RobertPHeller/RPi-RRCircuits/DCCShield/README.md

# DCCShield

Simple DCC driver shield for Arduino.
