RobertPHeller/RPi-RRCircuits/DCCTiva/README.md

# DCCTiva

Simple DCC Driver board for Tiva.
