RobertPHeller/RPi-RRCircuits/CommonOpenMRNExtras/README.md

# CommonOpenMRNExtras

This is a skeleton Directory for OpenMRN projects for the Raspberry Pi and/or
Beagle Boards.
