RobertPHeller/RPi-RRCircuits/MCP23017Hat/README.md

# MCP23017Hat

This is a 16 pin I2C port expander using a MCP230017.
