RobertPHeller/RPi-RRCircuits/CANHat2/CANHat2.png

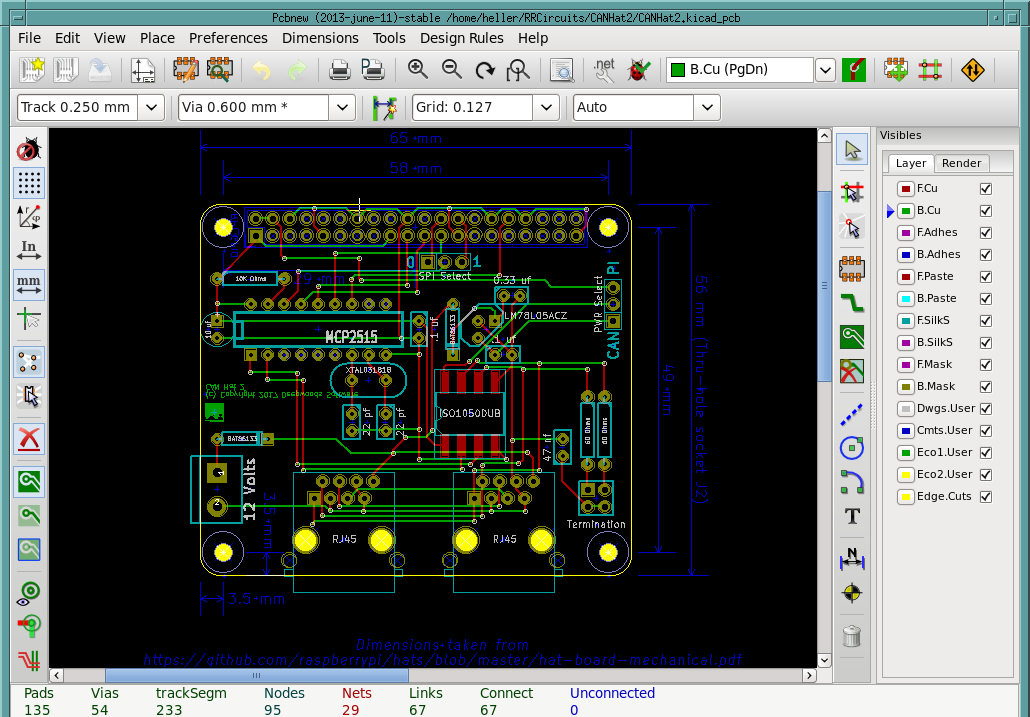
CANHat2/CANHat2.png
