RobertPHeller/RPi-RRCircuits/FRED/FRED_Board3D_Bottom.png

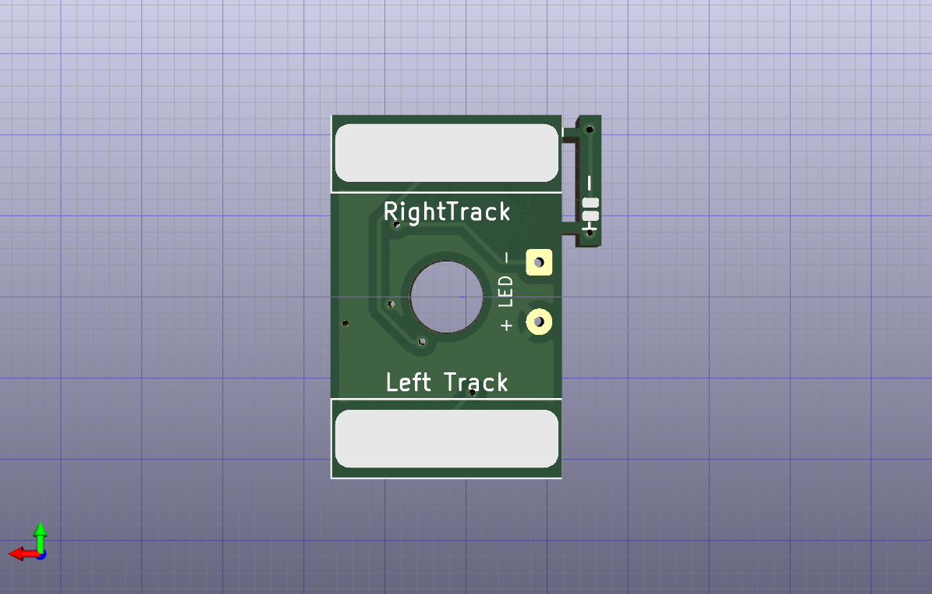
FRED/FRED_Board3D_Bottom.png
