RobertPHeller/RPi-RRCircuits/FRED/FRED_Board3D_Top.png

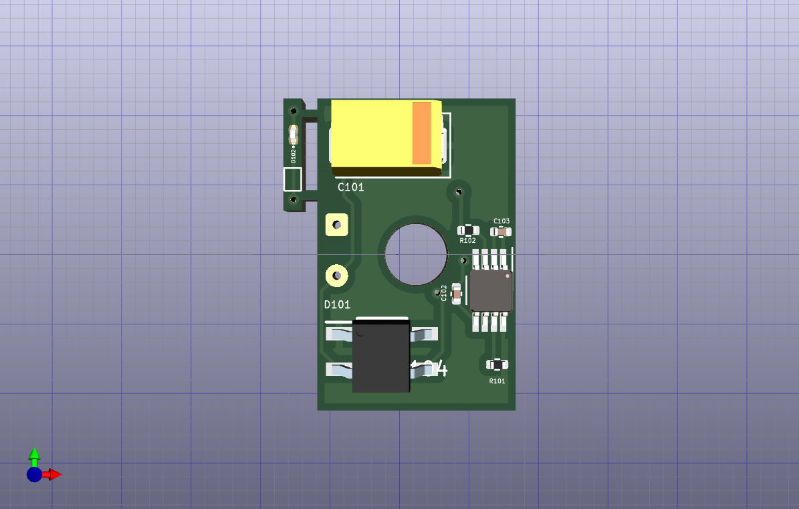
FRED/FRED_Board3D_Top.png
