RobertPHeller/RPi-RRCircuits/PocketBeagleMultifuntion/Header-P1-sch.png

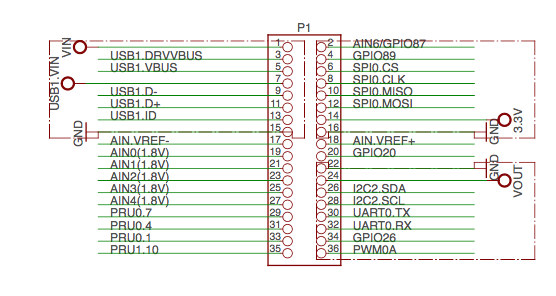
PocketBeagleMultifuntion/Header-P1-sch.png
