RobertPHeller/RPi-RRCircuits/PocketBeagleMultifuntion/Header-P2-sch.png

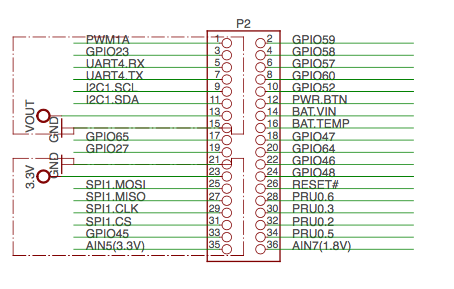
PocketBeagleMultifuntion/Header-P2-sch.png
