RobertPHeller/RPi-RRCircuits/STM32F767ZI_LCC_PNET_Router/firmware/doc/images/STM32F767ZI_LCC_PNET_Router.png

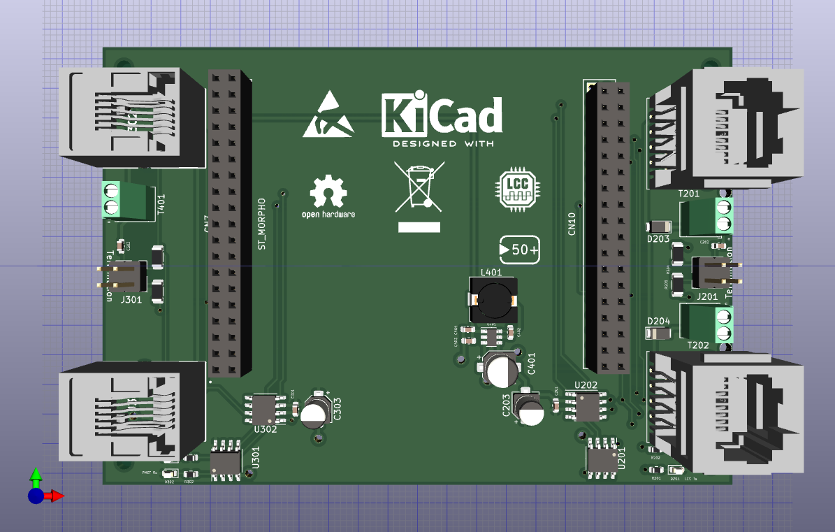
STM32F767ZI_LCC_PNET_Router/firmware/doc/images/STM32F767ZI_LCC_PNET_Router.png
