RobertPHeller/RPi-RRCircuits/STM32F767ZI_LCC_PNET_Router/firmware/doc/images/TerminationJumpers.png

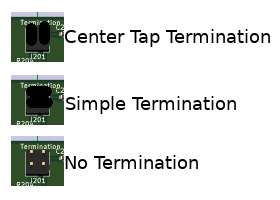
STM32F767ZI_LCC_PNET_Router/firmware/doc/images/TerminationJumpers.png
