RobertPHeller/RPi-RRCircuits/STM32F767ZI_LCC_Repeater/firmware/doc/images/STM32F767ZI_LCC_Repeater.png

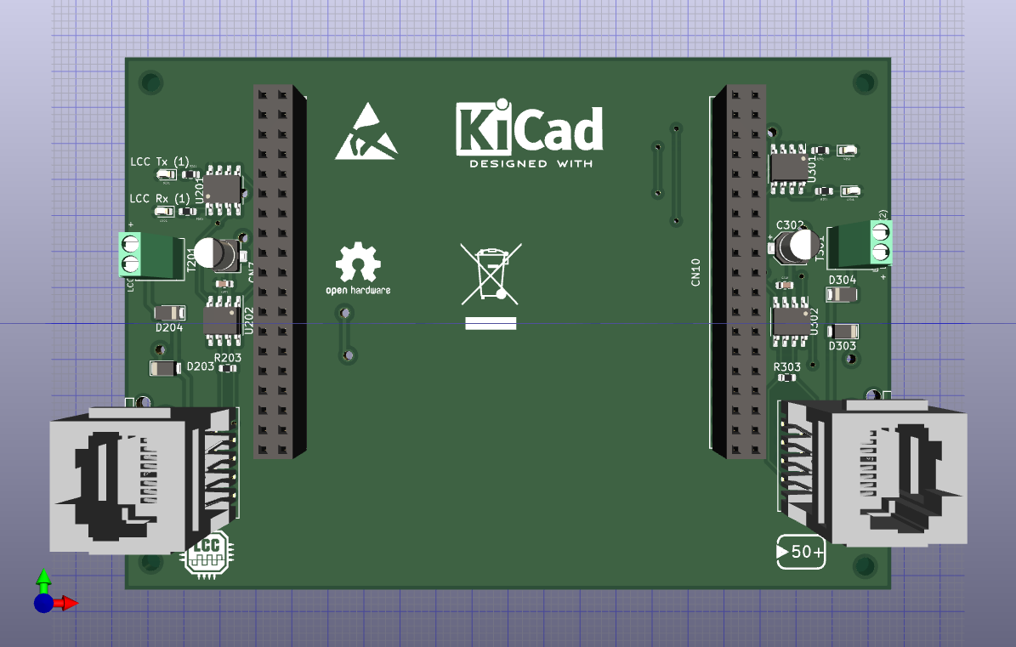
STM32F767ZI_LCC_Repeater/firmware/doc/images/STM32F767ZI_LCC_Repeater.png
