RobertPHeller/RPi-RRCircuits/TivaMultiFunctionBoard/TivaMultiFunctionBoard-top3D.jpg

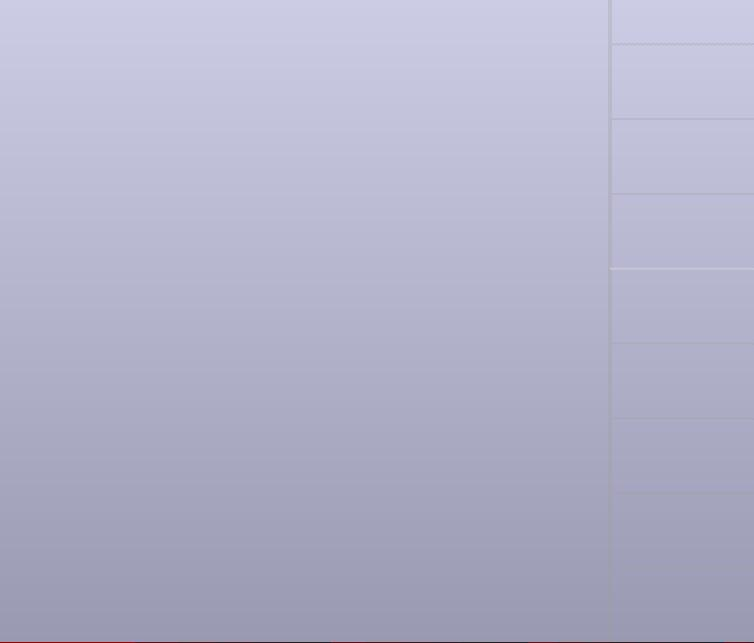
TivaMultiFunctionBoard/TivaMultiFunctionBoard-top3D.jpg
