RobertPHeller/RPi-RRCircuits/MCP23017Hat/MCP23017_mouser.csv

Value | Quantity | References | Mouser Part Number | Adafruit Part Number
.1 uf | 1 | C1 | 21RZ310-RC
RPi_GPIO | 1 | J0 | 855-M20-6102045 | 2223
Address Jumper | 1 | J1 | 517-929836-02-03
10K Ohms | 1 | RR1 | 652-4605X-1LF-10K
GP0;GP1 | 2 | T1 T2 | 651-1725737 | 2x 651-1725685
MCP23017 | 1 | U1 | 579-MCP23017-E/SP
