RobertPHeller/RPi-RRCircuits/QuadSSSQuadIn/QuadSSSQuadIn_mouser.csv

Value | Quantity | References | Mouser Part Number | Adafruit Part Number
.1 uf | 3 | C1 C2 C3 | 21RZ310-RC
ASSR-4128 | 2 | IC1 IC2 | 630-ASSR-4128-002E
RPi_GPIO | 1 | J0 | 855-M20-6102045 | 2223
CONN_3X2 | 1 | J1 | 517-929836-02-03
330 Ohms | 1 | RP1 | 652-4608X-AP2-331LF
10K Ohms | 2 | RR1 RR2 | 652-4605X-1LF-10K
CONN_8 | 1 | T1 | 651-1725711
CONN_6 | 1 | T2 | 651-1725698
MCP23008 | 1 | U1 | 579-MCP23008-E/P
74LV125AN | 1 | U2 | 595-SN74LV125AN
