RobertPHeller/RPi-RRCircuits/STM32ShieldForMetroMiniSlaves/STM32ShieldForMetroMiniSlaves.pdf

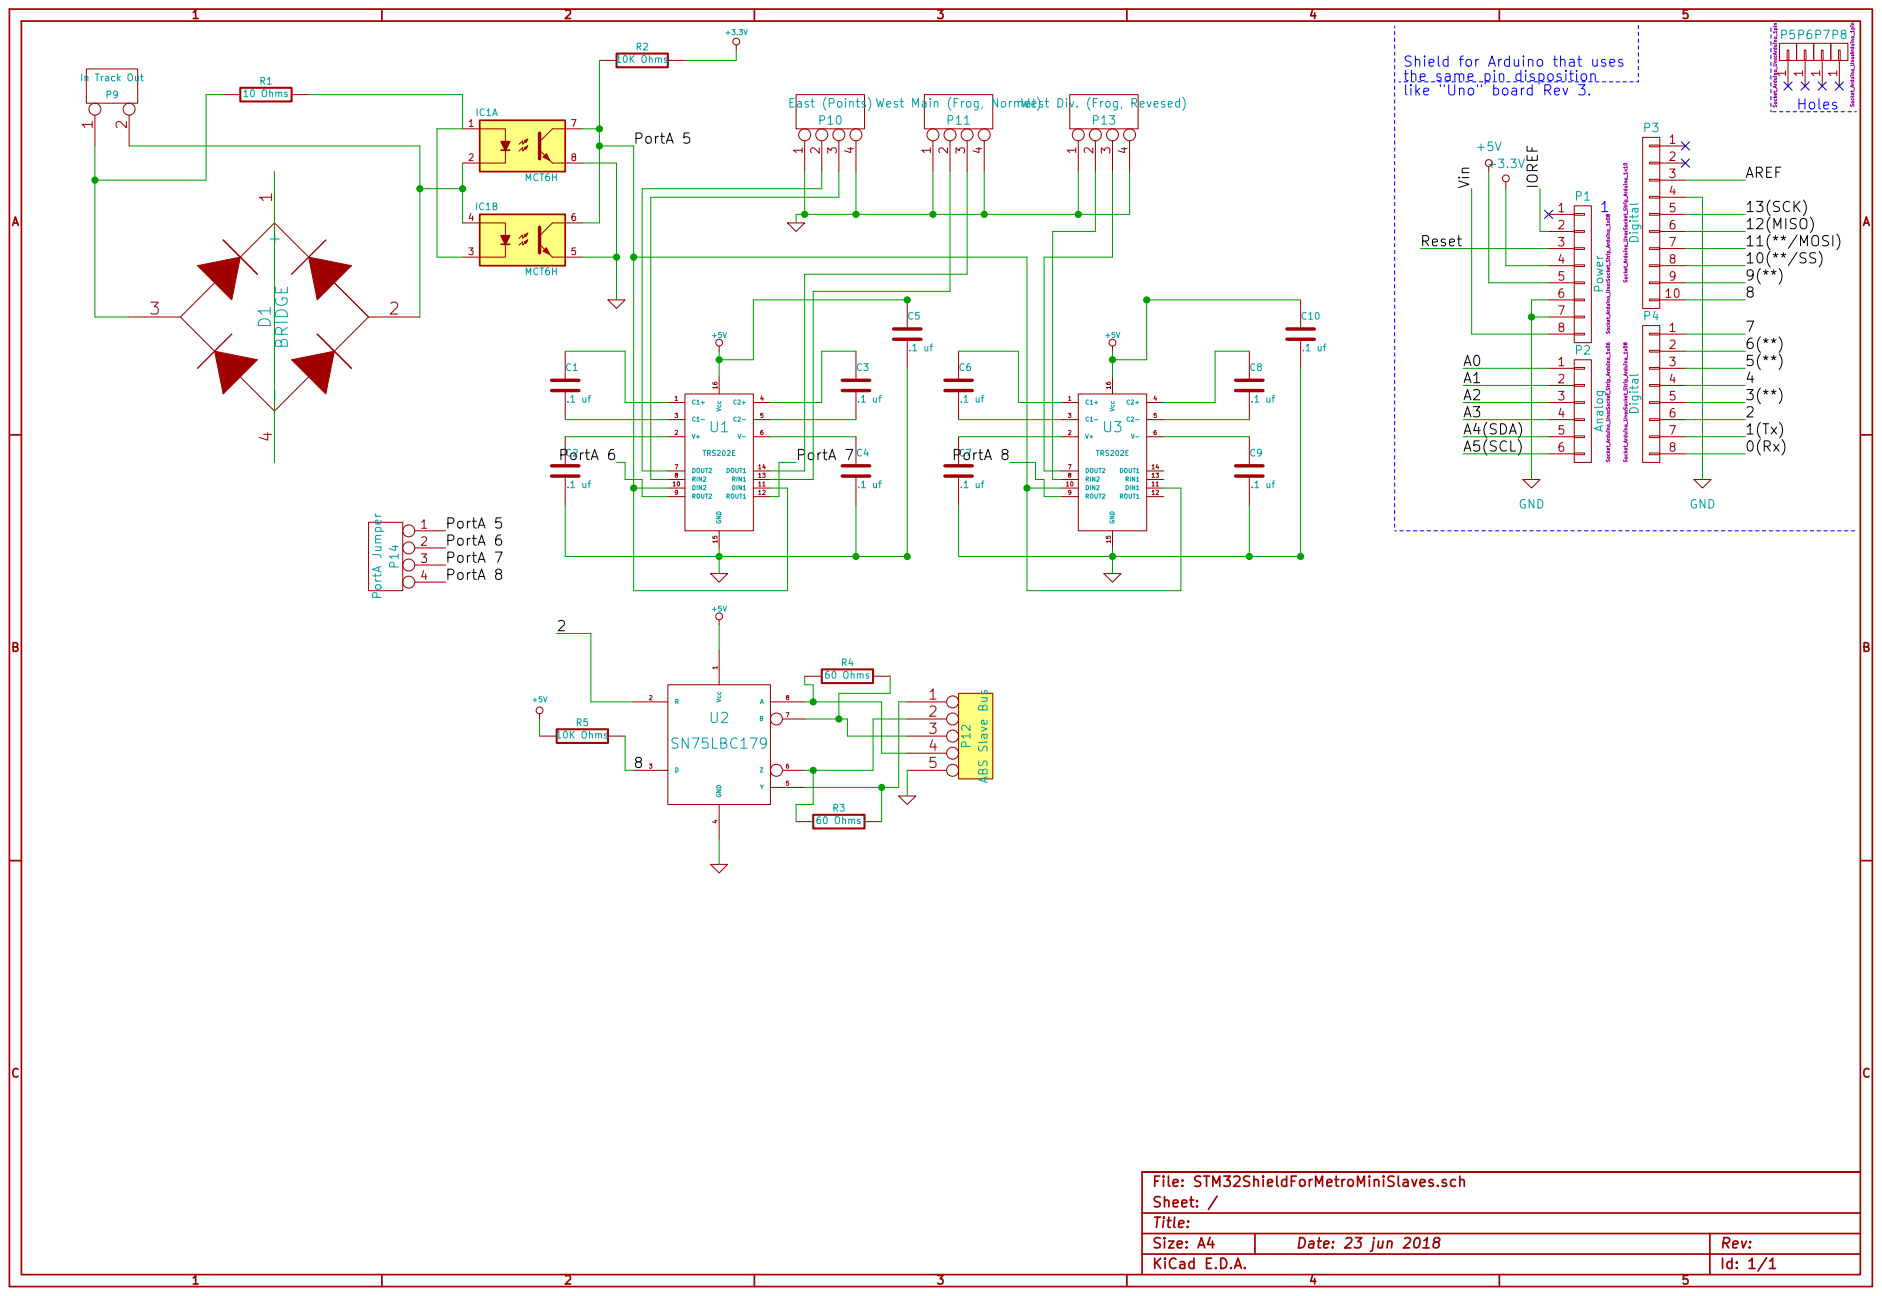
[picture p45: page 1]

4 P13 West Div. (Frog, Revesed) +3.3V 2

the same pin disposition
like "Uno" board Rev 3. 1

4 P11 West Main (Frog, Normal) 1

Id: 1/1 Title: File: STM32ShieldForMetroMiniSlaves.sch
