RobertPHeller/RPi-RRCircuits/WS2811_SignalHead/WS2811_SignalHead.pdf

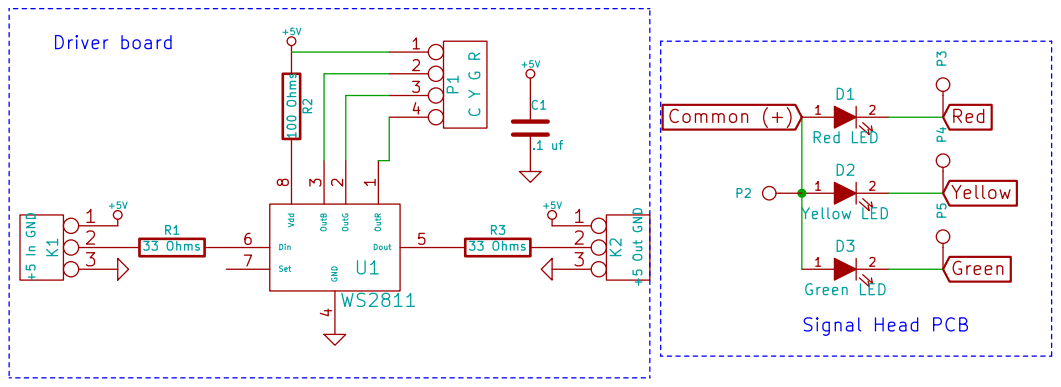
[picture p46: page 1]

Deepwoods Software OutR 1 OutG 2 OutB 3 GND 4

File: WS2811_SignalHead.sch
Sheet: /
Title: WS811 Signal Head Driver
