RobertPHeller/RPi-RRCircuits/TivaInterchangeSMD/TivaInterchangeSMD.pdf

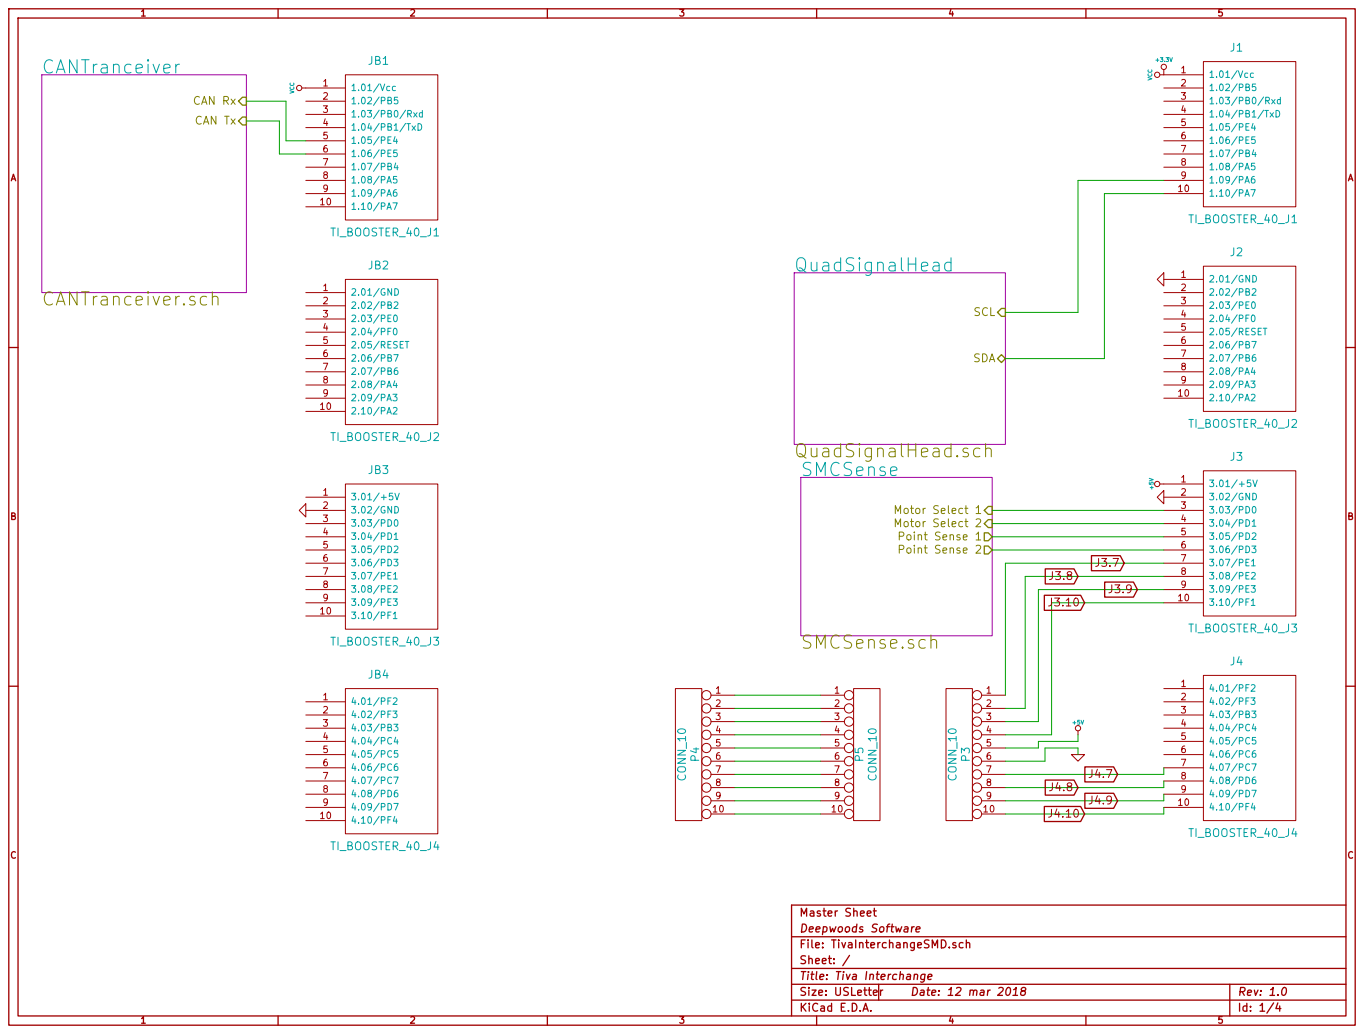
[picture p47: page 1]

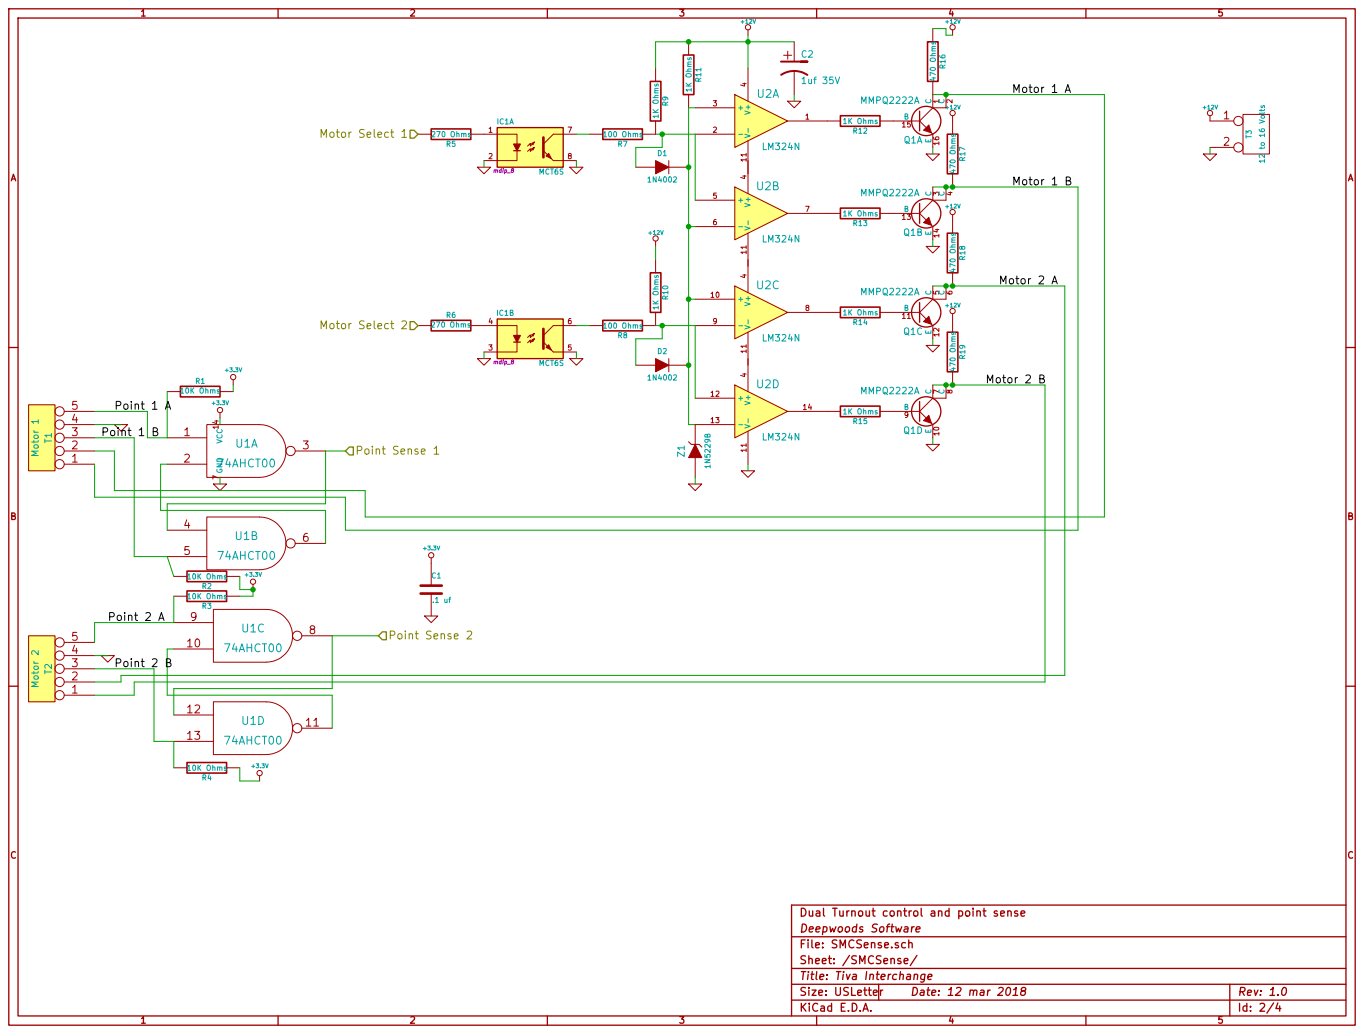
[picture p48: page 2]

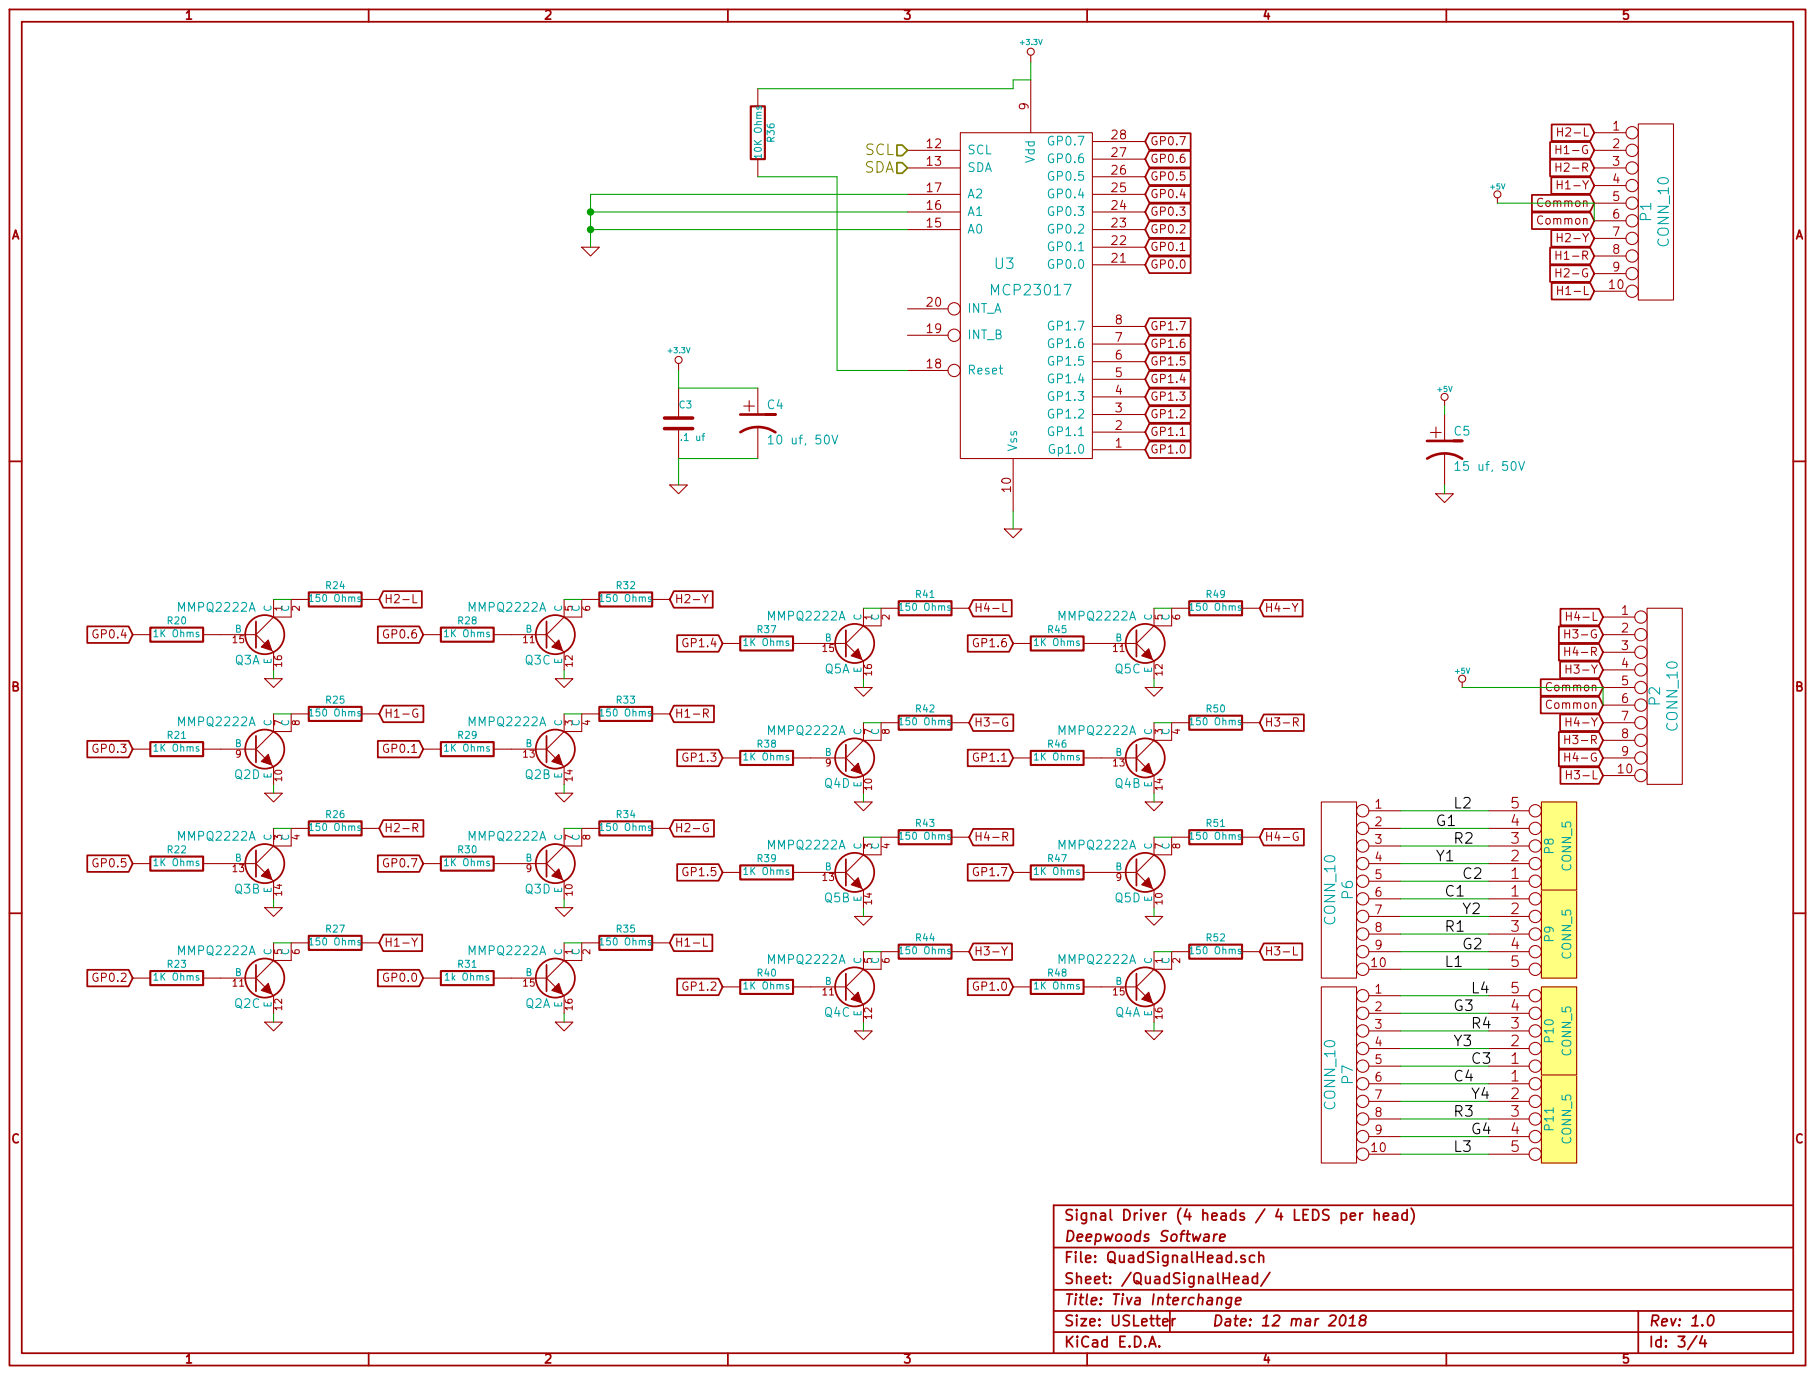
[picture p49: page 3]

Signal Driver (4 heads / 4 LEDS per head)
Deepwoods Software
File: QuadSignalHead.sch
Sheet: /QuadSignalHead/
Title: Tiva Interchange

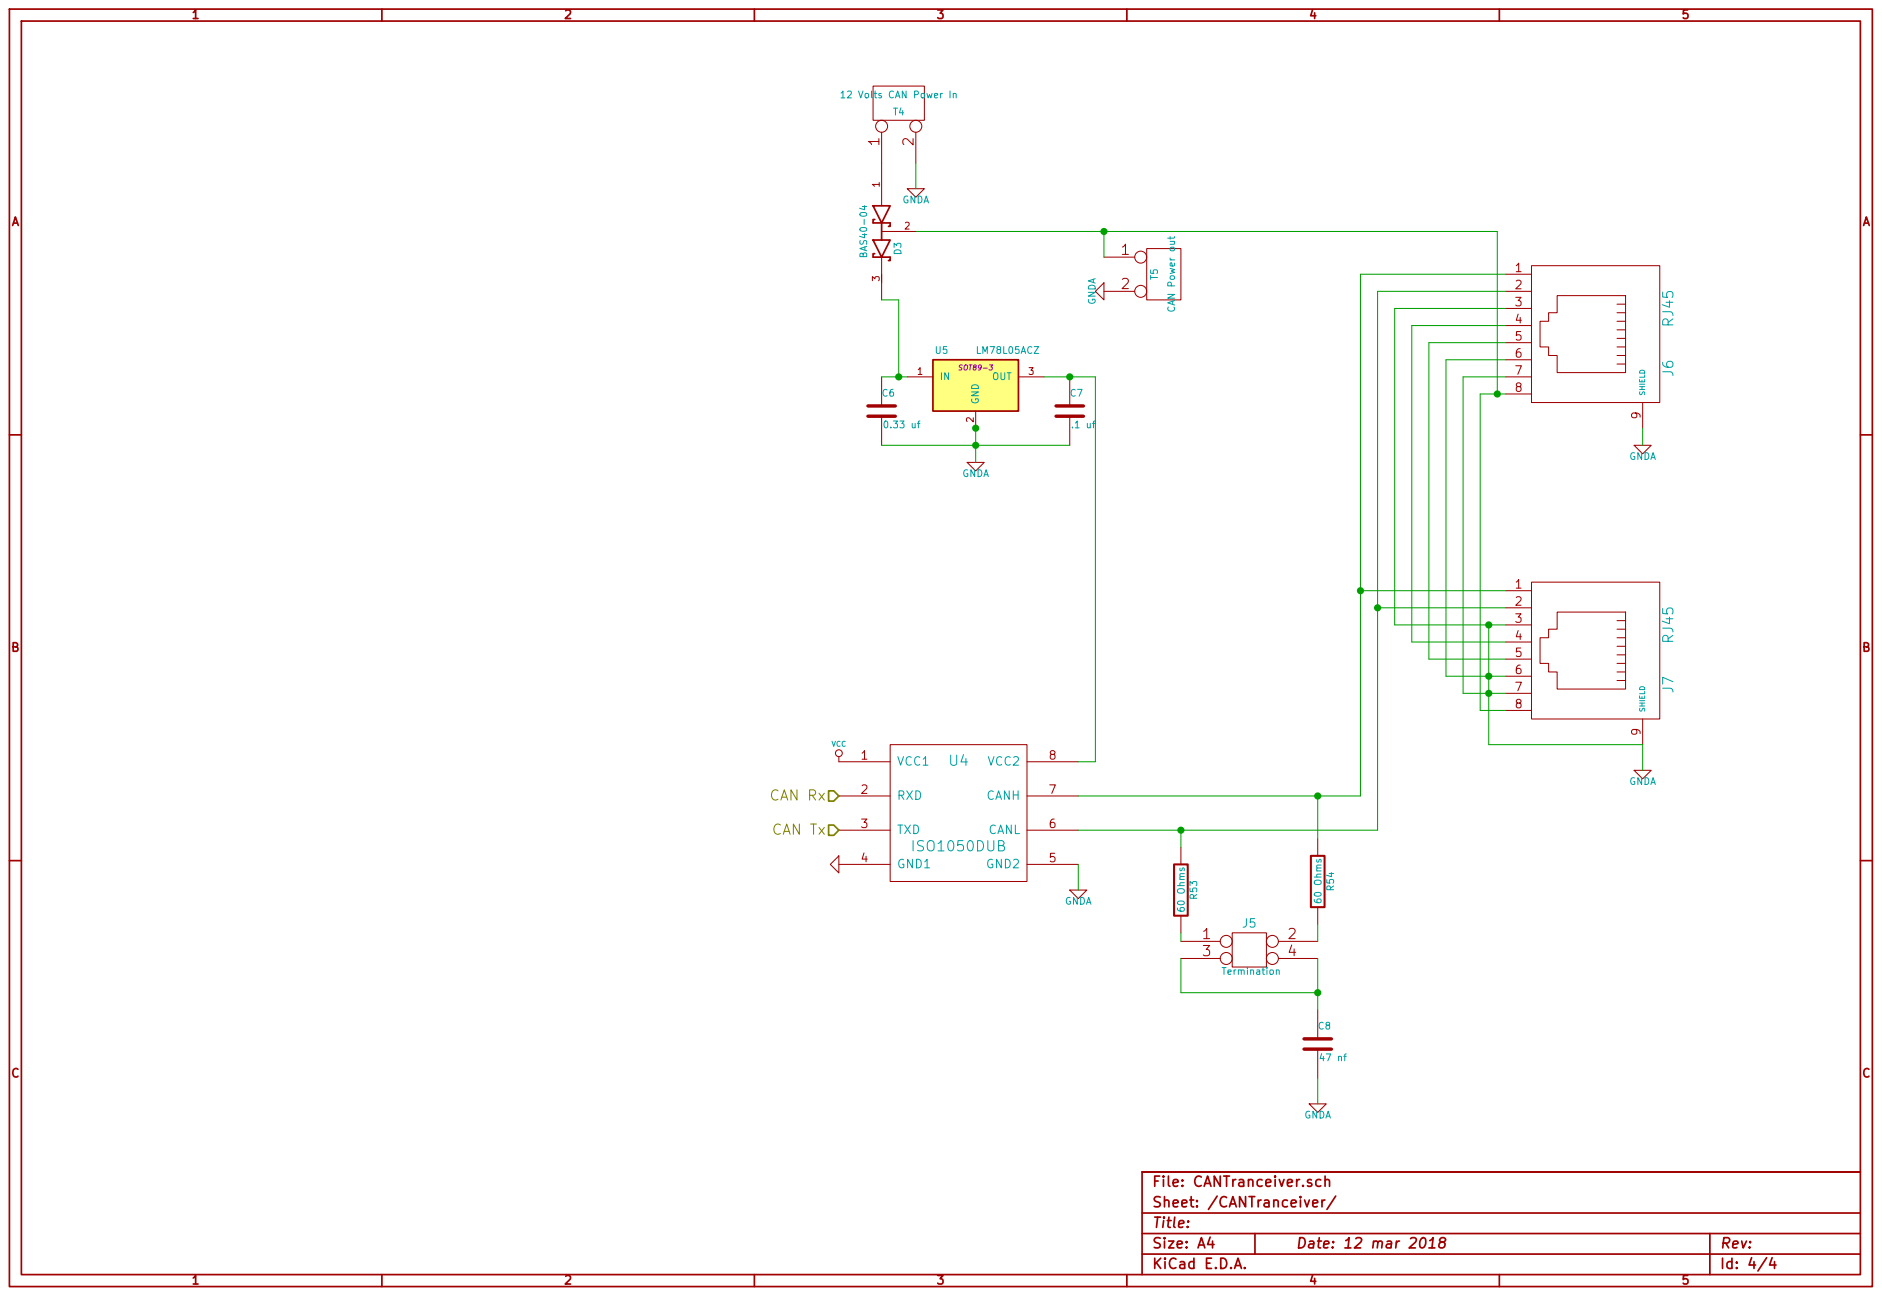
[picture p50: page 4]

47 nf GNDA CAN Rx

Id: 4/4 Title: File: CANTranceiver.sch
Sheet: /CANTranceiver/
