RobertPHeller/RPi-RRCircuits/TivaInterchange/TivaInterchange.pdf

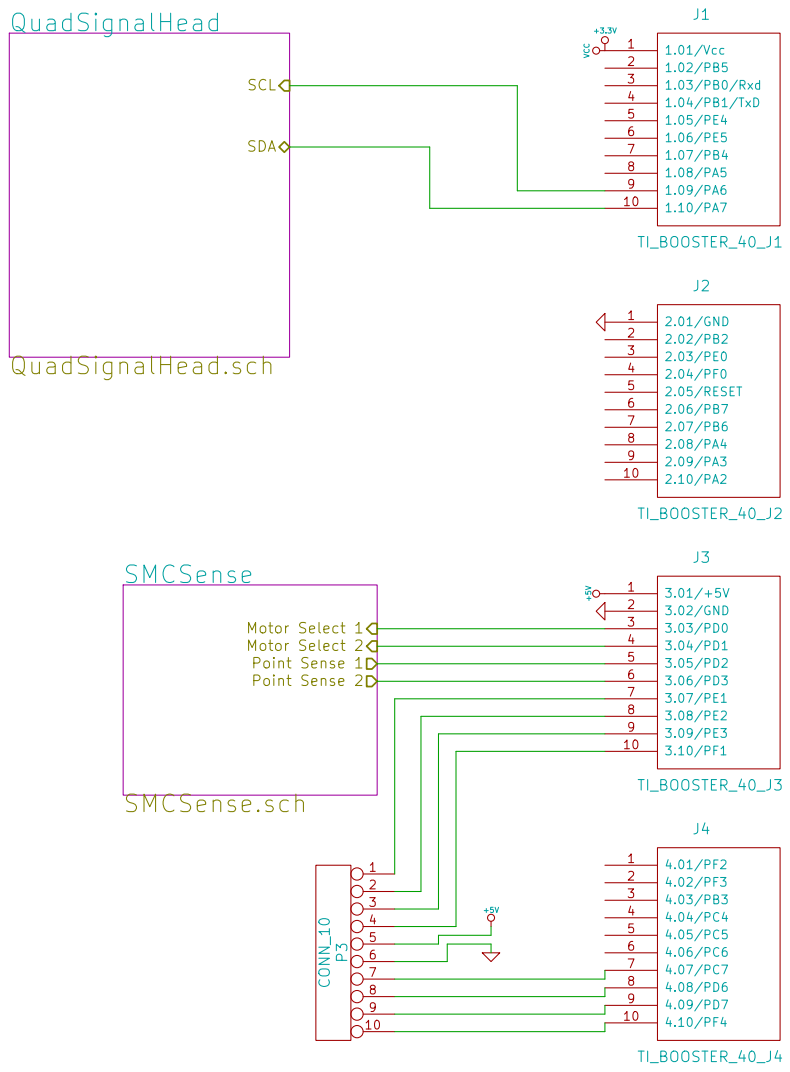
[picture p51: page 1]

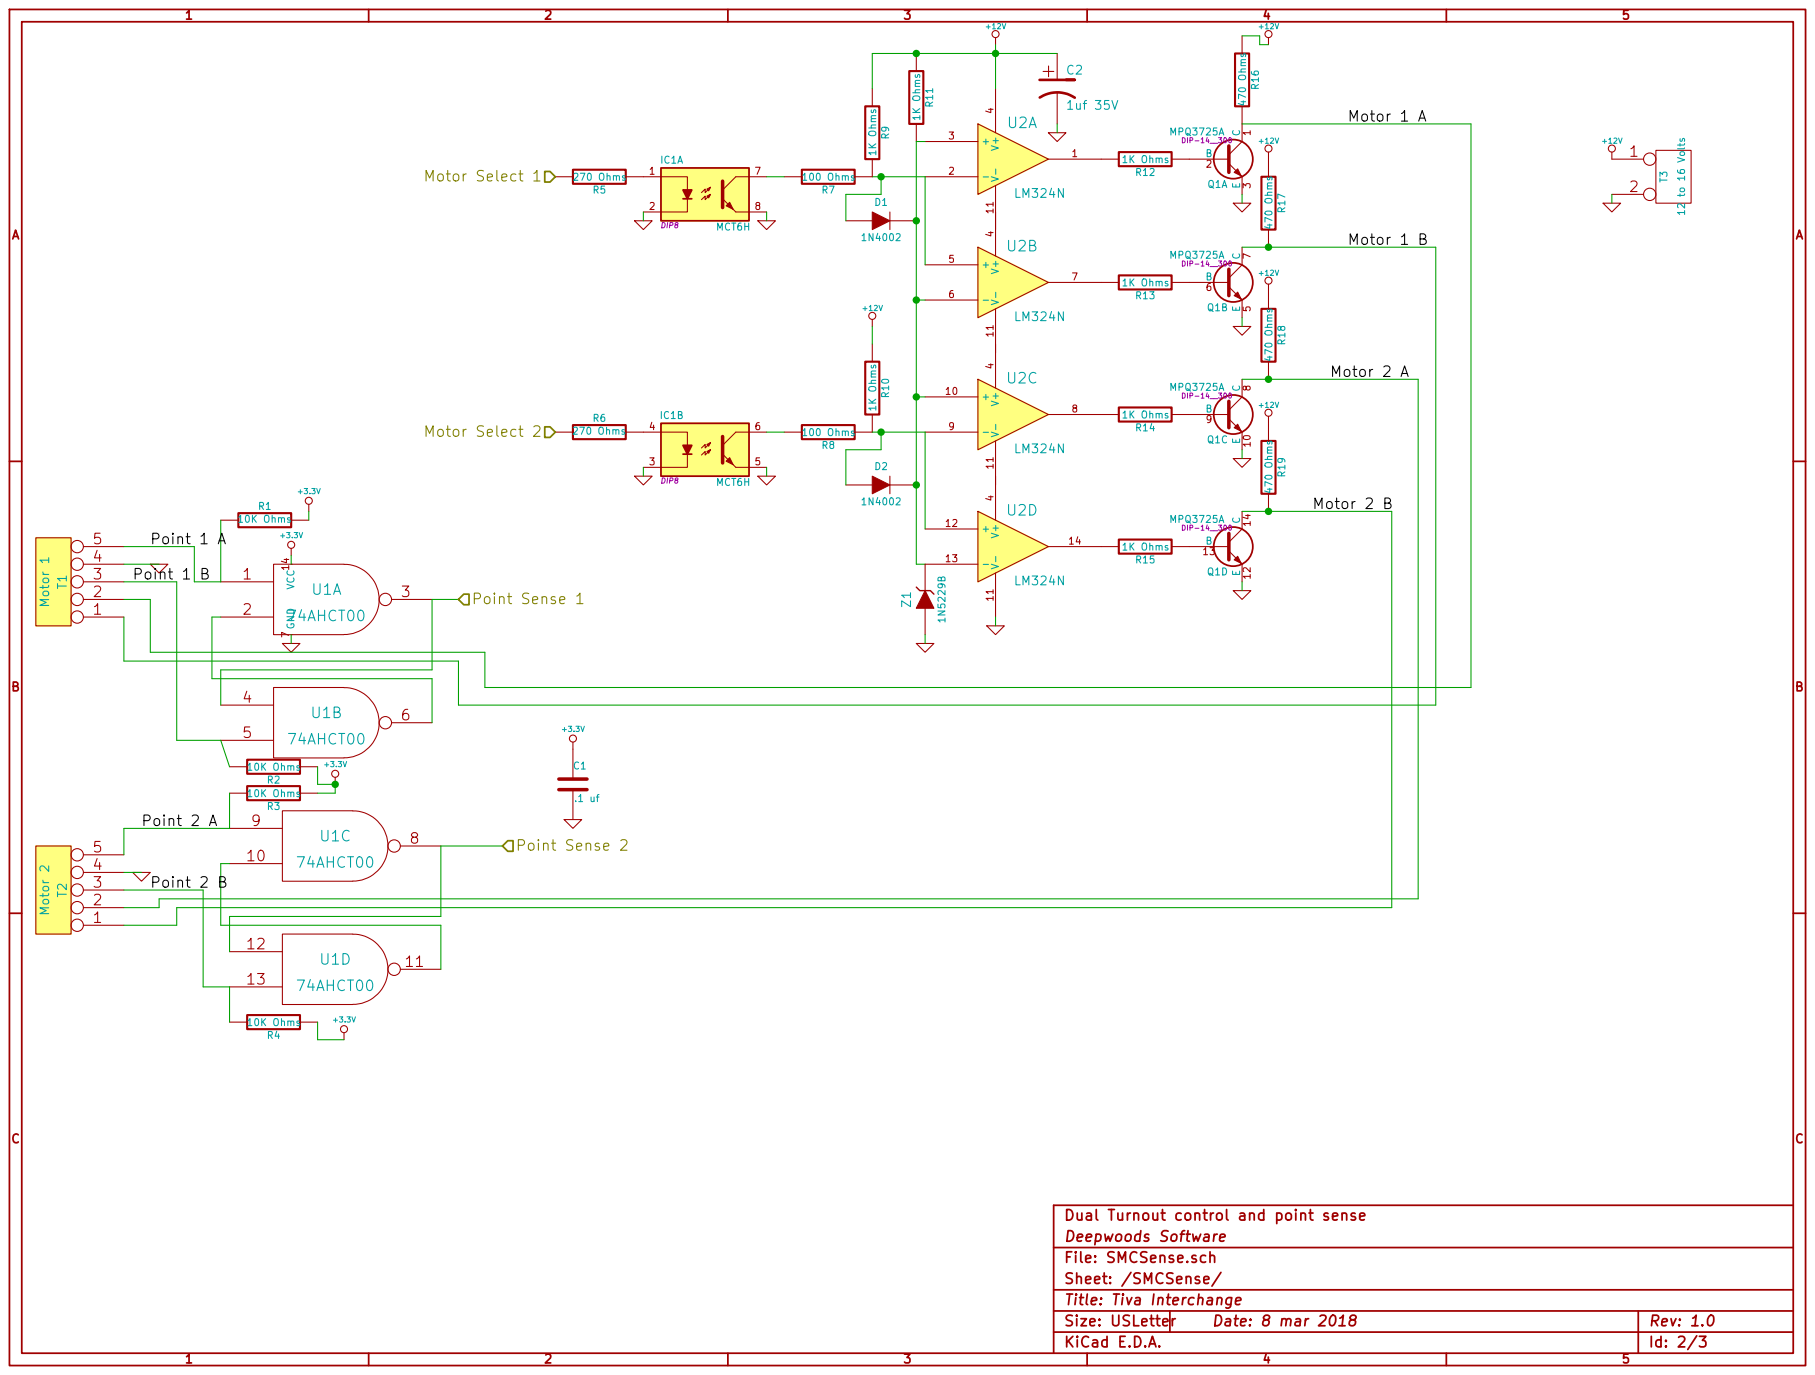
[picture p52: page 2]

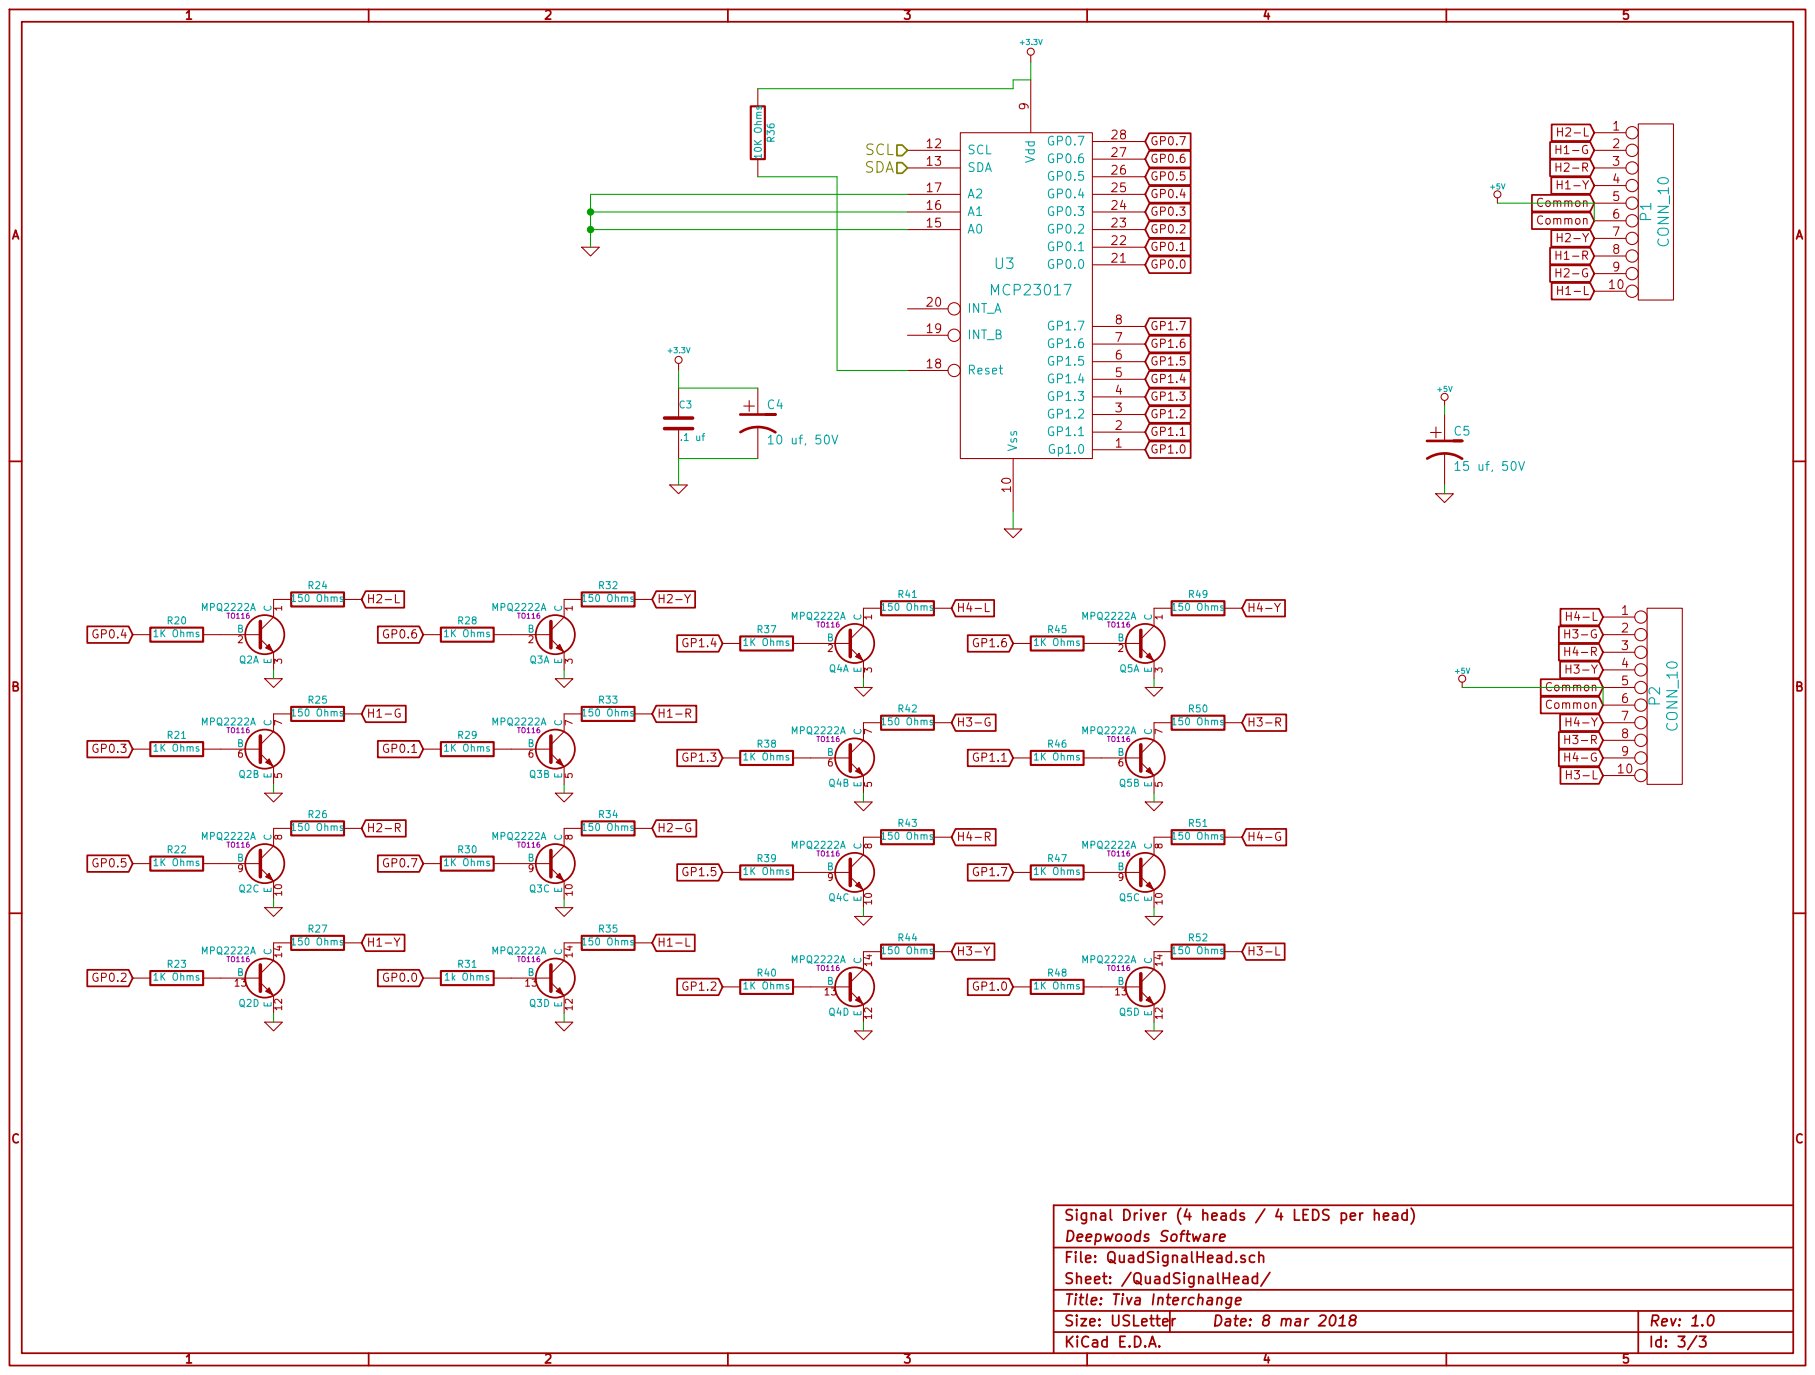
[picture p53: page 3]

Signal Driver (4 heads / 4 LEDS per head)
Deepwoods Software
File: QuadSignalHead.sch
Sheet: /QuadSignalHead/
Title: Tiva Interchange
