RobertPHeller/RPi-RRCircuits/LEDDriverHat/LEDDriverHat.pdf

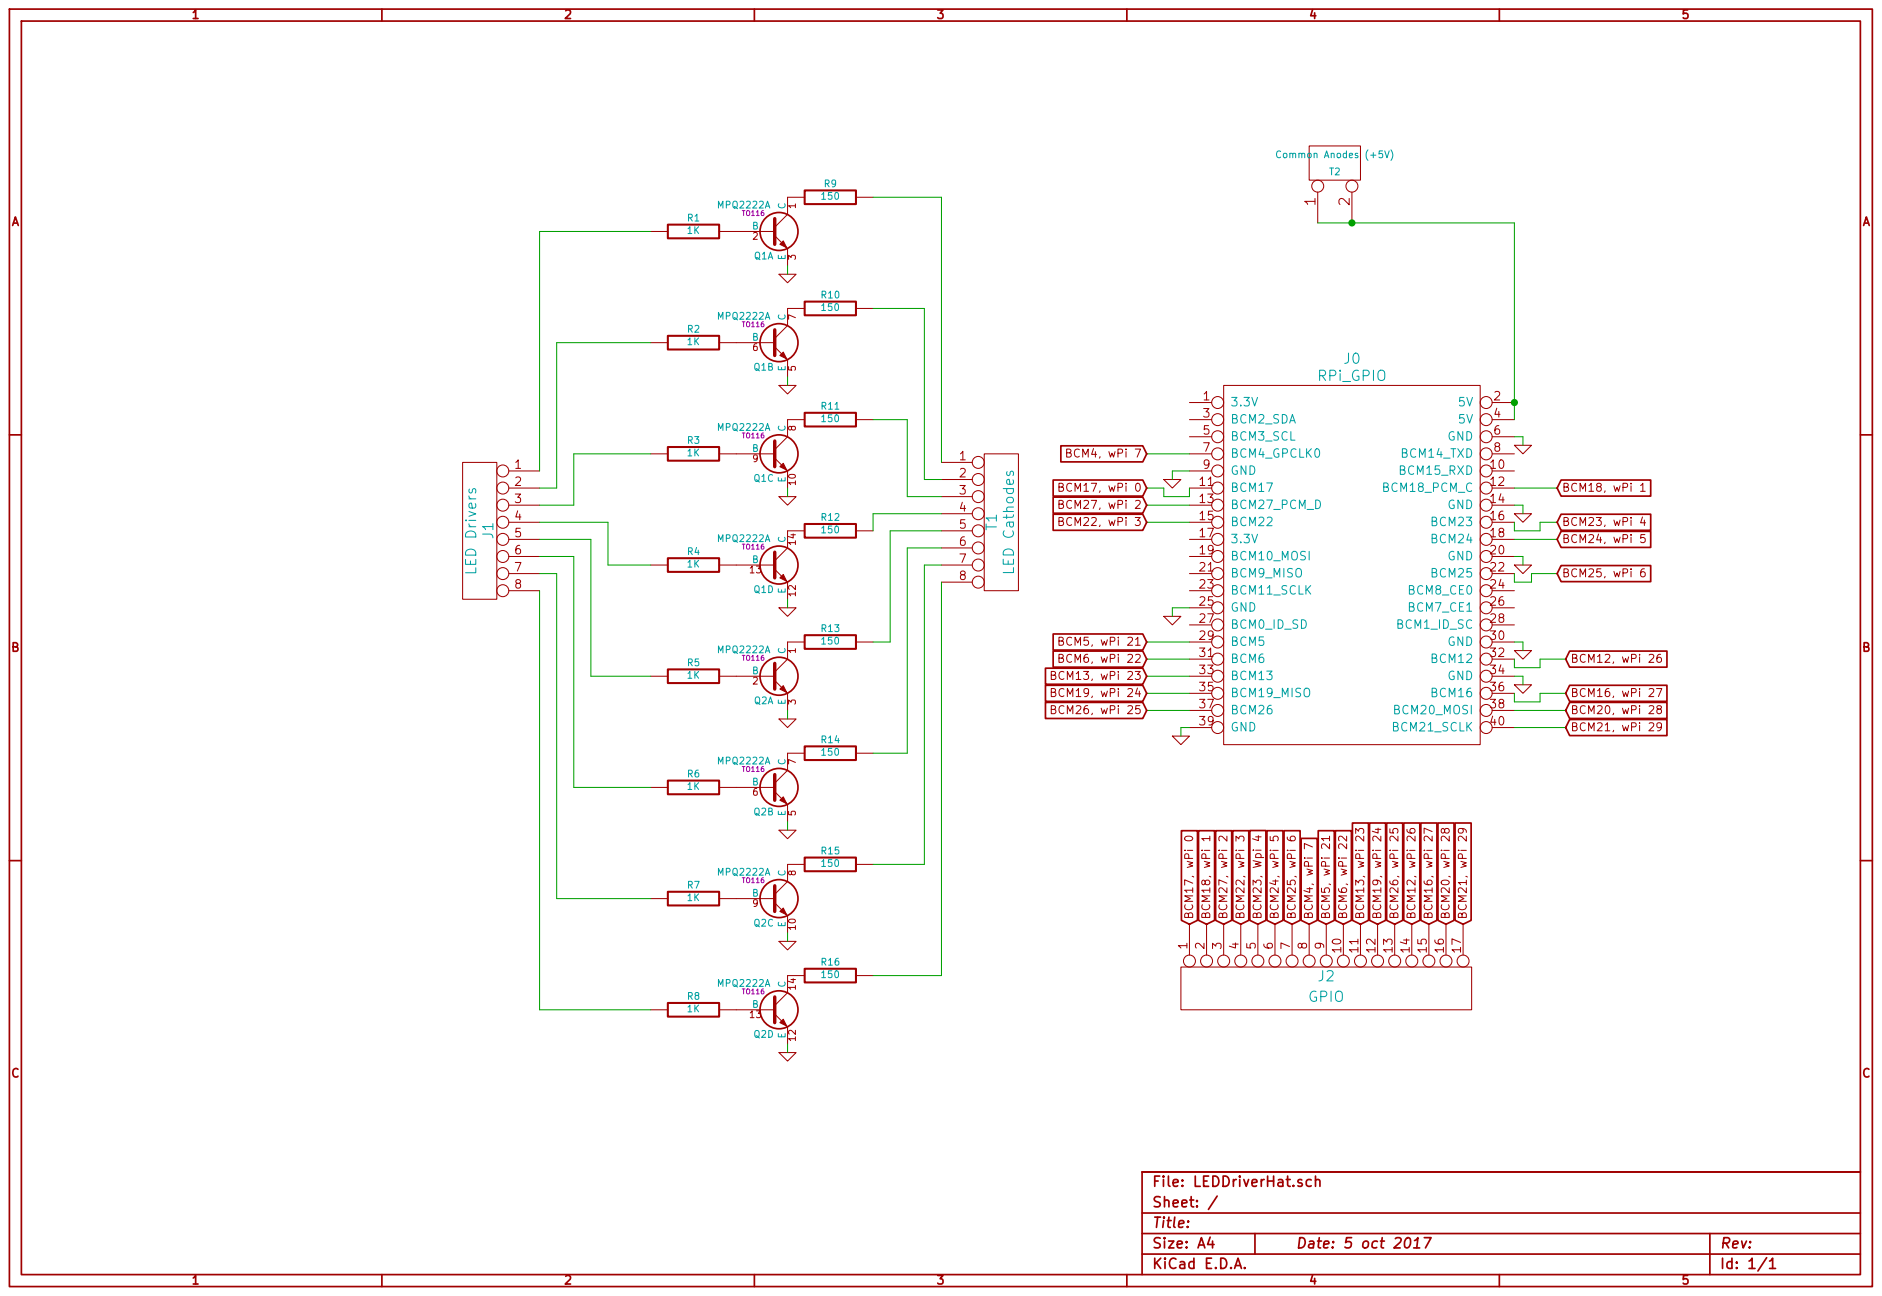
[picture p54: page 1]

Id: 1/1 Title: File: LEDDriverHat.sch Sheet: /
