RobertPHeller/RPi-RRCircuits/16LEDDriver23017SMD/16LEDDriver23017SMD.pdf

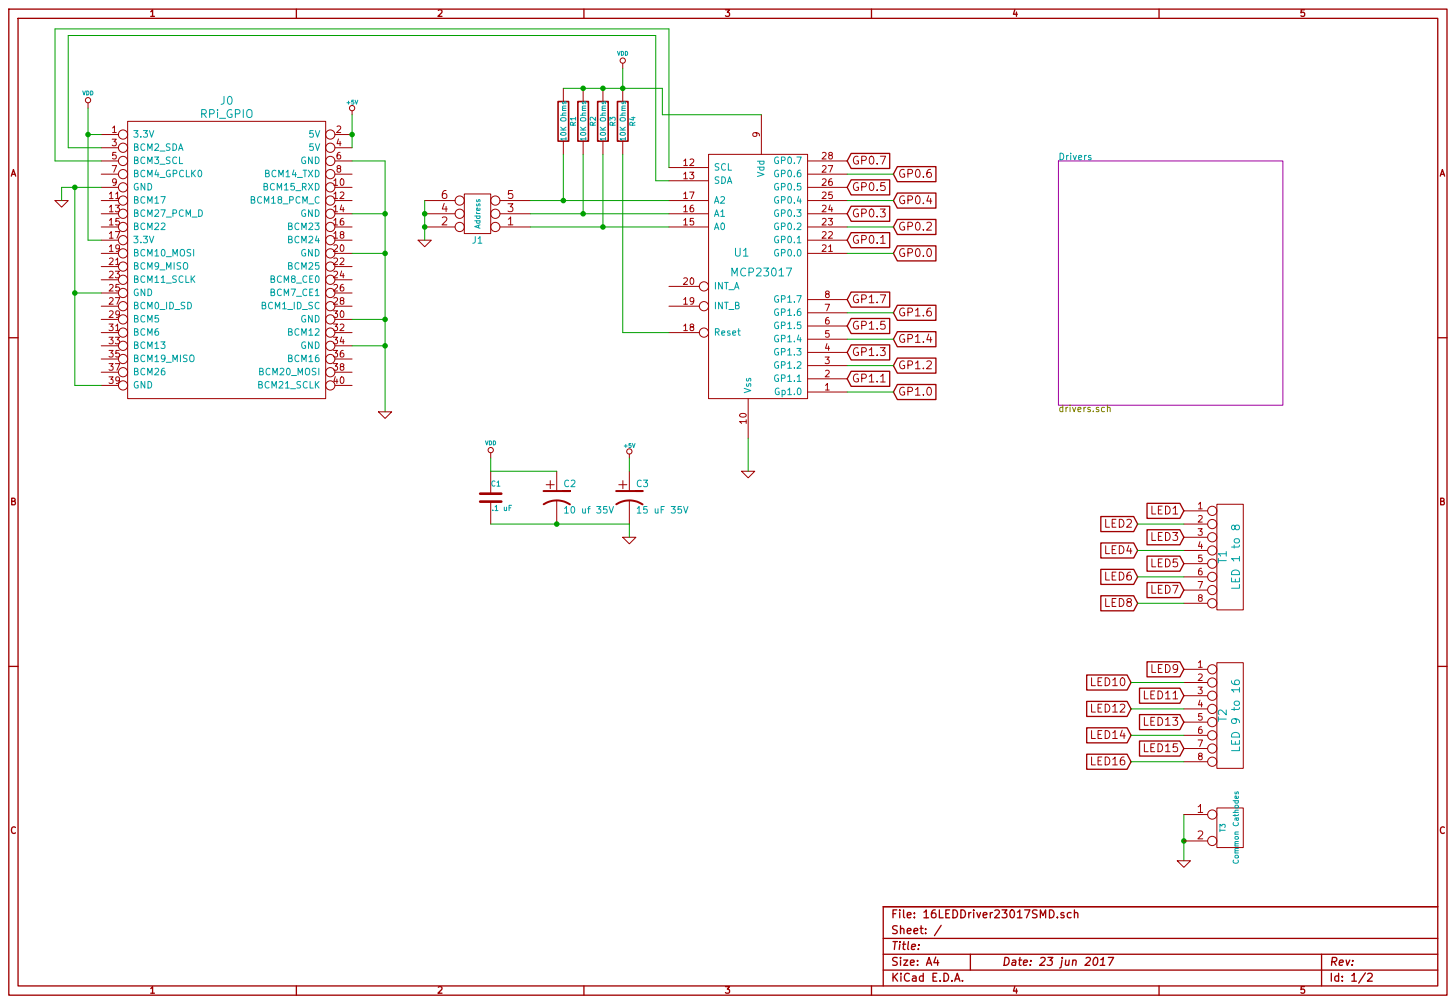
[picture p55: page 1]

Id: 1/2 Title: File: 16LEDDriver23017SMD.sch
Sheet: /

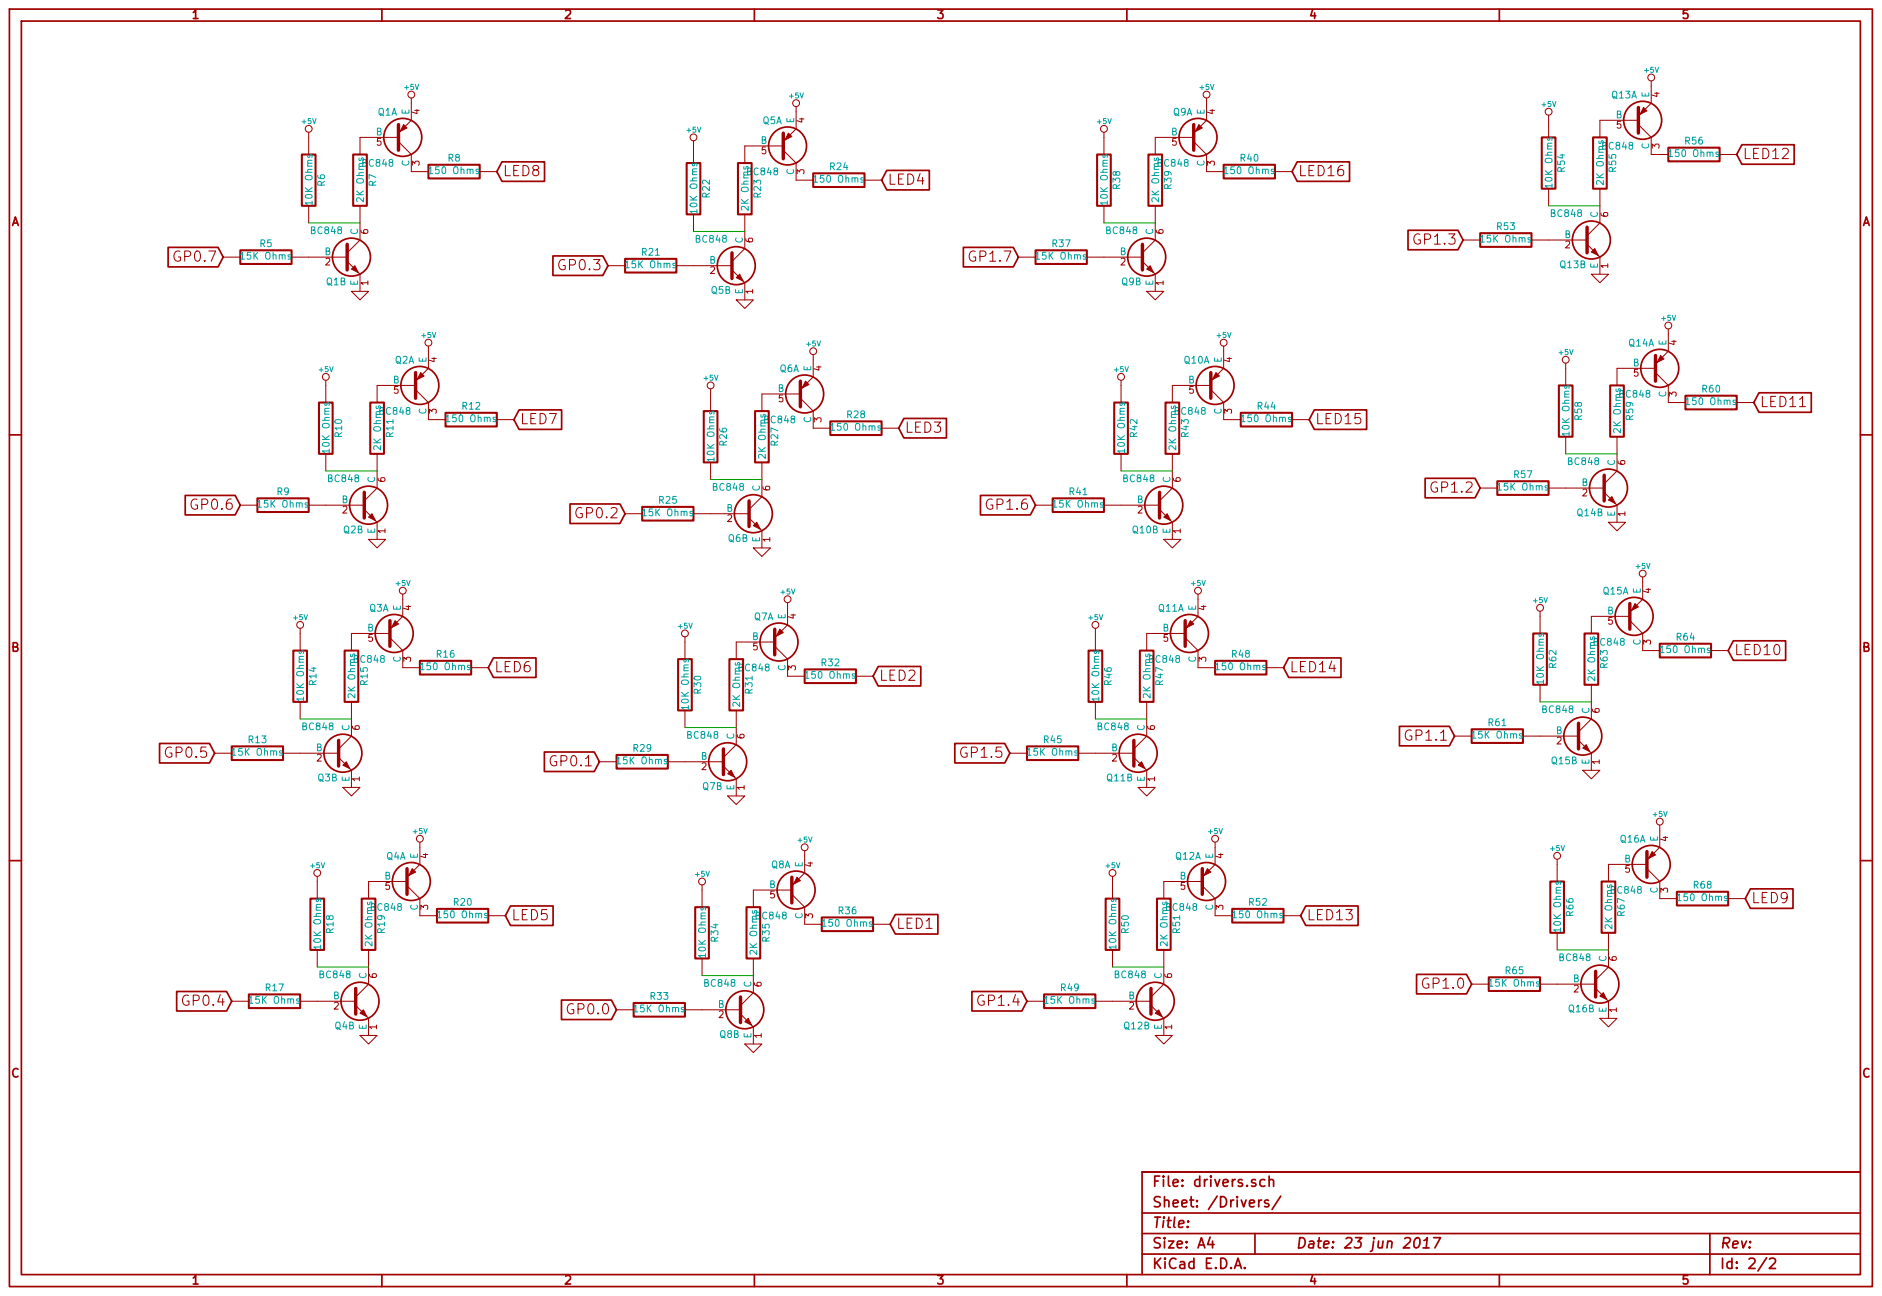
[picture p56: page 2]

Id: 2/2 Title: File: drivers.sch Sheet: /Drivers/
