RobertPHeller/RPi-RRCircuits/QuadSMCSenseHat/QuadSMCSenseHat.pdf

11

22

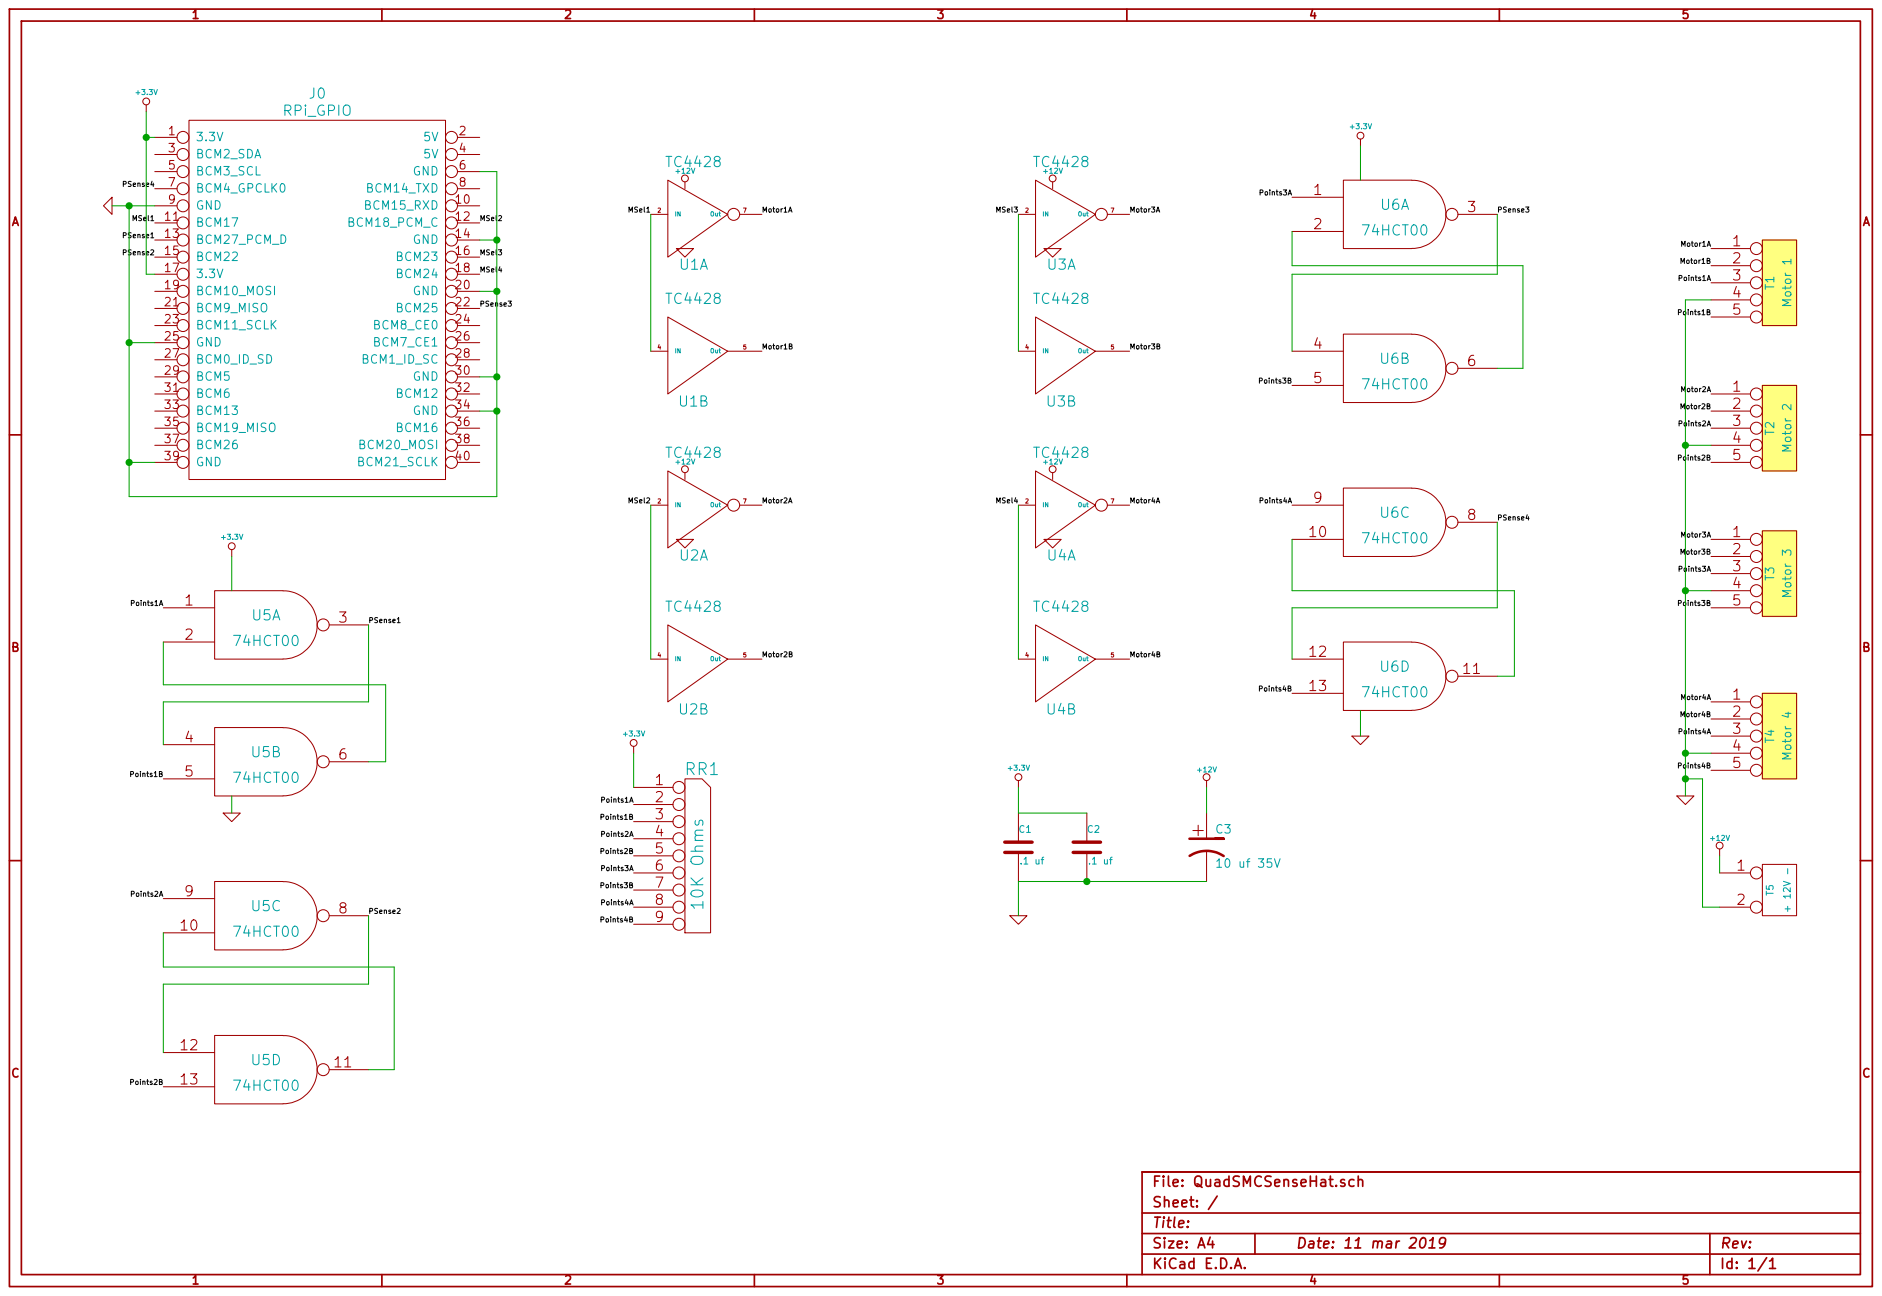
[picture p66: page 1]
