RobertPHeller/RPi-RRCircuits/RPiHalfSiding/RPiHalfSiding.pdf

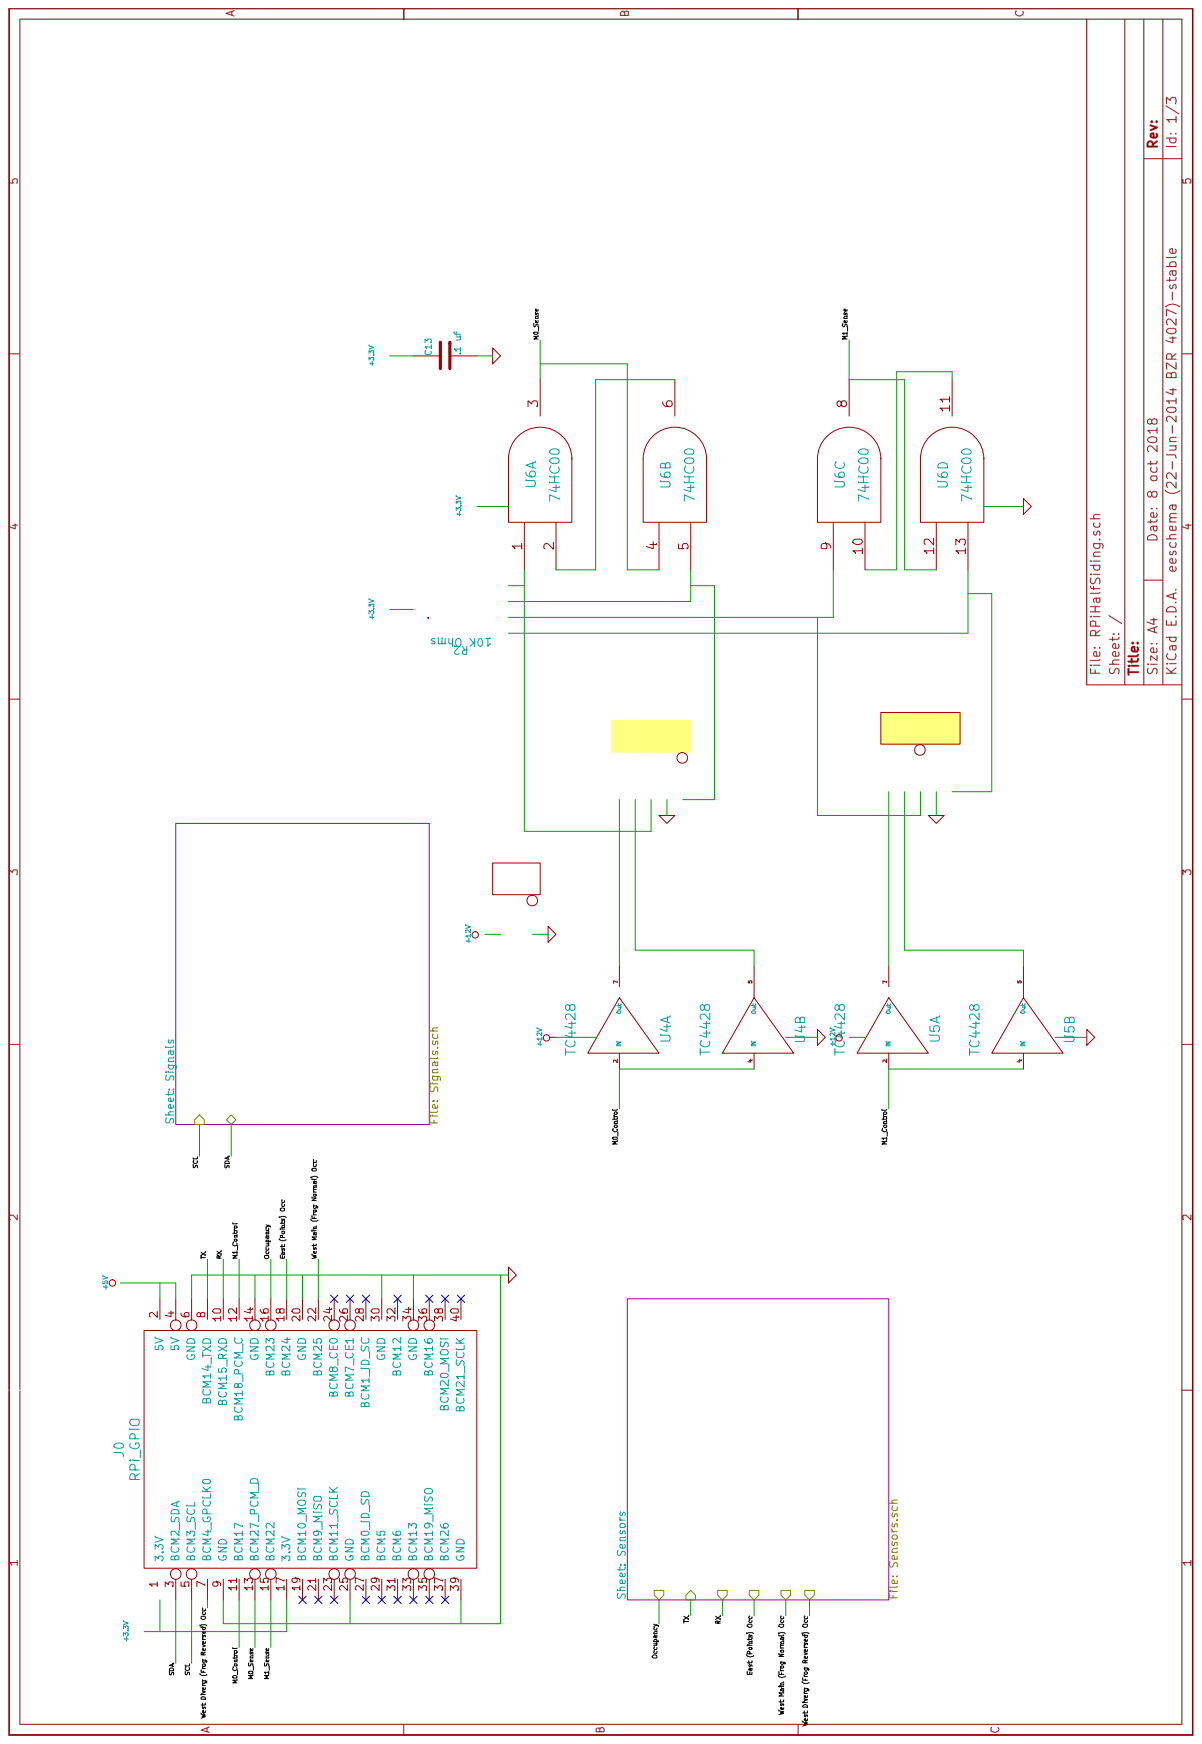
[picture p67: page 1]

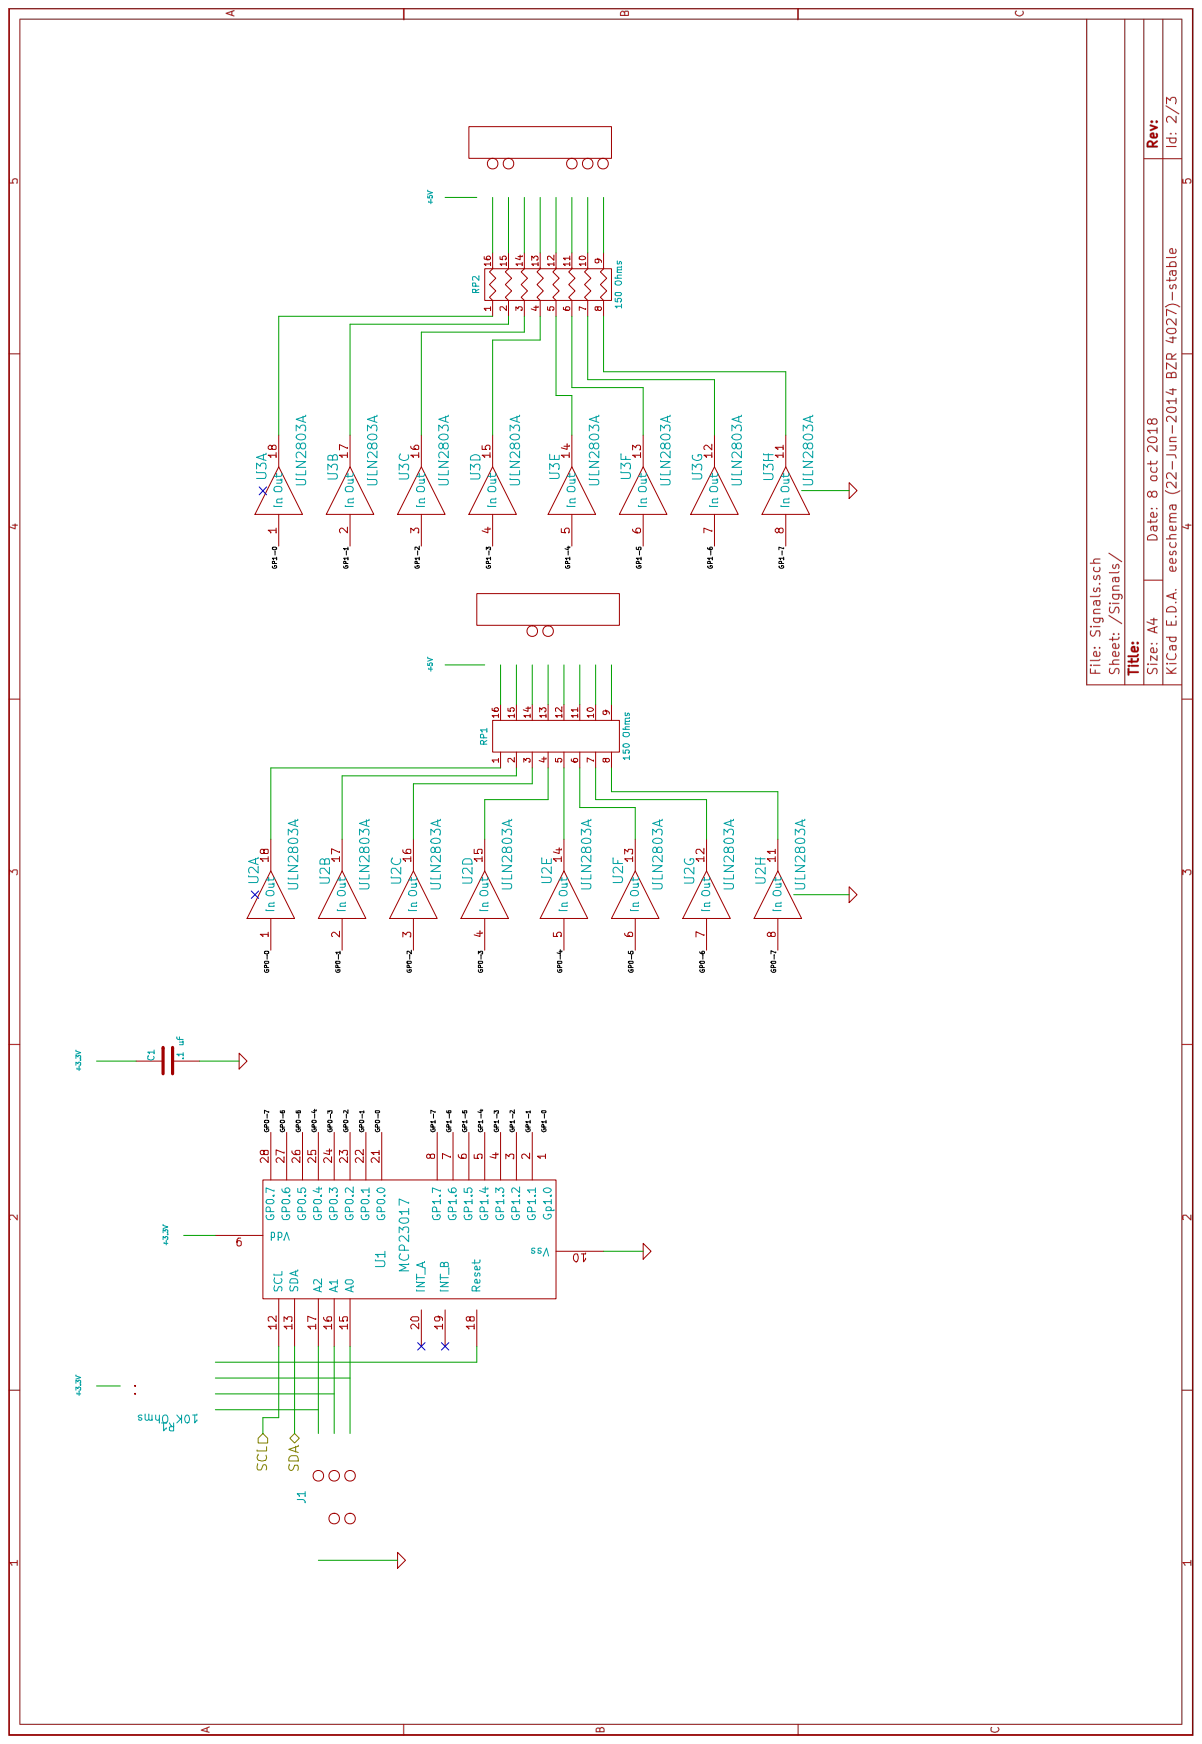
[picture p68: page 2]

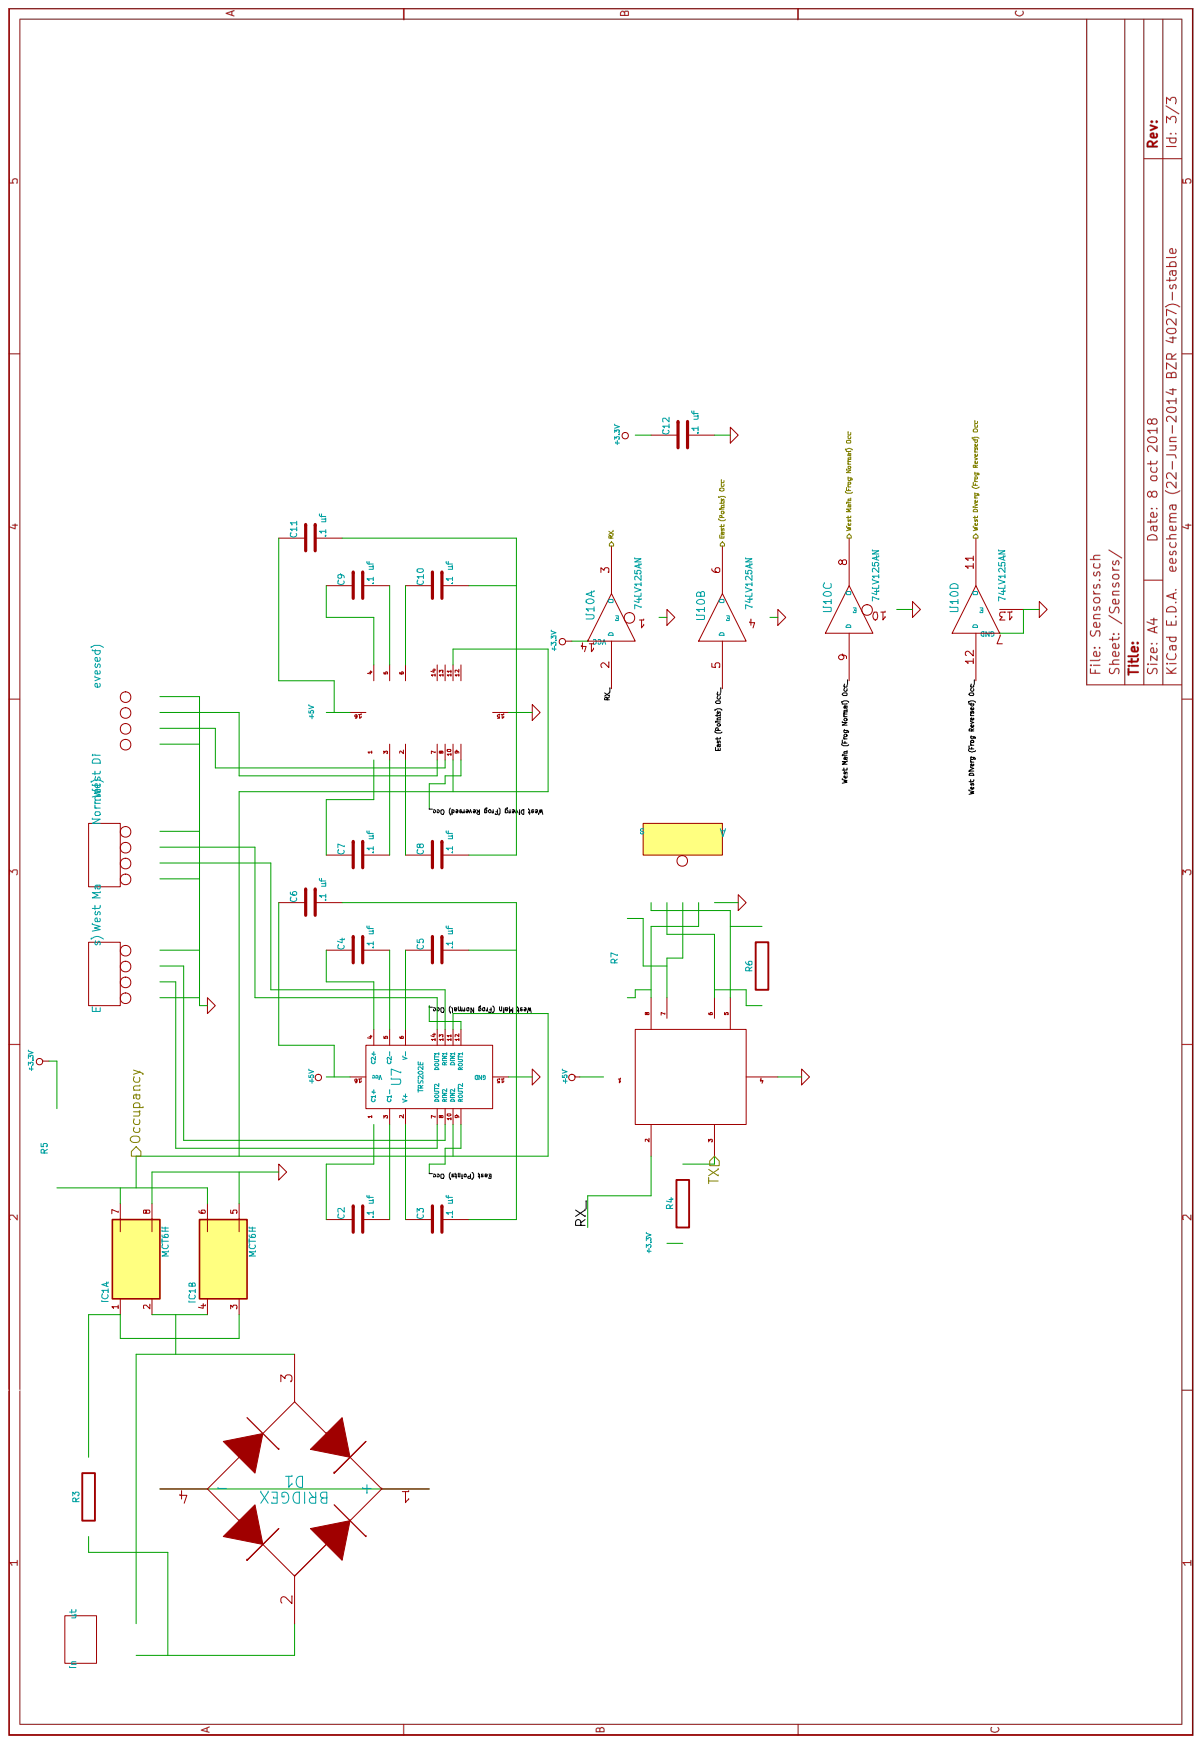
[picture p69: page 3]
