RobertPHeller/RPi-RRCircuits/MetroMiniABSBiDir-noCANSlave/MetroMiniABSBiDir-noCANSlave.pdf

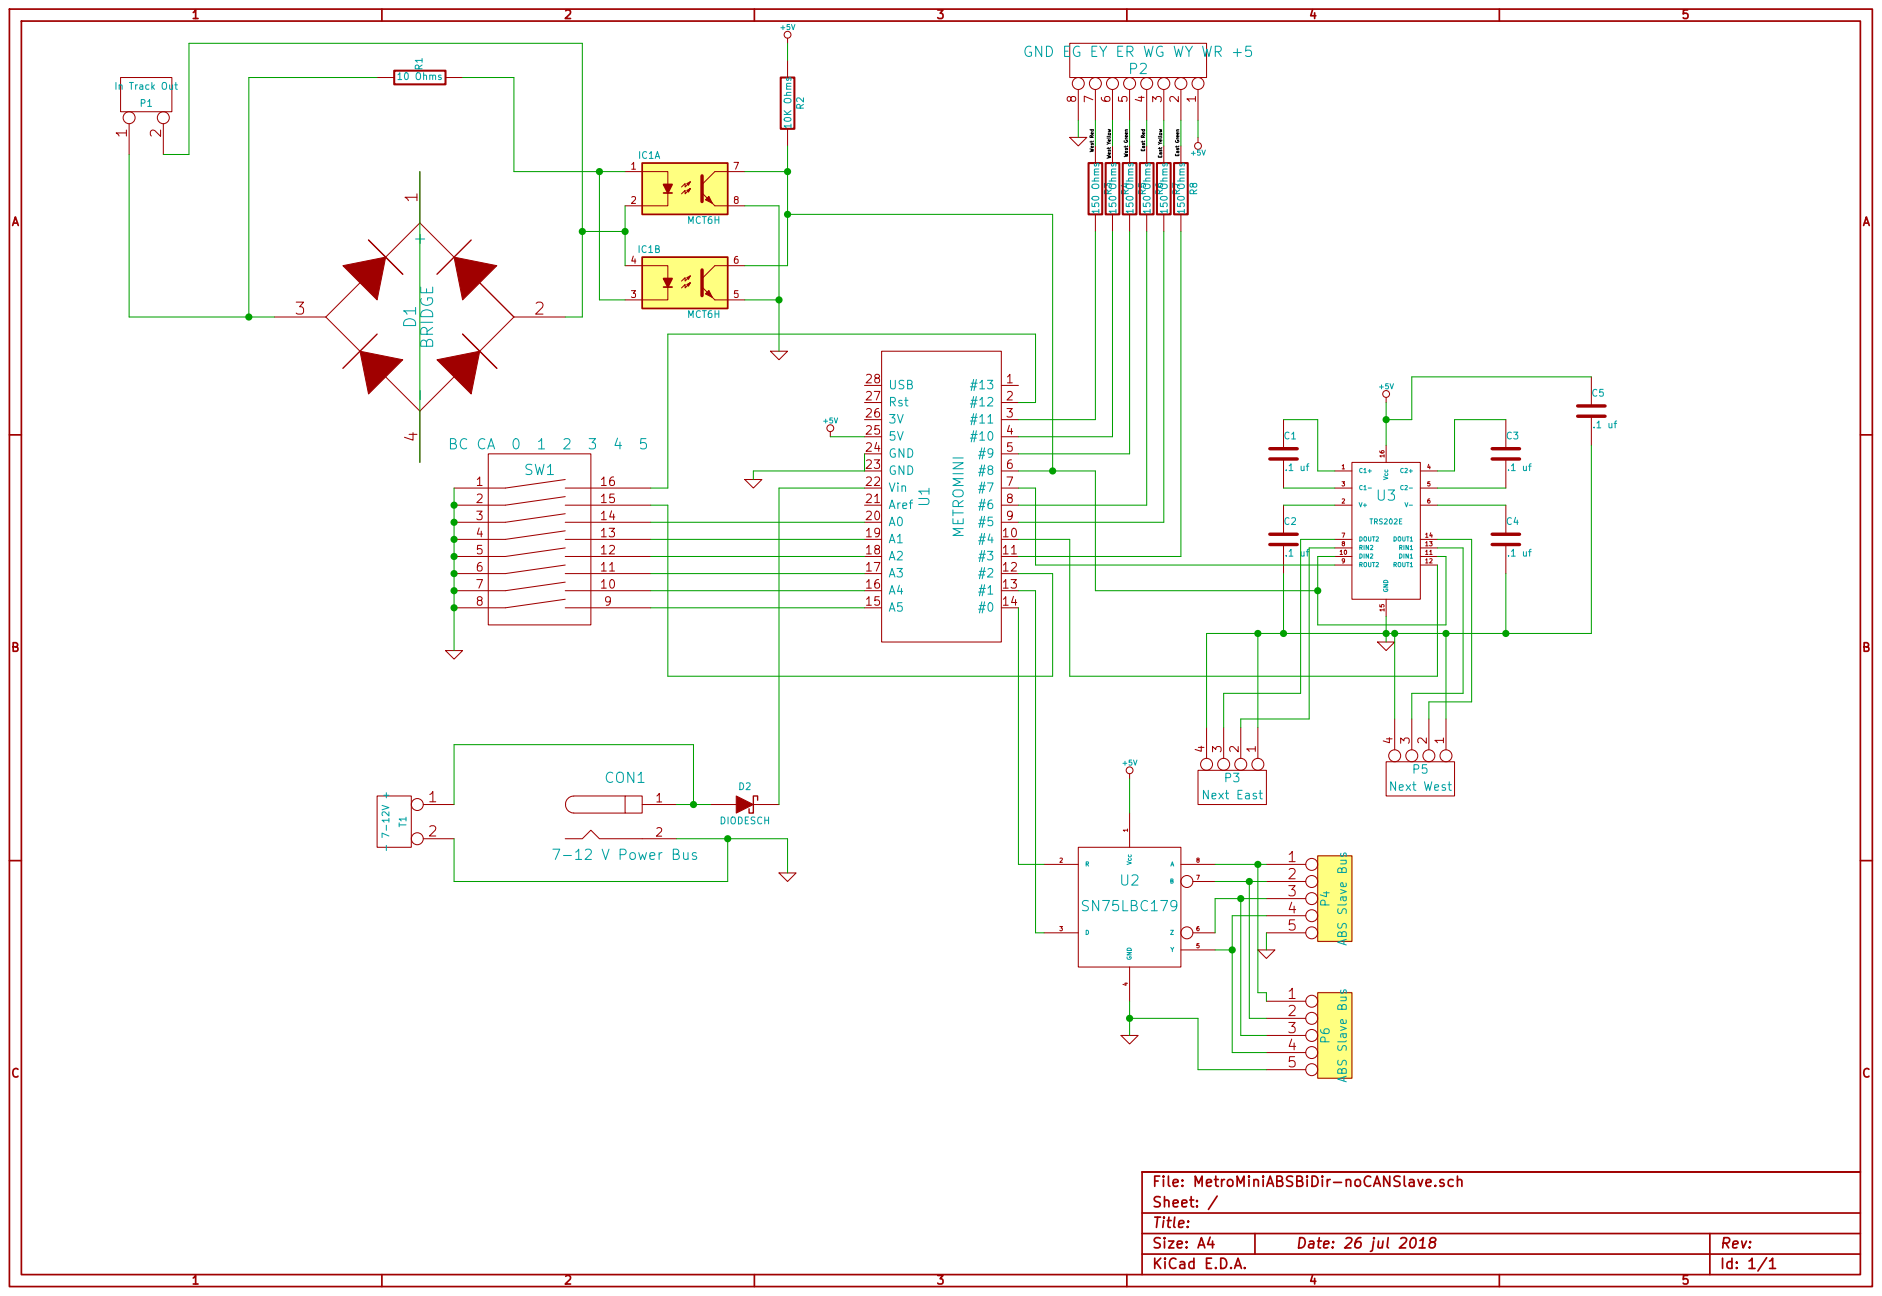
[picture p70: page 1]

Id: 1/1 Title: File: MetroMiniABSBiDir-noCANSlave.sch
