RobertPHeller/RPi-RRCircuits/MetroMiniABS/MetroMiniABS.pdf

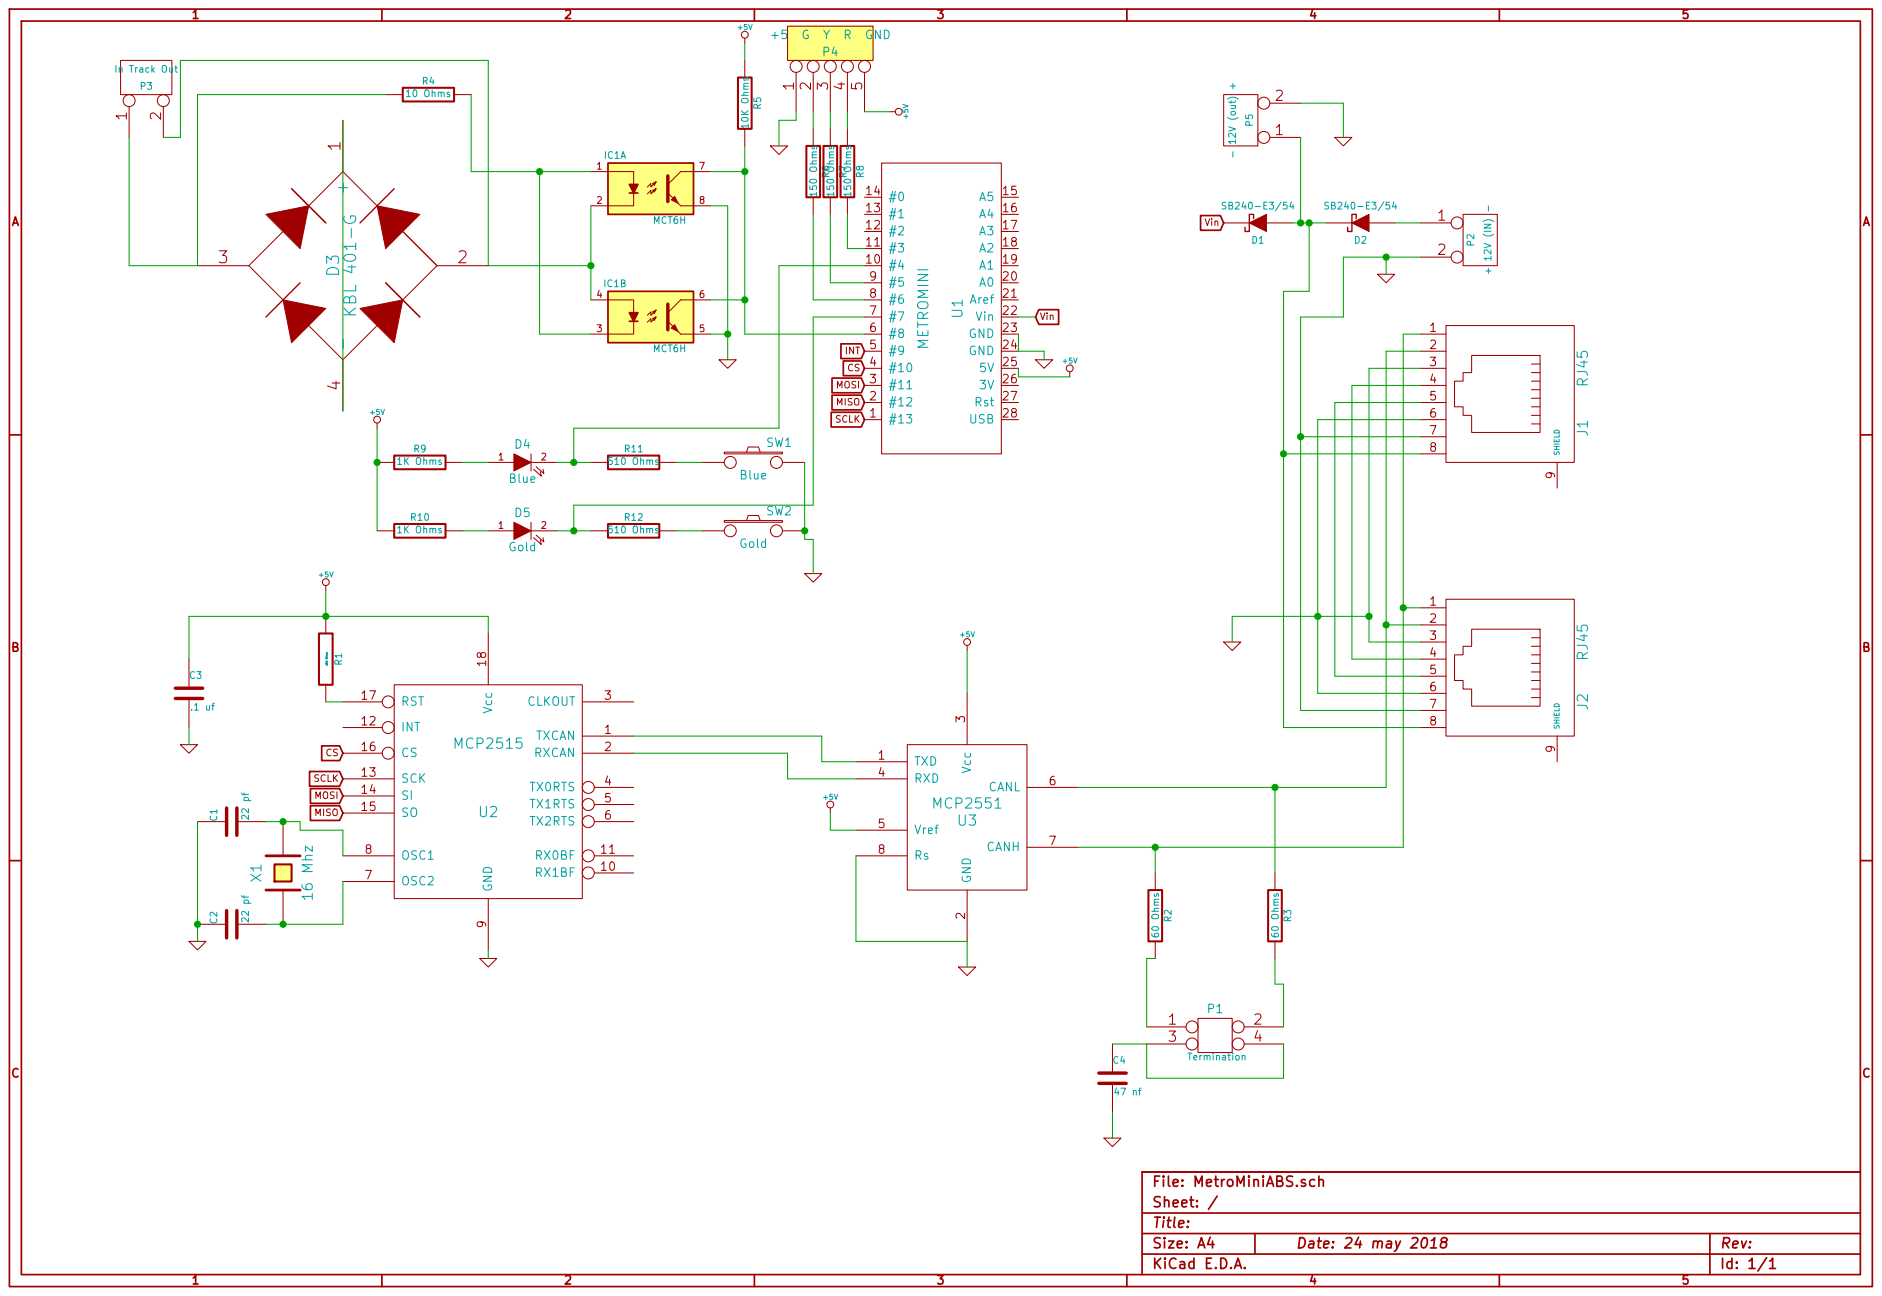
[picture p71: page 1]

Id: 1/1 Title: File: MetroMiniABS.sch
