RobertPHeller/RPi-RRCircuits/QuadSignalDriverCA/QuadSignalDriverCA.pdf

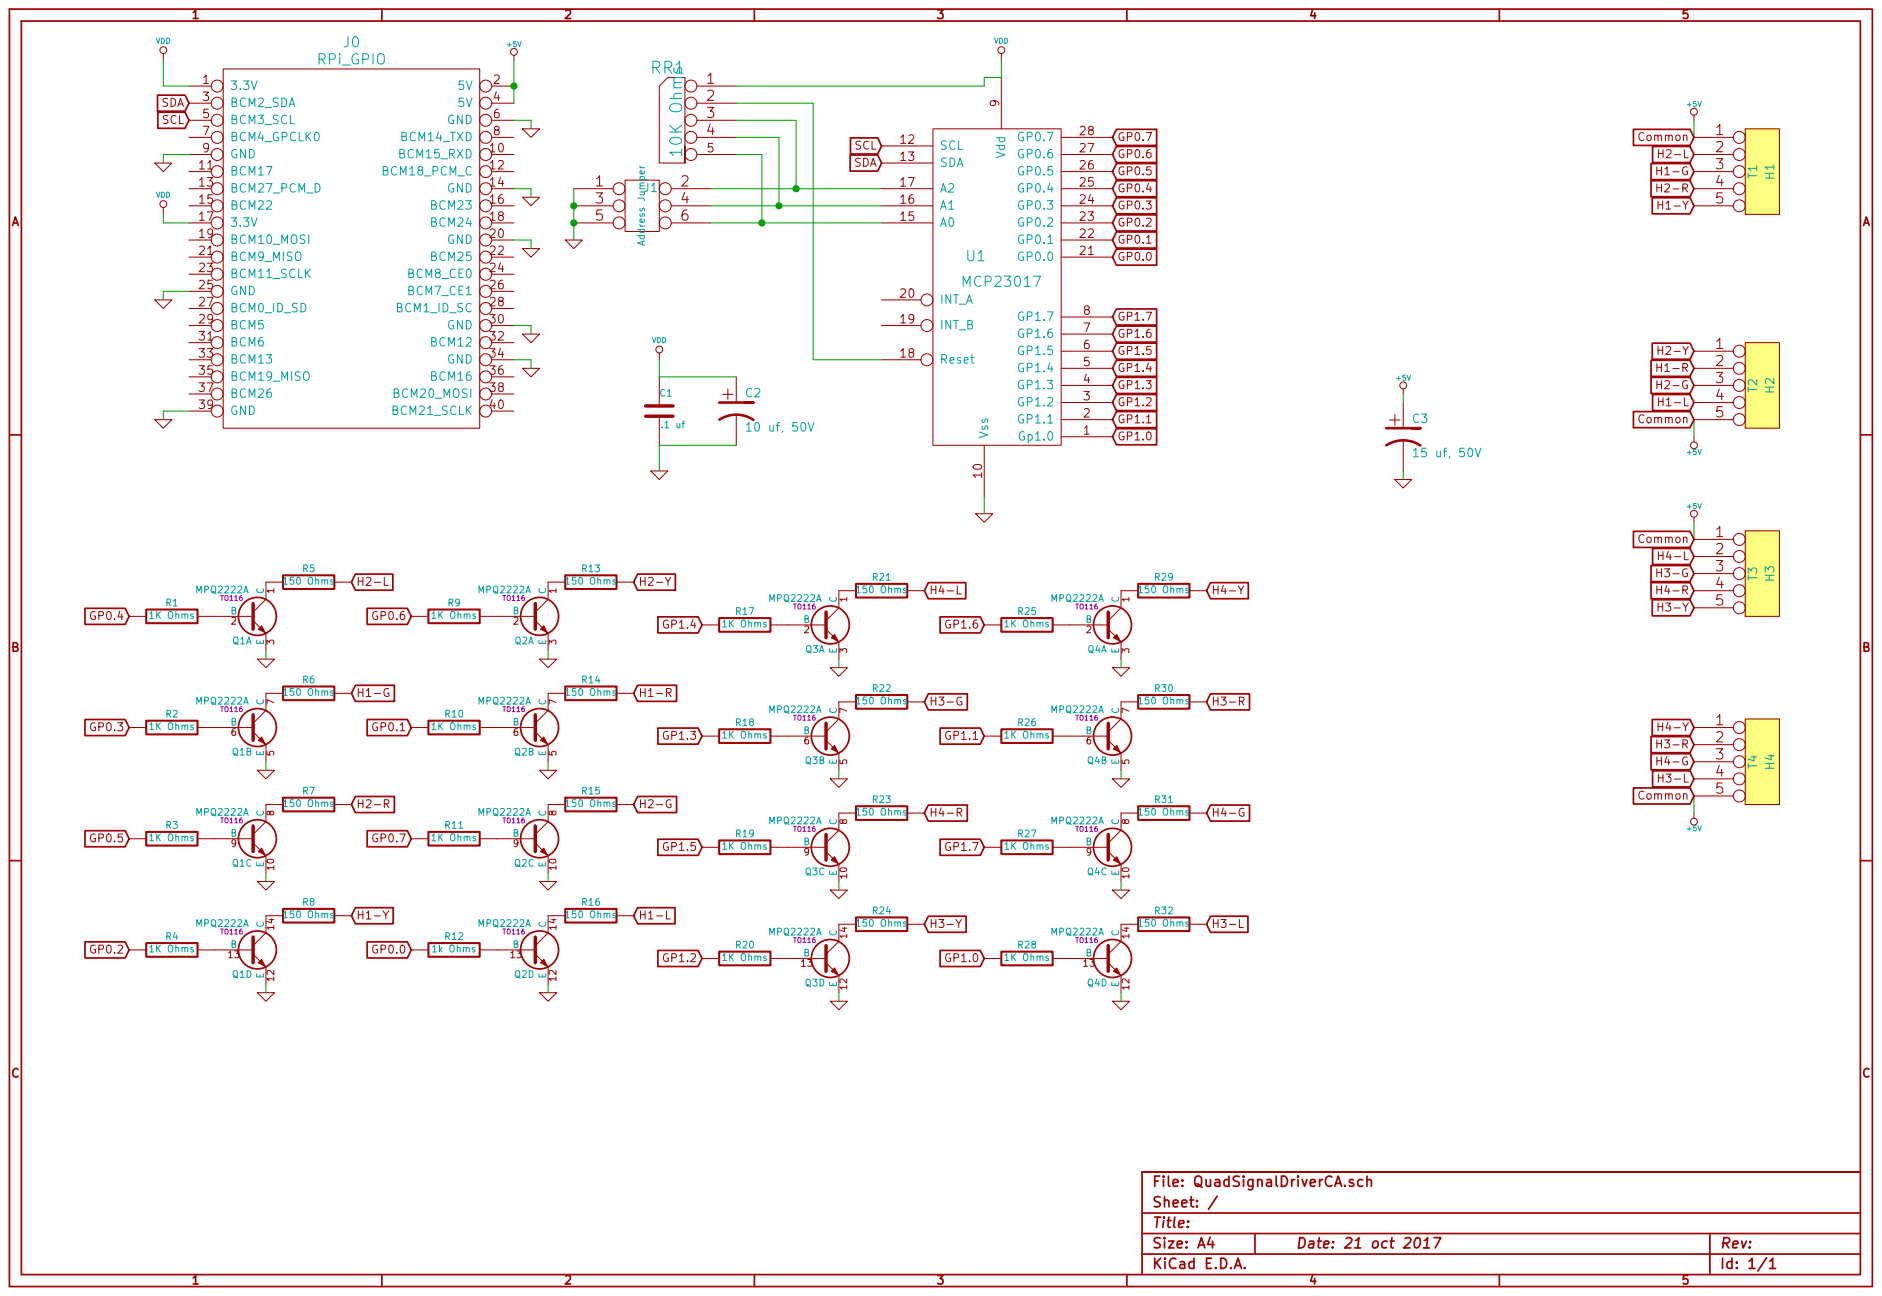
[picture p72: page 1]

Id: 1/1 Title: File: QuadSignalDriverCA.sch
Sheet: /
