RobertPHeller/RPi-RRCircuits/CANHat2/CANHat2.pdf

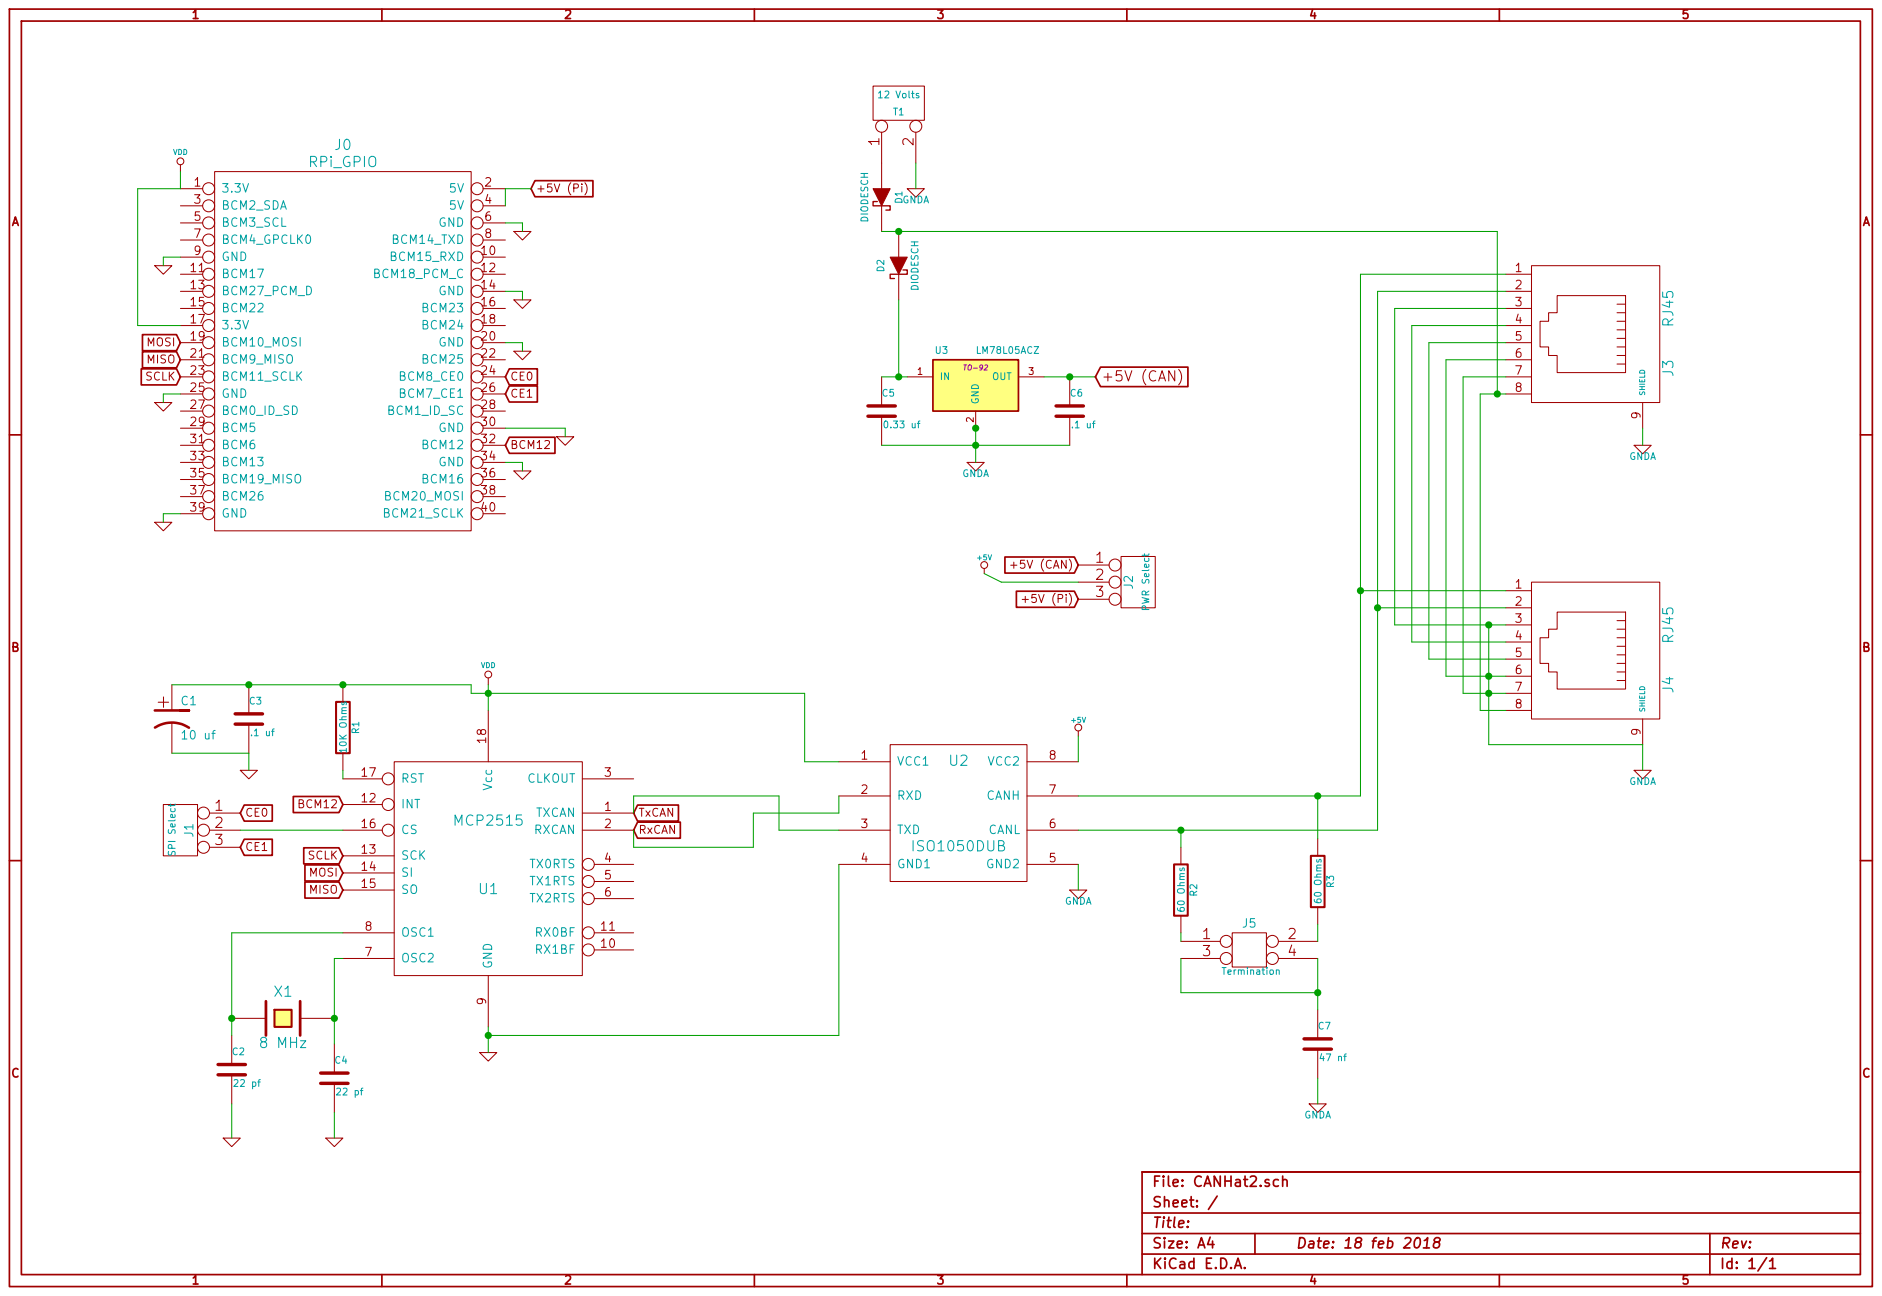
[picture p73: page 1]

Id: 1/1 Title: File: CANHat2.sch
Sheet: /
