RobertPHeller/RPi-RRCircuits/MCP23017Hat/MCP23017.pdf

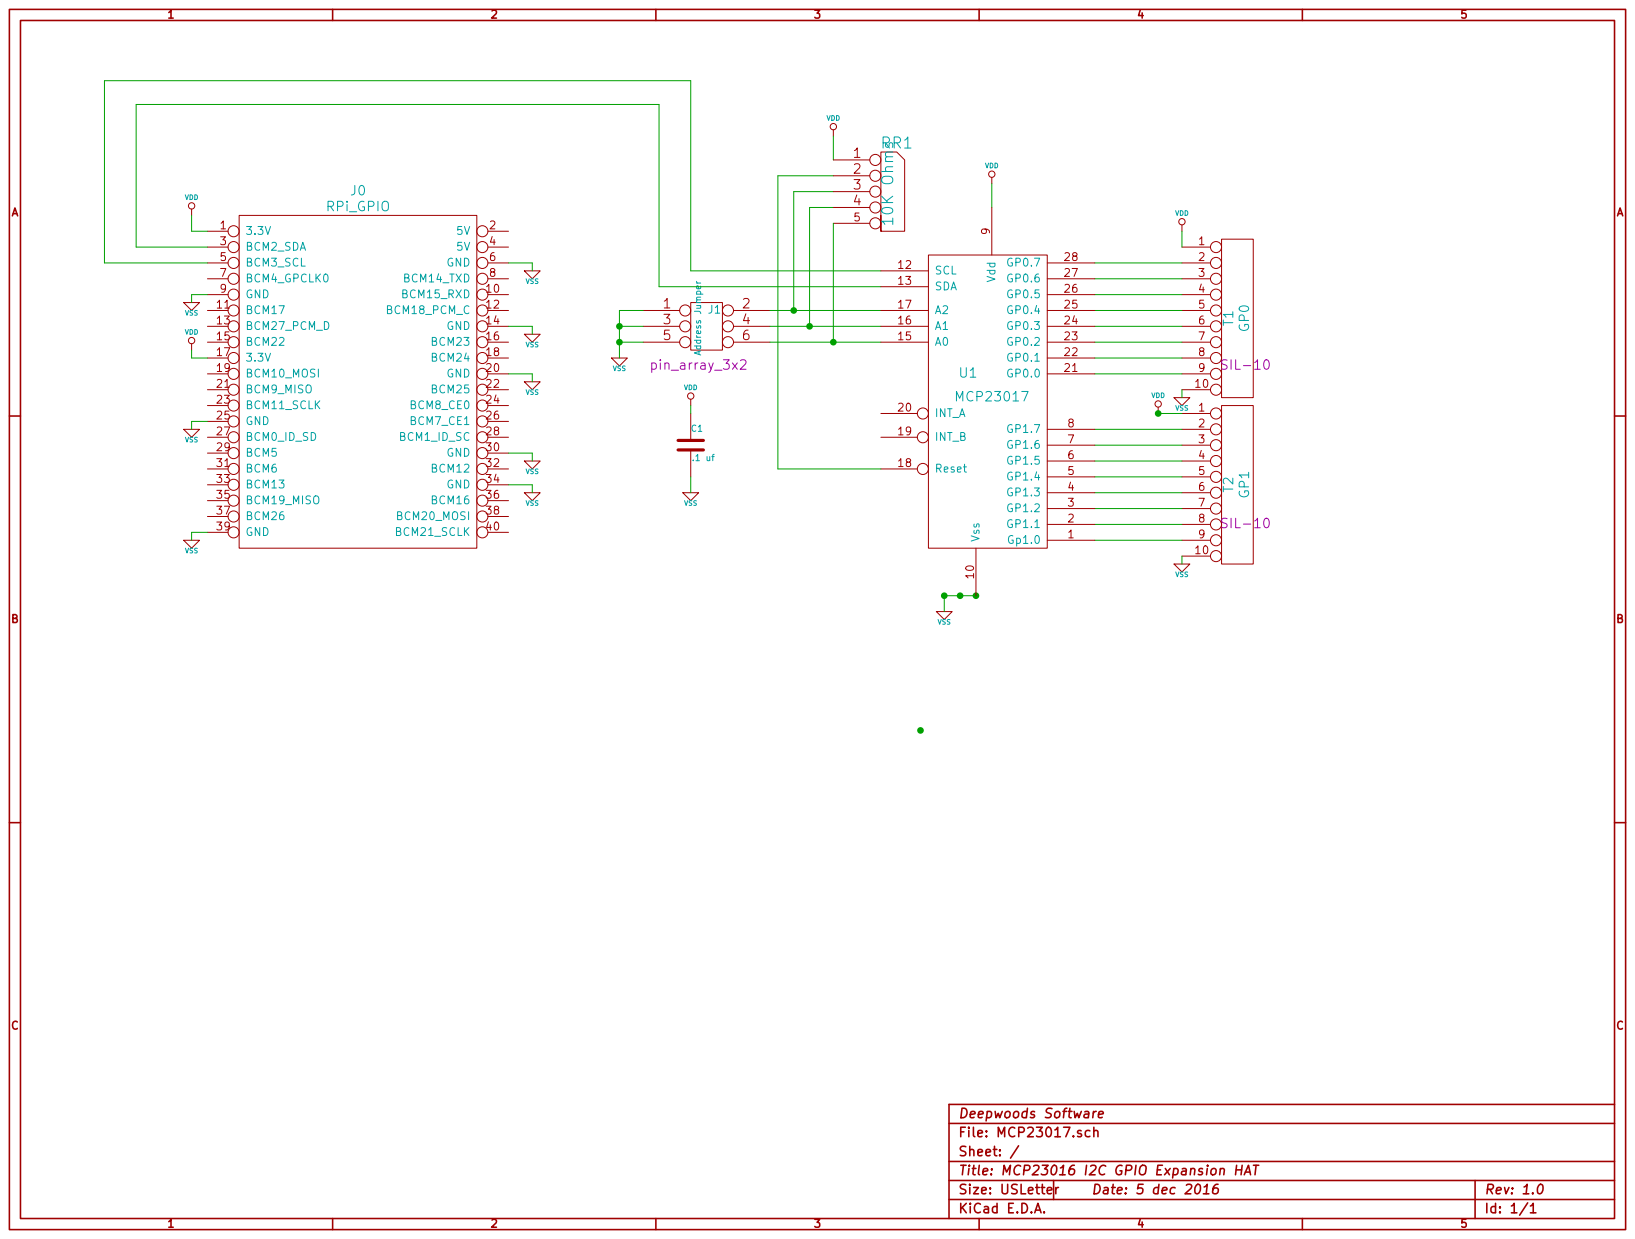
[picture p74: page 1]
