RobertPHeller/RPi-RRCircuits/OctalLEDDriver/OctalLEDDriver.pdf

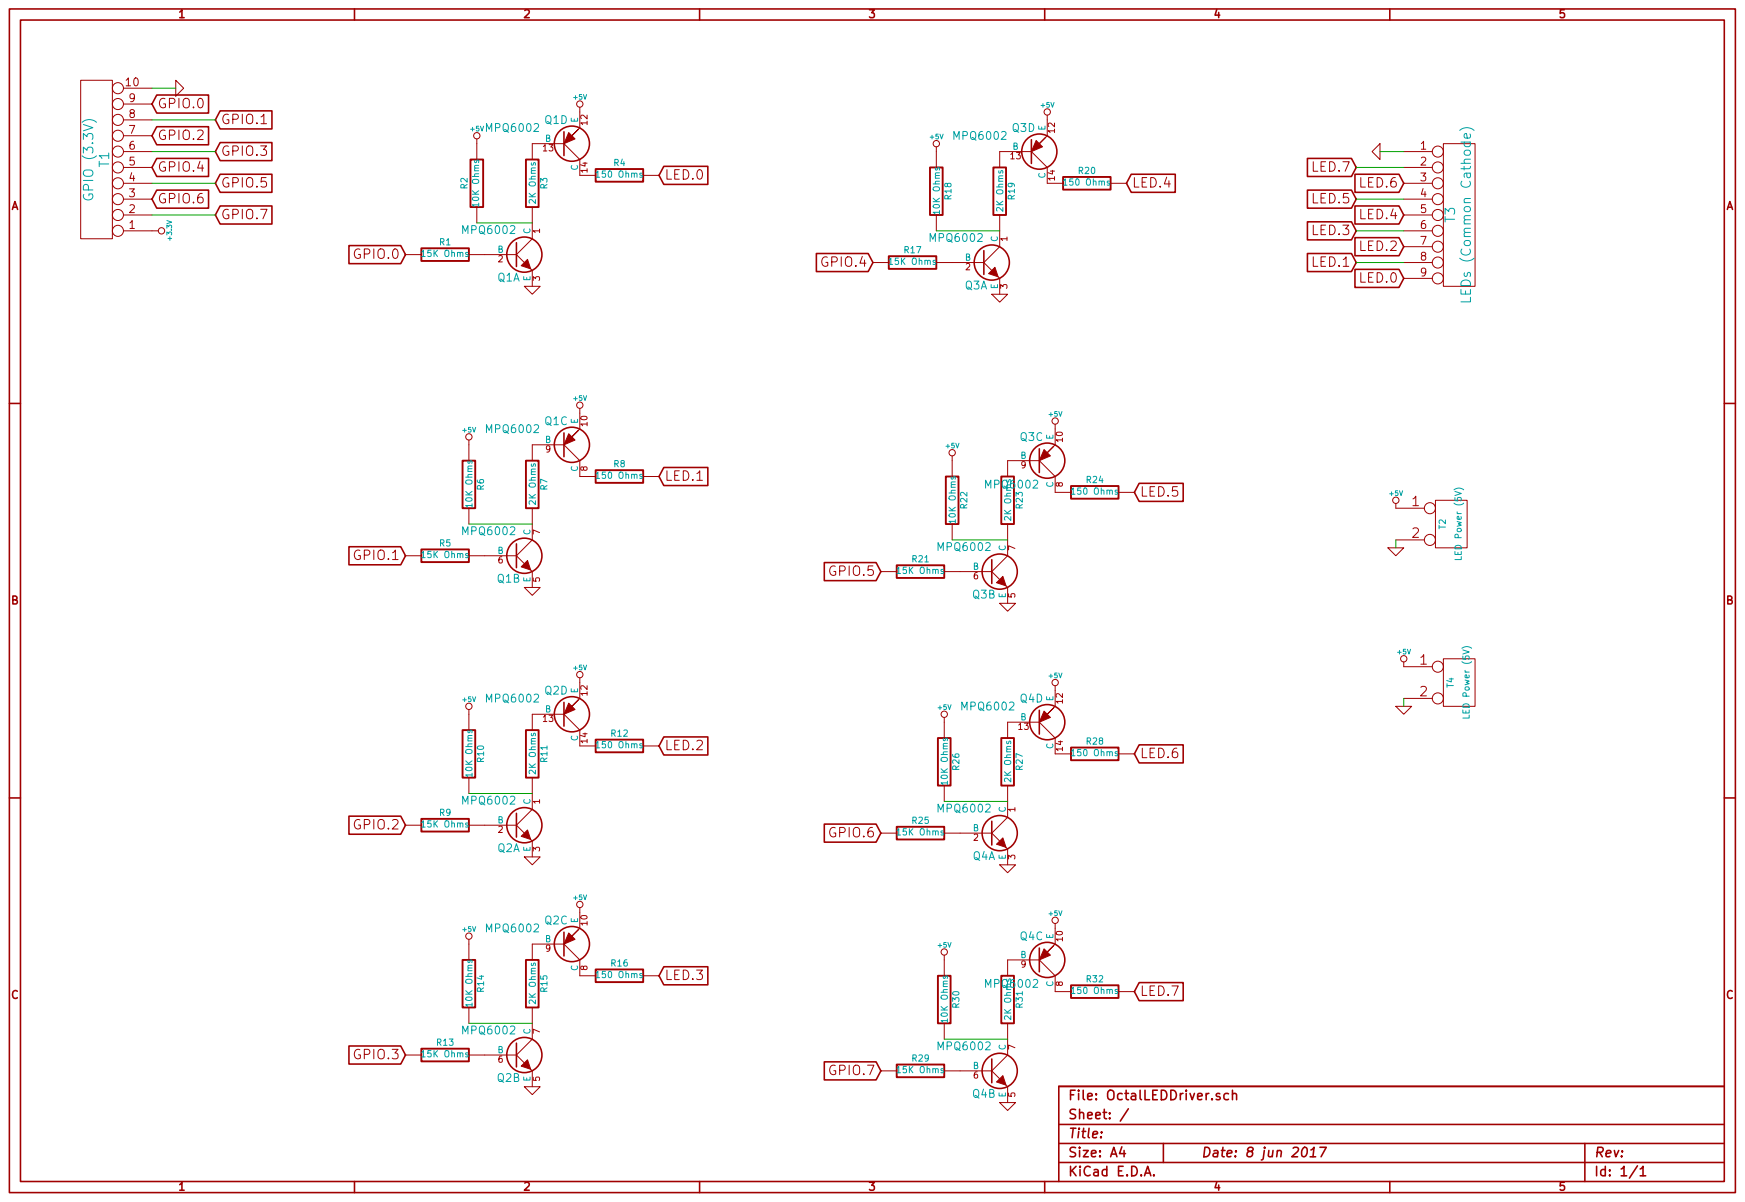
[picture p75: page 1]
