RobertPHeller/RPi-RRCircuits/QuadSSSQuadIn/QuadSSSQuadIn.pdf

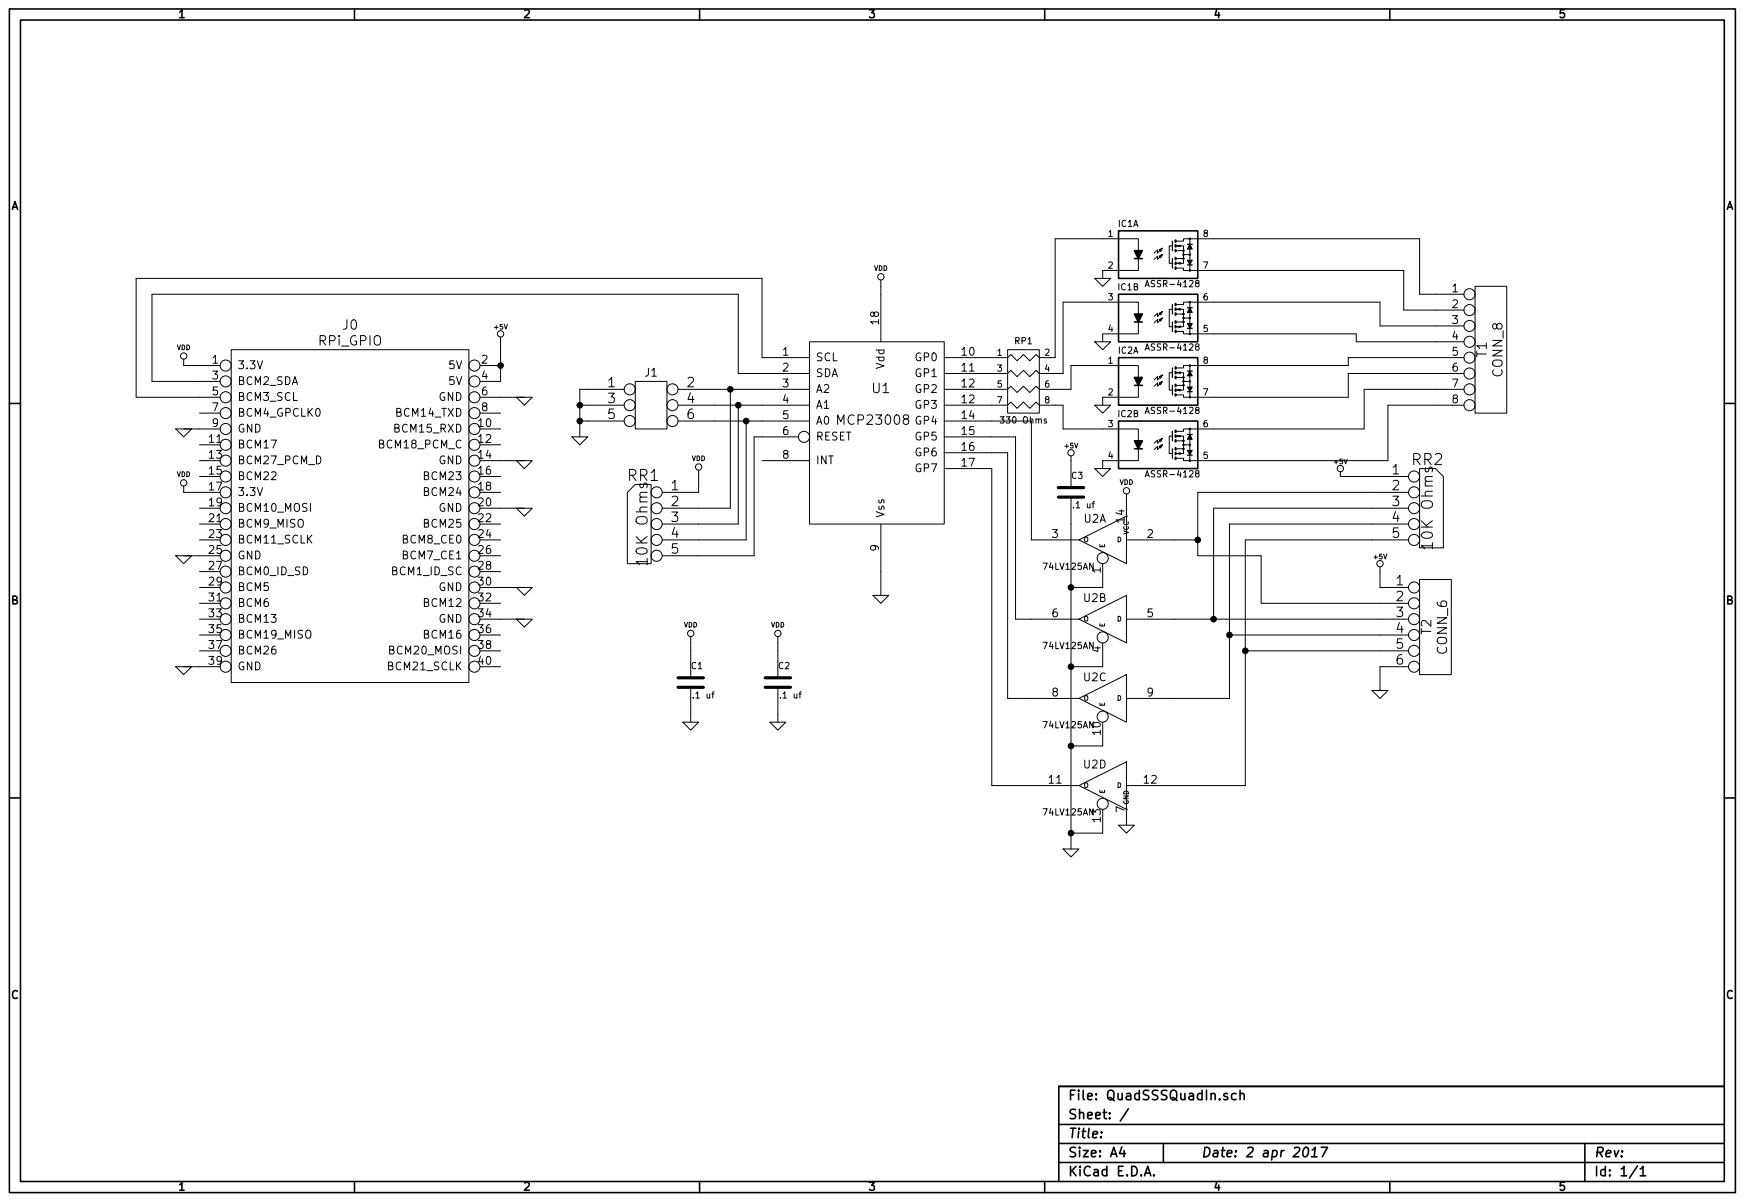
[picture p76: page 1]
