RobertPHeller/RPi-RRCircuits/SMCSenseHAT/SMCSenseHAT.pdf

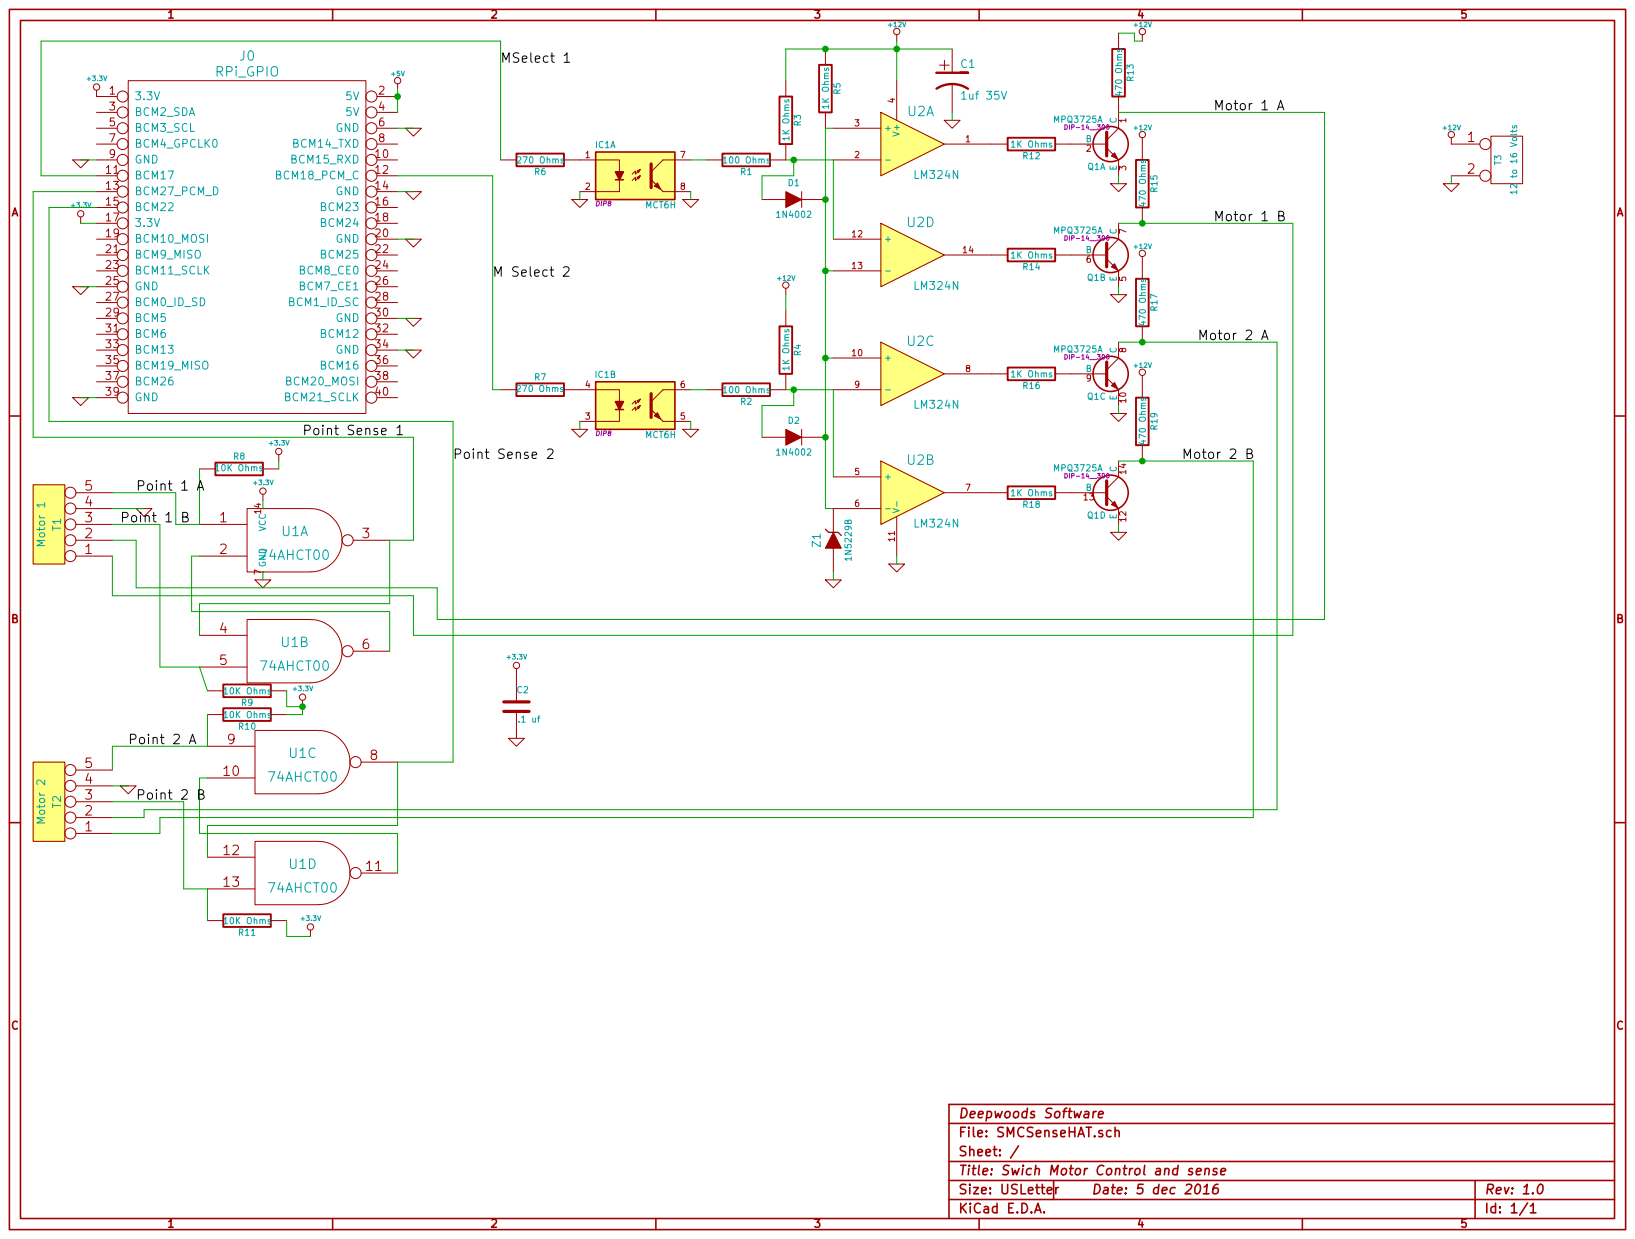
[picture p77: page 1]
