RobertPHeller/RPi-RRCircuits/ButtonHat/ButtonHat.pdf

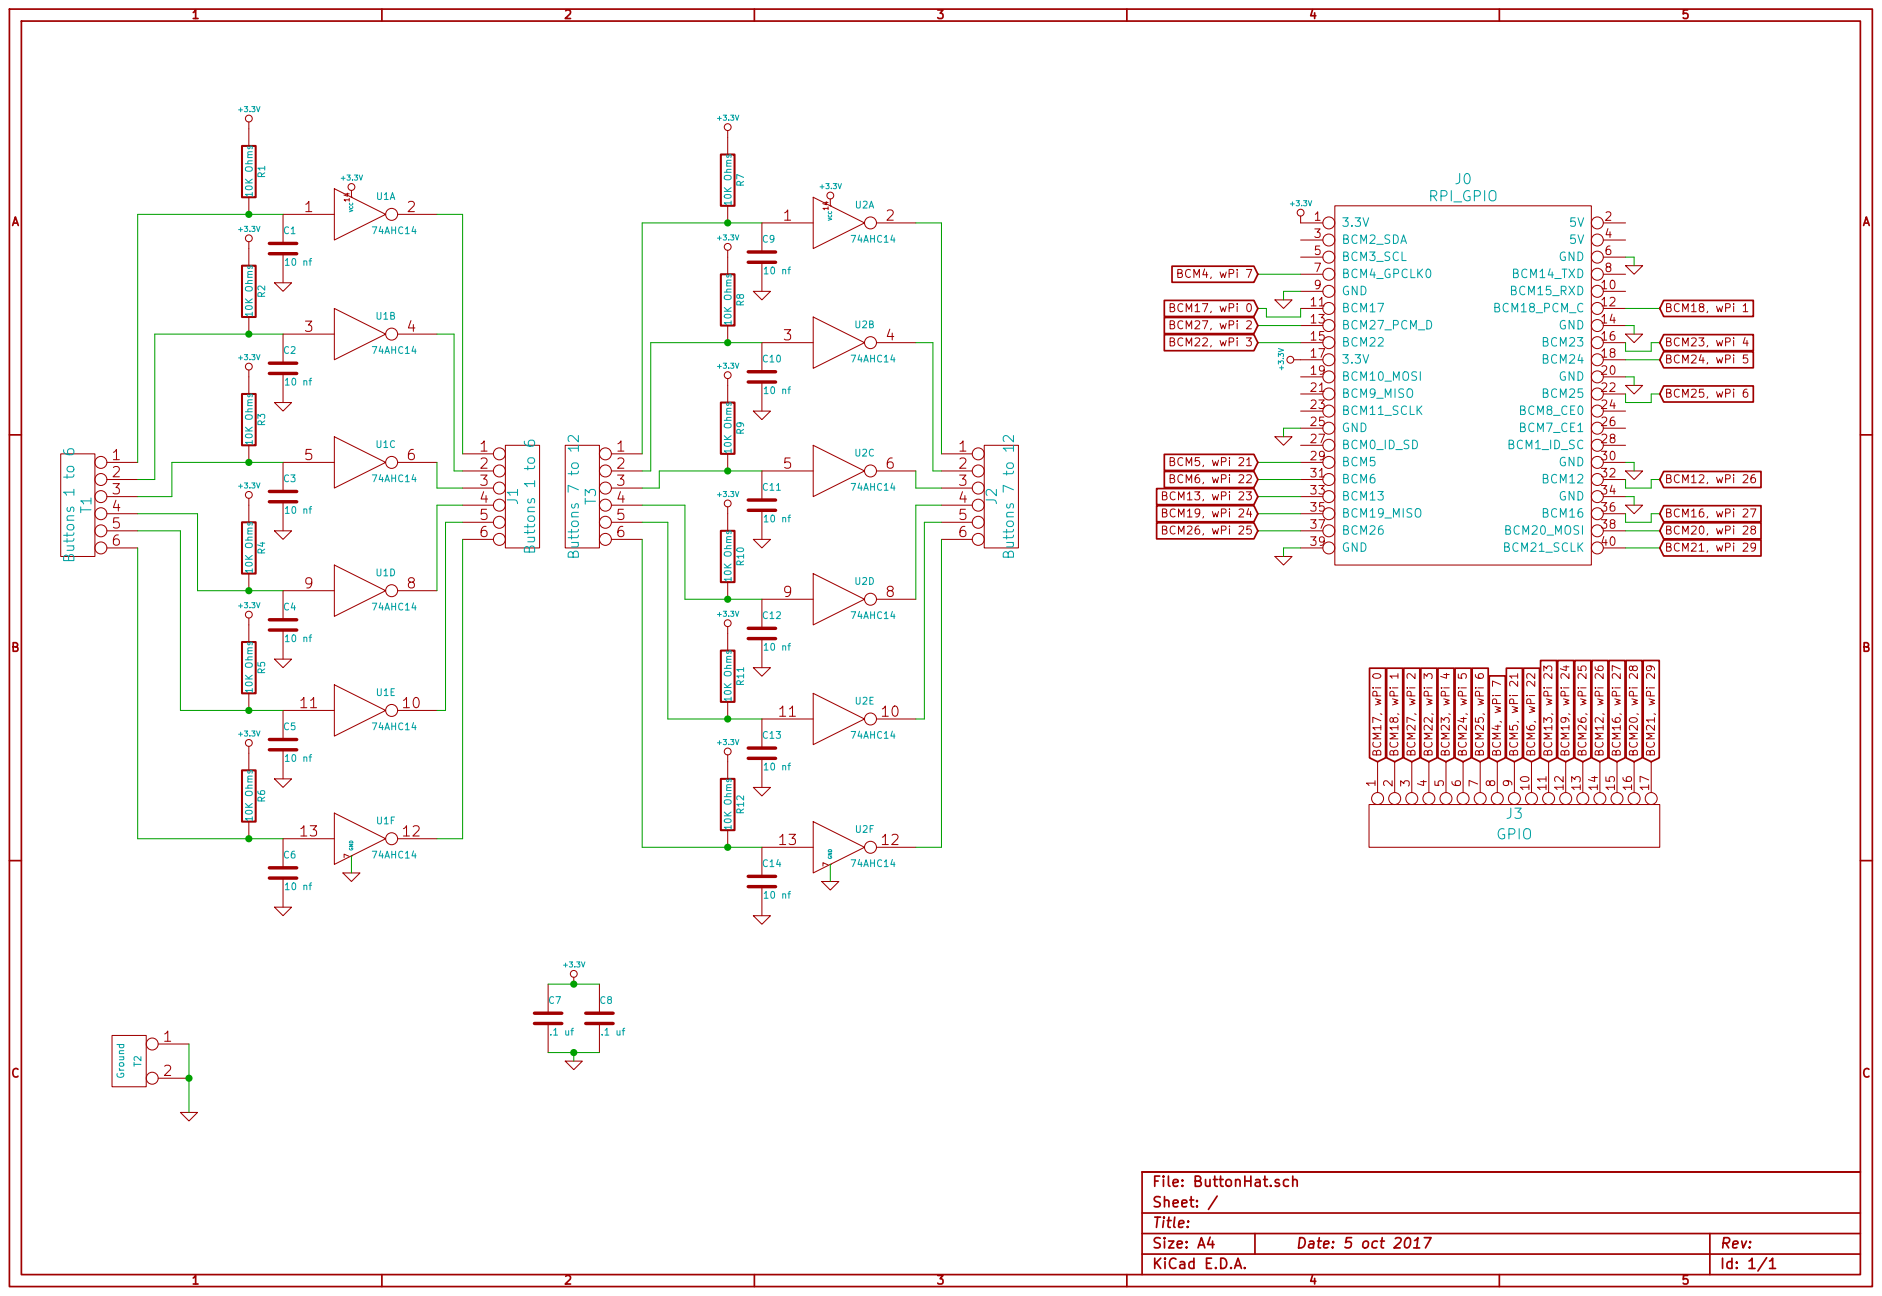
[picture p78: page 1]
