RobertPHeller/RPi-RRCircuits/DualUncouplerHAT/DualUncouplerHAT.pdf

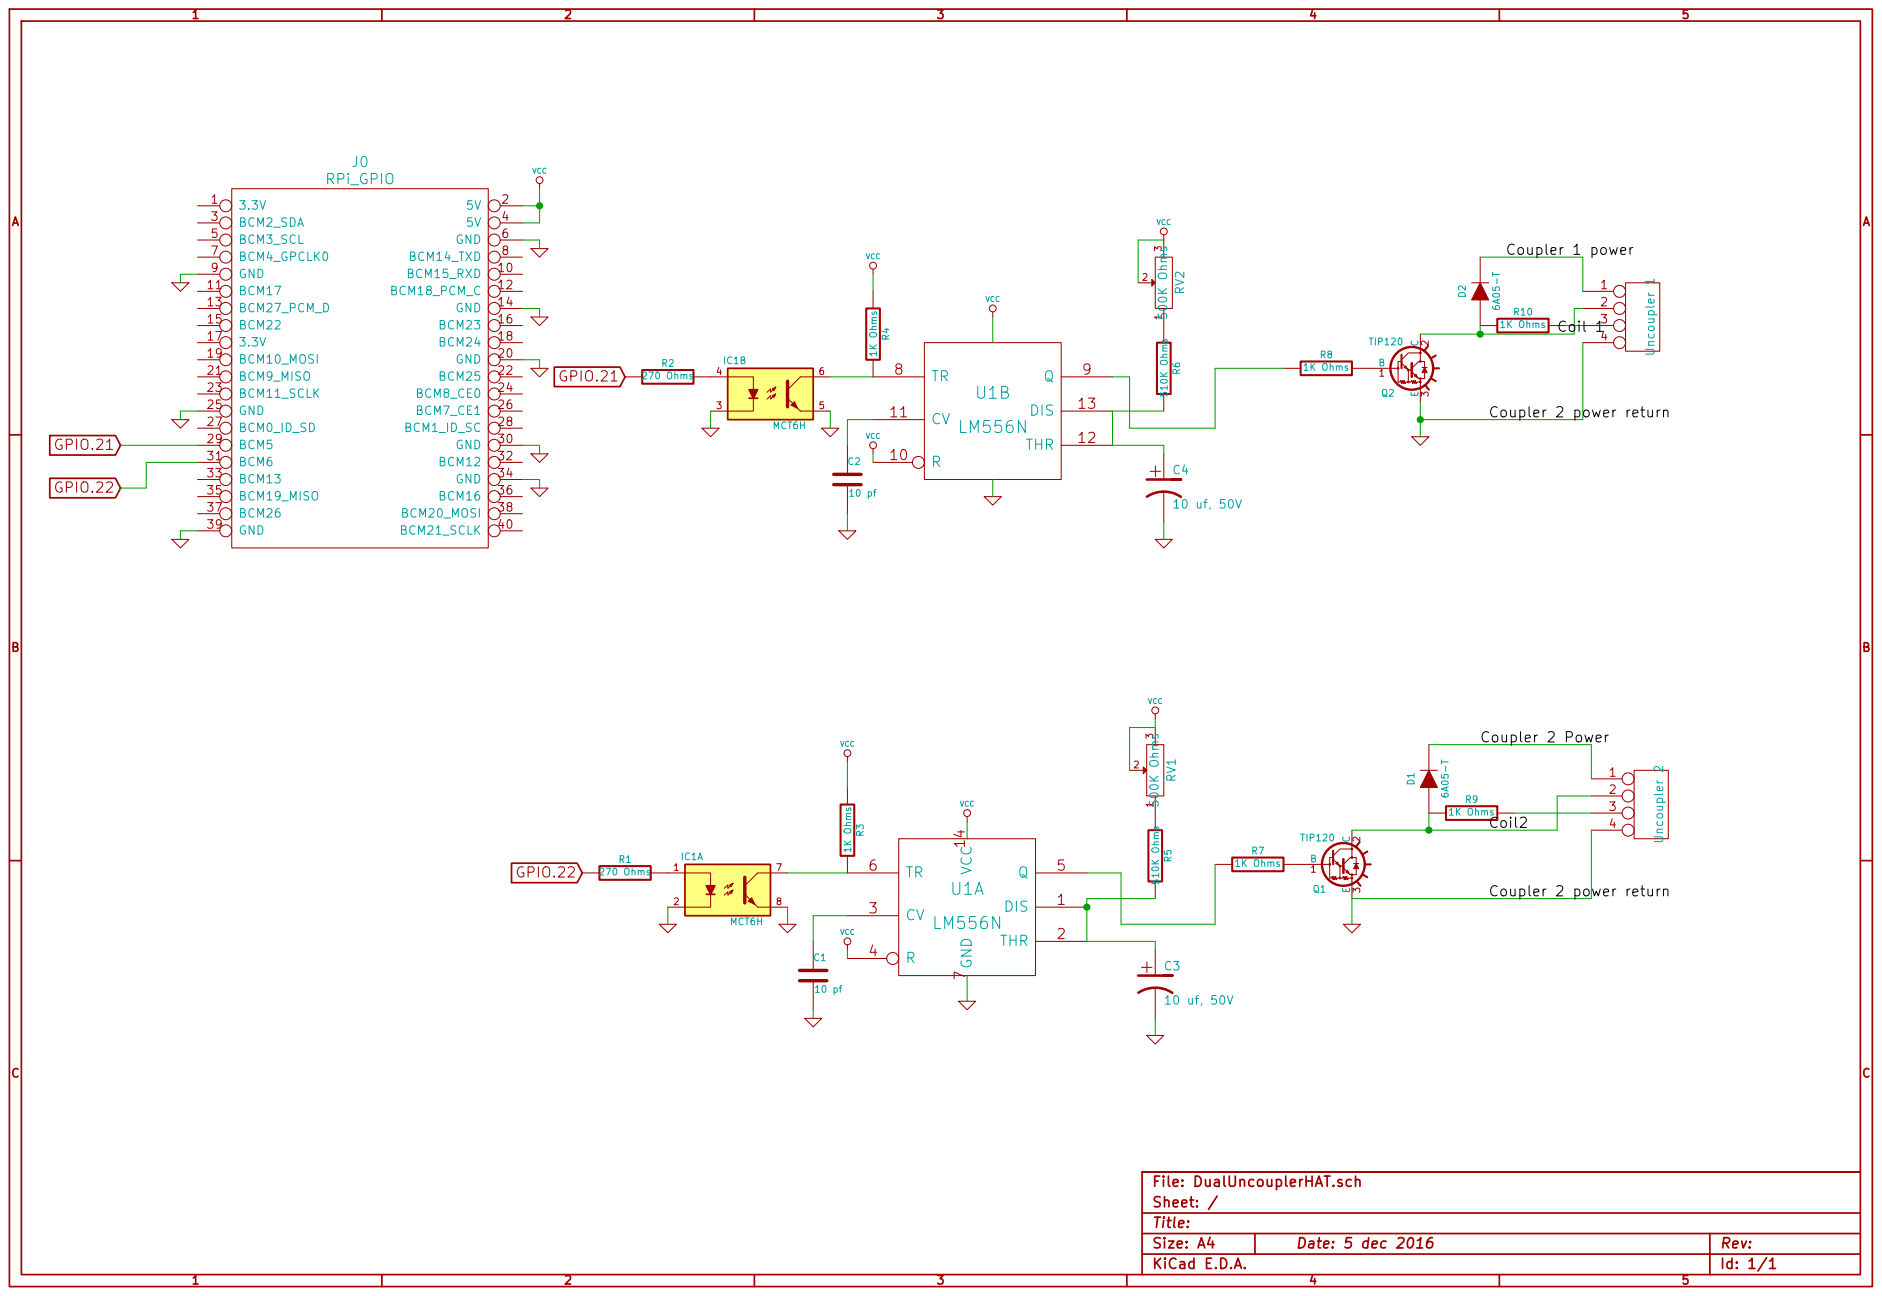
[picture p79: page 1]

MCT6H

Id: 1/1 Title: File: DualUncouplerHAT.sch
Sheet: /
