RobertPHeller/RPi-RRCircuits/QuadSMC/QuadSMC.pdf

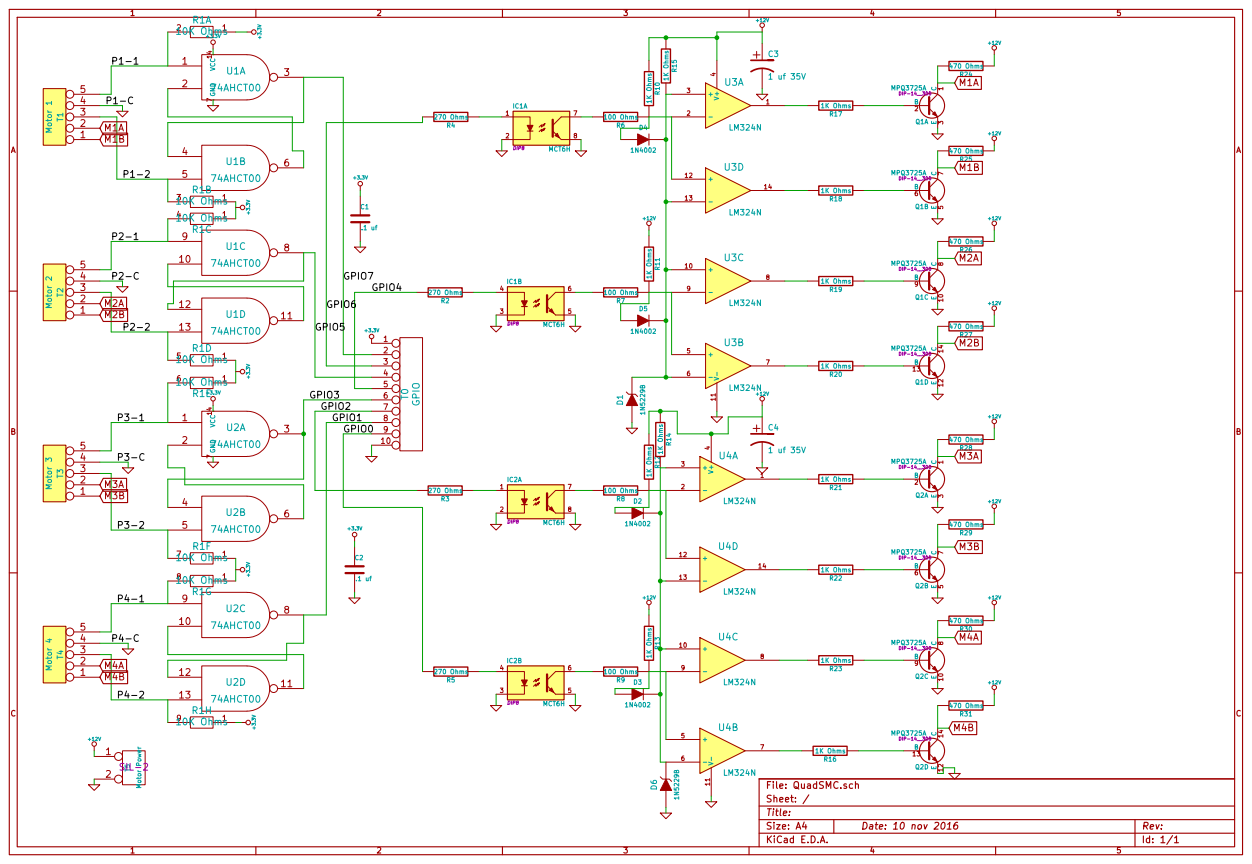
[picture p80: page 1]

Id: 1/1 Title: File: QuadSMC.sch
