RobertPHeller/RPi-RRCircuits/QuadUncoupler/QuadUncoupler.pdf

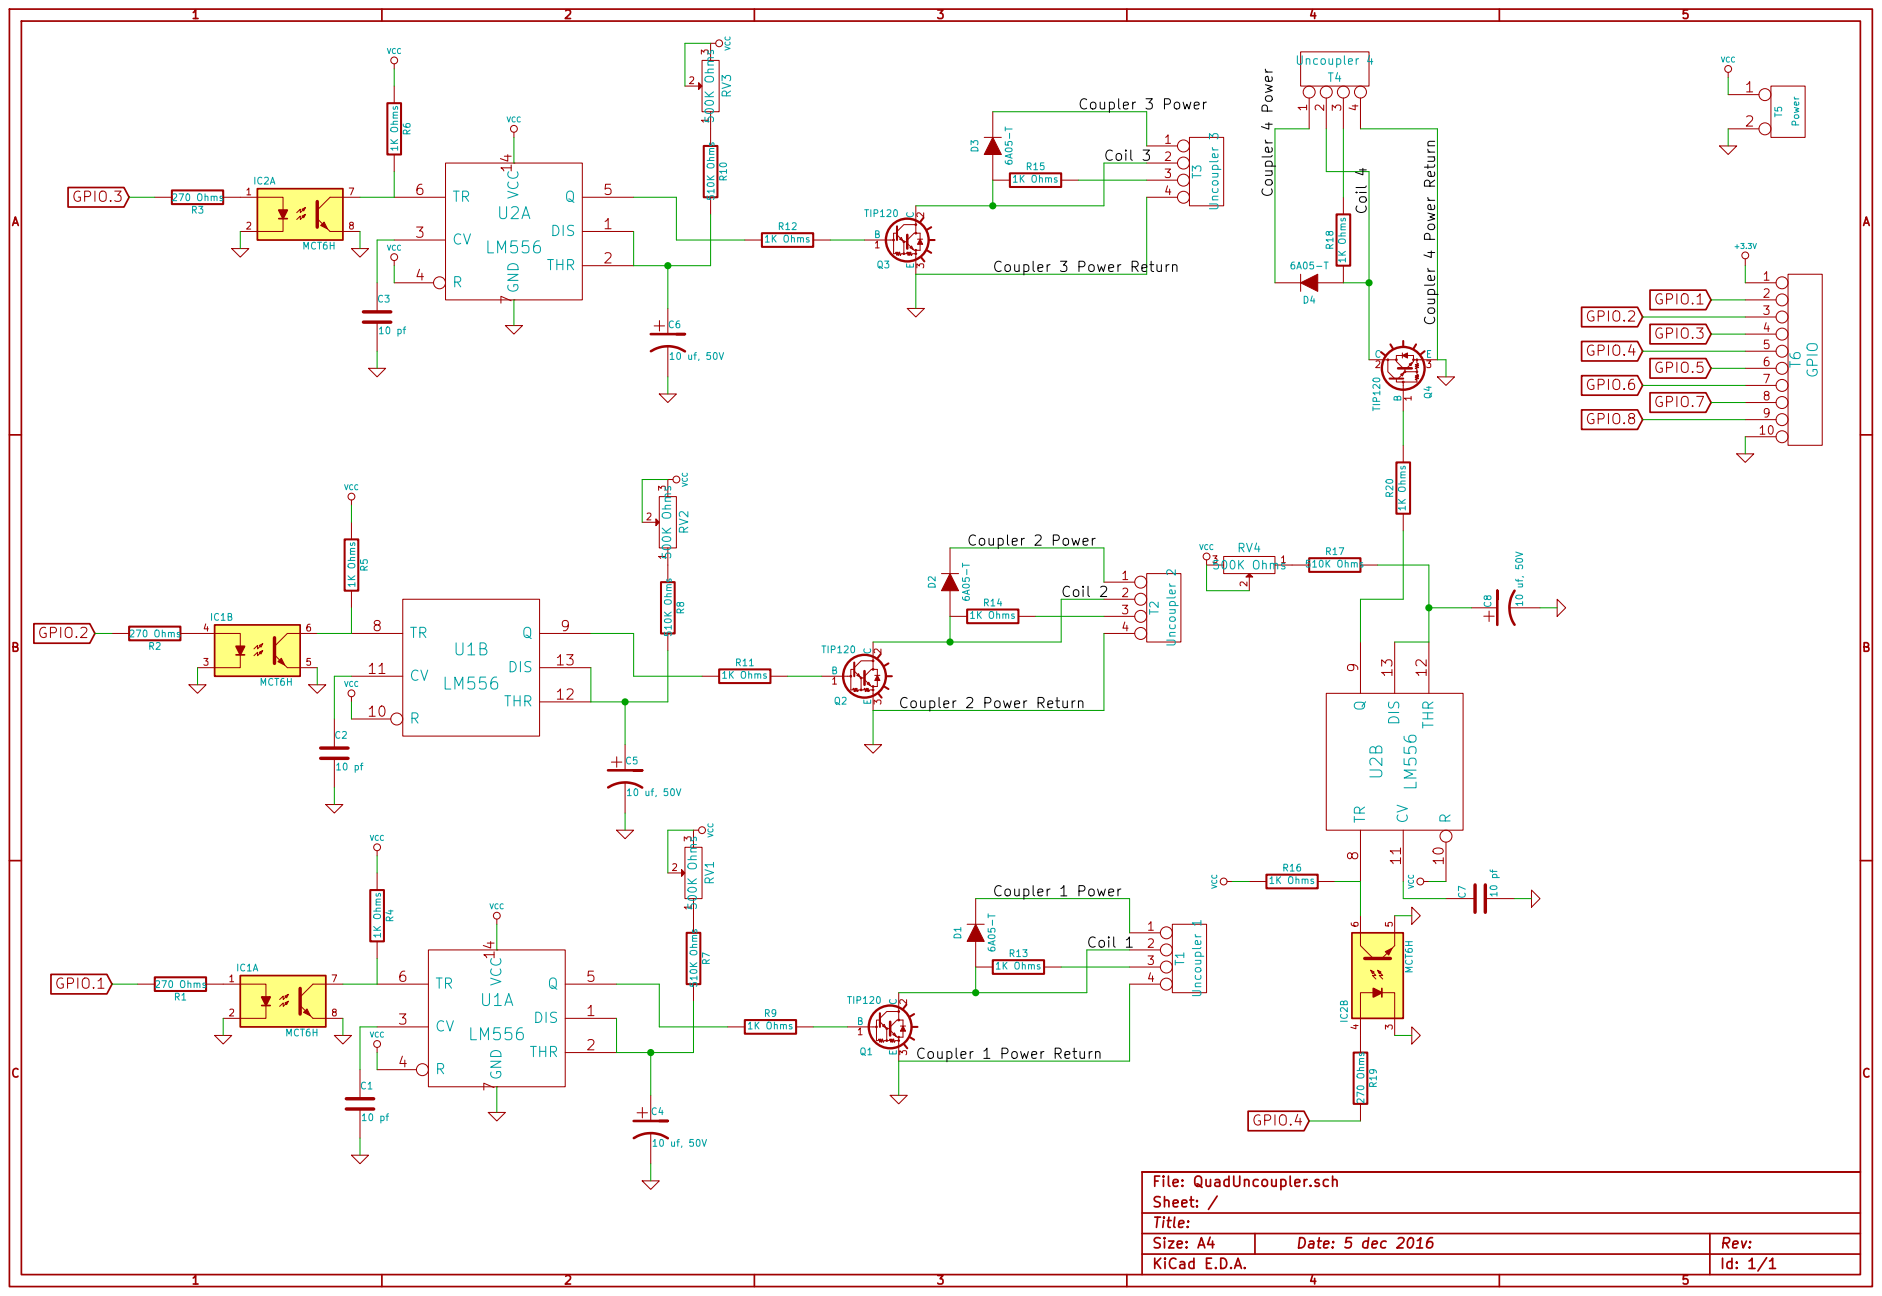
[picture p81: page 1]

Id: 1/1 Title: File: QuadUncoupler.sch
Sheet: /
