RobertPHeller/RPi-RRCircuits/SignalHAT/SignalHAT.pdf

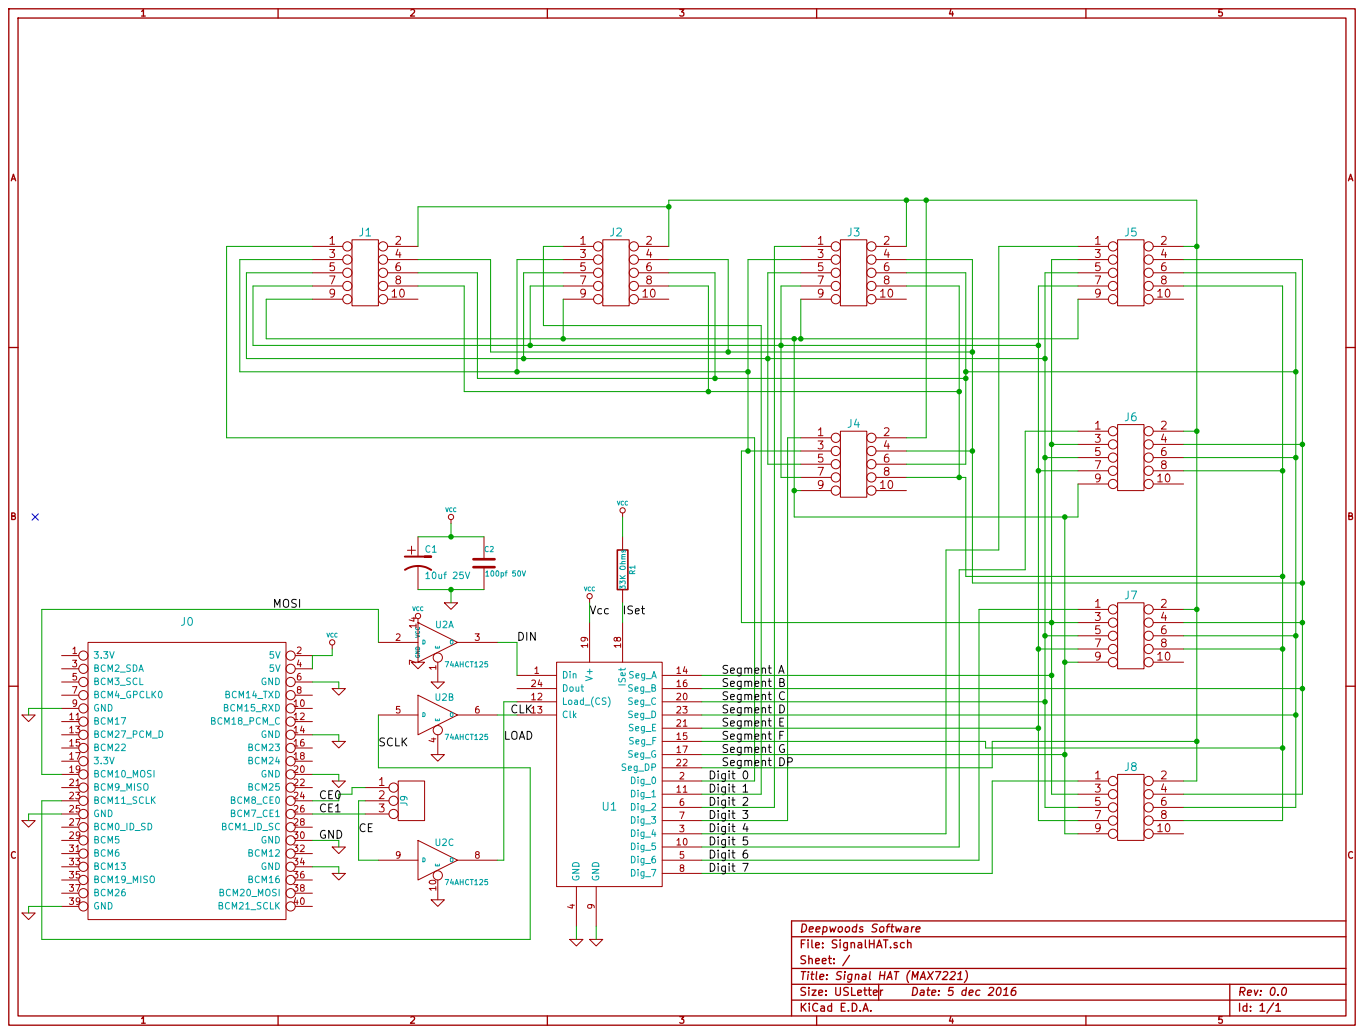
[picture p82: page 1]

J3 | | J5
9 | | 10

J4

Segment B
Segment C

CLK | Segment D

Segment E
Segment F Segment G

Segment DP
Digit 0
