RobertPHeller/RPi-RRCircuits/16PWMLedDriverCape/16PWMLedDriverCape.kicad_pcb

## KiCad design 16PWMLedDriverCape/16PWMLedDriverCape.kicad_pcb (2020-01-30)

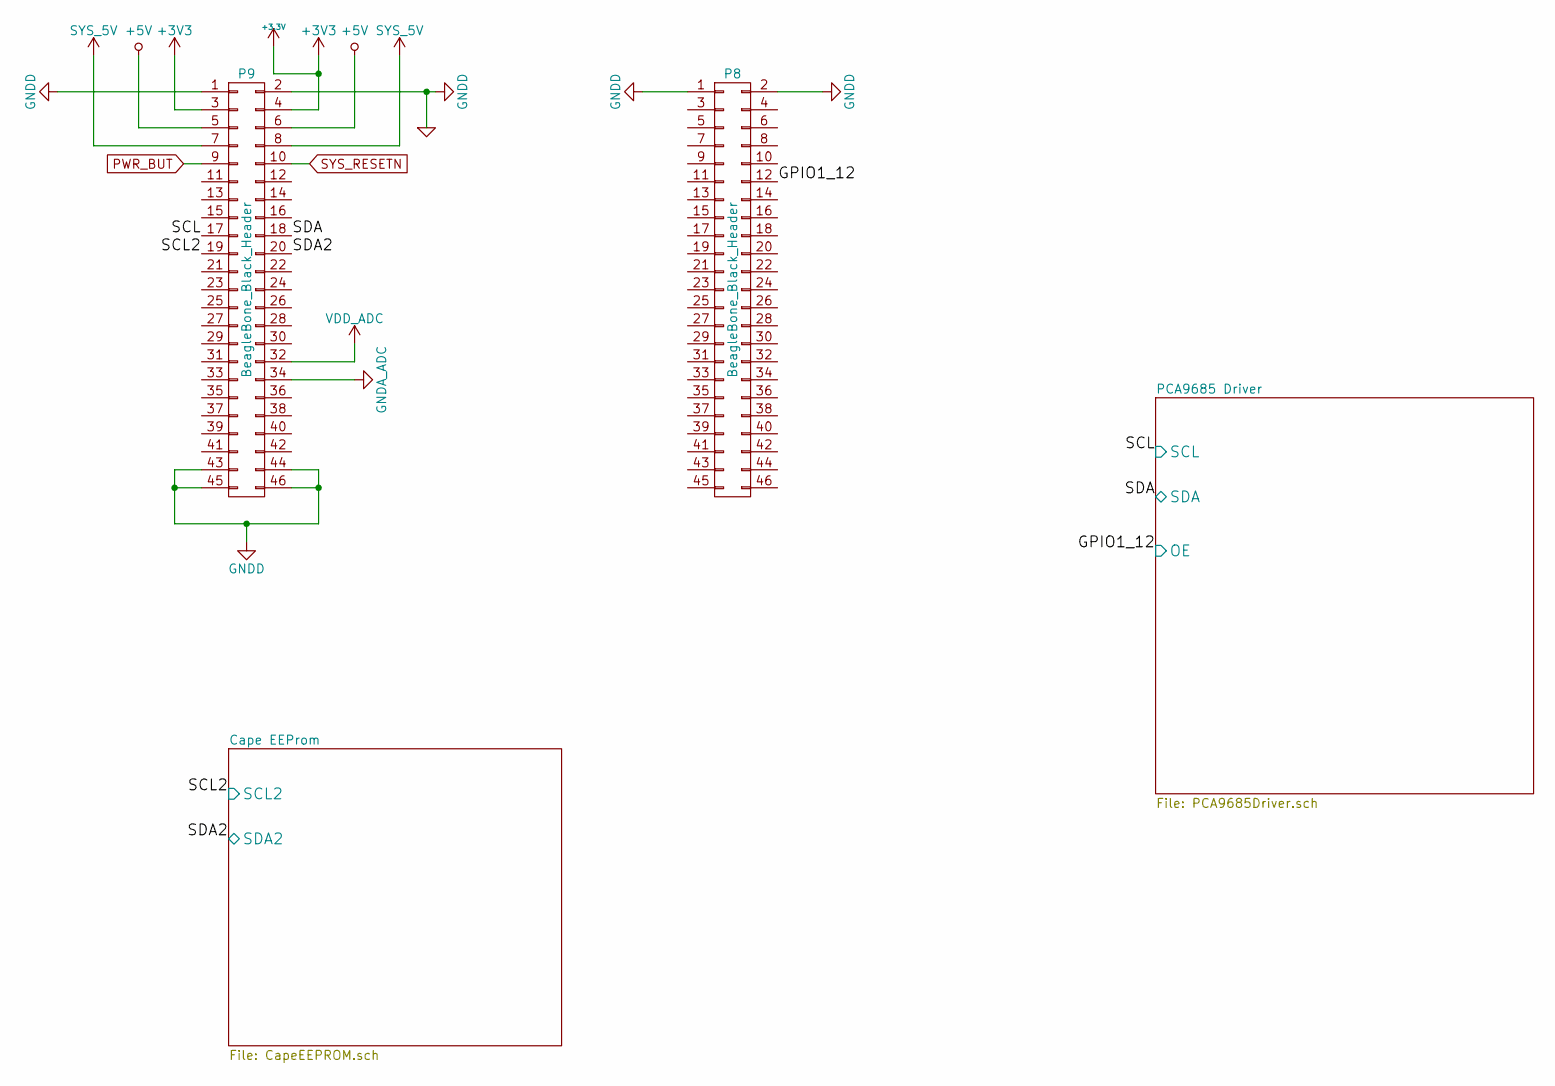
[picture p120: schematic 16PWMLedDriverCape.sch]

Parts:
P8, P9: BeagleBone_Black_Header; Socket_BeagleBone_Black

Connections:
+3.3V: P9.3, P9.4; also elsewhere on the board
+5V: P9.5, P9.6
/Cape EEProm/SCL2: P9.19; also elsewhere on the board
/Cape EEProm/SDA2: P9.20; also elsewhere on the board
/PCA9685 Driver/OE: P8.12; also elsewhere on the board
/PCA9685 Driver/SCL: P9.17; also elsewhere on the board
/PCA9685 Driver/SDA: P9.18; also elsewhere on the board
GND: P8.1, P8.2, P9.1, P9.2, P9.43, P9.44, P9.45, P9.46; also elsewhere on the board
SYS_5V: P9.7, P9.8

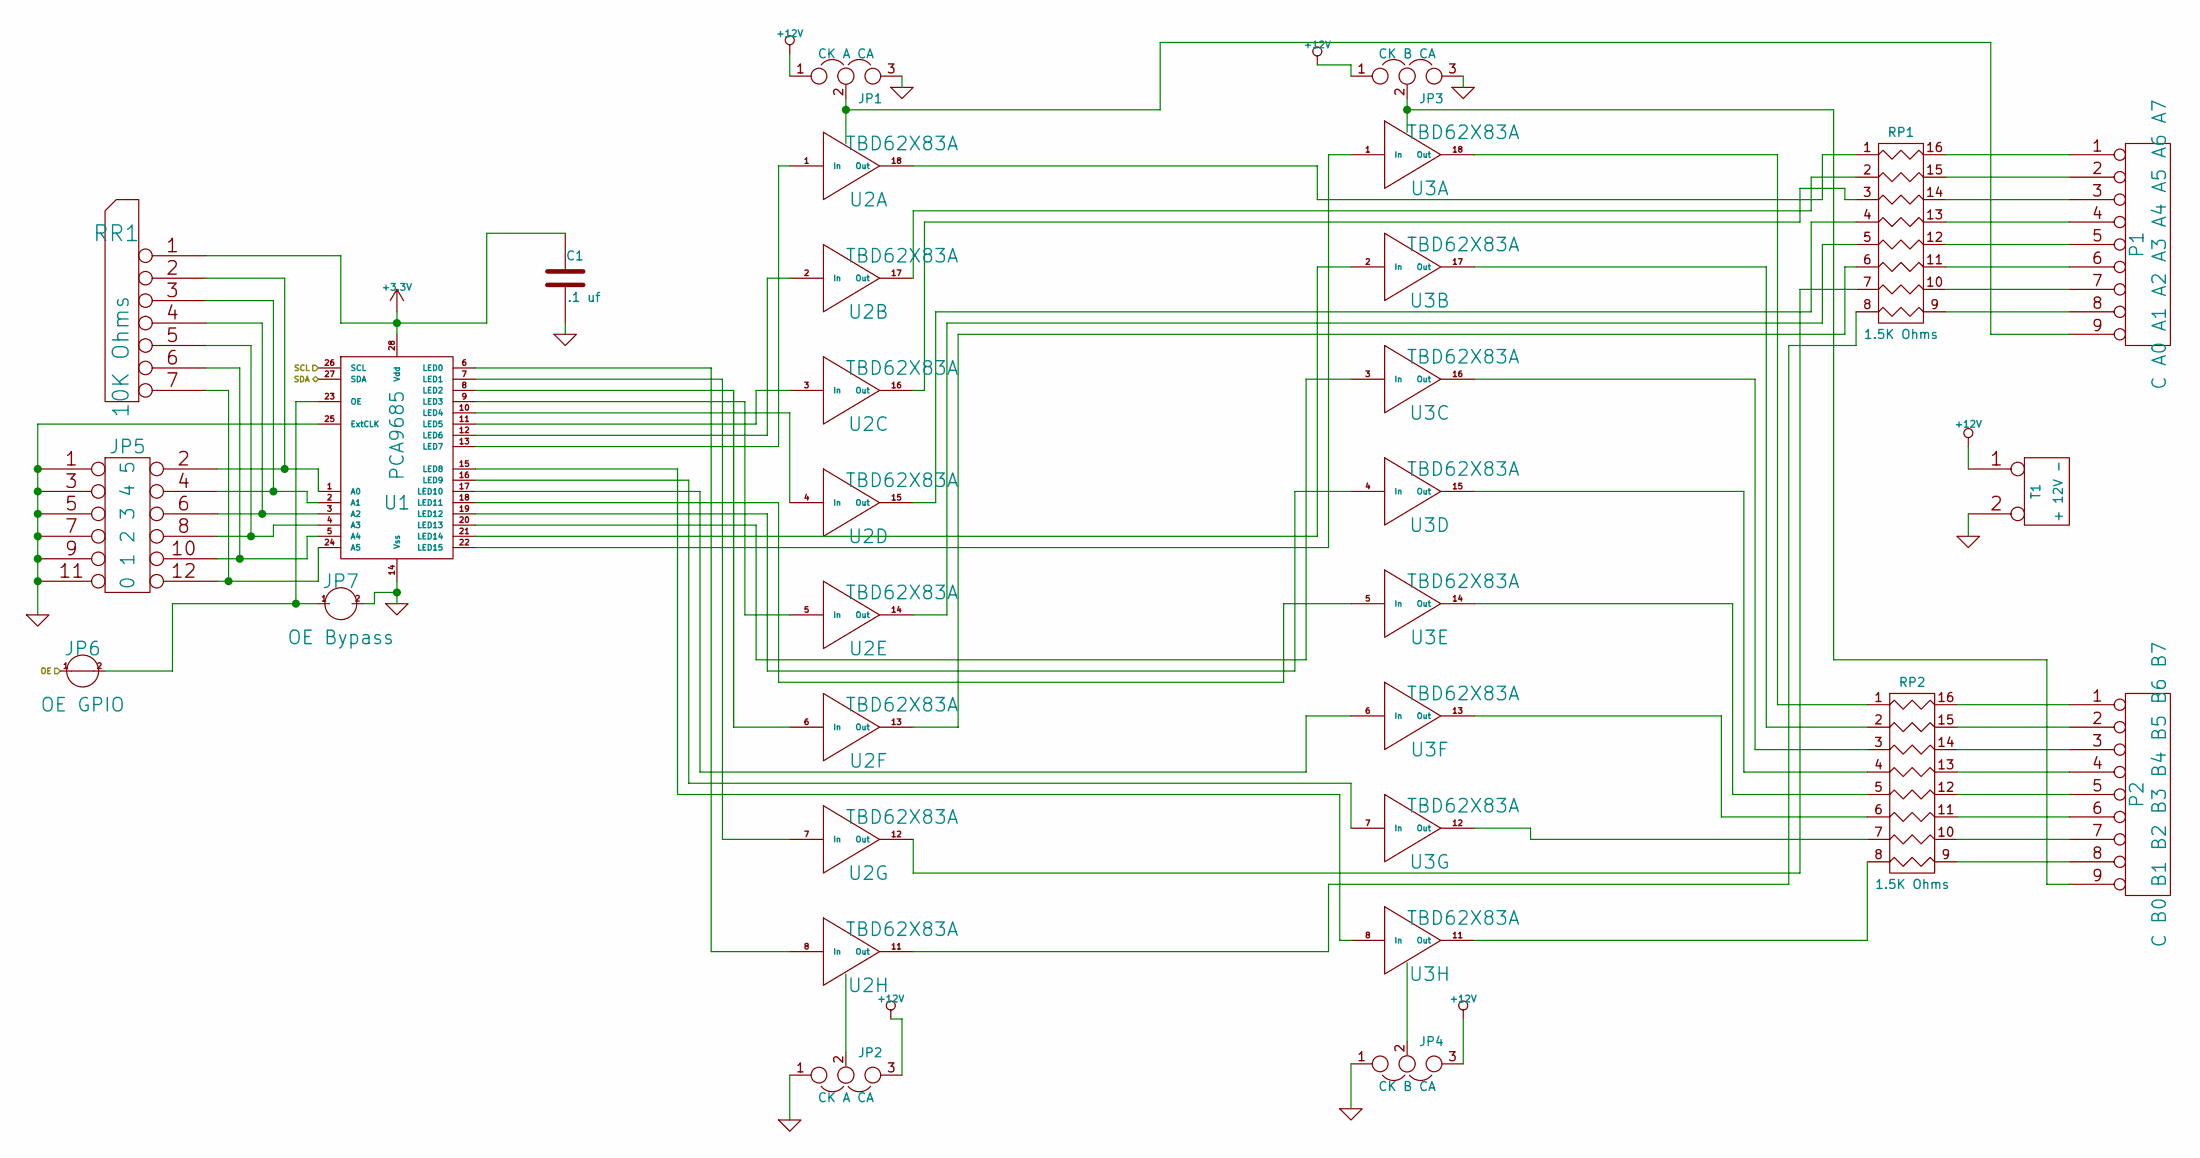
[picture p121: schematic PCA9685Driver.sch]

Parts:
C1: .1 uf
JP1, JP2: CK A CA
JP3, JP4: CK B CA
JP5: 0 1 2 3 4 5
JP6: OE GPIO
JP7: OE Bypass
P1: C A0 A1 A2 A3 A4 A5 A6 A7
P2: C B0 B1 B2 B3 B4 B5 B6 B7
RP1, RP2: 1.5K Ohms
RR1: 10K Ohms
T1: + 12V -
U1: PCA9685
U2, U3: TBD62X83A

Connections:
+3.3V: C1.1, RR1.1 (COM), U1.28 (Vdd); also elsewhere on the board
+12V: JP1.1, JP2.3, JP3.1, JP4.3, T1.1
/PCA9685 Driver/OE: JP6.1; also elsewhere on the board
/PCA9685 Driver/SCL: U1.26 (SCL); also elsewhere on the board
/PCA9685 Driver/SDA: U1.27 (SDA); also elsewhere on the board
GND: C1.2, JP1.3, JP2.1, JP3.3, JP4.1, JP5.1, JP5.3, JP5.5, JP5.7, JP5.9, JP5.11, JP7.2, T1.2 (PM), U1.14 (Vss), U1.25 (ExtCLK); also elsewhere on the board
unnamed: RP2.8, U3.11 (Out)
unnamed: RP2.7, U3.12 (Out)
unnamed: RP2.6, U3.13 (Out)
unnamed: RP2.5, U3.14 (Out)
unnamed: RP2.4, U3.15 (Out)
unnamed: JP5.2, RR1.2, U1.1 (A0)
unnamed: JP5.4, RR1.3, U1.2 (A1)
unnamed: JP5.10, RR1.6, U1.5 (A4)
unnamed: JP5.8, RR1.5, U1.4 (A3)
unnamed: JP5.12, RR1.7, U1.24 (A5)
unnamed: RP1.4, U2.15 (Out)
unnamed: RP1.3, U2.16 (Out)
unnamed: RP1.2, U2.17 (Out)
unnamed: RP1.1, U2.18 (Out)
unnamed: P2.8, RP2.9 (R8)
unnamed: P2.7, RP2.10 (R7)
unnamed: P2.6, RP2.11 (R6)
unnamed: P2.5, RP2.12 (R5)
unnamed: P2.4, RP2.13 (R4)
unnamed: RP2.3, U3.16 (Out)
unnamed: RP2.2, U3.17 (Out)
unnamed: RP2.1, U3.18 (Out)
unnamed: RP1.8, U2.11 (Out)
unnamed: RP1.7, U2.12 (Out)
unnamed: RP1.6, U2.13 (Out)
unnamed: RP1.5, U2.14 (Out)
unnamed: U1.19 (LED12), U3.4 (In)
unnamed: U1.11 (LED5), U2.3 (In)
unnamed: U1.8 (LED2), U2.6 (In)
unnamed: U1.10 (LED4), U2.4 (In)
unnamed: U1.21 (LED14), U3.2 (In)
unnamed: U1.12 (LED6), U2.2 (In)
unnamed: U1.17 (LED10), U3.6 (In)
unnamed: U1.9 (LED3), U2.5 (In)
unnamed: U1.22 (LED15), U3.1 (In)
unnamed: JP6.2, JP7.1, U1.23 (OE)
unnamed: JP5.6, RR1.4, U1.3 (A2)
unnamed: JP1.2, P1.9, U2.10 (OC)
unnamed: JP2.2, U2.9 (IC)
unnamed: P2.1, RP2.16 (R1)
unnamed: JP3.2, P2.9, U3.10 (OC)
unnamed: P2.3, RP2.14 (R3)
unnamed: P2.2, RP2.15 (R2)
unnamed: JP4.2, U3.9 (IC)
unnamed: U1.16 (LED9), U3.7 (In)
unnamed: U1.18 (LED11), U3.5 (In)
unnamed: U1.20 (LED13), U3.3 (In)
unnamed: P1.1, RP1.16 (R1)
unnamed: P1.2, RP1.15 (R2)
unnamed: P1.3, RP1.14 (R3)
unnamed: P1.4, RP1.13 (R4)
unnamed: P1.5, RP1.12 (R5)
unnamed: P1.6, RP1.11 (R6)
unnamed: P1.7, RP1.10 (R7)
unnamed: P1.8, RP1.9 (R8)
unnamed: U1.15 (LED8), U3.8 (In)
unnamed: U1.7 (LED1), U2.7 (In)
unnamed: U1.13 (LED7), U2.1 (In)
unnamed: U1.6 (LED0), U2.8 (In)

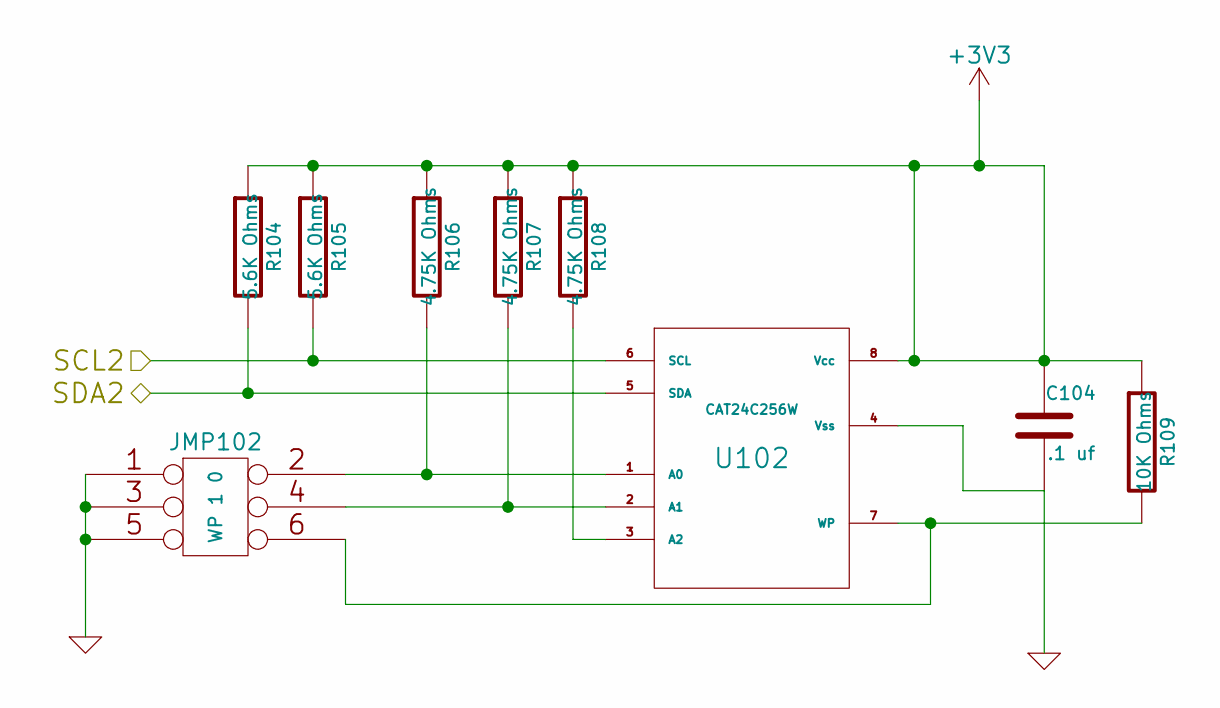
[picture p122: schematic CapeEEPROM.sch]

Parts:
C104: .1 uf
JMP102: WP 1 0
R104, R105: 5.6K Ohms
R106, R107, R108: 4.75K Ohms
R109: 10K Ohms
U102: CAT24C256W

Connections:
+3.3V: C104.1, R104.1, R105.1, R106.1, R107.1, R108.1, R109.1, U102.8 (Vcc); also elsewhere on the board
/Cape EEProm/SCL2: R105.2, U102.6 (SCL); also elsewhere on the board
/Cape EEProm/SDA2: R104.2, U102.5 (SDA); also elsewhere on the board
GND: C104.2, JMP102.1, JMP102.3, JMP102.5, U102.4 (Vss); also elsewhere on the board
unnamed: R108.2, U102.3 (A2)
unnamed: JMP102.4, R107.2, U102.2 (A1)
unnamed: JMP102.2, R106.2, U102.1 (A0)
unnamed: JMP102.6, R109.2, U102.7 (WP)

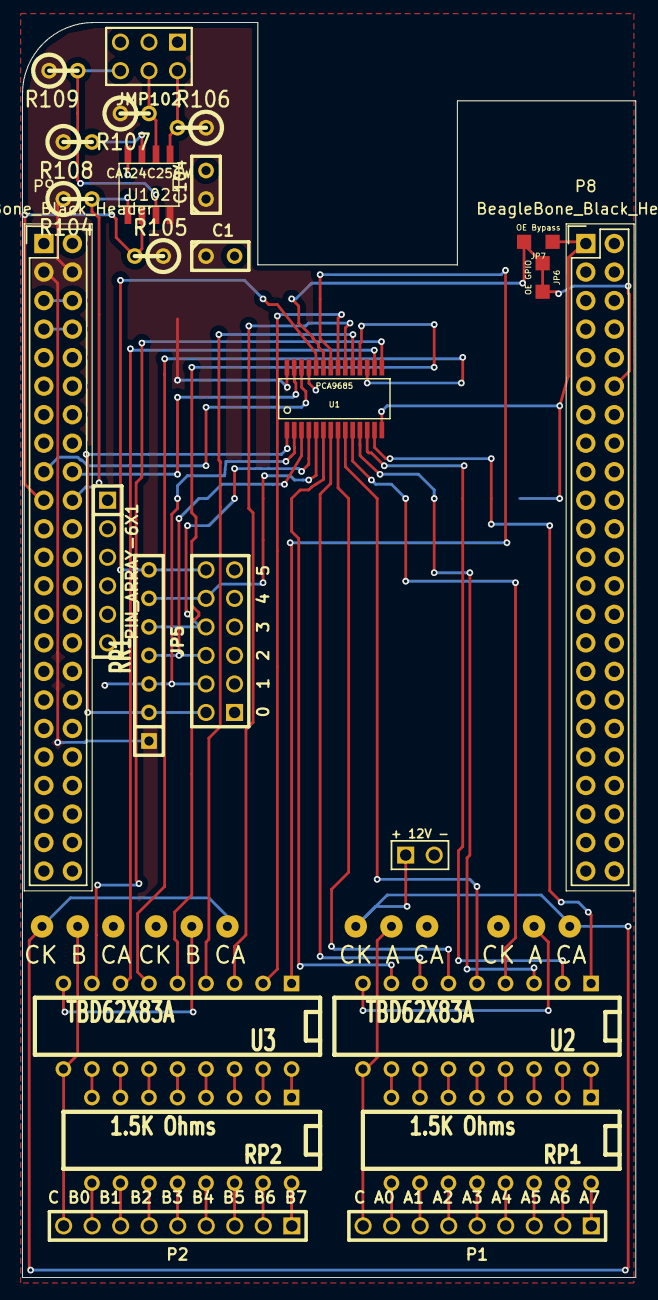
[picture p123: board 16PWMLedDriverCape.kicad_pcb from above]

Board: 2 copper layers, 54.6 x 111.8 mm, 29 parts (0 on the bottom side), 73 nets.

Other parts of the board:
PIN_ARRAY-6X1: Val**; PIN_ARRAY-6X1
