RobertPHeller/RPi-RRCircuits/PocketBeagleQuadSMCSense/PocketBeagleQuadSMCSense.kicad_pcb

## KiCad design PocketBeagleQuadSMCSense/PocketBeagleQuadSMCSense.kicad_pcb (2019-07-23)

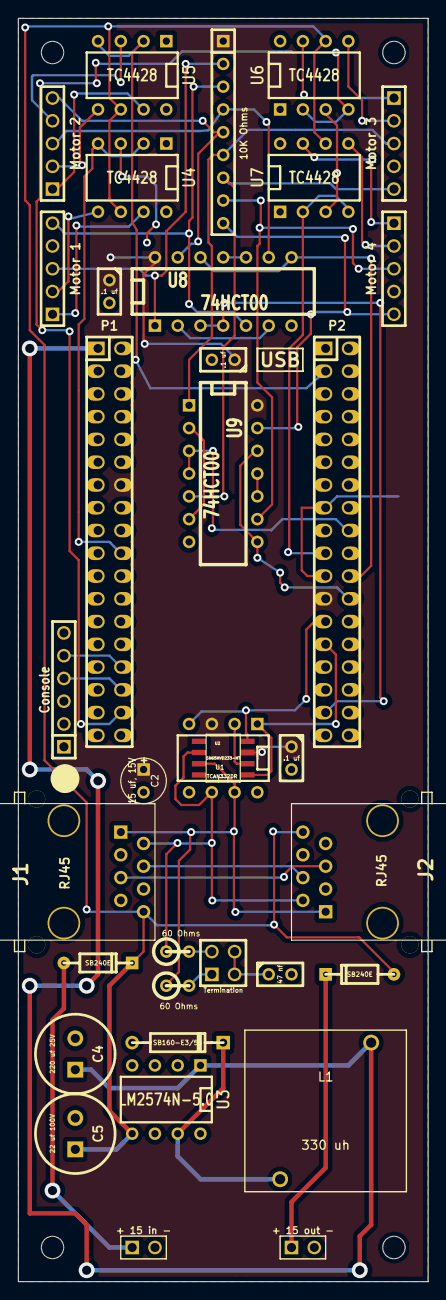
[picture p124: board PocketBeagleQuadSMCSense.kicad_pcb from above]

Board: 2 copper layers, 45.7 x 141.0 mm, 39 parts (0 on the bottom side), 46 nets.

Parts:
C1, C6, C7: .1 uf; C1
C2: 15 uf, 15V; C1V5
C3: 47 nf; C1
C4: 220 uf 25V; C1-3V8
C5: 22 uf 100V; C1-3V8
D1, D2: SB240E; DO-35
D3: SB160-E3/54; DO-41
J1, J2: RJ45; RJ45_8N-S
JMP1: Termination; PIN_ARRAY_2X2
L1: 330 uh; PE-LowProfile
MH: MountingHole_2-5mm_RevA_Date21Jun2010
MH#2, MH#3, MH#4: MountingHole_2-5mm_RevA_Date21Jun2010
P1: POCKETBEAGLE-P1; pin_socket_18x2
P2: POCKETBEAGLE-P2; pin_socket_18x2
P101: Console; PIN_ARRAY-6X1
R1, R2: 60 Ohms; R1
RR1: 10K Ohms; SIL-9
T1: + 15 in -; ScrewTerm2.54-2
T2: + 15 out -; ScrewTerm2.54-2
T3: Motor 1; ScrewTerm_2.54-5
T4: Motor 2; ScrewTerm_2.54-5
T5: Motor 3; ScrewTerm_2.54-5
T6: Motor 4; ScrewTerm_2.54-5
U1: TCAN332DR; SOIC-8_N
U2: SN65HVD233-HT; DIP-8__300
U3: LM2574N-5.0; DIP-8__300
U4, U5, U6, U7: TC4428; DIP-8__300
U8, U9: 74HCT00; DIP-14__300

Connections:
+3.3V: C1.1, C2.1, C6.1, C7.1, P1.14, P2.23, RR1.1, U1.3, U2.3, U8.14, U9.14
+12V: C5.1, D1.2, D2.1, J1.8, J2.8, U3.5, U4.6, U5.6, U6.6, U7.6
/CAN1_RX: P2.25, U1.4, U2.4
/CAN1_TX: P2.27, U1.1, U2.1
/CANH: J1.1, J2.1, R1.1, U1.7, U2.7
/CANL: J1.2, J2.2, R2.1, U1.6, U2.6
/Power Supply/5V Out: C4.1, L1.1, P1.1, U3.1
/Quad SMC Sense/Motor1A: T3.1, U4.7
/Quad SMC Sense/Motor1B: T3.2, U4.5
/Quad SMC Sense/Motor2A: T4.1, U5.7
/Quad SMC Sense/Motor2B: T4.2, U5.5
/Quad SMC Sense/Motor3A: T5.1, U6.7
/Quad SMC Sense/Motor3B: T5.2, U6.5
/Quad SMC Sense/Motor4A: T6.1, U7.7
/Quad SMC Sense/Motor4B: T6.2, U7.5
/Quad SMC Sense/Motor 1: P1.20, U4.2, U4.4
/Quad SMC Sense/Motor 2: P2.3, U5.2, U5.4
/Quad SMC Sense/Motor 3: P1.34, U6.2, U6.4
/Quad SMC Sense/Motor 4: P2.19, U7.2, U7.4
/Quad SMC Sense/Sense1A: RR1.2, T3.3, U8.1
/Quad SMC Sense/Sense1B: RR1.3, T3.5, U8.5
/Quad SMC Sense/Sense2A: RR1.4, T4.3, U8.9
/Quad SMC Sense/Sense2B: RR1.5, T4.5, U8.13
/Quad SMC Sense/Sense3A: RR1.6, T5.3, U9.1
/Quad SMC Sense/Sense3B: RR1.7, T5.5, U9.5
/Quad SMC Sense/Sense4A: RR1.8, T6.3, U9.9
/Quad SMC Sense/Sense4B: RR1.9, T6.5, U9.13
/Quad SMC Sense/Sense 1: P2.33, U8.3, U8.4
/Quad SMC Sense/Sense 2: P2.22, U8.8, U8.12
/Quad SMC Sense/Sense 3: P2.18, U9.3, U9.4
/Quad SMC Sense/Sense 4: P2.24, U9.8, U9.12
GND: C1.2, C2.2, C3.2, C4.2, C5.2, C6.2, C7.2, D3.1, J1.3, J1.6, J1.7, J2.3, J2.6, J2.7, P1.15, P1.16, P1.22, P2.15, P2.21, P101.1, T1.2, T2.2, T3.4, T4.4, T5.4, T6.4, U1.2, U2.2, U2.5, U2.8, U3.2, U3.3, U3.4, U4.3, U5.3, U6.3, U7.3, U8.7, U9.7
unnamed: P1.32, P101.4
unnamed: J1.5, J2.5
unnamed: J1.4, J2.4
unnamed: JMP1.1, R1.2
unnamed: JMP1.2, R2.2
unnamed: C3.1, JMP1.3, JMP1.4
unnamed: P1.30, P101.5
unnamed: D2.2, T2.1
unnamed: D1.1, T1.1
unnamed: D3.2, L1.2, U3.7
unnamed: U9.10, U9.11
unnamed: U9.2, U9.6
unnamed: U8.2, U8.6
unnamed: U8.10, U8.11
