RobertPHeller/RPi-RRCircuits/PocketBeagleQuadOCDect/PocketBeagleQuadOCDect.kicad_pcb

## KiCad design PocketBeagleQuadOCDect/PocketBeagleQuadOCDect.kicad_pcb (2019-07-08)

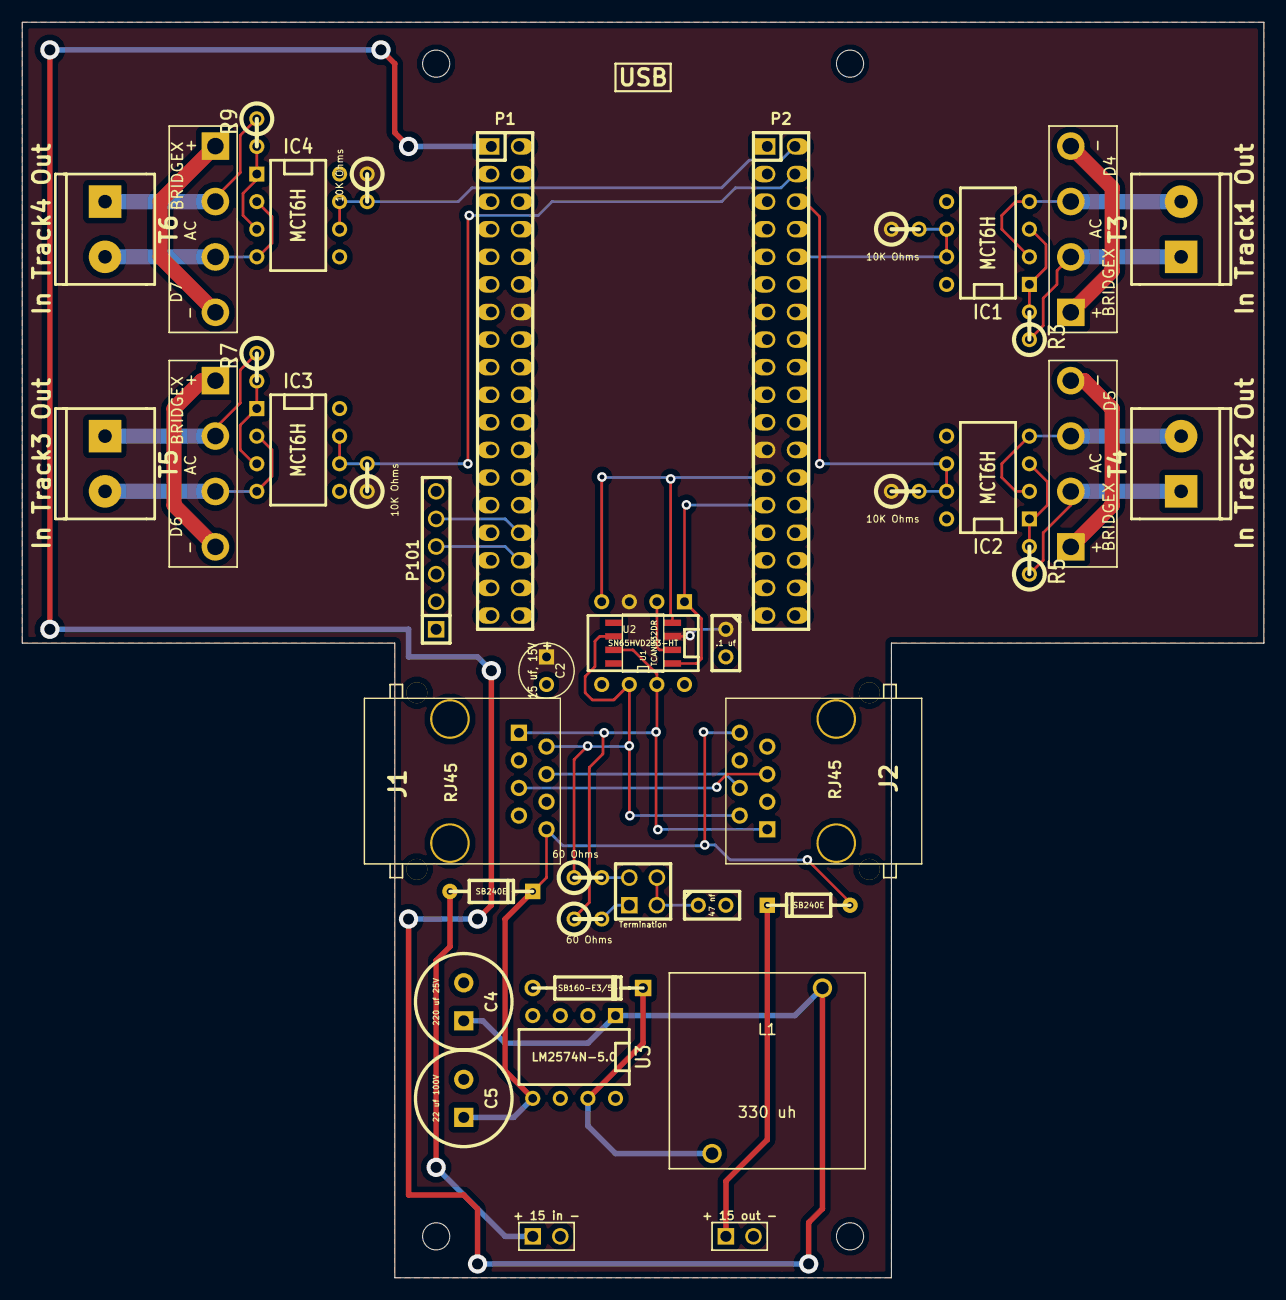
[picture p125: board PocketBeagleQuadOCDect.kicad_pcb from above]

Board: 2 copper layers, 114.3 x 115.6 mm, 46 parts (0 on the bottom side), 38 nets.

Parts:
C1: .1 uf; C1
C2: 15 uf, 15V; C1V5
C3: 47 nf; C1
C4: 220 uf 25V; C1-3V8
C5: 22 uf 100V; C1-3V8
D1, D2: SB240E; DO-35
D3: SB160-E3/54; DO-41
D4, D5, D6, D7: BRIDGEX; KBL
IC1, IC2, IC3, IC4: MCT6H; DIP-8__300
J1, J2: RJ45; RJ45_8N-S
JMP1: Termination; PIN_ARRAY_2X2
L1: 330 uh; PE-LowProfile
MH: MountingHole_2-5mm_RevA_Date21Jun2010
MH#2, MH#3, MH#4: MountingHole_2-5mm_RevA_Date21Jun2010
P1: POCKETBEAGLE-P1; pin_socket_18x2
P2: POCKETBEAGLE-P2; pin_socket_18x2
P101: Console; PIN_ARRAY-6X1
R1, R2: 60 Ohms; R1
R3, R5, R7, R9: 10 Ohms; R1
R4, R6, R8, R10: 10K Ohms; R1
T1: + 15 in -; ScrewTerm2.54-2
T2: + 15 out -; ScrewTerm2.54-2
T3: In Track1 Out; mors_2p
T4: In Track2 Out; mors_2p
T5: In Track3 Out; mors_2p
T6: In Track4 Out; mors_2p
U1: TCAN332DR; SOIC-8_N
U2: SN65HVD233-HT; DIP-8__300
U3: LM2574N-5.0; DIP-8__300

Connections:
+3.3V: C1.1, C2.1, P1.14, P2.23, R4.1, R6.1, R8.1, R10.1, U1.3, U2.3
/CAN1_RX: P2.25, U1.4, U2.4
/CAN1_TX: P2.27, U1.1, U2.1
/CANH: J1.1, J2.1, R1.1, U1.7, U2.7
/CANL: J1.2, J2.2, R2.1, U1.6, U2.6
/Occupancy Detector 1/OD1: IC1.6, IC1.7, P2.10, R4.2
/Occupancy Detector 2/OD2: IC2.6, IC2.7, P2.6, R6.2
/Occupancy Detector 3/OD3: IC3.6, IC3.7, P2.4, R8.2
/Occupancy Detector 4/OD4: IC4.6, IC4.7, P2.2, R10.2
/Power Supply/5V Out: C4.1, L1.1, P1.1, U3.1
/Power Supply/12-15 Volt input: C5.1, D1.2, D2.1, J1.8, J2.8, U3.5
GND: C1.2, C2.2, C3.2, C4.2, C5.2, D3.1, IC1.5, IC1.8, IC2.5, IC2.8, IC3.5, IC3.8, IC4.5, IC4.8, J1.3, J1.6, J1.7, J2.3, J2.6, J2.7, P1.15, P1.16, P1.22, P2.15, P2.21, P101.1, T1.2, T2.2, U1.2, U2.2, U2.5, U2.8, U3.2, U3.3, U3.4
unnamed: J1.5, J2.5
unnamed: J1.4, J2.4
unnamed: P1.30, P101.5
unnamed: P1.32, P101.4
unnamed: JMP1.2, R2.2
unnamed: C3.1, JMP1.3, JMP1.4
unnamed: JMP1.1, R1.2
unnamed: D2.2, T2.1
unnamed: D1.1, T1.1
unnamed: D5.2, R5.1, T4.1
unnamed: D5.1, D5.4
unnamed: IC2.1, IC2.3, R5.2
unnamed: D5.3, IC2.2, IC2.4, T4.2
unnamed: D3.2, L1.2, U3.7
unnamed: D7.2, R9.1, T6.1
unnamed: D7.1, D7.4
unnamed: IC4.1, IC4.3, R9.2
unnamed: D7.3, IC4.2, IC4.4, T6.2
unnamed: D6.3, IC3.2, IC3.4, T5.2
unnamed: IC3.1, IC3.3, R7.2
unnamed: D6.2, R7.1, T5.1
unnamed: D6.1, D6.4
unnamed: D4.2, R3.1, T3.1
unnamed: D4.1, D4.4
unnamed: IC1.1, IC1.3, R3.2
unnamed: D4.3, IC1.2, IC1.4, T3.2
