RobertPHeller/RPi-RRCircuits/PocketBeagle16LedDriver/PocketBeagle16LedDriver.kicad_pcb

## KiCad design PocketBeagle16LedDriver/PocketBeagle16LedDriver.kicad_pcb (2019-07-08)

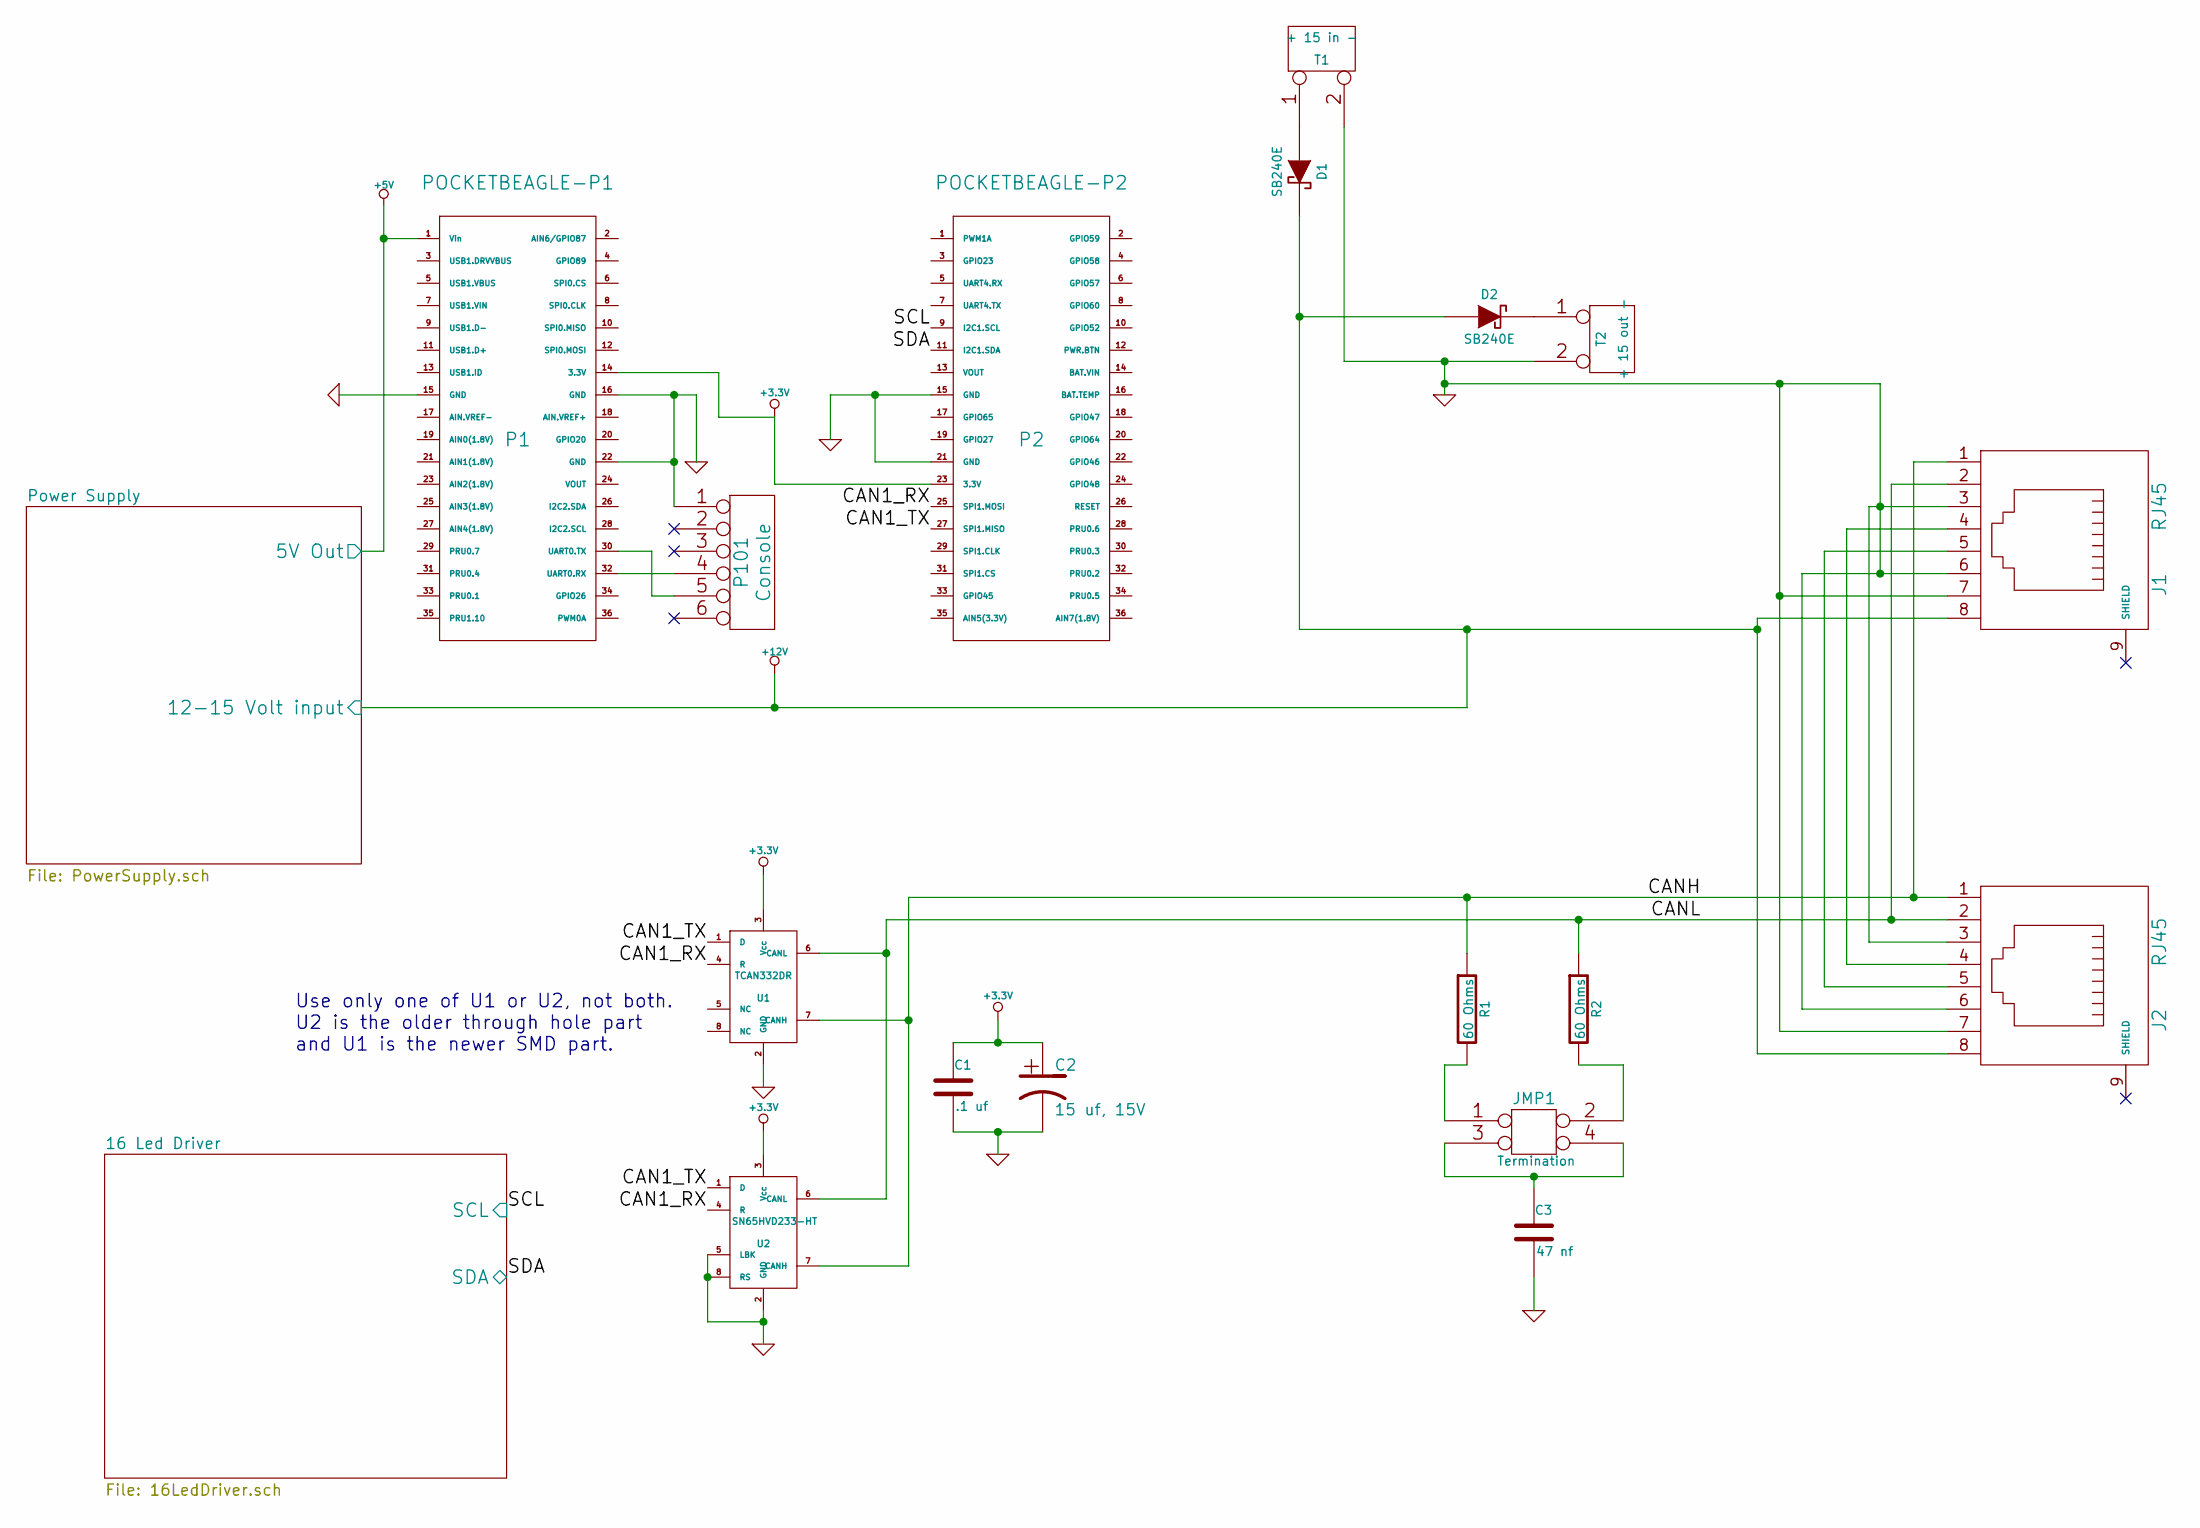
[picture p126: schematic PocketBeagle16LedDriver.sch]

Parts:
C1: .1 uf
C2: 15 uf, 15V
C3: 47 nf
D1, D2: SB240E
J1, J2: RJ45
JMP1: Termination
P1: POCKETBEAGLE-P1
P2: POCKETBEAGLE-P2
P101: Console
R1, R2: 60 Ohms
T1: + 15 in -
T2: + 15 out -
U1: TCAN332DR
U2: SN65HVD233-HT

Connections:
+3.3V: C1.1, C2.1, P1.14 (3.3V), P2.23 (3.3V), U1.3 (Vcc), U2.3 (Vcc); also elsewhere on the board
+5V: P1.1 (Vin); also elsewhere on the board
+12V: D1.2 (K), D2.1 (A), J1.8, J2.8; also elsewhere on the board
/16 Led Driver/SCL: P2.9 (I2C1.SCL); also elsewhere on the board
/16 Led Driver/SDA: P2.11 (I2C1.SDA); also elsewhere on the board
/CAN1_RX: P2.25 (SPI1.MOSI), U1.4 (R), U2.4 (R)
/CAN1_TX: P2.27 (SPI1.MISO), U1.1 (D), U2.1 (D)
/CANH: J1.1, J2.1, R1.1, U1.7 (CANH), U2.7 (CANH)
/CANL: J1.2, J2.2, R2.1, U1.6 (CANL), U2.6 (CANL)
GND: C1.2, C2.2, C3.2, J1.3, J1.6, J1.7, J2.3, J2.6, J2.7, P1.15 (GND), P1.16 (GND), P1.22 (GND), P2.15 (GND), P2.21 (GND), P101.1, T1.2 (PM), T2.2 (PM), U1.2 (GND), U2.2 (GND), U2.5 (LBK), U2.8 (RS); also elsewhere on the board
unnamed: J1.4, J2.4
unnamed: J1.5, J2.5
unnamed: P1.32 (UART0.RX), P101.4
unnamed: P1.30 (UART0.TX), P101.5
unnamed: JMP1.1, R1.2
unnamed: JMP1.2, R2.2
unnamed: C3.1, JMP1.3, JMP1.4
unnamed: D1.1 (A), T1.1
unnamed: D2.2 (K), T2.1

Notes on the sheet:
Use only one of U1 or U2, not both. U2 is the older through hole part and U1 is the newer SMD part.

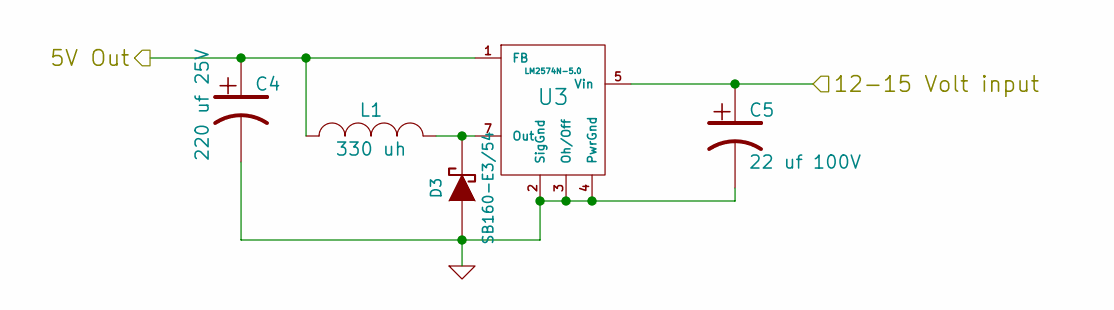
[picture p127: schematic PowerSupply.sch]

Parts:
C4: 220 uf 25V; C1-3V8; Part Number REA221M1EBK-0811P
C5: 22 uf 100V; C1-3V8; Part Number REA220M2ABK-0811P
D3: SB160-E3/54; DO-41; Part Number SB160-E3/54
L1: 330 uh; PE-LowProfile; Part Number PE-52627NL
U3: LM2574N-5.0

Connections:
+5V: C4.1, L1.1, U3.1 (FB); also elsewhere on the board
+12V: C5.1, U3.5 (Vin); also elsewhere on the board
GND: C4.2, C5.2, D3.1 (A), U3.2 (SigGnd), U3.3 (Oh/Off), U3.4 (PwrGnd); also elsewhere on the board
unnamed: D3.2 (K), L1.2, U3.7 (Out)

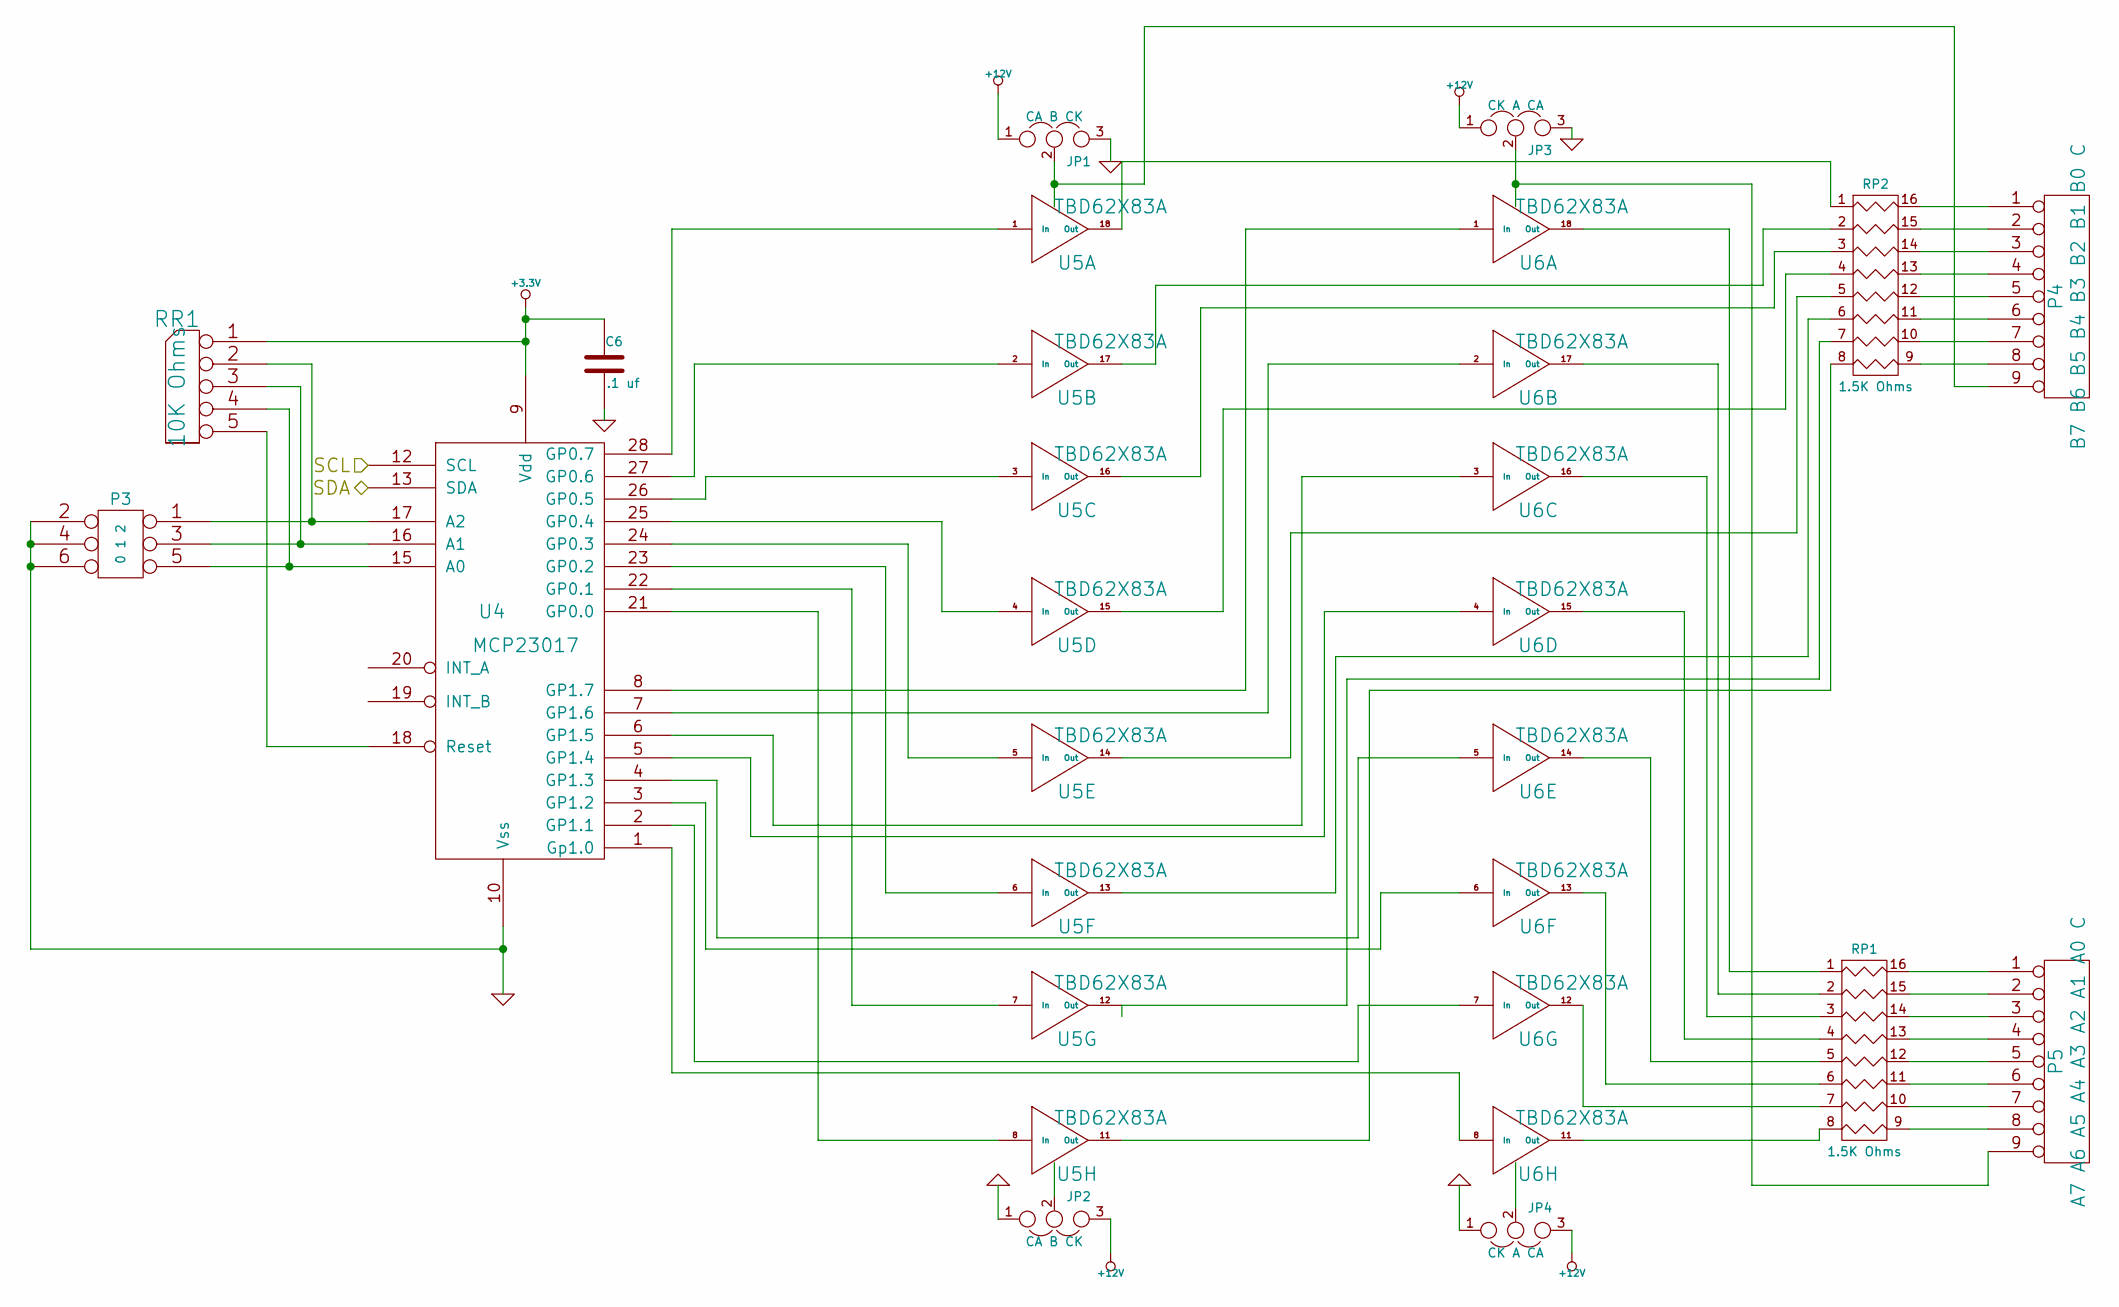
[picture p128: schematic 16LedDriver.sch]

Parts:
C6: .1 uf
JP1, JP2: CA B CK
JP3, JP4: CK A CA
P3: 0 1 2
P4: B7 B6 B5 B4 B3 B2 B1 B0 C
P5: A7 A6 A5 A4 A3 A2 A1 A0 C
RP1, RP2: 1.5K Ohms
RR1: 10K Ohms
U4: MCP23017
U5, U6: TBD62X83A

Connections:
+3.3V: C6.1, RR1.1 (COM), U4.9 (Vdd); also elsewhere on the board
+12V: JP1.1, JP2.3, JP3.1, JP4.3; also elsewhere on the board
/16 Led Driver/SCL: U4.12 (SCL); also elsewhere on the board
/16 Led Driver/SDA: U4.13 (SDA); also elsewhere on the board
GND: C6.2, JP1.3, JP2.1, JP3.3, JP4.1, P3.2, P3.4, P3.6, U4.10 (Vss); also elsewhere on the board
unnamed: U4.4 (GP1.3), U6.5 (In)
unnamed: U4.3 (GP1.2), U6.6 (In)
unnamed: U4.5 (GP1.4), U6.4 (In)
unnamed: U4.6 (GP1.5), U6.3 (In)
unnamed: RP2.3, U5.16 (Out)
unnamed: RP2.2, U5.17 (Out)
unnamed: RP2.1, U5.18 (Out)
unnamed: JP4.2, U6.9 (IC)
unnamed: JP2.2, U5.9 (IC)
unnamed: U4.1 (Gp1.0), U6.8 (In)
unnamed: U4.2 (GP1.1), U6.7 (In)
unnamed: U4.27 (GP0.6), U5.2 (In)
unnamed: U4.28 (GP0.7), U5.1 (In)
unnamed: U4.23 (GP0.2), U5.6 (In)
unnamed: U4.7 (GP1.6), U6.2 (In)
unnamed: U4.8 (GP1.7), U6.1 (In)
unnamed: U4.21 (GP0.0), U5.8 (In)
unnamed: U4.22 (GP0.1), U5.7 (In)
unnamed: U4.24 (GP0.3), U5.5 (In)
unnamed: U4.25 (GP0.4), U5.4 (In)
unnamed: U4.26 (GP0.5), U5.3 (In)
unnamed: P5.6, RP1.11 (R6)
unnamed: JP3.2, P5.9, U6.10 (OC)
unnamed: JP1.2, P4.9, U5.10 (OC)
unnamed: P5.8, RP1.9 (R8)
unnamed: P5.7, RP1.10 (R7)
unnamed: P5.5, RP1.12 (R5)
unnamed: P5.4, RP1.13 (R4)
unnamed: P5.3, RP1.14 (R3)
unnamed: P5.2, RP1.15 (R2)
unnamed: P5.1, RP1.16 (R1)
unnamed: P4.8, RP2.9 (R8)
unnamed: P4.7, RP2.10 (R7)
unnamed: P4.6, RP2.11 (R6)
unnamed: P4.5, RP2.12 (R5)
unnamed: P4.4, RP2.13 (R4)
unnamed: P4.3, RP2.14 (R3)
unnamed: RR1.5, U4.18 (Reset)
unnamed: P3.1, RR1.2, U4.17 (A2)
unnamed: P3.3, RR1.3, U4.16 (A1)
unnamed: P3.5, RR1.4, U4.15 (A0)
unnamed: P4.2, RP2.15 (R2)
unnamed: RP2.8, U5.11 (Out)
unnamed: RP2.7, U5.12 (Out)
unnamed: RP2.6, U5.13 (Out)
unnamed: RP1.8, U6.11 (Out)
unnamed: RP2.5, U5.14 (Out)
unnamed: RP2.4, U5.15 (Out)
unnamed: RP1.4, U6.15 (Out)
unnamed: P4.1, RP2.16 (R1)
unnamed: RP1.1, U6.18 (Out)
unnamed: RP1.2, U6.17 (Out)
unnamed: RP1.3, U6.16 (Out)
unnamed: RP1.5, U6.14 (Out)
unnamed: RP1.6, U6.13 (Out)
unnamed: RP1.7, U6.12 (Out)

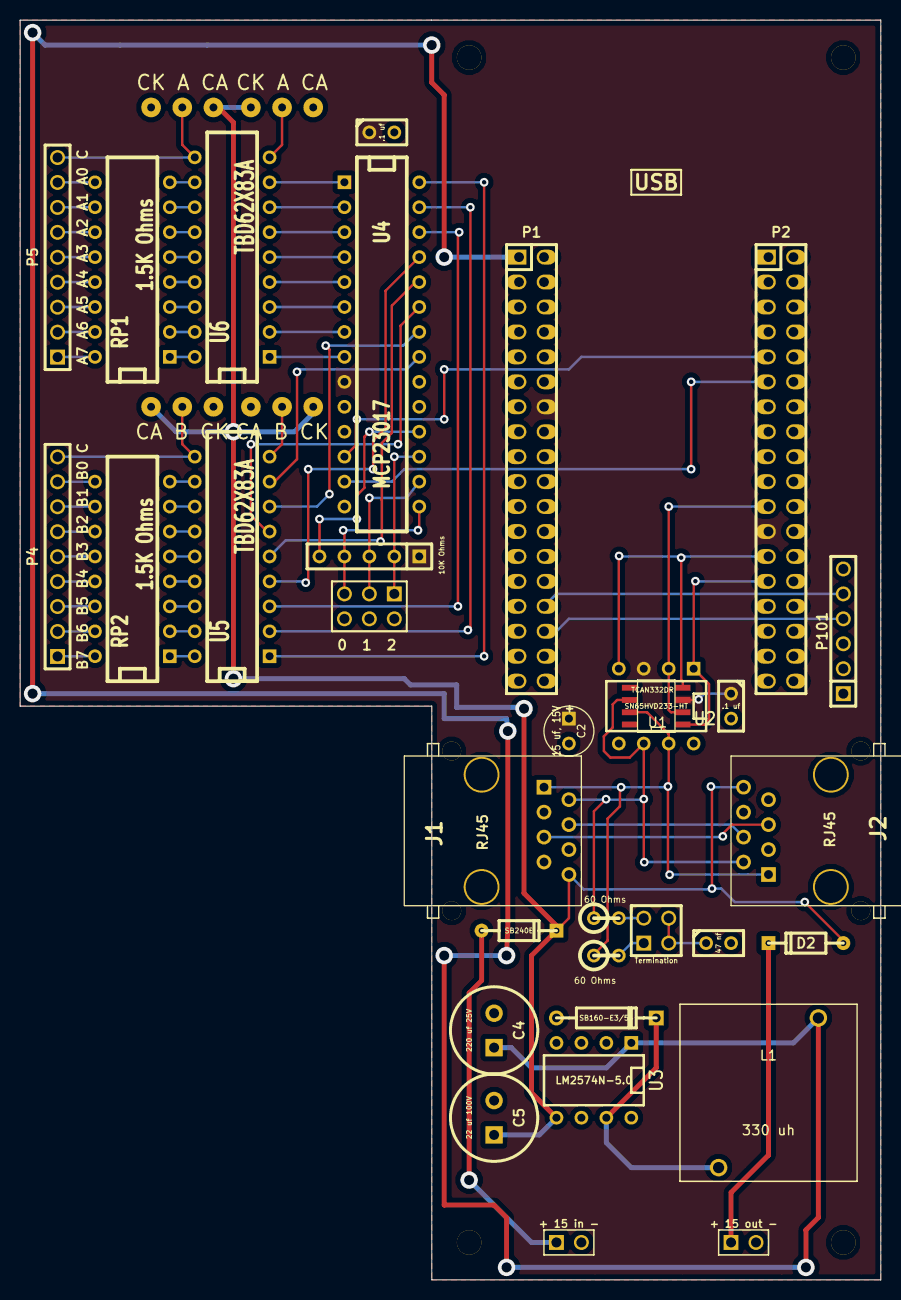
[picture p129: board PocketBeagle16LedDriver.kicad_pcb from above]

Board: 2 copper layers, 87.6 x 128.3 mm, 40 parts (0 on the bottom side), 76 nets.

Other parts of the board:
MH: MountingHole_2-5mm_RevA_Date21Jun2010
MH#2, MH#3, MH#4: MountingHole_2-5mm_RevA_Date21Jun2010
