RobertPHeller/RPi-RRCircuits/PocketBeagleMegaIOBaseBoard/PocketBeagleMegaIOBaseBoard.kicad_pcb

## KiCad design PocketBeagleMegaIOBaseBoard/PocketBeagleMegaIOBaseBoard.kicad_pcb (2019-07-08)

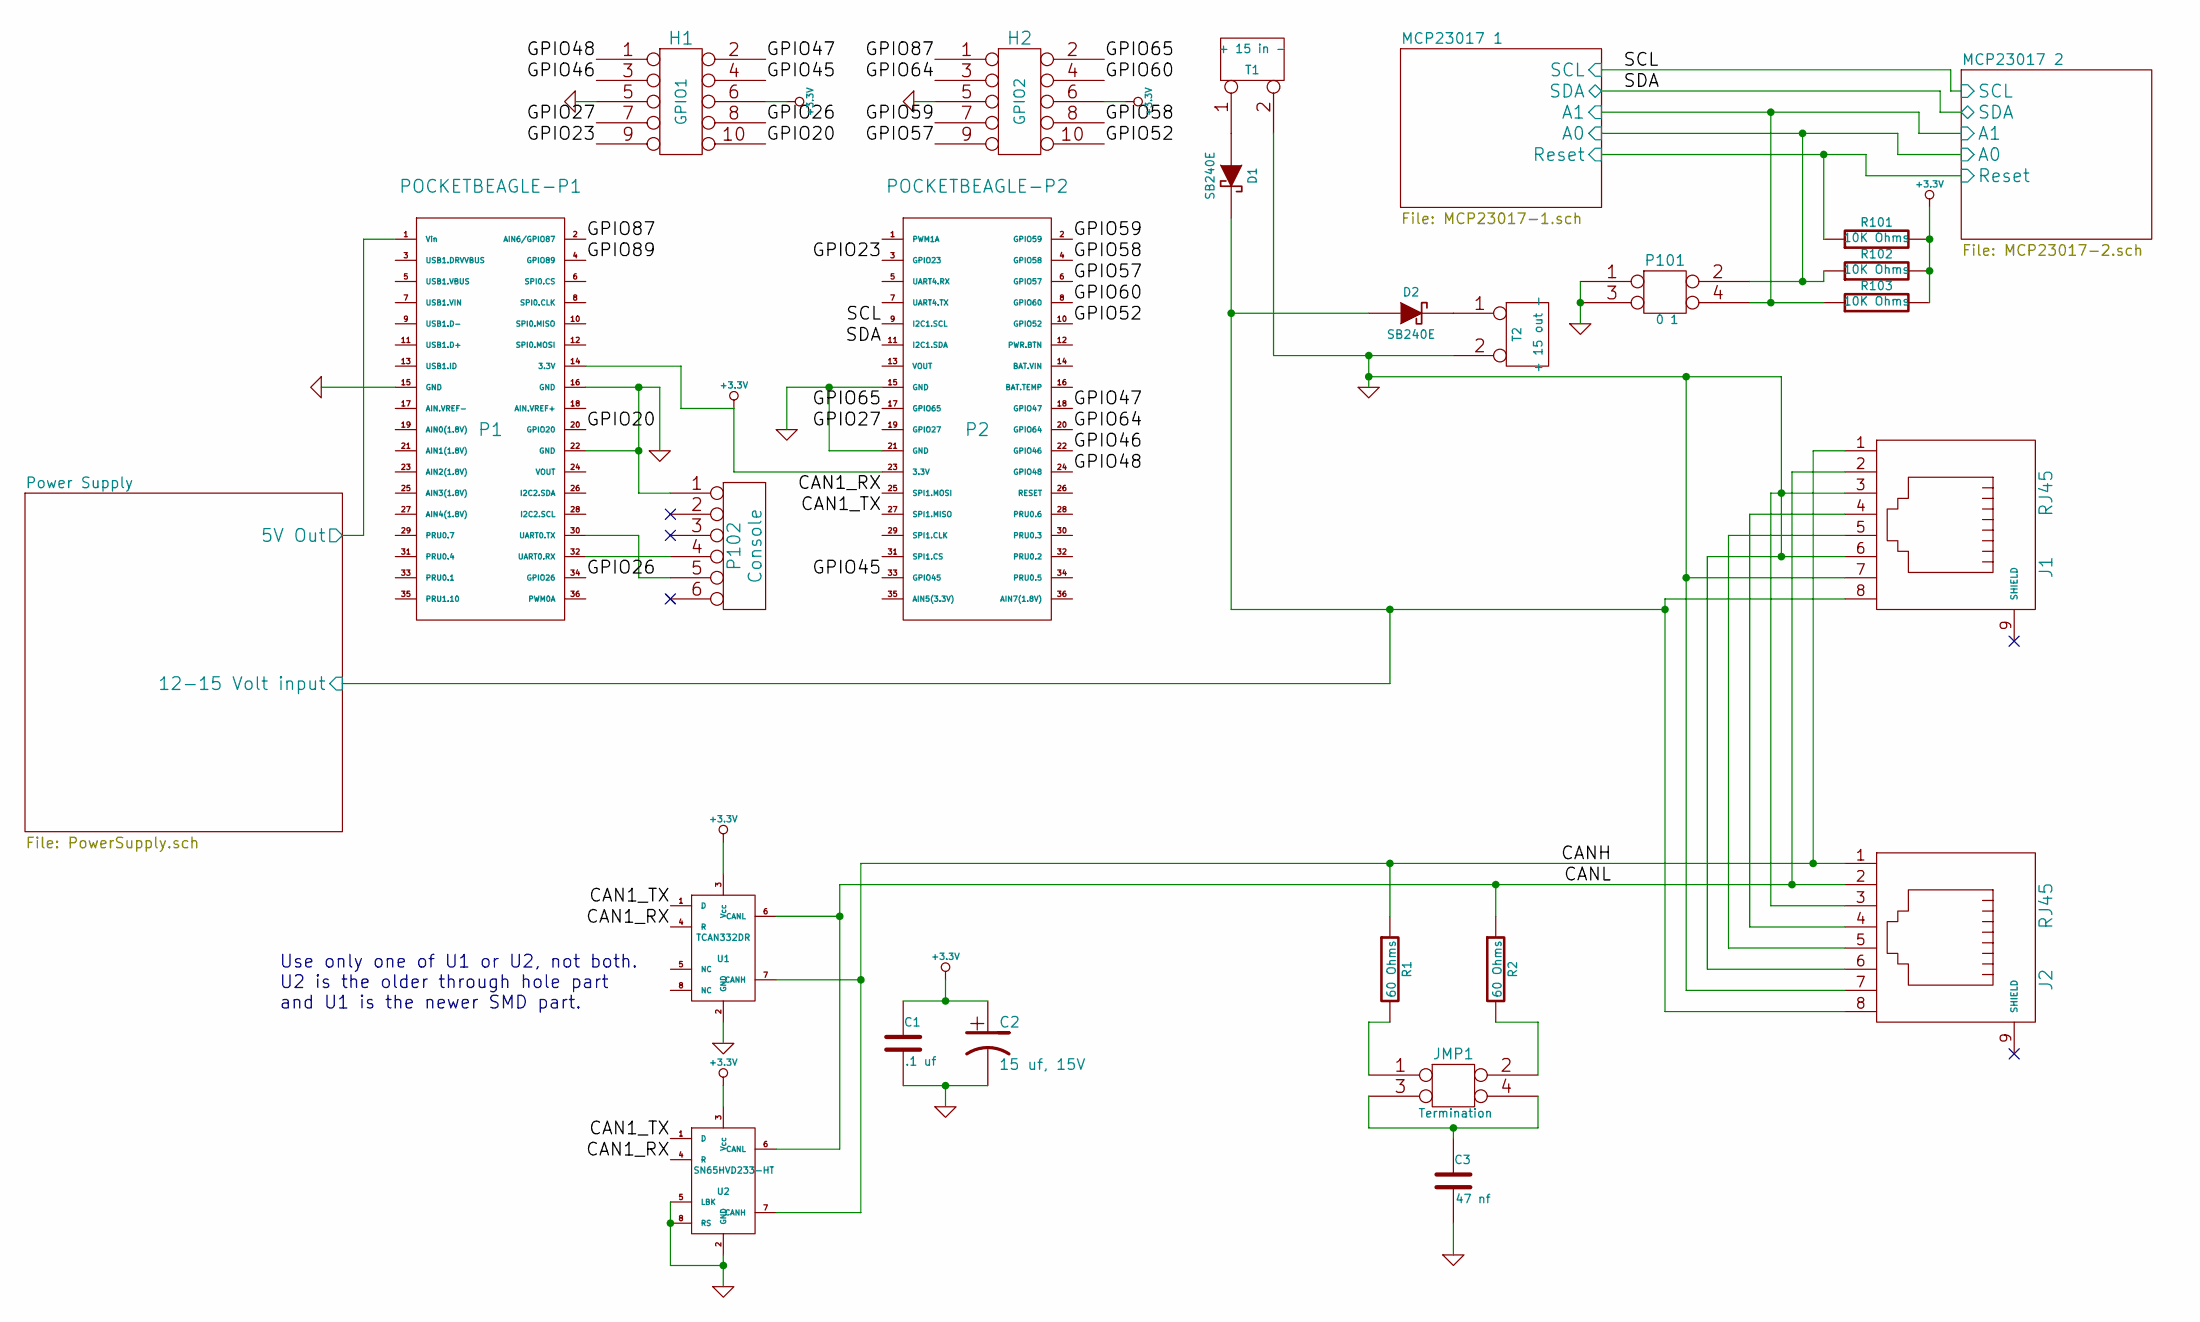
[picture p130: schematic PocketBeagleMegaIOBaseBoard.sch]

Parts:
C1: .1 uf
C2: 15 uf, 15V
C3: 47 nf
D1, D2: SB240E
H1: GPIO1
H2: GPIO2
J1, J2: RJ45
JMP1: Termination
P1: POCKETBEAGLE-P1
P2: POCKETBEAGLE-P2
P101: 0 1
P102: Console
R1, R2: 60 Ohms
R101, R102, R103: 10K Ohms
T1: + 15 in -
T2: + 15 out -
U1: TCAN332DR
U2: SN65HVD233-HT

Connections:
+3.3V: C1.1, C2.1, H1.6, H2.6, P1.14 (3.3V), P2.23 (3.3V), R101.2, R102.2, R103.2, U1.3 (Vcc), U2.3 (Vcc); also elsewhere on the board
/CAN1_RX: P2.25 (SPI1.MOSI), U1.4 (R), U2.4 (R)
/CAN1_TX: P2.27 (SPI1.MISO), U1.1 (D), U2.1 (D)
/CANH: J1.1, J2.1, R1.1, U1.7 (CANH), U2.7 (CANH)
/CANL: J1.2, J2.2, R2.1, U1.6 (CANL), U2.6 (CANL)
/GPIO20: H1.10, P1.20 (GPIO20)
/GPIO23: H1.9, P2.3 (GPIO23)
/GPIO26: H1.8, P1.34 (GPIO26)
/GPIO27: H1.7, P2.19 (GPIO27)
/GPIO45: H1.4, P2.33 (GPIO45)
/GPIO46: H1.3, P2.22 (GPIO46)
/GPIO47: H1.2, P2.18 (GPIO47)
/GPIO48: H1.1, P2.24 (GPIO48)
/GPIO52: H2.10, P2.10 (GPIO52)
/GPIO57: H2.9, P2.6 (GPIO57)
/GPIO58: H2.8, P2.4 (GPIO58)
/GPIO59: H2.7, P2.2 (GPIO59)
/GPIO60: H2.4, P2.8 (GPIO60)
/GPIO64: H2.3, P2.20 (GPIO64)
/GPIO65: H2.2, P2.17 (GPIO65)
/GPIO87: H2.1, P1.2 (AIN6/GPIO87)
/MCP23017 1/A0: P101.2, R102.1; also elsewhere on the board
/MCP23017 1/A1: P101.4, R103.1; also elsewhere on the board
/MCP23017 1/Reset: R101.1; also elsewhere on the board
/MCP23017 1/SCL: P2.9 (I2C1.SCL); also elsewhere on the board
/MCP23017 1/SDA: P2.11 (I2C1.SDA); also elsewhere on the board
/Power Supply/5V Out: P1.1 (Vin); also elsewhere on the board
/Power Supply/12-15 Volt input: D1.2 (K), D2.1 (A), J1.8, J2.8; also elsewhere on the board
GND: C1.2, C2.2, C3.2, H1.5, H2.5, J1.3, J1.6, J1.7, J2.3, J2.6, J2.7, P1.15 (GND), P1.16 (GND), P1.22 (GND), P2.15 (GND), P2.21 (GND), P101.1, P101.3, P102.1, T1.2 (PM), T2.2 (PM), U1.2 (GND), U2.2 (GND), U2.5 (LBK), U2.8 (RS); also elsewhere on the board
unnamed: JMP1.2, R2.2
unnamed: JMP1.1, R1.2
unnamed: C3.1, JMP1.3, JMP1.4
unnamed: P1.32 (UART0.RX), P102.4
unnamed: P1.30 (UART0.TX), P102.5
unnamed: J1.5, J2.5
unnamed: J1.4, J2.4
unnamed: D2.2 (K), T2.1
unnamed: D1.1 (A), T1.1

Notes on the sheet:
Use only one of U1 or U2, not both. U2 is the older through hole part and U1 is the newer SMD part.


Parts:
C4: 220 uf 25V; C1-3V8; Part Number REA221M1EBK-0811P
C5: 22 uf 100V; C1-3V8; Part Number REA220M2ABK-0811P
D3: SB160-E3/54; DO-41; Part Number SB160-E3/54
L1: 330 uh; PE-LowProfile; Part Number PE-52627NL
U3: LM2574N-5.0

Connections:
/Power Supply/5V Out: C4.1, L1.1, U3.1 (FB); also elsewhere on the board
/Power Supply/12-15 Volt input: C5.1, U3.5 (Vin); also elsewhere on the board
GND: C4.2, C5.2, D3.1 (A), U3.2 (SigGnd), U3.3 (Oh/Off), U3.4 (PwrGnd); also elsewhere on the board
unnamed: D3.2 (K), L1.2, U3.7 (Out)

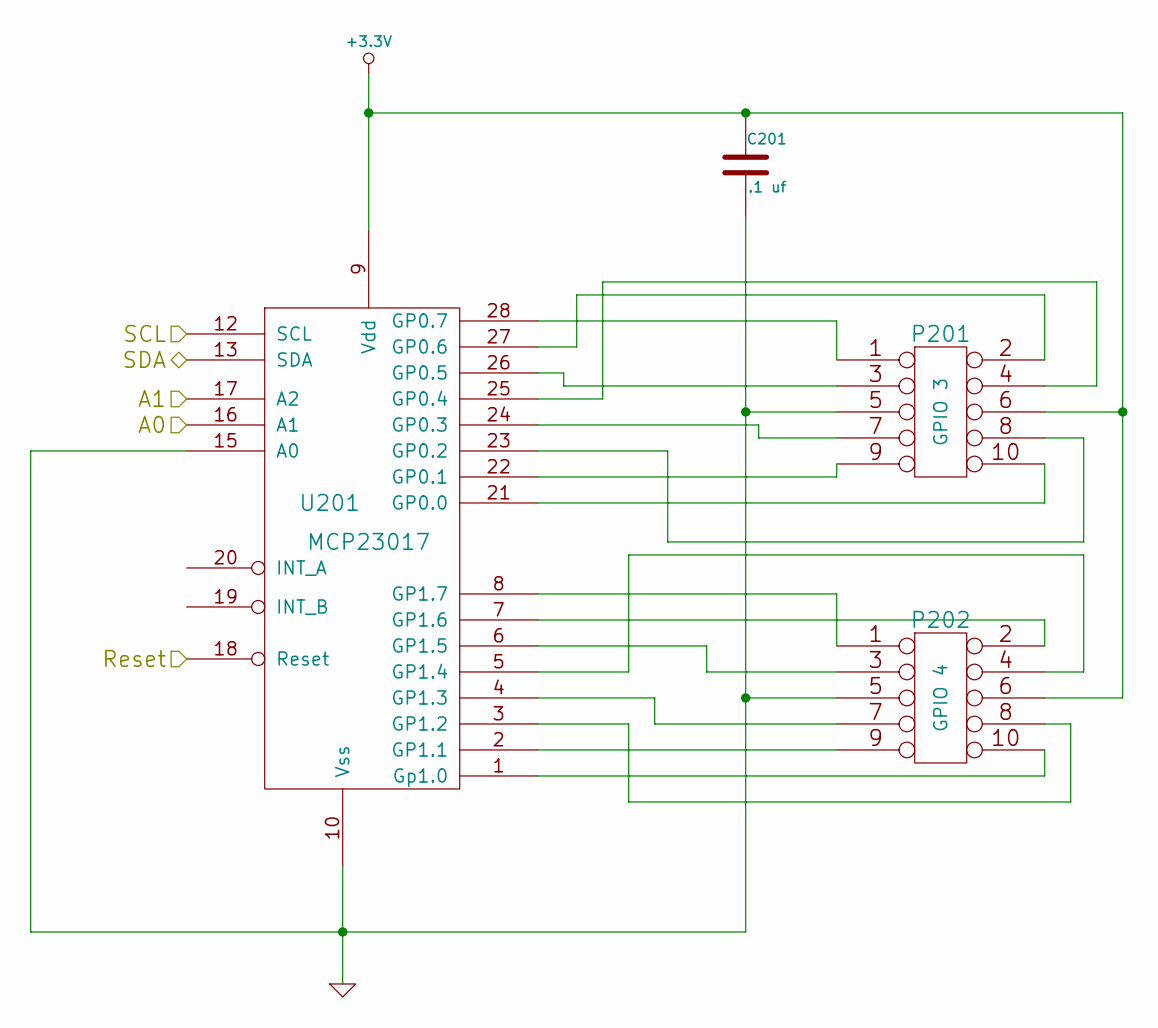
[picture p131: schematic MCP23017-1.sch, Mega I/O Hat]

Parts:
C201: .1 uf
P201: GPIO 3
P202: GPIO 4
U201: MCP23017

Connections:
+3.3V: C201.1, P201.6, P202.6, U201.9 (Vdd); also elsewhere on the board
/MCP23017 1/A0: U201.16 (A1); also elsewhere on the board
/MCP23017 1/A1: U201.17 (A2); also elsewhere on the board
/MCP23017 1/Reset: U201.18 (Reset); also elsewhere on the board
/MCP23017 1/SCL: U201.12 (SCL); also elsewhere on the board
/MCP23017 1/SDA: U201.13 (SDA); also elsewhere on the board
GND: C201.2, P201.5, P202.5, U201.10 (Vss), U201.15 (A0); also elsewhere on the board
unnamed: P201.4, U201.25 (GP0.4)
unnamed: P201.10, U201.21 (GP0.0)
unnamed: P201.9, U201.22 (GP0.1)
unnamed: P201.8, U201.23 (GP0.2)
unnamed: P201.7, U201.24 (GP0.3)
unnamed: P201.3, U201.26 (GP0.5)
unnamed: P201.2, U201.27 (GP0.6)
unnamed: P201.1, U201.28 (GP0.7)
unnamed: P202.4, U201.5 (GP1.4)
unnamed: P202.3, U201.6 (GP1.5)
unnamed: P202.1, U201.8 (GP1.7)
unnamed: P202.7, U201.4 (GP1.3)
unnamed: P202.8, U201.3 (GP1.2)
unnamed: P202.9, U201.2 (GP1.1)
unnamed: P202.10, U201.1 (Gp1.0)
unnamed: P202.2, U201.7 (GP1.6)

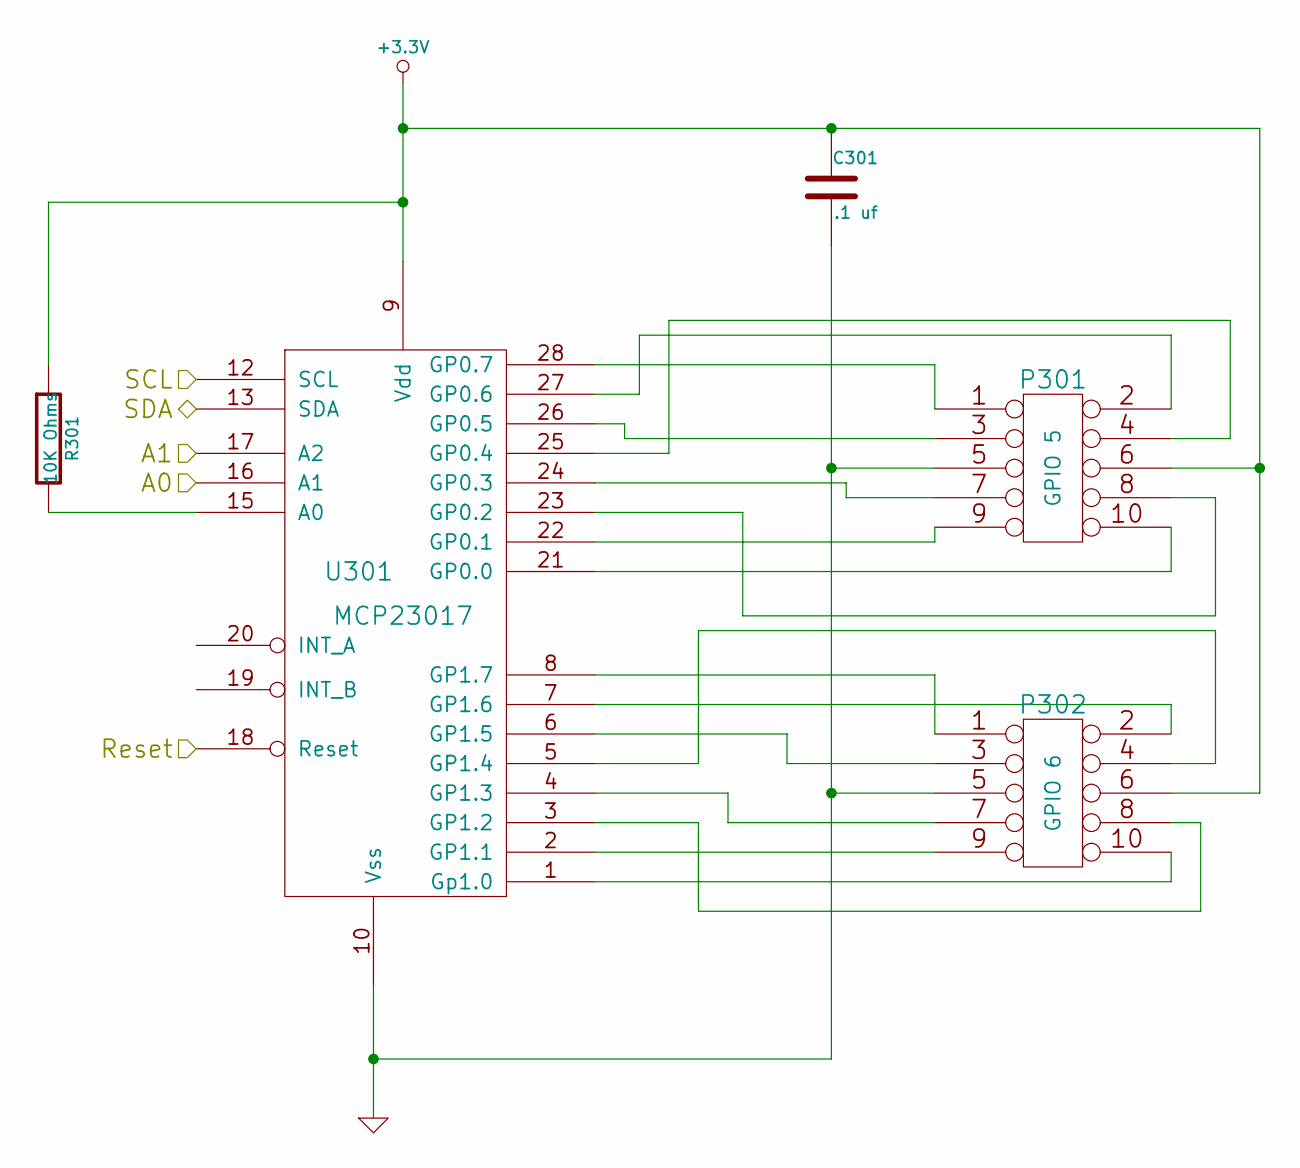
[picture p132: schematic MCP23017-2.sch, Mega I/O Hat]

Parts:
C301: .1 uf
P301: GPIO 5
P302: GPIO 6
R301: 10K Ohms
U301: MCP23017

Connections:
+3.3V: C301.1, P301.6, P302.6, R301.1, U301.9 (Vdd); also elsewhere on the board
/MCP23017 1/A0: U301.16 (A1); also elsewhere on the board
/MCP23017 1/A1: U301.17 (A2); also elsewhere on the board
/MCP23017 1/Reset: U301.18 (Reset); also elsewhere on the board
/MCP23017 1/SCL: U301.12 (SCL); also elsewhere on the board
/MCP23017 1/SDA: U301.13 (SDA); also elsewhere on the board
GND: C301.2, P301.5, P302.5, U301.10 (Vss); also elsewhere on the board
unnamed: P301.10, U301.21 (GP0.0)
unnamed: P301.9, U301.22 (GP0.1)
unnamed: P301.8, U301.23 (GP0.2)
unnamed: P301.7, U301.24 (GP0.3)
unnamed: P301.4, U301.25 (GP0.4)
unnamed: P301.3, U301.26 (GP0.5)
unnamed: P301.2, U301.27 (GP0.6)
unnamed: P301.1, U301.28 (GP0.7)
unnamed: R301.2, U301.15 (A0)
unnamed: P302.4, U301.5 (GP1.4)
unnamed: P302.3, U301.6 (GP1.5)
unnamed: P302.7, U301.4 (GP1.3)
unnamed: P302.8, U301.3 (GP1.2)
unnamed: P302.9, U301.2 (GP1.1)
unnamed: P302.10, U301.1 (Gp1.0)
unnamed: P302.2, U301.7 (GP1.6)
unnamed: P302.1, U301.8 (GP1.7)

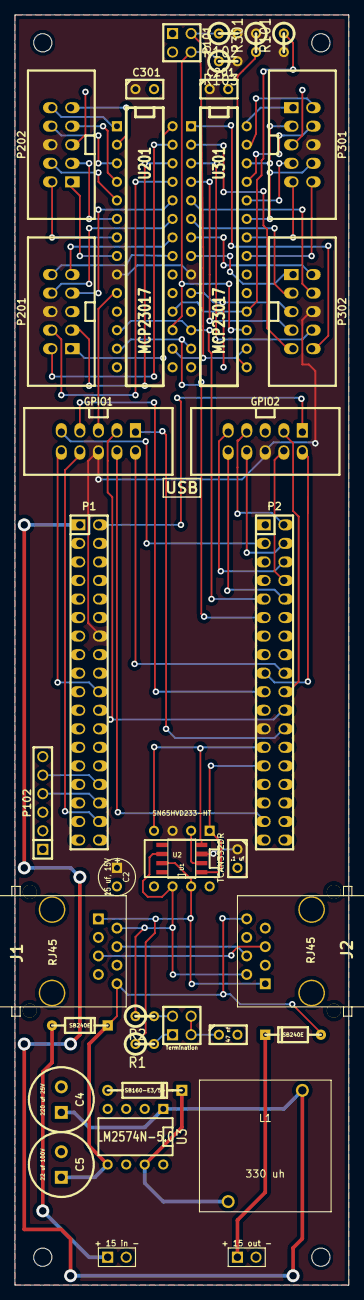
[picture p133: board PocketBeagleMegaIOBaseBoard.kicad_pcb from above]

Board: 2 copper layers, 45.7 x 174.0 mm, 41 parts (0 on the bottom side), 72 nets.

Other parts of the board:
MH: MountingHole_2-5mm_RevA_Date21Jun2010
MH#2, MH#3, MH#4: MountingHole_2-5mm_RevA_Date21Jun2010
