RobertPHeller/RPi-RRCircuits/16DriverOutputCape/16DriverOutputCape.kicad_pcb

## KiCad design 16DriverOutputCape/16DriverOutputCape.kicad_pcb (2019-07-04)

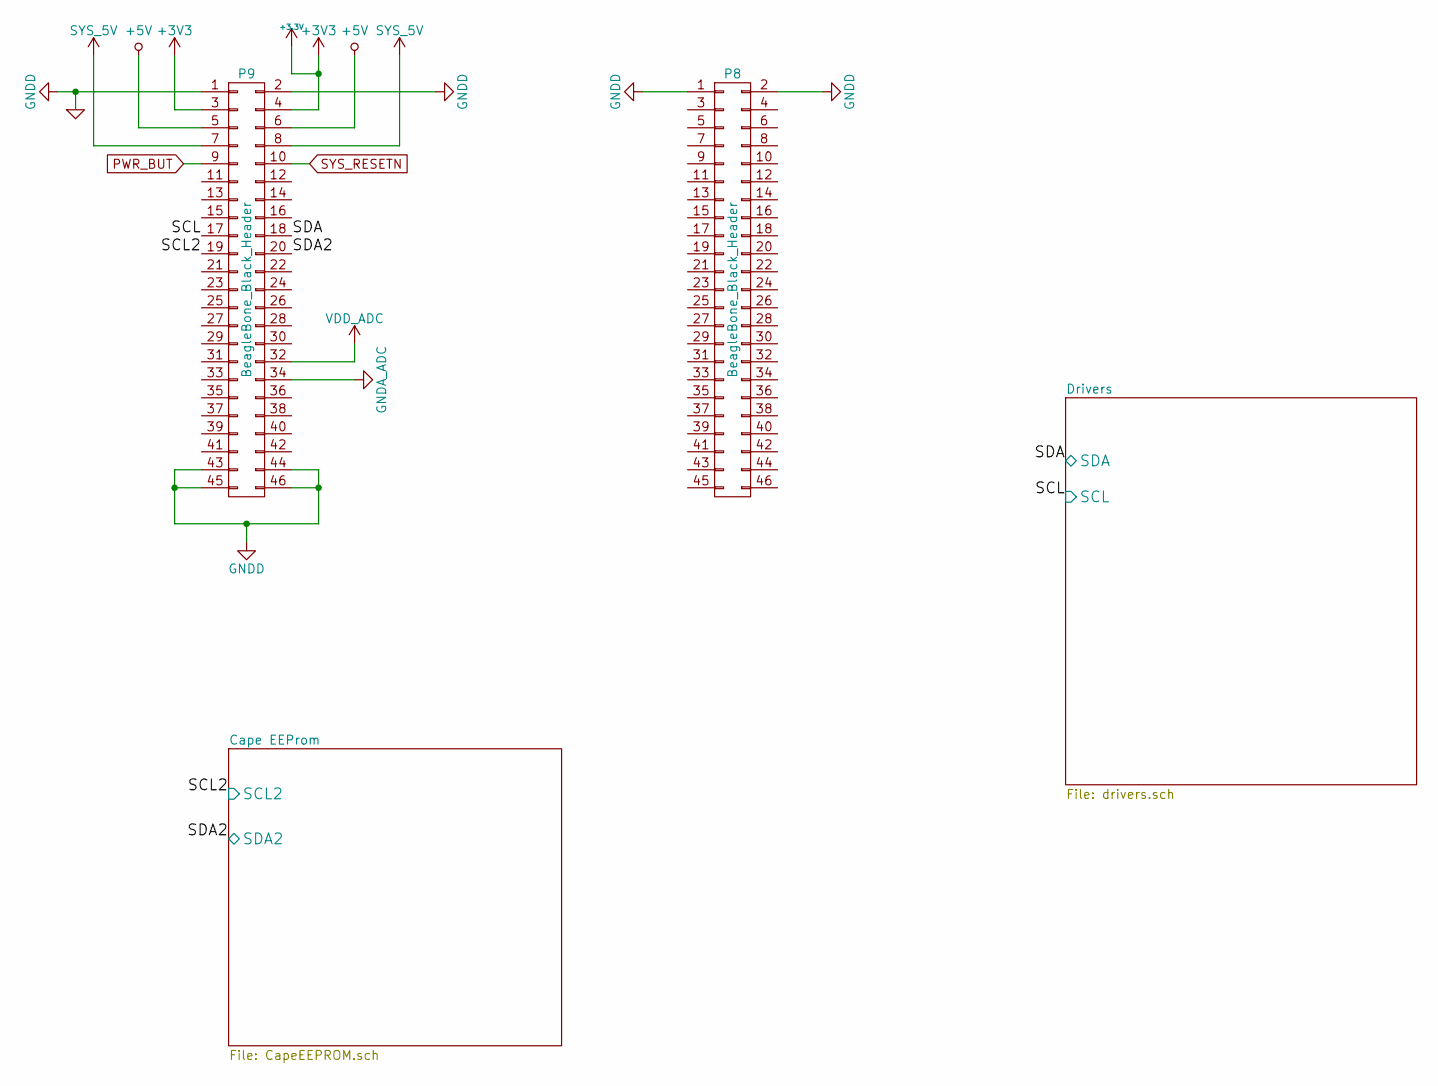
[picture p134: schematic 16DriverOutputCape.sch]

Parts:
P8, P9: BeagleBone_Black_Header; Socket_BeagleBone_Black

Connections:
+3.3V: P9.3, P9.4; also elsewhere on the board
+5V: P9.5, P9.6
/Cape EEProm/SCL2: P9.19; also elsewhere on the board
/Cape EEProm/SDA2: P9.20; also elsewhere on the board
/Drivers/SCL: P9.17; also elsewhere on the board
/Drivers/SDA: P9.18; also elsewhere on the board
GND: P8.1, P8.2, P9.1, P9.2, P9.43, P9.44, P9.45, P9.46; also elsewhere on the board
SYS_5V: P9.7, P9.8
