RobertPHeller/RPi-RRCircuits/16DriverOutputCape/16DriverOutputCape.kicad_pcb

## KiCad design 16DriverOutputCape/16DriverOutputCape.kicad_pcb (continued)

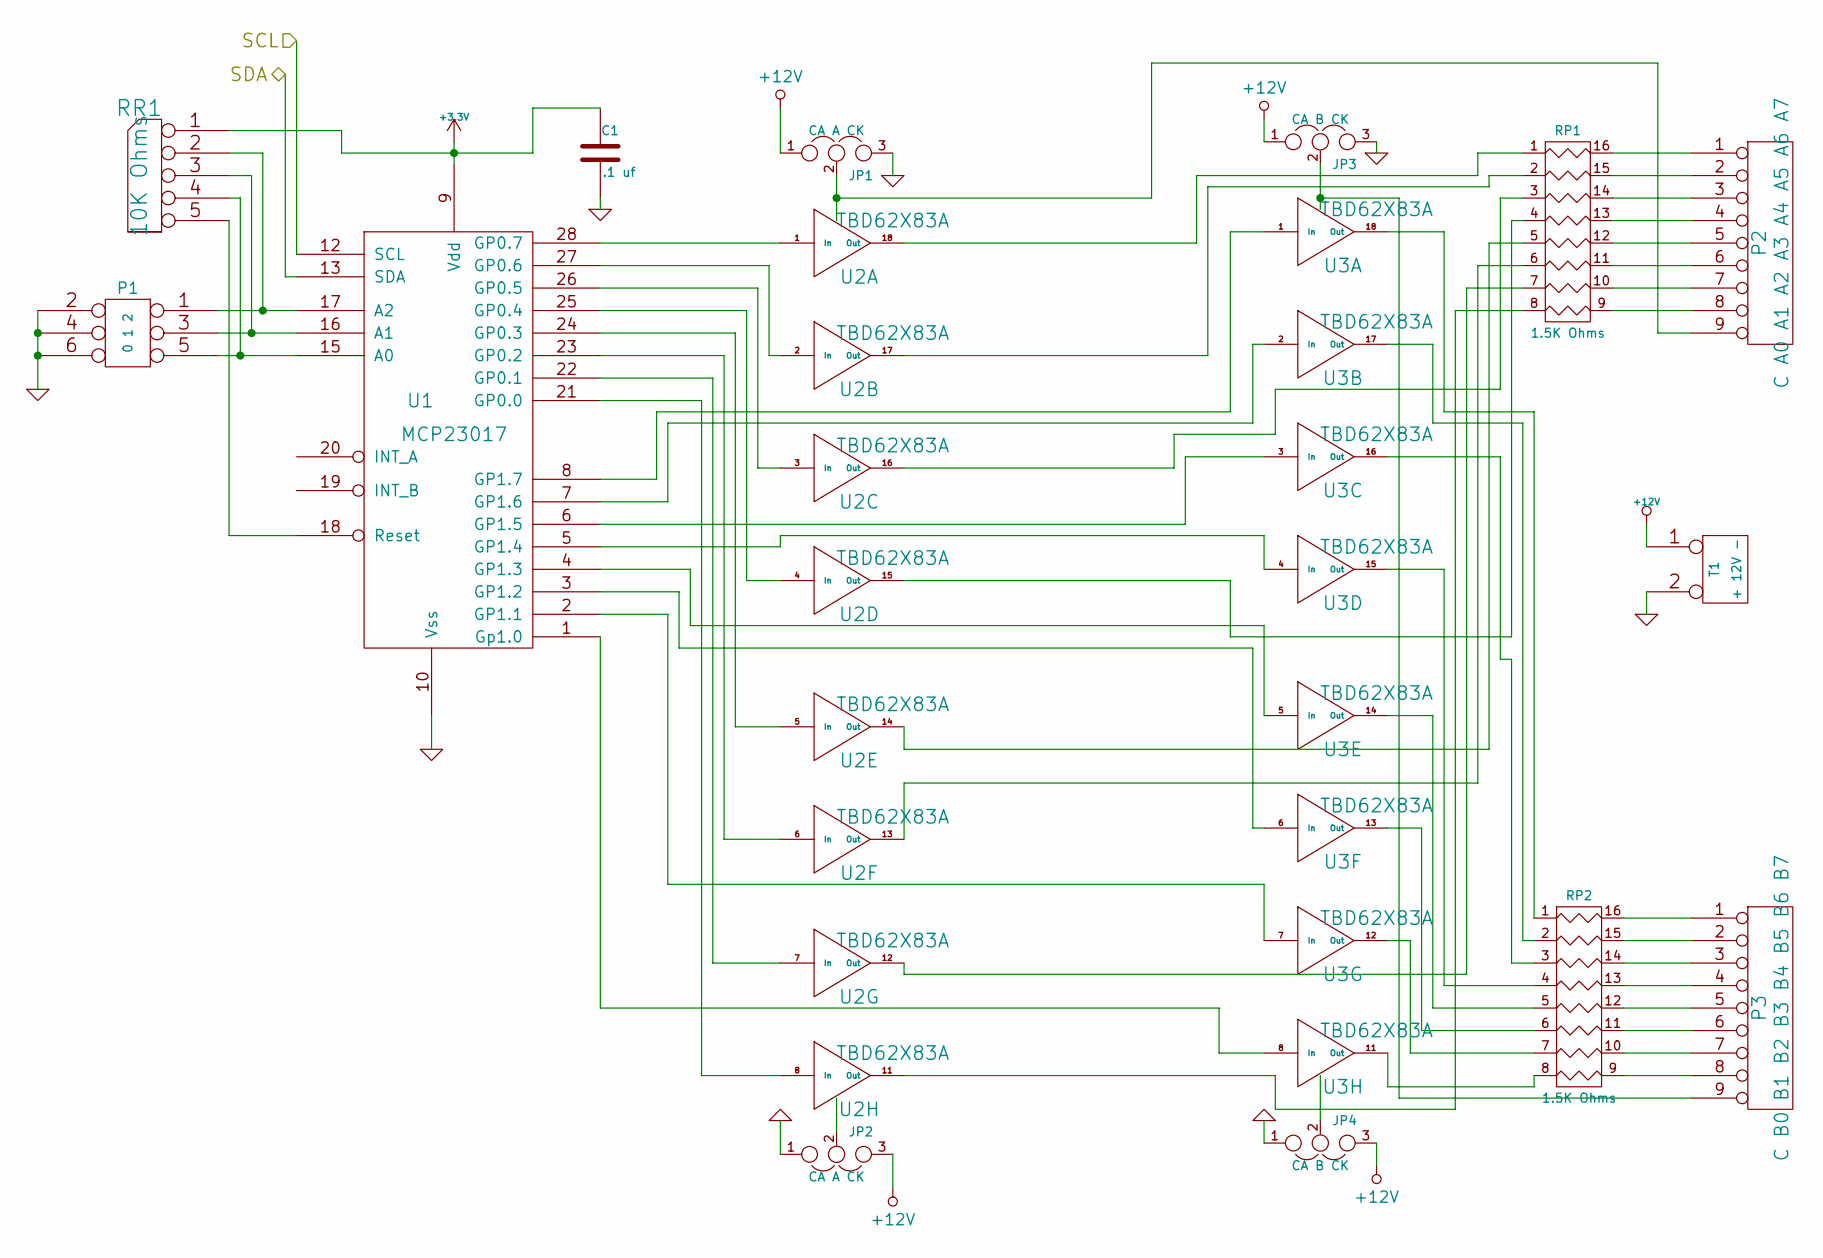
[picture p135: schematic drivers.sch]

Parts:
C1: .1 uf
JP1, JP2: CA A CK
JP3, JP4: CA B CK
P1: 0 1 2
P2: C A0 A1 A2 A3 A4 A5 A6 A7
P3: C B0 B1 B2 B3 B4 B5 B6 B7
RP1, RP2: 1.5K Ohms
RR1: 10K Ohms
T1: + 12V -
U1: MCP23017
U2, U3: TBD62X83A

Connections:
+3.3V: C1.1, RR1.1 (COM), U1.9 (Vdd); also elsewhere on the board
+12V: JP1.1, JP2.3, JP3.1, JP4.3, T1.1
/Drivers/SCL: U1.12 (SCL); also elsewhere on the board
/Drivers/SDA: U1.13 (SDA); also elsewhere on the board
GND: C1.2, JP1.3, JP2.1, JP3.3, JP4.1, P1.2, P1.4, P1.6, T1.2 (PM), U1.10 (Vss); also elsewhere on the board
unnamed: P1.1, RR1.2, U1.17 (A2)
unnamed: P1.3, RR1.3, U1.16 (A1)
unnamed: P1.5, RR1.4, U1.15 (A0)
unnamed: RR1.5, U1.18 (Reset)
unnamed: JP2.2, U2.9 (IC)
unnamed: JP3.2, P3.9, U3.10 (OC)
unnamed: JP1.2, P2.9, U2.10 (OC)
unnamed: JP4.2, U3.9 (IC)
unnamed: RP2.6, U3.13 (Out)
unnamed: RP2.8, U3.11 (Out)
unnamed: RP2.7, U3.12 (Out)
unnamed: RP2.5, U3.14 (Out)
unnamed: RP2.4, U3.15 (Out)
unnamed: RP2.3, U3.16 (Out)
unnamed: U1.26 (GP0.5), U2.3 (In)
unnamed: U1.28 (GP0.7), U2.1 (In)
unnamed: U1.27 (GP0.6), U2.2 (In)
unnamed: U1.25 (GP0.4), U2.4 (In)
unnamed: U1.24 (GP0.3), U2.5 (In)
unnamed: RP1.5, U2.14 (Out)
unnamed: U1.23 (GP0.2), U2.6 (In)
unnamed: U1.5 (GP1.4), U3.4 (In)
unnamed: U1.8 (GP1.7), U3.1 (In)
unnamed: U1.22 (GP0.1), U2.7 (In)
unnamed: RP1.7, U2.12 (Out)
unnamed: RP2.1, U3.18 (Out)
unnamed: U1.7 (GP1.6), U3.2 (In)
unnamed: P3.1, RP2.16 (R1)
unnamed: P3.2, RP2.15 (R2)
unnamed: P3.3, RP2.14 (R3)
unnamed: P3.4, RP2.13 (R4)
unnamed: P3.5, RP2.12 (R5)
unnamed: P3.6, RP2.11 (R6)
unnamed: P3.7, RP2.10 (R7)
unnamed: U1.21 (GP0.0), U2.8 (In)
unnamed: P3.8, RP2.9 (R8)
unnamed: U1.1 (Gp1.0), U3.8 (In)
unnamed: U1.2 (GP1.1), U3.7 (In)
unnamed: U1.3 (GP1.2), U3.6 (In)
unnamed: U1.4 (GP1.3), U3.5 (In)
unnamed: P2.6, RP1.11 (R6)
unnamed: RP2.2, U3.17 (Out)
unnamed: P2.1, RP1.16 (R1)
unnamed: P2.2, RP1.15 (R2)
unnamed: P2.3, RP1.14 (R3)
unnamed: P2.4, RP1.13 (R4)
unnamed: P2.5, RP1.12 (R5)
unnamed: P2.7, RP1.10 (R7)
unnamed: P2.8, RP1.9 (R8)
unnamed: RP1.8, U2.11 (Out)
unnamed: RP1.6, U2.13 (Out)
unnamed: RP1.4, U2.15 (Out)
unnamed: RP1.3, U2.16 (Out)
unnamed: RP1.2, U2.17 (Out)
unnamed: RP1.1, U2.18 (Out)
unnamed: U1.6 (GP1.5), U3.3 (In)


Parts:
C104: .1 uf
JMP102: WP 1 0
R104, R105: 5.6K Ohms
R106, R107, R108: 4.75K Ohms
R109: 10K Ohms
U102: CAT24C256W

Connections:
+3.3V: C104.1, R104.1, R105.1, R106.1, R107.1, R108.1, R109.1, U102.8 (Vcc); also elsewhere on the board
/Cape EEProm/SCL2: R105.2, U102.6 (SCL); also elsewhere on the board
/Cape EEProm/SDA2: R104.2, U102.5 (SDA); also elsewhere on the board
GND: C104.2, JMP102.1, JMP102.3, JMP102.5, U102.4 (Vss); also elsewhere on the board
unnamed: R108.2, U102.3 (A2)
unnamed: JMP102.4, R107.2, U102.2 (A1)
unnamed: JMP102.2, R106.2, U102.1 (A0)
unnamed: JMP102.6, R109.2, U102.7 (WP)

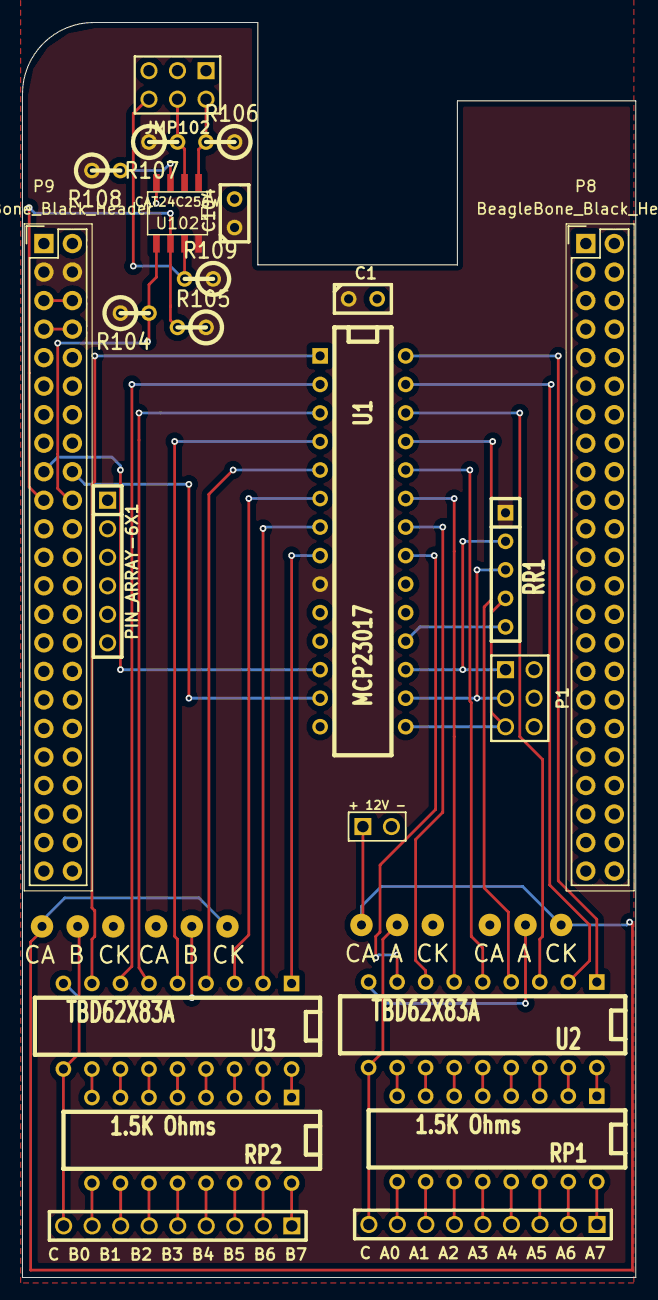
[picture p136: board 16DriverOutputCape.kicad_pcb from above]

Board: 2 copper layers, 54.6 x 111.8 mm, 27 parts (0 on the bottom side), 69 nets.

Other parts of the board:
PIN_ARRAY-6X1: Val**; PIN_ARRAY-6X1
