RobertPHeller/RPi-RRCircuits/QuadOCDectCape/QuadOCDectCape.kicad_pcb

## KiCad design QuadOCDectCape/QuadOCDectCape.kicad_pcb (2019-07-04)

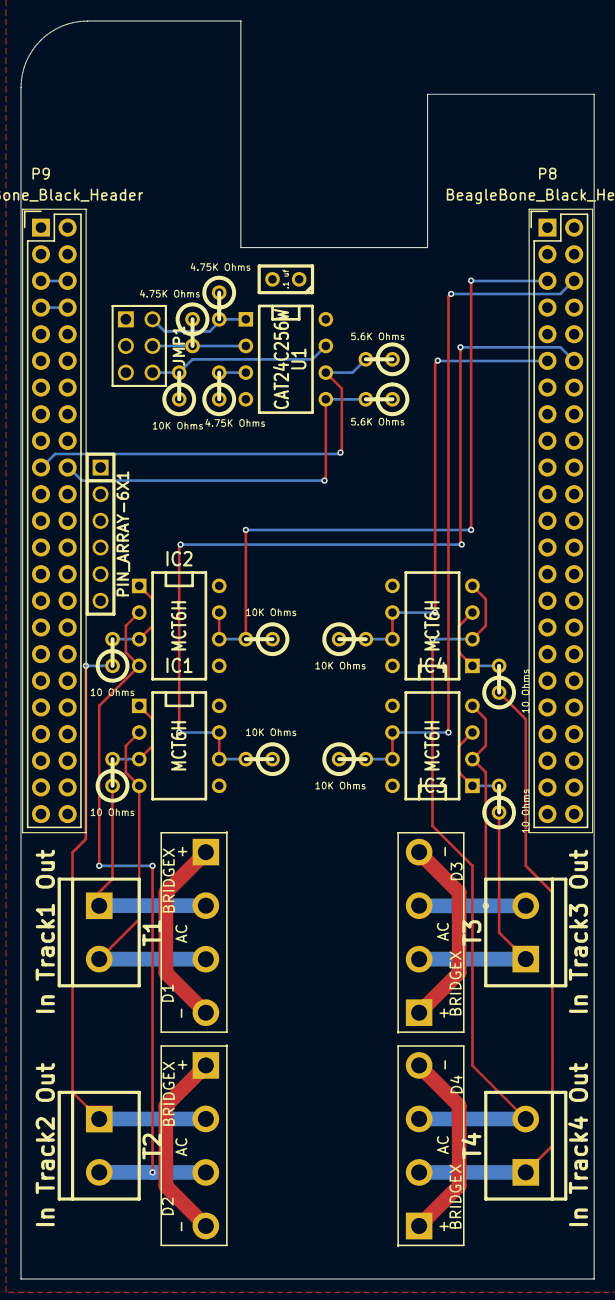
[picture p137: board QuadOCDectCape.kicad_pcb from above]

Board: 2 copper layers, 54.6 x 119.9 mm, 32 parts (0 on the bottom side), 30 nets.

Parts:
C1: .1 uf; C1
D1, D2, D3, D4: BRIDGEX; KBL
IC1, IC2, IC3, IC4: MCT6H; DIP-8__300
JMP1: WP 1 0; pin_array_3x2
P8, P9: BeagleBone_Black_Header; Socket_BeagleBone_Black
PIN_ARRAY-6X1: Val**; PIN_ARRAY-6X1
R1, R3, R5, R7: 10 Ohms; R1
R2, R4, R6, R8, R14: 10K Ohms; R1
R9, R10: 5.6K Ohms; R1
R11, R12, R13: 4.75K Ohms; R1
T1: In Track1 Out; bornier2
T2: In Track2 Out; bornier2
T3: In Track3 Out; bornier2
T4: In Track4 Out; bornier2
U1: CAT24C256W; DIP-8__300

Connections:
+3.3V: C1.1, P9.3, P9.4, R2.1, R4.1, R6.1, R8.1, R9.1, R10.1, R11.1, R12.1, R13.1, R14.1, U1.8
+5V: P9.5, P9.6
/Cape EEProm/SCL: P9.19, R10.2, U1.6
/Cape EEProm/SDA: P9.20, R9.2, U1.5
/Occupancy Detector 1/OD1: IC1.6, IC1.7, P8.12, R2.2
/Occupancy Detector 2/OD2: IC2.6, IC2.7, P8.5, R4.2
/Occupancy Detector 3/OD3: IC3.6, IC3.7, P8.6, R6.2
/Occupancy Detector 4/OD4: IC4.6, IC4.7, P8.11, R8.2
GND: C1.2, IC1.5, IC1.8, IC2.5, IC2.8, IC3.5, IC3.8, IC4.5, IC4.8, JMP1.1, JMP1.3, JMP1.5, P8.1, P8.2, P9.1, P9.2, P9.43, P9.44, P9.45, P9.46, U1.4
unnamed: IC4.1, IC4.3, R7.2
unnamed: D4.3, IC4.2, IC4.4, T4.2
unnamed: D4.2, R7.1, T4.1
unnamed: D4.1, D4.4
unnamed: JMP1.6, R14.2, U1.7
unnamed: JMP1.2, R11.2, U1.1
unnamed: JMP1.4, R12.2, U1.2
unnamed: R13.2, U1.3
unnamed: IC1.1, IC1.3, R1.2
unnamed: D1.3, IC1.2, IC1.4, T1.2
unnamed: D1.2, R1.1, T1.1
unnamed: D1.1, D1.4
unnamed: D2.2, R3.1, T2.1
unnamed: D2.1, D2.4
unnamed: D2.3, IC2.2, IC2.4, T2.2
unnamed: IC2.1, IC2.3, R3.2
unnamed: D3.3, IC3.2, IC3.4, T3.2
unnamed: IC3.1, IC3.3, R5.2
unnamed: D3.2, R5.1, T3.1
unnamed: D3.1, D3.4
SYS_5V: P9.7, P9.8
