RobertPHeller/RPi-RRCircuits/QuadSMCSenseCape/QuadSMCSenseCape.kicad_pcb

## KiCad design QuadSMCSenseCape/QuadSMCSenseCape.kicad_pcb (2019-07-04)

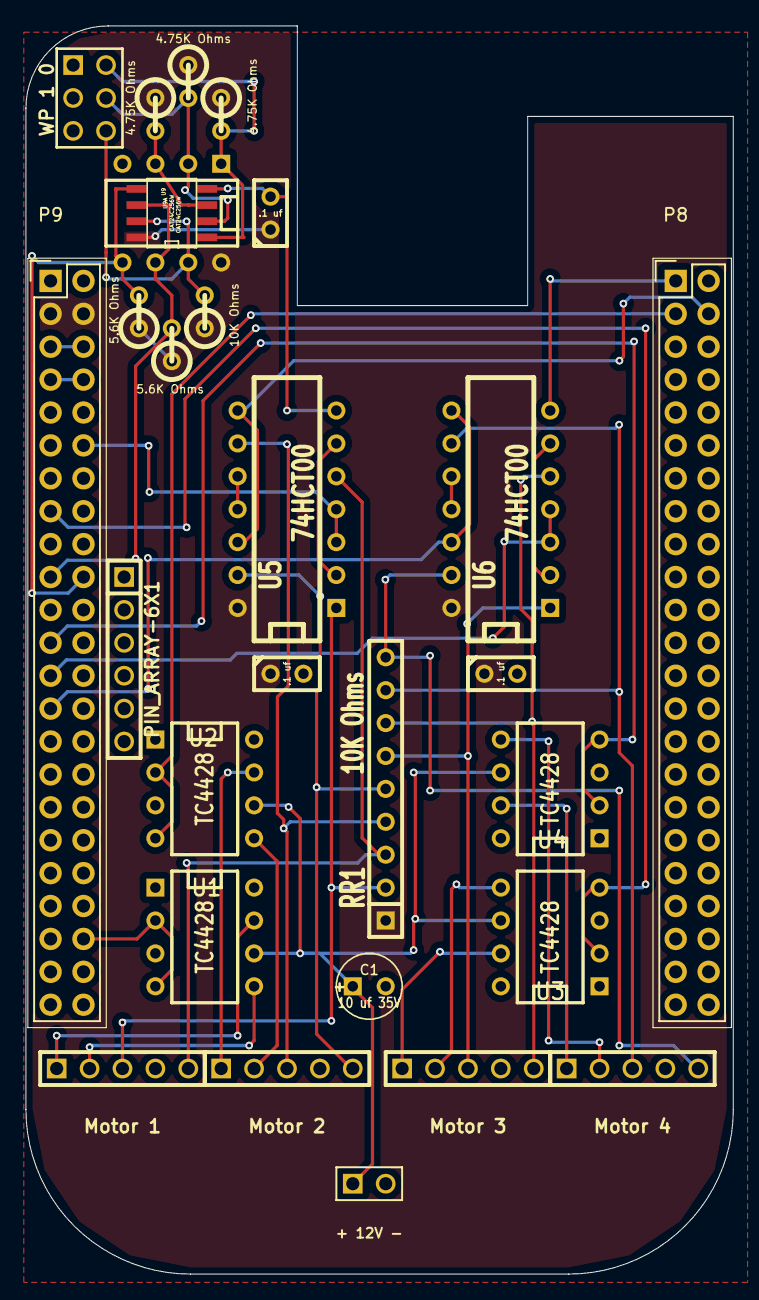
[picture p138: board QuadSMCSenseCape.kicad_pcb from above]

Board: 2 copper layers, 54.6 x 96.4 mm, 28 parts (0 on the bottom side), 39 nets.

Parts:
C1: 10 uf 35V; C1V5
C2, C3, C8: .1 uf; C1
P2: WP 1 0; pin_array_3x2
P8, P9: BeagleBone_Black_Header; Socket_BeagleBone_Black
PIN_ARRAY-6X1: Val**; PIN_ARRAY-6X1
R3, R4: 5.6K Ohms; R1
R5, R6, R7: 4.75K Ohms; R1
R8: 10K Ohms; R1
RR1: 10K Ohms; SIL-9
T1: Motor 1; ScrewTerm_2.54-5
T2: Motor 2; ScrewTerm_2.54-5
T3: Motor 3; ScrewTerm_2.54-5
T4: Motor 4; ScrewTerm_2.54-5
T5: + 12V -; ScrewTerm2.54-2
U1, U2, U3, U4: TC4428; DIP-8__300
U5, U6: 74HCT00; DIP-14__300
U9: CAT24C256W; DIP-8__300
U9A: CAT24C256W; SOIC-8_N

Connections:
+3.3V: C2.1, C3.1, C8.1, P9.3, P9.4, R3.1, R4.1, R5.1, R6.1, R7.1, R8.1, RR1.1, U5.14, U6.14, U9.8, U9A.8
+5V: P9.5, P9.6
+12V: C1.1, T5.1, U1.6, U2.6, U3.6, U4.6
/Cape EEPROM/SCL: P9.19, R4.2, U9.6, U9A.6
/Cape EEPROM/SDA: P9.20, R3.2, U9.5, U9A.5
/MSel1: P9.42, U1.2, U1.4
/MSel2: P8.3, U2.2, U2.4
/MSel3: P9.15, U3.2, U3.4
/MSel4: P9.23, U4.2, U4.4
/Motor1A: T1.1, U1.7
/Motor1B: T1.2, U1.5
/Motor2A: T2.1, U2.7
/Motor2B: T2.2, U2.5
/Motor3A: T3.1, U3.7
/Motor3B: T3.2, U3.5
/Motor4A: T4.1, U4.7
/Motor4B: T4.2, U4.5
/PSense1: P9.12, U5.3, U5.4
/PSense2: P8.4, U5.8, U5.12
/PSense3: P9.25, U6.3, U6.4
/PSense4: P9.27, U6.8, U6.12
/Points1A: RR1.2, T1.3, U5.1
/Points1B: RR1.3, T1.5, U5.5
/Points2A: RR1.4, T2.3, U5.9
/Points2B: RR1.5, T2.5, U5.13
/Points3A: RR1.6, T3.3, U6.1
/Points3B: RR1.7, T3.5, U6.5
/Points4A: RR1.8, T4.3, U6.9
/Points4B: RR1.9, T4.5, U6.13
GND: C1.2, C2.2, C3.2, C8.2, P2.1, P2.3, P2.5, P8.1, P8.2, P9.1, P9.2, P9.43, P9.44, P9.45, P9.46, T1.4, T2.4, T3.4, T4.4, T5.2, U1.3, U2.3, U3.3, U4.3, U5.7, U6.7, U9.4, U9A.4
unnamed: U5.2, U5.6
unnamed: U6.10, U6.11
unnamed: U5.10, U5.11
unnamed: U6.2, U6.6
unnamed: P2.6, R8.2, U9.7, U9A.7
unnamed: P2.2, R5.2, U9.1, U9A.1
unnamed: P2.4, R6.2, U9.2, U9A.2
unnamed: R7.2, U9.3, U9A.3
SYS_5V: P9.7, P9.8
