RobertPHeller/RPi-RRCircuits/RPiHalfSiding/RPiHalfSiding.kicad_pcb

## KiCad design RPiHalfSiding/RPiHalfSiding.kicad_pcb (2019-01-16)

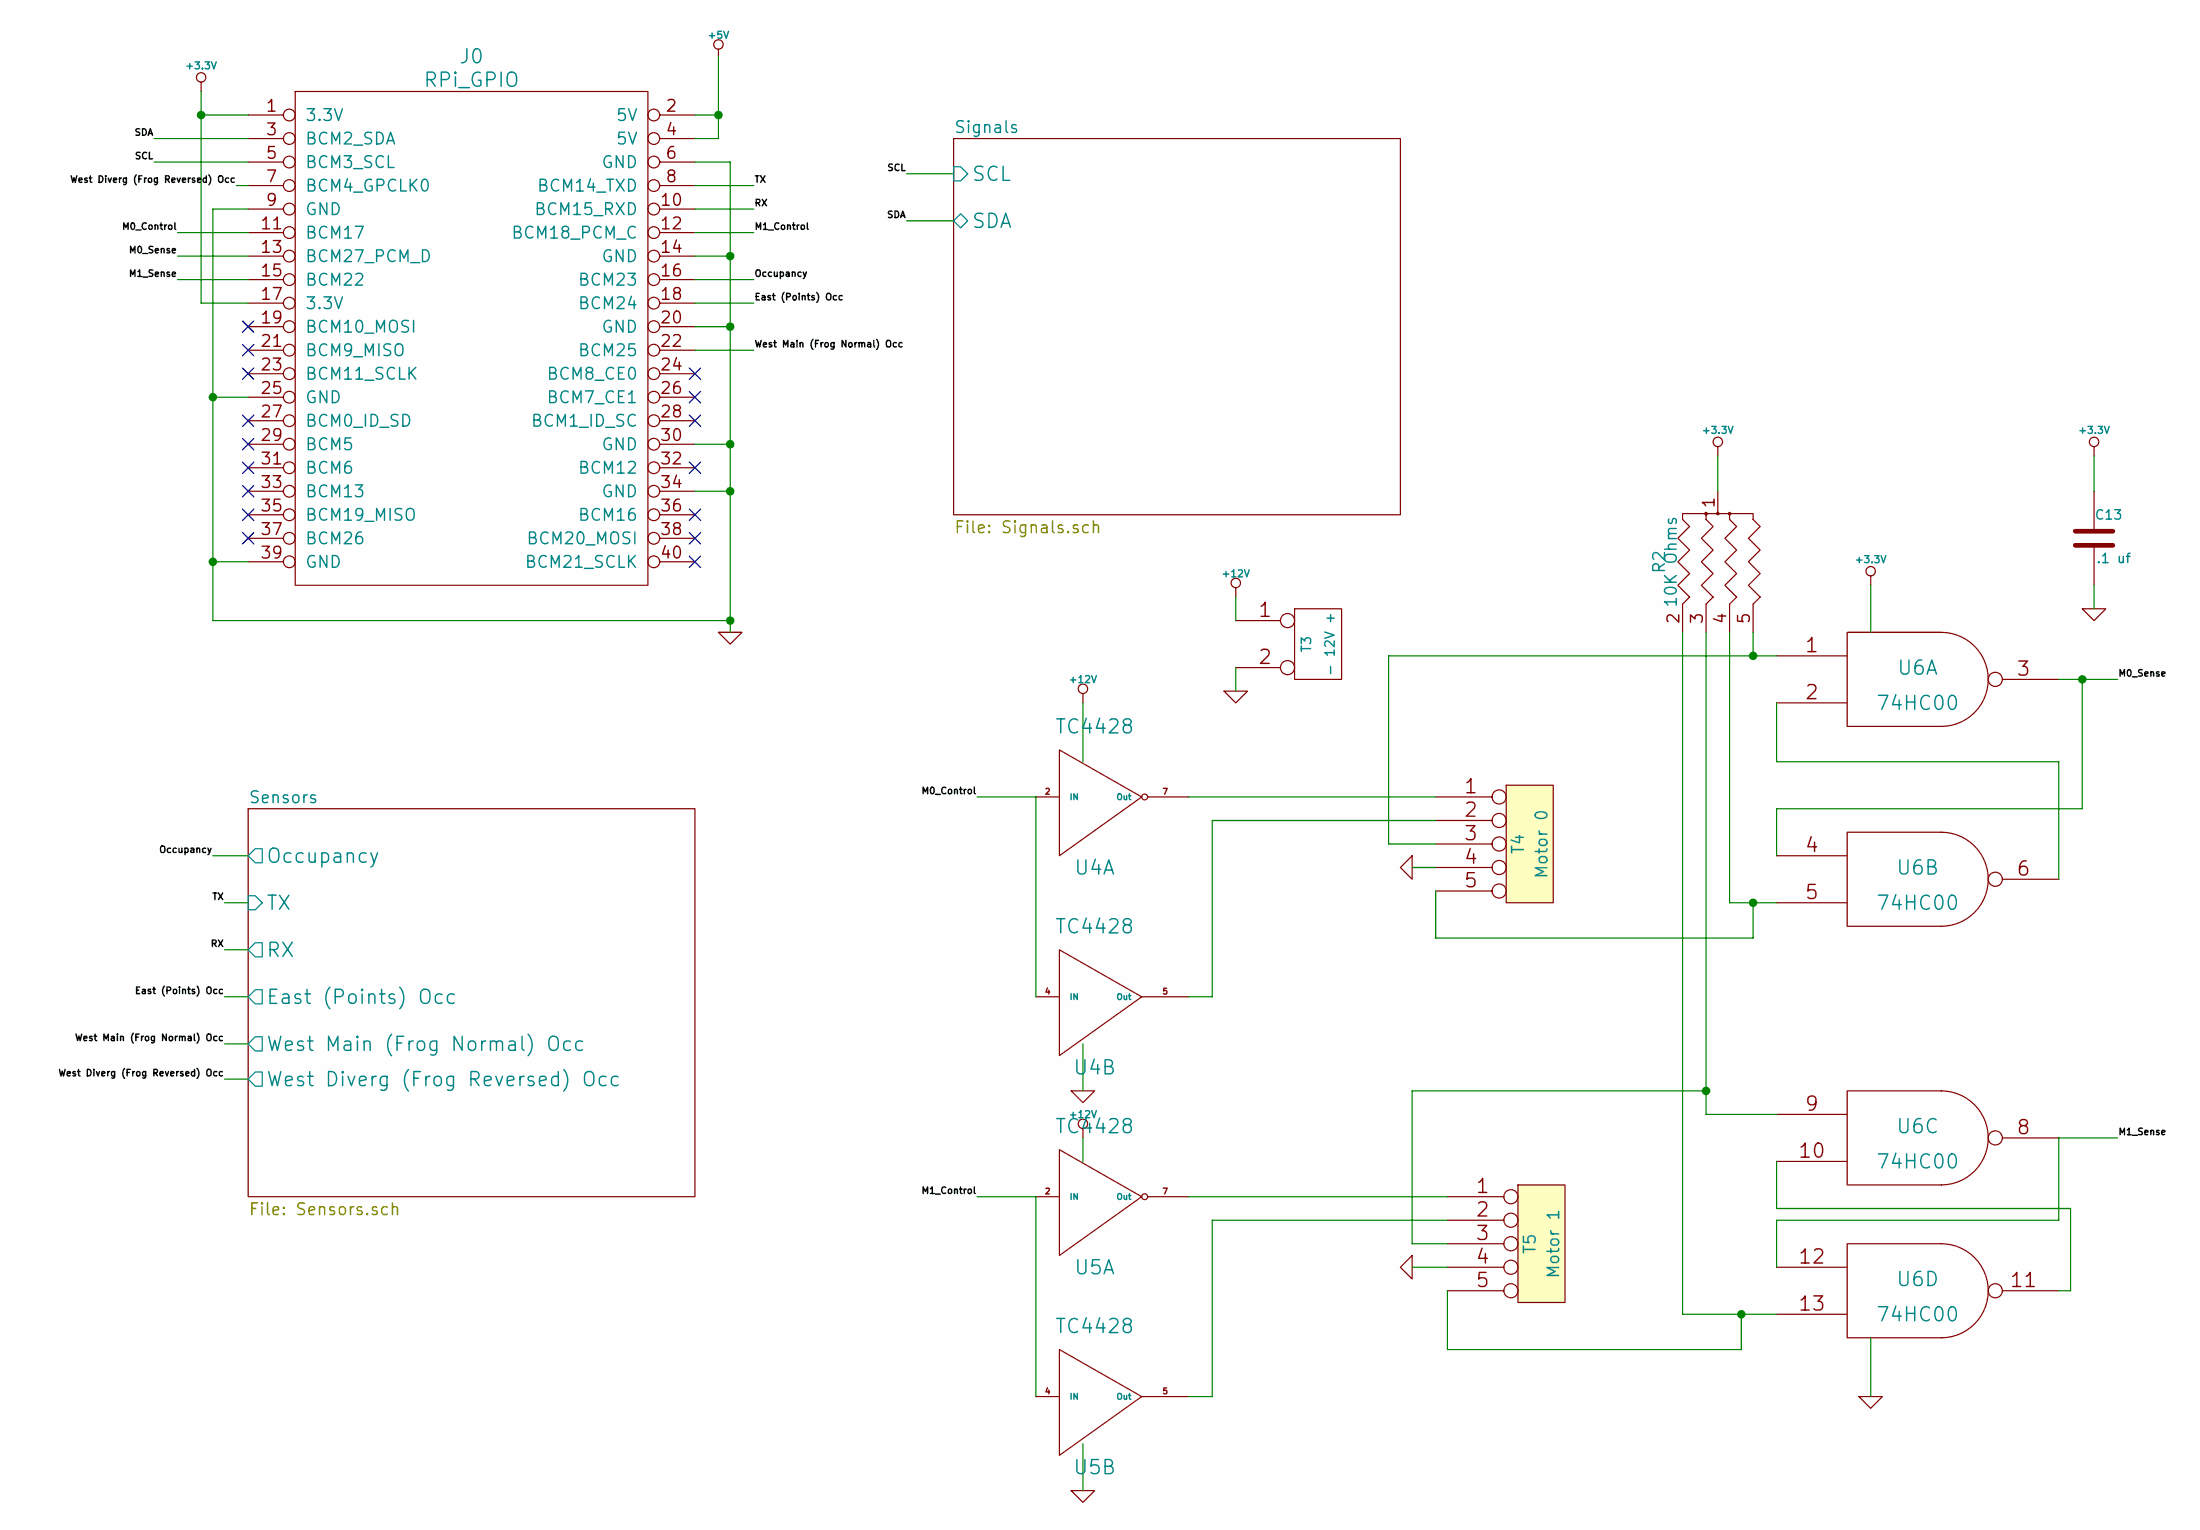
[picture p139: schematic RPiHalfSiding.sch]

Parts:
C13: .1 uf
J0: RPi_GPIO; Pin_Header_Straight_2x20
R2: 10K Ohms
T3: - 12V +
T4: Motor 0
T5: Motor 1
U4, U5: TC4428
U6: 74HC00

Connections:
+3.3V: C13.1, J0.1 (3.3V), J0.17 (3.3V), R2.1, U6.14 (VCC); also elsewhere on the board
+5V: J0.2 (5V), J0.4 (5V); also elsewhere on the board
+12V: T3.1, U4.6 (Vdd), U5.6 (Vdd)
/M0_Control: J0.11 (BCM17), U4.2 (IN), U4.4 (IN)
/M0_Sense: J0.13 (BCM27_PCM_D), U6.3, U6.4
/M1_Control: J0.12 (BCM18_PCM_C), U5.2 (IN), U5.4 (IN)
/M1_Sense: J0.15 (BCM22), U6.8, U6.12
/Sensors/East (Points) Occ: J0.18 (BCM24); also elsewhere on the board
/Sensors/Occupancy: J0.16 (BCM23); also elsewhere on the board
/Sensors/RX: J0.10 (BCM15_RXD); also elsewhere on the board
/Sensors/TX: J0.8 (BCM14_TXD); also elsewhere on the board
/Sensors/West Diverg (Frog Reversed) Occ: J0.7 (BCM4_GPCLK0); also elsewhere on the board
/Sensors/West Main (Frog Normal) Occ: J0.22 (BCM25); also elsewhere on the board
/Signals/SCL: J0.5 (BCM3_SCL); also elsewhere on the board
/Signals/SDA: J0.3 (BCM2_SDA); also elsewhere on the board
GND: C13.2, J0.6 (GND), J0.9 (GND), J0.14 (GND), J0.20 (GND), J0.25 (GND), J0.30 (GND), J0.34 (GND), J0.39 (GND), T3.2 (PM), T4.4, T5.4, U4.3 (GND), U5.3 (GND), U6.7 (GND); also elsewhere on the board
unnamed: U6.2, U6.6
unnamed: U6.10, U6.11
unnamed: T5.2, U5.5 (Out)
unnamed: R2.2, T5.5, U6.13
unnamed: R2.3, T5.3, U6.9
unnamed: R2.4, T4.5, U6.5
unnamed: R2.5, T4.3, U6.1
unnamed: T5.1, U5.7 (Out)
unnamed: T4.2, U4.5 (Out)
unnamed: T4.1, U4.7 (Out)

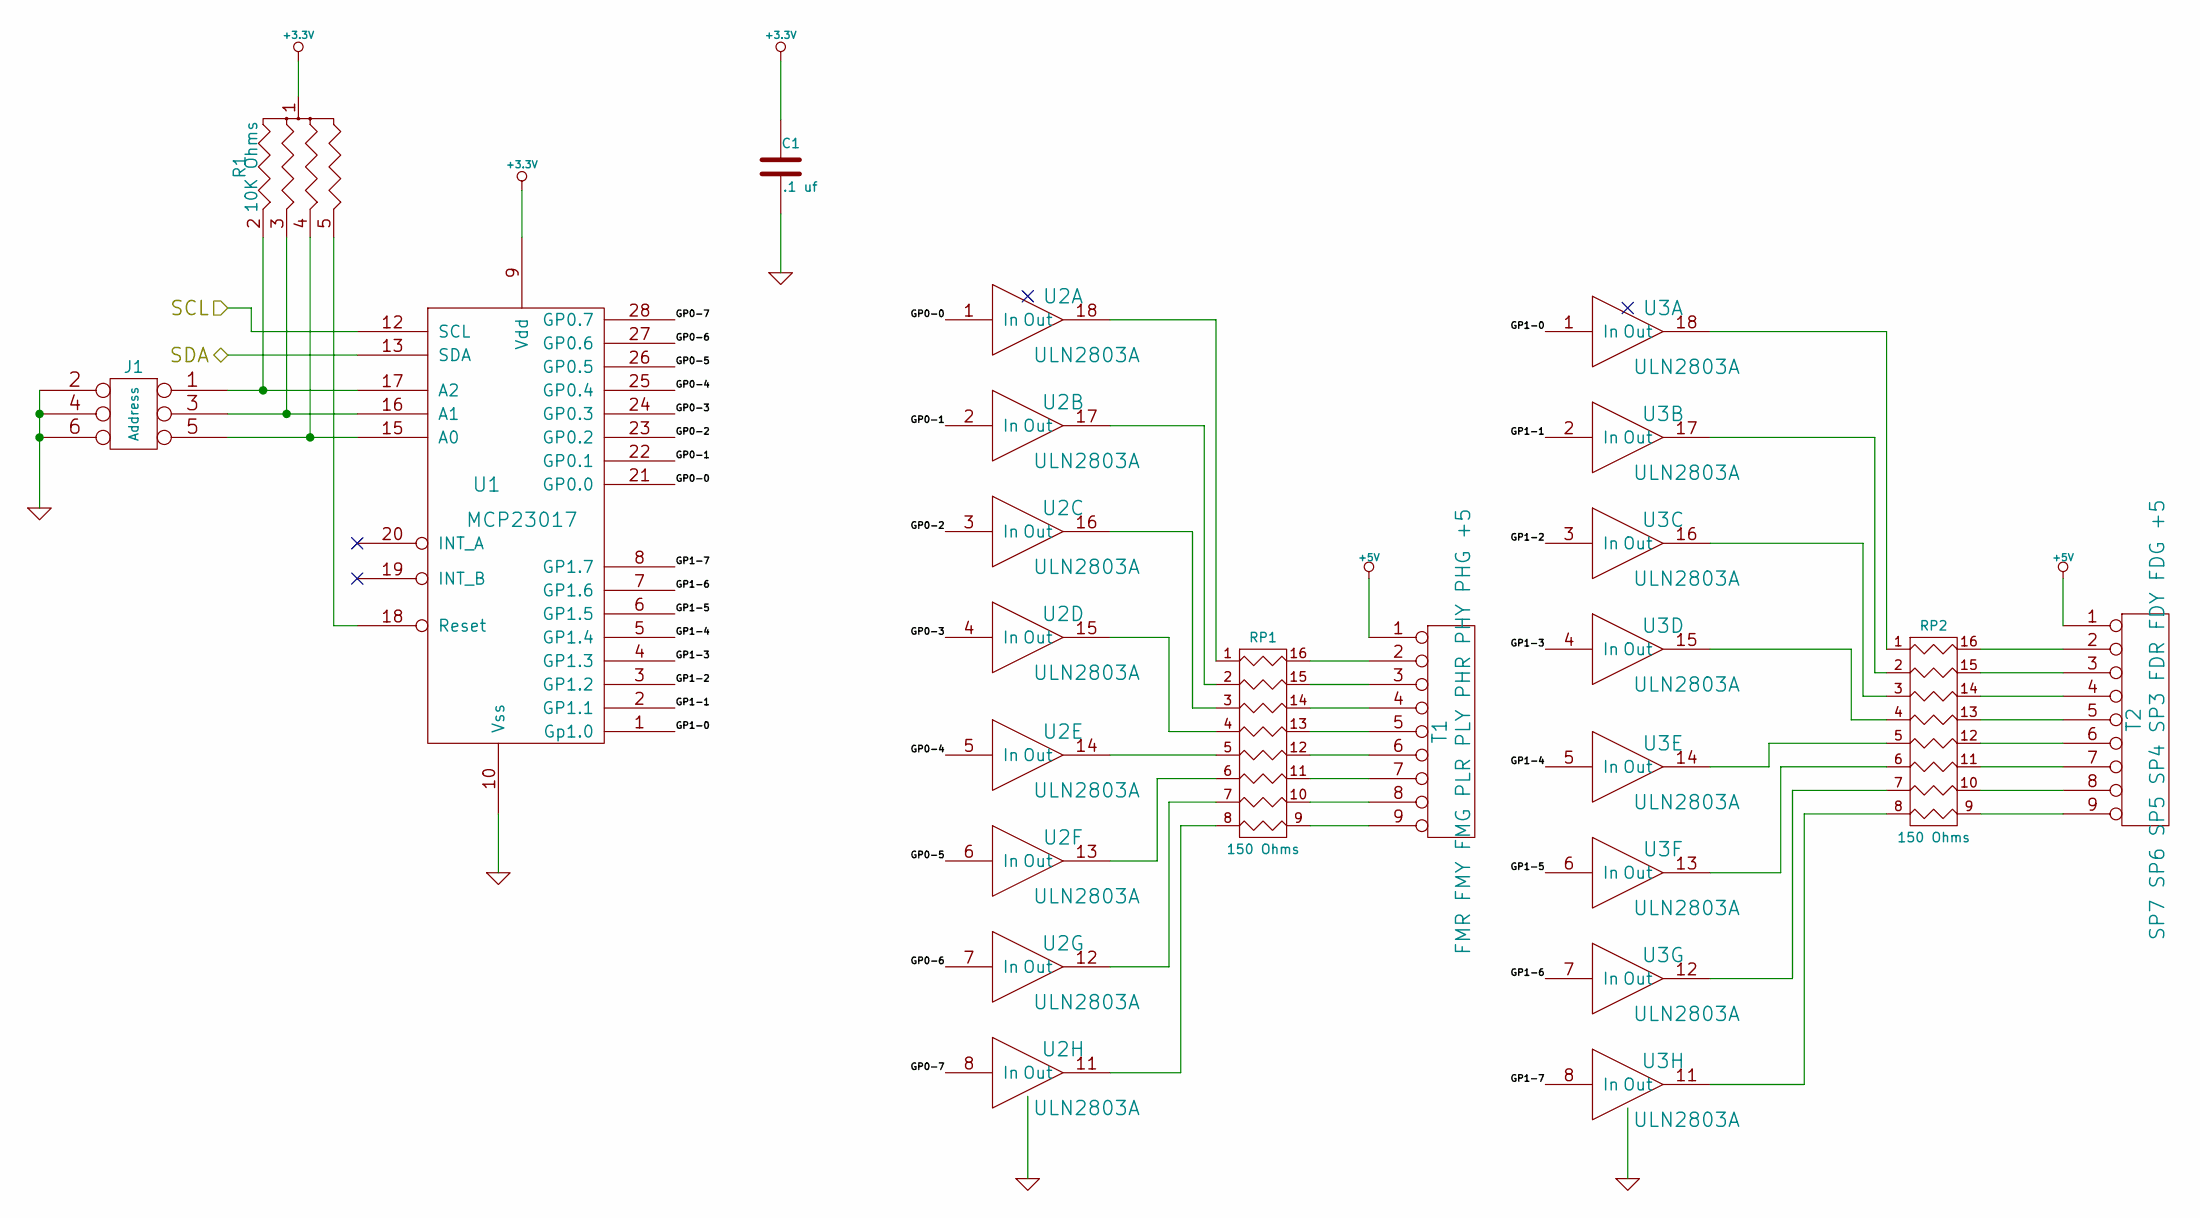
[picture p140: schematic Signals.sch]

Parts:
C1: .1 uf
J1: Address
R1: 10K Ohms
RP1, RP2: 150 Ohms
T1: FMR FMY FMG PLR PLY PHR PHY PHG +5
T2: SP7 SP6 SP5 SP4 SP3 FDR FDY FDG +5
U1: MCP23017
U2, U3: ULN2803A

Connections:
+3.3V: C1.1, R1.1, U1.9 (Vdd); also elsewhere on the board
+5V: T1.1, T2.1; also elsewhere on the board
/Signals/GP0-0: U1.21 (GP0.0), U2.1 (In)
/Signals/GP0-1: U1.22 (GP0.1), U2.2 (In)
/Signals/GP0-2: U1.23 (GP0.2), U2.3 (In)
/Signals/GP0-3: U1.24 (GP0.3), U2.4 (In)
/Signals/GP0-4: U1.25 (GP0.4), U2.5 (In)
/Signals/GP0-5: U1.26 (GP0.5), U2.6 (In)
/Signals/GP0-6: U1.27 (GP0.6), U2.7 (In)
/Signals/GP0-7: U1.28 (GP0.7), U2.8 (In)
/Signals/GP1-0: U1.1 (Gp1.0), U3.1 (In)
/Signals/GP1-1: U1.2 (GP1.1), U3.2 (In)
/Signals/GP1-2: U1.3 (GP1.2), U3.3 (In)
/Signals/GP1-3: U1.4 (GP1.3), U3.4 (In)
/Signals/GP1-4: U1.5 (GP1.4), U3.5 (In)
/Signals/GP1-5: U1.6 (GP1.5), U3.6 (In)
/Signals/GP1-6: U1.7 (GP1.6), U3.7 (In)
/Signals/GP1-7: U1.8 (GP1.7), U3.8 (In)
/Signals/SCL: U1.12 (SCL); also elsewhere on the board
/Signals/SDA: U1.13 (SDA); also elsewhere on the board
GND: C1.2, J1.2, J1.4, J1.6, U1.10 (Vss), U2.9 (GND), U3.9 (GND); also elsewhere on the board
unnamed: R1.5, U1.18 (Reset)
unnamed: J1.1, R1.2, U1.17 (A2)
unnamed: RP1.12 (R5), T1.6
unnamed: RP1.13 (R4), T1.5
unnamed: RP1.14 (R3), T1.4
unnamed: RP1.15 (R2), T1.3
unnamed: RP1.16 (R1), T1.2
unnamed: RP2.9 (R8), T2.9
unnamed: RP2.10 (R7), T2.8
unnamed: RP2.11 (R6), T2.7
unnamed: RP2.12 (R5), T2.6
unnamed: RP2.13 (R4), T2.5
unnamed: RP2.14 (R3), T2.4
unnamed: RP2.15 (R2), T2.3
unnamed: RP2.16 (R1), T2.2
unnamed: RP1.9 (R8), T1.9
unnamed: RP1.10 (R7), T1.8
unnamed: RP1.11 (R6), T1.7
unnamed: J1.5, R1.4, U1.15 (A0)
unnamed: J1.3, R1.3, U1.16 (A1)
unnamed: RP2.8, U3.11 (Out)
unnamed: RP2.7, U3.12 (Out)
unnamed: RP2.6, U3.13 (Out)
unnamed: RP1.7, U2.12 (Out)
unnamed: RP1.6, U2.13 (Out)
unnamed: RP1.5, U2.14 (Out)
unnamed: RP1.4, U2.15 (Out)
unnamed: RP1.3, U2.16 (Out)
unnamed: RP1.2, U2.17 (Out)
unnamed: RP1.1, U2.18 (Out)
unnamed: RP2.5, U3.14 (Out)
unnamed: RP2.4, U3.15 (Out)
unnamed: RP2.3, U3.16 (Out)
unnamed: RP2.2, U3.17 (Out)
unnamed: RP2.1, U3.18 (Out)
unnamed: RP1.8, U2.11 (Out)

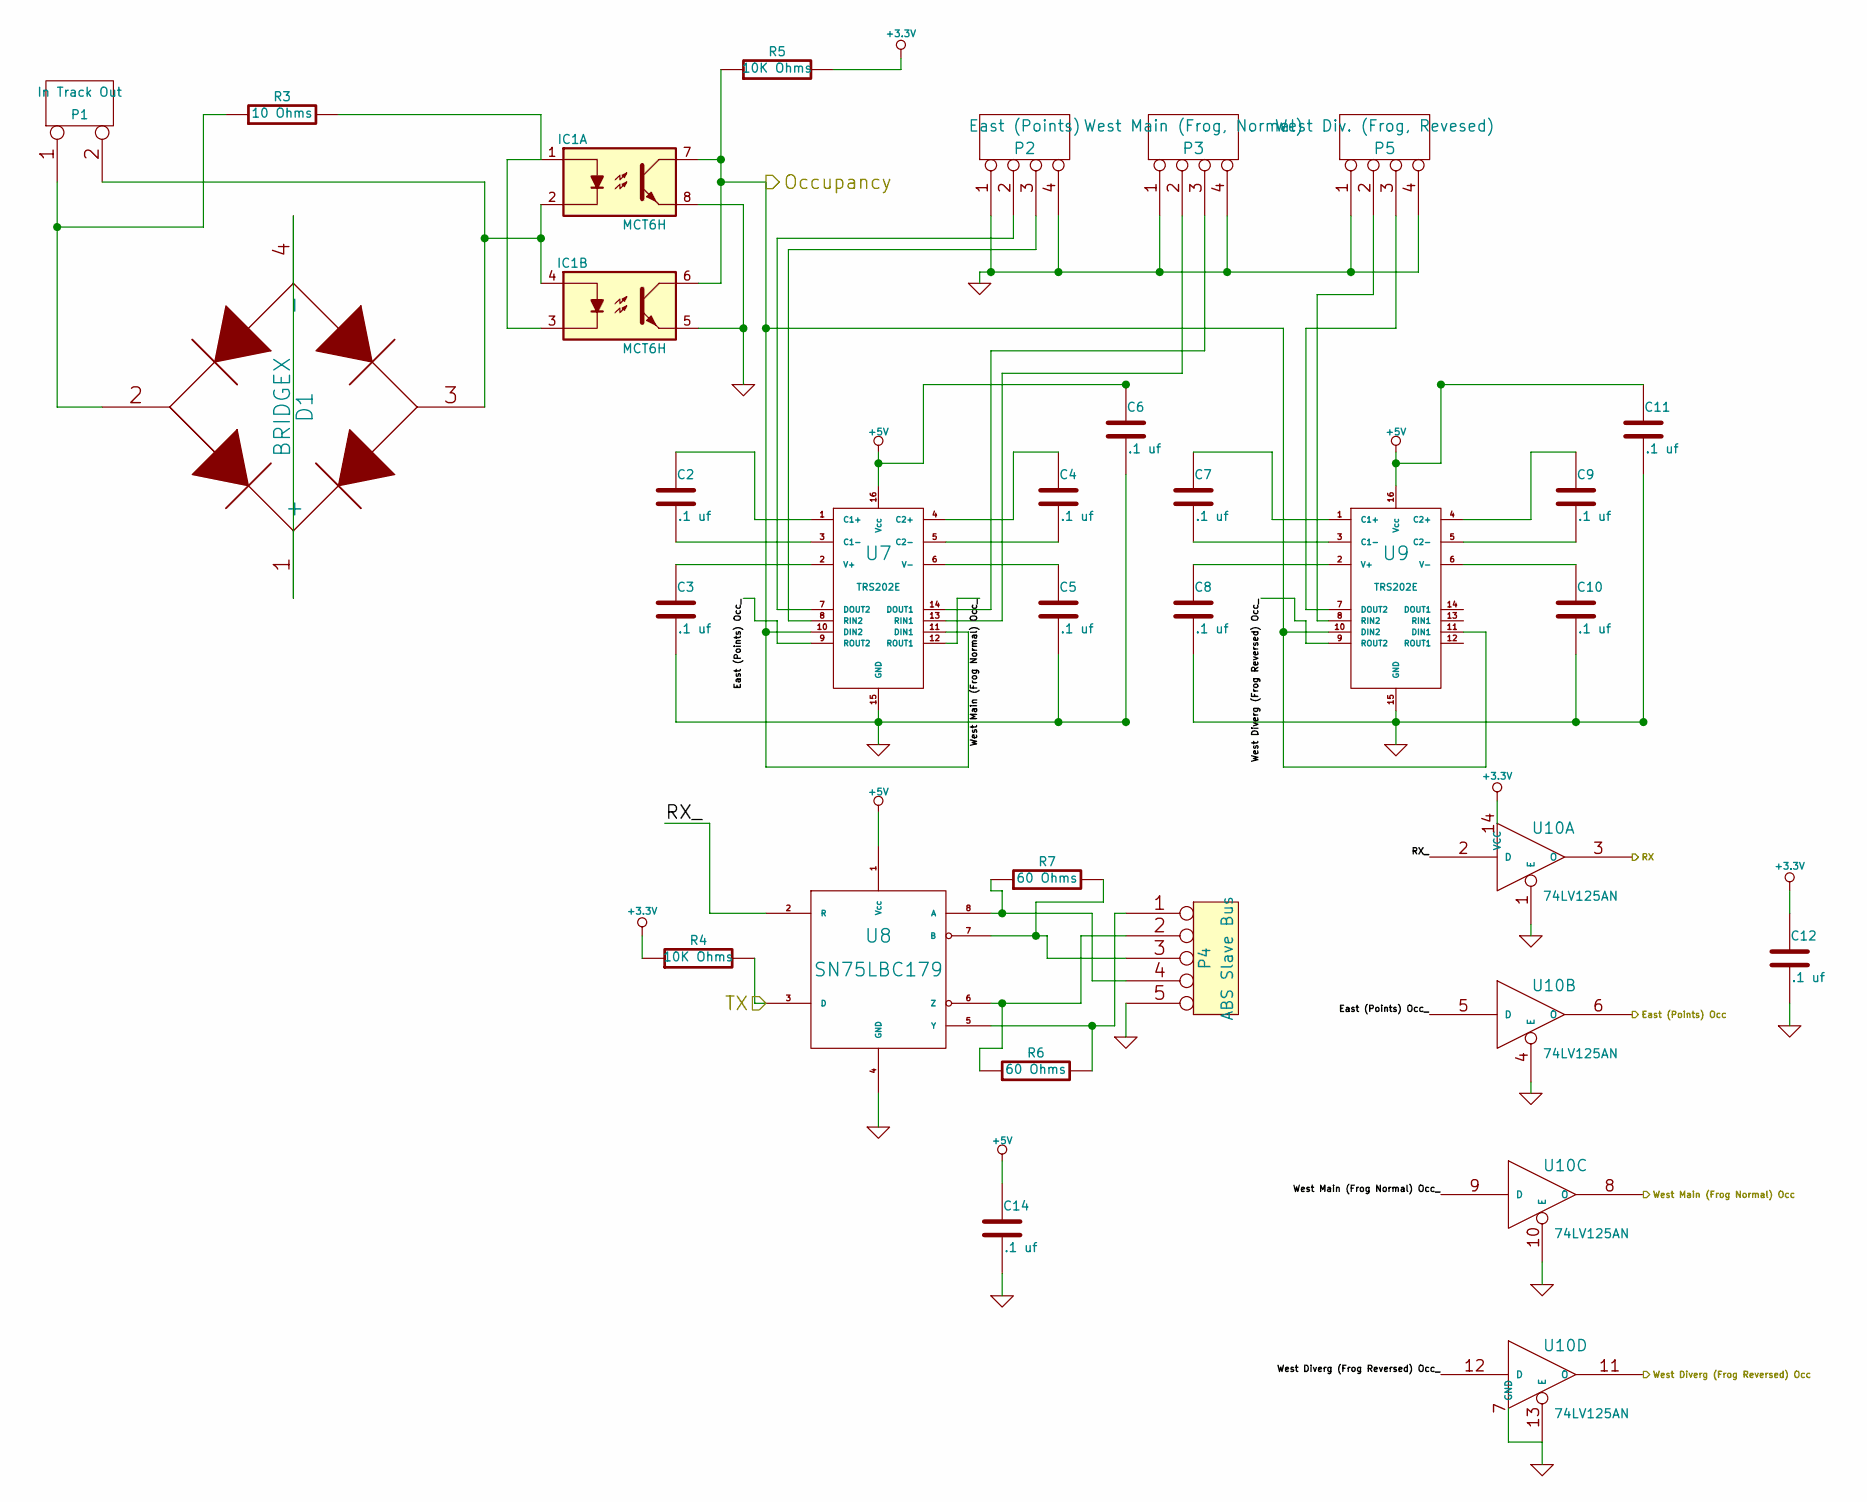
[picture p141: schematic Sensors.sch]

Parts:
C2, C3, C4, C5, C6, C7, C8, C9, C10, C11, C12, C14: .1 uf
D1: BRIDGEX
IC1: MCT6H; DIP-8__300
P1: In Track Out
P2: East (Points)
P3: West Main (Frog, Normal)
P4: ABS Slave Bus
P5: West Div. (Frog, Revesed)
R3: 10 Ohms
R4, R5: 10K Ohms
R6, R7: 60 Ohms
U7, U9: TRS202E
U8: SN75LBC179
U10: 74LV125AN

Connections:
+3.3V: C12.1, R4.1, R5.2, U10.14 (VCC); also elsewhere on the board
+5V: C6.1, C11.1, C14.1, U7.16 (Vcc), U8.1 (Vcc), U9.16 (Vcc); also elsewhere on the board
/Sensors/East (Points) Occ: U10.6 (O); also elsewhere on the board
/Sensors/East (Points) Occ_: U7.9 (ROUT2), U10.5 (D)
/Sensors/Occupancy: IC1.6, IC1.7, R5.1, U7.10 (DIN2), U7.11 (DIN1), U9.10 (DIN2), U9.11 (DIN1); also elsewhere on the board
/Sensors/RX: U10.3 (O); also elsewhere on the board
/Sensors/RX_: U8.2 (R), U10.2 (D)
/Sensors/TX: R4.2, U8.3 (D); also elsewhere on the board
/Sensors/West Diverg (Frog Reversed) Occ: U10.11 (O); also elsewhere on the board
/Sensors/West Diverg (Frog Reversed) Occ_: U9.9 (ROUT2), U10.12 (D)
/Sensors/West Main (Frog Normal) Occ: U10.8 (O); also elsewhere on the board
/Sensors/West Main (Frog Normal) Occ_: U7.12 (ROUT1), U10.9 (D)
GND: C3.2, C5.2, C6.2, C8.2, C10.2, C11.2, C12.2, C14.2, IC1.5, IC1.8, P2.1, P2.4, P3.1, P3.4, P4.5, P5.1, P5.4, U7.15 (GND), U8.4 (GND), U9.15 (GND), U10.1 (E), U10.4 (E), U10.7 (GND), U10.10 (E), U10.13 (E); also elsewhere on the board
unnamed: P2.2, U7.7 (DOUT2)
unnamed: P3.3, U7.14 (DOUT1)
unnamed: P5.2, U9.8 (RIN2)
unnamed: P3.2, U7.13 (RIN1)
unnamed: P2.3, U7.8 (RIN2)
unnamed: P5.3, U9.7 (DOUT2)
unnamed: C10.1, U9.6 (V-)
unnamed: C9.2, U9.5 (C2-)
unnamed: C8.1, U9.2 (V+)
unnamed: C7.2, U9.3 (C1-)
unnamed: C9.1, U9.4 (C2+)
unnamed: C7.1, U9.1 (C1+)
unnamed: D1.2, P1.1, R3.1
unnamed: D1.1 (+), D1.4 (-)
unnamed: IC1.1, IC1.3, R3.2
unnamed: D1.3, IC1.2, IC1.4, P1.2 (PM)
unnamed: P4.1, R6.2, U8.5 (Y)
unnamed: C5.1, U7.6 (V-)
unnamed: C4.1, U7.4 (C2+)
unnamed: C2.1, U7.1 (C1+)
unnamed: C4.2, U7.5 (C2-)
unnamed: C3.1, U7.2 (V+)
unnamed: C2.2, U7.3 (C1-)
unnamed: P4.3, R7.2, U8.7 (B)
unnamed: P4.4, R7.1, U8.8 (A)
unnamed: P4.2, R6.1, U8.6 (Z)
