RobertPHeller/RPi-RRCircuits/RPiHalfSiding/RPiHalfSiding.kicad_pcb

## KiCad design RPiHalfSiding/RPiHalfSiding.kicad_pcb (continued)

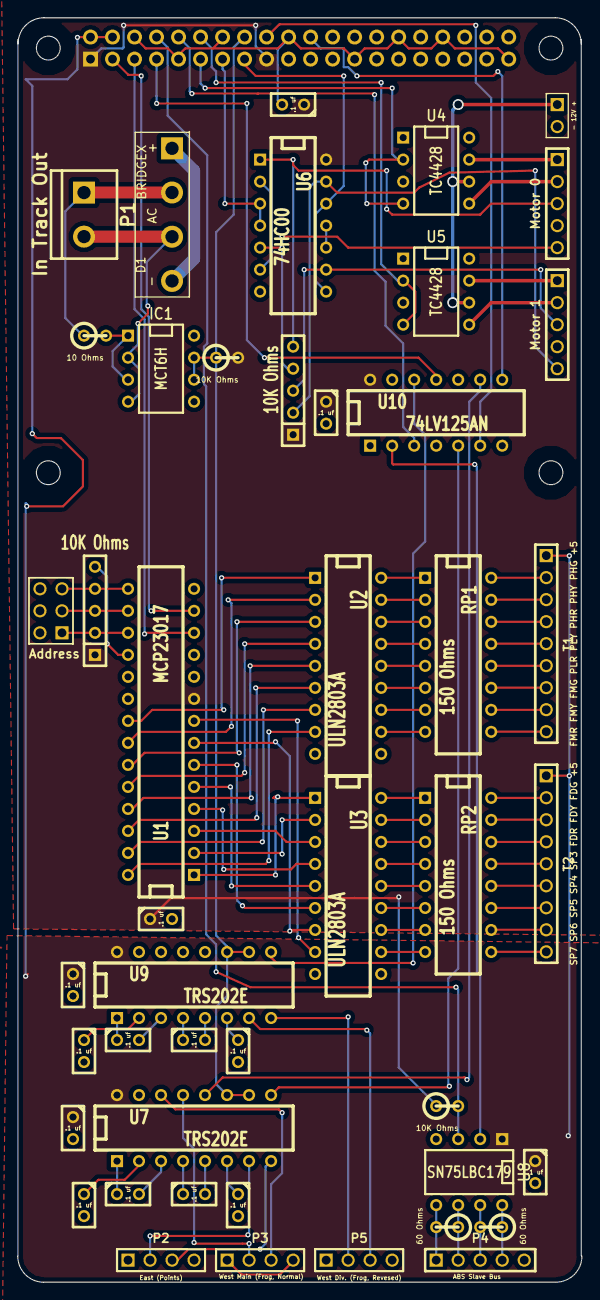
[picture p142: board RPiHalfSiding.kicad_pcb from above]

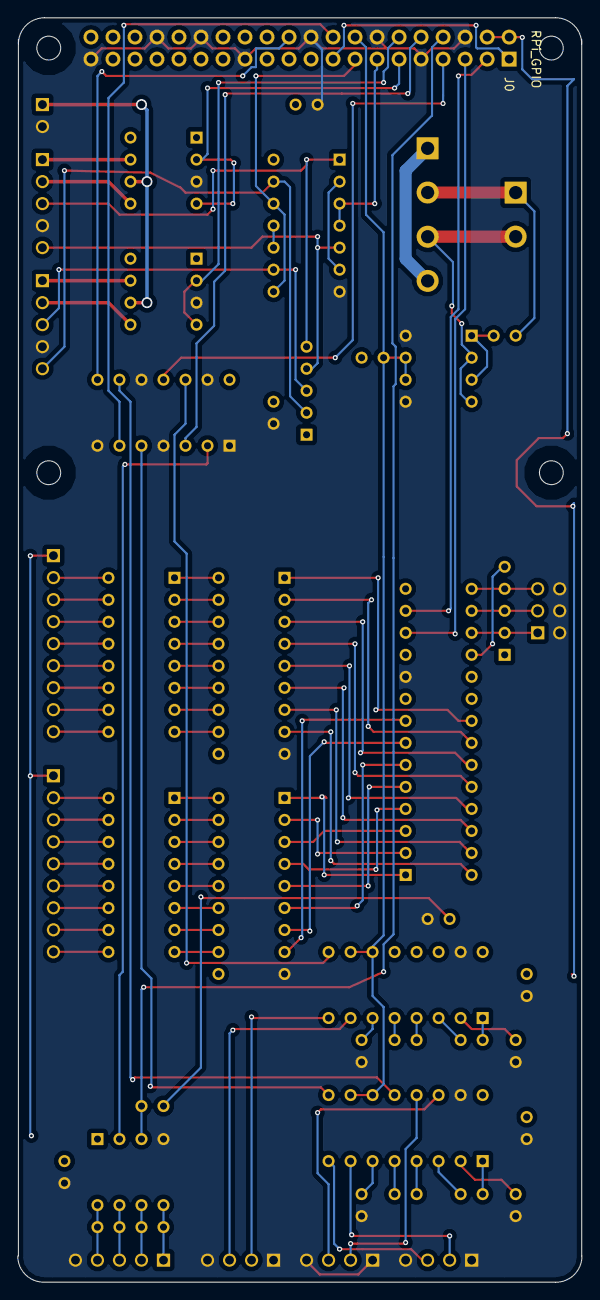
[picture p143: board RPiHalfSiding.kicad_pcb from below]

Board: 2 copper layers, 65.1 x 145.9 mm, 51 parts (5 on the bottom side), 108 nets.

Other parts of the board:
H1, H2, H3, H4: RPi_Hat_Mounting_Hole
