RobertPHeller/RPi-RRCircuits/MetroMiniABSBiDir-noCANSlave/MetroMiniABSBiDir-noCANSlave.kicad_pcb

## KiCad design MetroMiniABSBiDir-noCANSlave/MetroMiniABSBiDir-noCANSlave.kicad_pcb (2018-08-21)

Schematic: MetroMiniABSBiDir-noCANSlave.sch

Parts:
C1, C2, C3, C4: .1 uf
C5: .1 uf; Mouser Part Number 581-SR295E104MAA
CON1: 7-12 V Power Bus; Mouser Part Number 490-PJ-037A
D1: BRIDGE; Mouser Part Number 750-KBL401-G
D2: DIODESCH; Mouser Part Number SB240-E3/54
IC1: MCT6H; DIP-8__300; Mouser Part Number 782-MCT6H
P1: In Track Out; Mouser Part Number 710-691249510002
P2: +5V EG EY ER WG WY WR GND; Mouser Part Number 651-1725711
P3: Next East
P4, P6: ABS Slave Bus
P5: Next West
R1: 10 Ohms; Mouser Part Number 660-MF1/4LCT52R100J
R2: 10K Ohms; Mouser Part Number 660-MF1/4LCT52R103J
R3, R4, R5, R6, R7, R8: 150 Ohms; Mouser Part Number 660-MF1/4LCT52R151J
SW1: BC CA 0 1 2 3 4 5
T1: - 7-12V +
U1: METROMINI
U2: SN75LBC179; Mouser Part Number 595-SN75LBC179P
U3: TRS202E; Mouser Part Number 595-TRS202ECN

Connections:
+5V: C5.1, P2.1, R2.1, U1.25 (5V), U2.1 (Vcc), U3.16 (Vcc)
/East Green: P2.2, R8.1
/East Red: P2.4, R6.1
/East Yellow: P2.3, R7.1
/West Green: P2.5, R5.1
/West Red: P2.7, R3.1
/West Yellow: P2.6, R4.1
GND: C2.2, C4.2, C5.2, CON1.2, IC1.5, IC1.8, P2.8, P3.1, P3.4, P4.5, P5.1, P5.4, P6.5, SW1.1, SW1.2, SW1.3, SW1.4, SW1.5, SW1.6, SW1.7, SW1.8, T1.2 (PM), U1.23 (GND), U1.24 (GND), U2.4 (GND), U3.15 (GND)
unnamed: P3.2, U3.8 (RIN2)
unnamed: P5.2, U3.14 (DOUT1)
unnamed: P5.3, U3.13 (RIN1)
unnamed: P3.3, U3.7 (DOUT2)
unnamed: U1.13 (#1), U2.3 (D)
unnamed: U1.14 (#0), U2.2 (R)
unnamed: P4.4, P6.4, U2.5 (Y)
unnamed: C1.1, U3.1 (C1+)
unnamed: C3.1, U3.4 (C2+)
unnamed: C3.2, U3.5 (C2-)
unnamed: C1.2, U3.3 (C1-)
unnamed: C4.1, U3.6 (V-)
unnamed: C2.1, U3.2 (V+)
unnamed: U1.10 (#4), U3.12 (ROUT1)
unnamed: U1.7 (#7), U3.9 (ROUT2)
unnamed: SW1.12, U1.18 (A2)
unnamed: SW1.11, U1.17 (A3)
unnamed: SW1.10, U1.16 (A4)
unnamed: SW1.9, U1.15 (A5)
unnamed: SW1.13, U1.19 (A1)
unnamed: SW1.16, U1.2 (#12)
unnamed: SW1.15, U1.12 (#2)
unnamed: SW1.14, U1.20 (A0)
unnamed: CON1.1, D2.1 (A), T1.1
unnamed: P4.2, P6.2, U2.7 (B)
unnamed: P4.3, P6.3, U2.6 (Z)
unnamed: P4.1, P6.1, U2.8 (A)
unnamed: D1.1 (+), D1.4 (-)
unnamed: R8.2, U1.11 (#3)
unnamed: R4.2, U1.4 (#10)
unnamed: R3.2, U1.3 (#11)
unnamed: D2.2 (K), U1.22 (Vin)
unnamed: R7.2, U1.9 (#5)
unnamed: R6.2, U1.8 (#6)
unnamed: R5.2, U1.5 (#9)
unnamed: D1.3, P1.1, R1.1
unnamed: IC1.6, IC1.7, R2.2, U1.6 (#8), U3.10 (DIN2), U3.11 (DIN1)
unnamed: D1.2, IC1.2, IC1.4, P1.2 (PM)
unnamed: IC1.1, IC1.3, R1.2

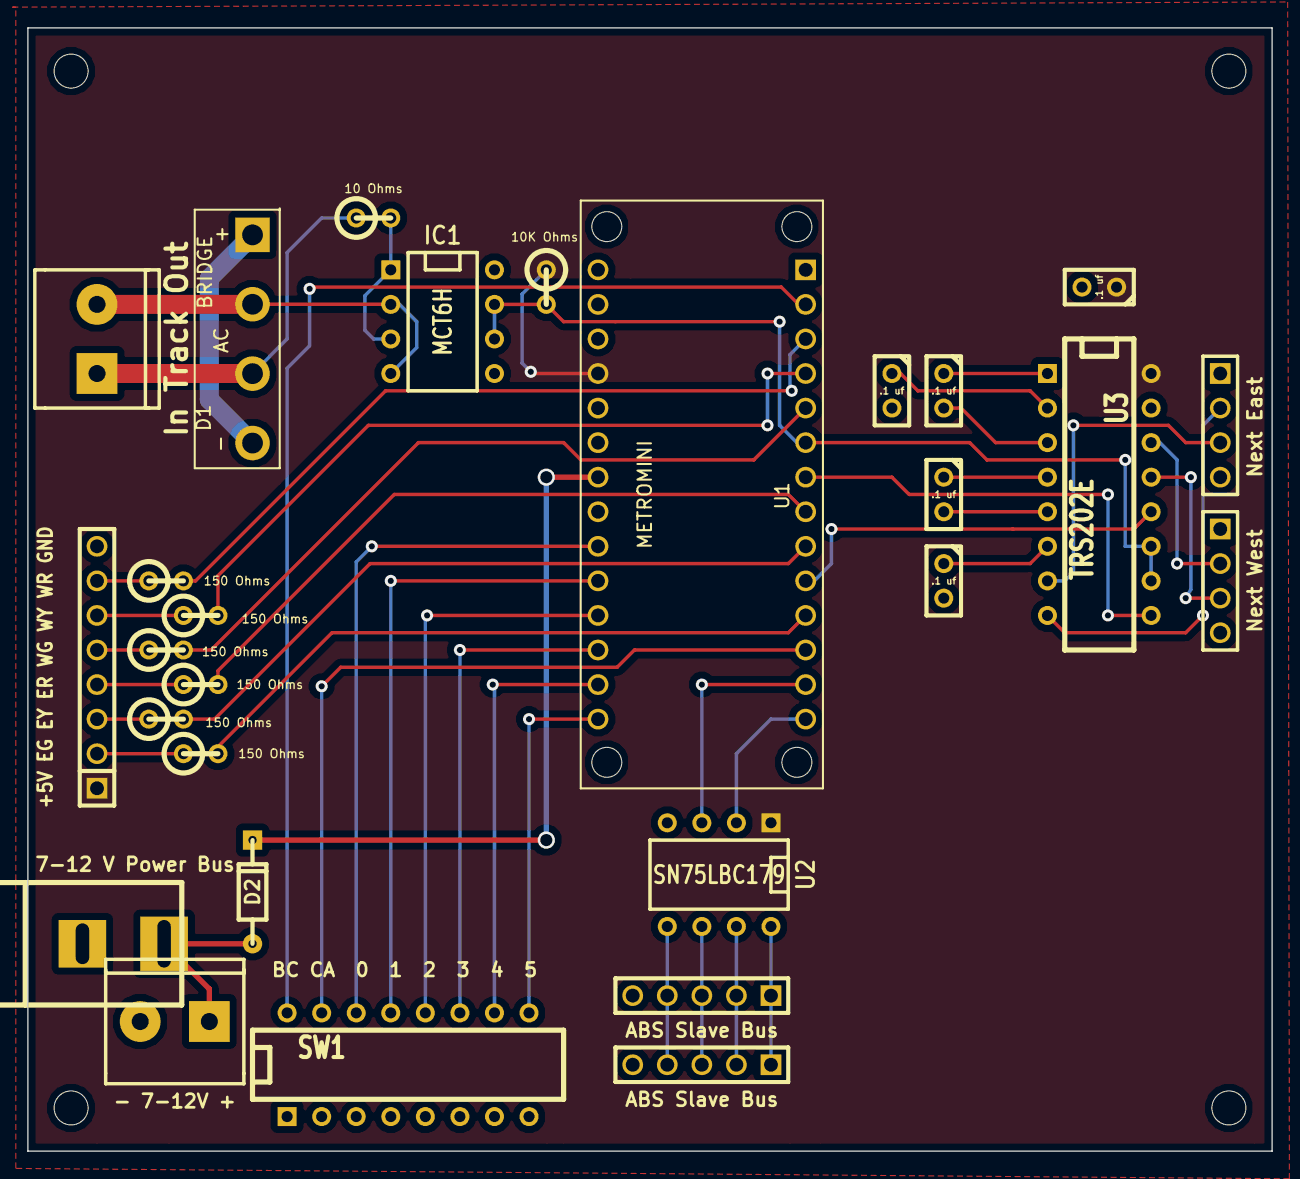
[picture p144: board MetroMiniABSBiDir-noCANSlave.kicad_pcb from above]

Board: 2 copper layers, 91.4 x 82.5 mm, 32 parts (0 on the bottom side), 47 nets.

Other parts of the board:
MH: MountingHole_2-5mm_RevA_Date21Jun2010
MH#2, MH#3, MH#4: MountingHole_2-5mm_RevA_Date21Jun2010
