RobertPHeller/RPi-RRCircuits/STM32ShieldForMetroMiniSlaves/STM32ShieldForMetroMiniSlaves.kicad_pcb

## KiCad design STM32ShieldForMetroMiniSlaves/STM32ShieldForMetroMiniSlaves.kicad_pcb (2018-08-01)

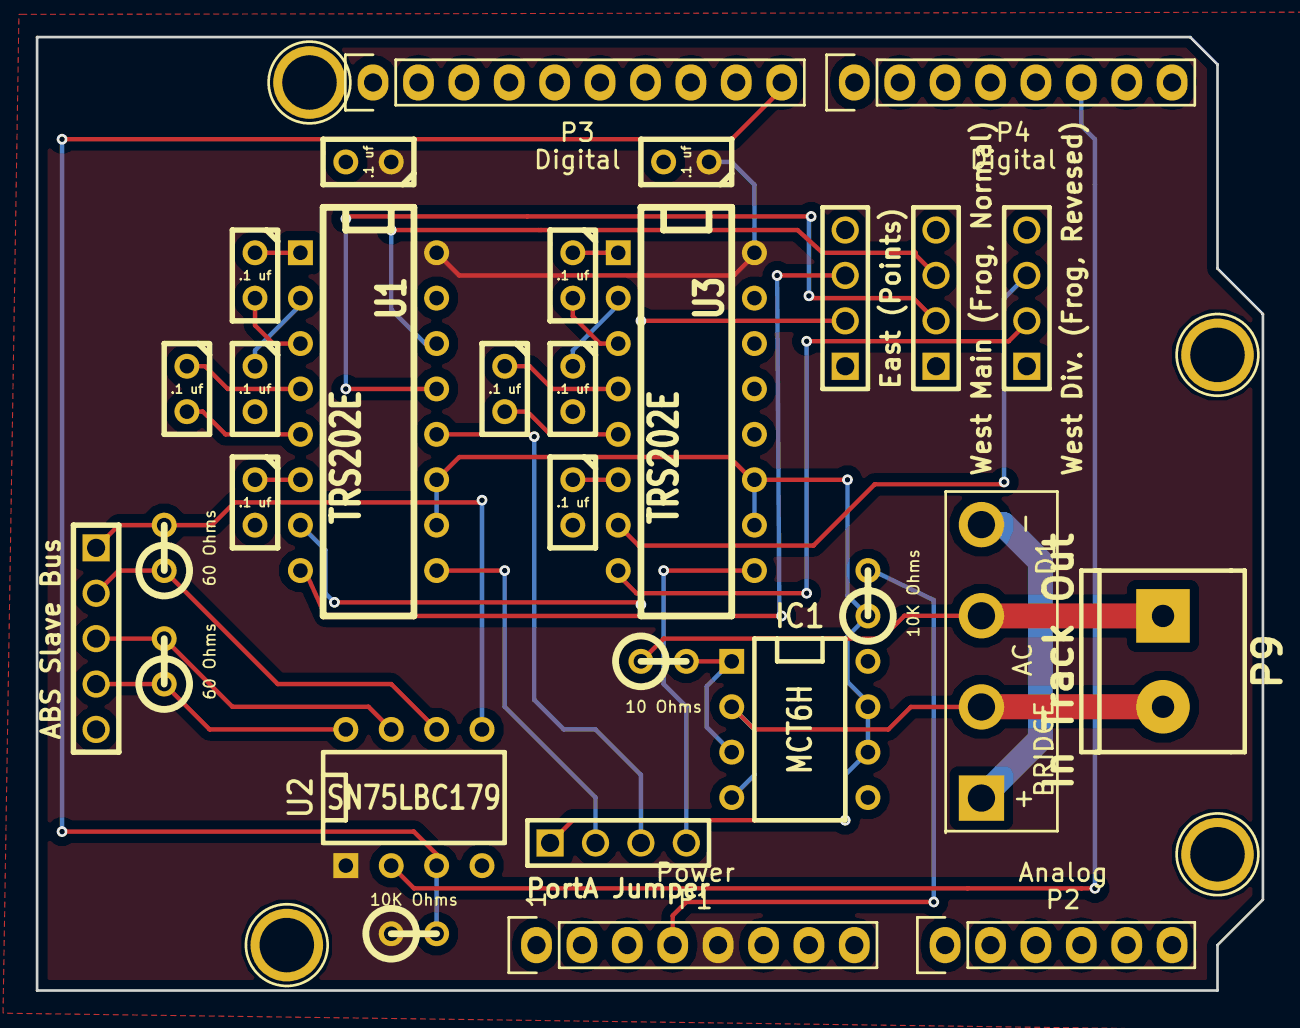
[picture p145: board STM32ShieldForMetroMiniSlaves.kicad_pcb from above]

Board: 2 copper layers, 68.6 x 53.3 mm, 34 parts (0 on the bottom side), 35 nets.

Parts:
C1, C2, C3, C4, C5, C6, C7, C8, C9, C10: .1 uf; C1
D1: BRIDGE; KBL
IC1: MCT6H; DIP-8__300
P1: Power; Socket_Strip_Arduino_1x08
P2: Analog; Socket_Strip_Arduino_1x06
P3: Digital; Socket_Strip_Arduino_1x10
P4: Digital; Socket_Strip_Arduino_1x08
P5, P6, P7, P8: CONN_01X01; Arduino_1pin
P9: In Track Out; mors_2p
P10: East (Points); PIN_ARRAY_4x1
P11: West Main (Frog, Normal); PIN_ARRAY_4x1
P12: ABS Slave Bus; PIN_ARRAY_5x1
P13: West Div. (Frog, Revesed); PIN_ARRAY_4x1
P14: PortA Jumper; PIN_ARRAY_4x1
R1: 10 Ohms; R1
R2, R5: 10K Ohms; R1
R3, R4: 60 Ohms; R1
U1, U3: TRS202E; DIP-16__300
U2: SN75LBC179; DIP-8__300

Connections:
+3.3V: P1.4, R2.2
+5V: C5.1, C10.1, P1.5, R5.1, U1.16, U2.1, U3.16
/2: P4.6, U2.2
/8: P3.10, R5.2, U2.3
/PortA 5: IC1.6, IC1.7, P14.1, R2.1, U1.10, U1.11, U3.10, U3.11
/PortA 6: P14.2, U1.9
/PortA 7: P14.3, U1.12
/PortA 8: P14.4, U3.9
GND: C2.2, C4.2, C5.2, C7.2, C9.2, C10.2, IC1.5, IC1.8, P1.6, P1.7, P3.4, P10.1, P10.4, P11.1, P11.4, P12.5, P13.1, P13.4, U1.15, U2.4, U3.15
unnamed: D1.3, P9.1, R1.1
unnamed: D1.1, D1.4
unnamed: C3.1, U1.4
unnamed: C1.1, U1.1
unnamed: C4.1, U1.6
unnamed: D1.2, IC1.2, IC1.4, P9.2
unnamed: IC1.1, IC1.3, R1.2
unnamed: C3.2, U1.5
unnamed: C2.1, U1.2
unnamed: C1.2, U1.3
unnamed: P12.1, R3.2, U2.5
unnamed: P12.2, R3.1, U2.6
unnamed: P12.3, R4.2, U2.7
unnamed: P12.4, R4.1, U2.8
unnamed: P13.2, U3.8
unnamed: P11.2, U1.13
unnamed: P10.3, U1.8
unnamed: P13.3, U3.7
unnamed: P11.3, U1.14
unnamed: P10.2, U1.7
unnamed: C8.1, U3.4
unnamed: C6.1, U3.1
unnamed: C9.1, U3.6
unnamed: C8.2, U3.5
unnamed: C7.1, U3.2
unnamed: C6.2, U3.3
