RobertPHeller/RPi-RRCircuits/SPILEDDriverAddOn/SPILEDDriverAddOn.kicad_pcb

## KiCad design SPILEDDriverAddOn/SPILEDDriverAddOn.kicad_pcb (2018-08-01)

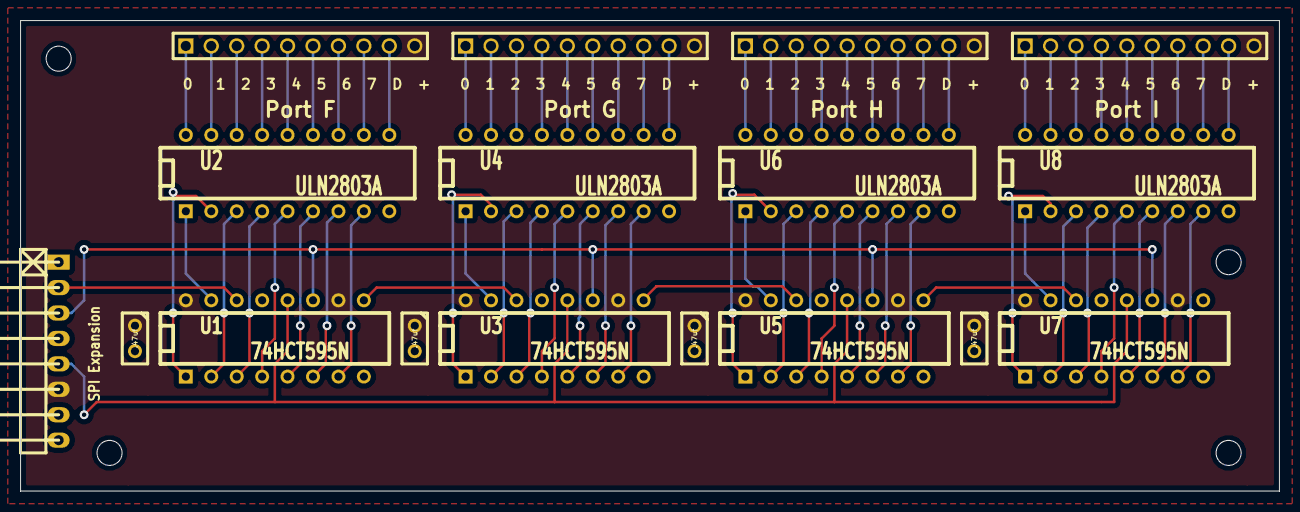
[picture p146: board SPILEDDriverAddOn.kicad_pcb from above]

Board: 2 copper layers, 125.7 x 47.0 mm, 21 parts (0 on the bottom side), 76 nets.

Parts:
C1, C2, C3, C4: .47uf; C1
MH: MountingHole_2-5mm_RevA_Date21Jun2010
MH#2, MH#3, MH#4: MountingHole_2-5mm_RevA_Date21Jun2010
P1: SPI Expansion; pin_strip_8-90
P2, P3, P4, P5: 0 1 2 3 4 5 6 7 D +; ScrewTerm_2.54-10
U1, U3, U5, U7: 74HCT595N; DIP-16__300
U2, U4, U6, U8: ULN2803A; DIP-18__300

Connections:
+5V: C1.1, C2.1, C3.1, C4.1, P1.6, P2.10, P3.10, P4.10, P5.10, U1.10, U1.16, U3.10, U3.16, U5.10, U5.16, U7.10, U7.16
/Port F/Diode Up: P2.9, U2.10
/Port F/OLAT: P1.5, U1.12, U3.12, U5.12, U7.12
/Port F/SCK: P1.3, U1.11, U3.11, U5.11, U7.11
/Port F/Serial In: P1.2, U1.14
/Port G/Diode Up: P3.9, U4.10
/Port G/Serial In: U1.9, U3.14
/Port H/Diode Up: P4.9, U6.10
/Port H/Serial In: U3.9, U5.14
/Port I/Diode Up: P5.9, U8.10
/Port I/Serial In: U5.9, U7.14
GND: C1.2, C2.2, C3.2, C4.2, P1.8, U1.8, U1.13, U2.9, U3.8, U3.13, U4.9, U5.8, U5.13, U6.9, U7.8, U7.13, U8.9
unnamed: P2.4, U2.15
unnamed: P2.3, U2.16
unnamed: P2.2, U2.17
unnamed: P2.1, U2.18
unnamed: P2.5, U2.14
unnamed: P2.6, U2.13
unnamed: P2.7, U2.12
unnamed: U1.6, U2.7
unnamed: U1.7, U2.8
unnamed: P2.8, U2.11
unnamed: U1.3, U2.4
unnamed: U1.5, U2.6
unnamed: U1.1, U2.2
unnamed: U1.2, U2.3
unnamed: U1.4, U2.5
unnamed: U1.15, U2.1
unnamed: P3.2, U4.17
unnamed: P3.3, U4.16
unnamed: P3.4, U4.15
unnamed: P3.5, U4.14
unnamed: P3.6, U4.13
unnamed: U3.6, U4.7
unnamed: U3.7, U4.8
unnamed: P3.1, U4.18
unnamed: P3.7, U4.12
unnamed: P3.8, U4.11
unnamed: U3.3, U4.4
unnamed: U3.5, U4.6
unnamed: U3.1, U4.2
unnamed: U3.2, U4.3
unnamed: U3.4, U4.5
unnamed: U3.15, U4.1
unnamed: P4.1, U6.18
unnamed: P4.2, U6.17
unnamed: P4.3, U6.16
unnamed: P4.4, U6.15
unnamed: P4.5, U6.14
unnamed: P4.6, U6.13
unnamed: P4.7, U6.12
unnamed: U5.6, U6.7
unnamed: U5.7, U6.8
unnamed: P4.8, U6.11
unnamed: U5.3, U6.4
unnamed: U5.5, U6.6
unnamed: U5.1, U6.2
unnamed: U5.2, U6.3
unnamed: U5.4, U6.5
unnamed: U5.15, U6.1
unnamed: P5.1, U8.18
unnamed: P5.2, U8.17
unnamed: P5.3, U8.16
unnamed: P5.4, U8.15
unnamed: P5.5, U8.14
unnamed: P5.6, U8.13
unnamed: P5.7, U8.12
unnamed: U7.6, U8.7
unnamed: U7.7, U8.8
unnamed: P5.8, U8.11
unnamed: U7.3, U8.4
unnamed: U7.5, U8.6
unnamed: U7.1, U8.2
unnamed: U7.2, U8.3
unnamed: U7.4, U8.5
unnamed: U7.15, U8.1
