RobertPHeller/RPi-RRCircuits/MetroMiniABS2-bidir/MetroMiniABS2-bidir.kicad_pcb

## KiCad design MetroMiniABS2-bidir/MetroMiniABS2-bidir.kicad_pcb (2018-06-10)

Schematic: MetroMiniABS2-bidir.sch

Parts:
C1, C2: 22 pf; Mouser Part Number 581-SR151A220KAR
C3: .1 uf; Mouser Part Number 21RZ310-RC
C4: 47 nf; Mouser Part Number 75-1C10Z5U473M050B
C5: .1 uf
CON1: PJ_037A
D1, D2: SB240-E3/54; Mouser Part Number 625-SB240-E3
D3: KBL 401-G; Mouser Part Number 750-KBL401-G
D4: Blue; Mouser Part Number 859-LTL17KTBS3KS
D5: Gold; Mouser Part Number 859-LTL-4251N
IC1: MCT6H; DIP-8__300; Mouser Part Number 782-MCT6H
J1, J2: RJ45; Mouser Part Number 710-615008144221
JP1: JUMPER
P1: Termination; Mouser Part Number 855-M20-9980246
P2: + 12V (IN) -; Mouser Part Number 710-691249510002
P3: In Track Out; Mouser Part Number 710-691249510002
P4: +5 WR WY WG ER EY EG +5
P5: - 12V (out) +; Mouser Part Number 782-MCT6H
R1, R6, R7, R8, R13, R14: 330 Ohms
R2, R3: 60 Ohms; Mouser Part Number 71-RN60C60R0B/R
R4: 10 Ohms; Mouser Part Number 782-MCT6H
R5: 10K Ohms; Mouser Part Number 782-MCT6H
R9, R10: 1K Ohms; Mouser Part Number 660-MF1/4LCT52R102J
R11, R12: 510 Ohms; Mouser Part Number 660-MF1/4LCT52R511J
R15: 10K Ohms
SW1: Blue; Mouser Part Number 506-FSM4JH
SW2: Gold; Mouser Part Number 506-FSM4JH
U1: METROMINI
U2: MCP2517; DIL-18_300
U3: MCP2551; DIL-8_300; Mouser Part Number 579-MCP2551-I/P
U4: TLC59208F
X1: 20 Mhz; Mouser Part Number 449-LFXTAL027945BULK

Connections:
+5V: C3.1, C5.1, P4.1, P4.8, R5.1, R9.1, R10.1, R15.2, U1.25 (5V), U2.14 (Vcc), U3.3 (Vcc), U3.5 (Vref), U4.16 (Vdd)
/East Green: P4.2, R1.1
/East Red: P4.4, R7.1
/East Yellow: P4.3, R6.1
/West Green: P4.5, R8.1
/West Red: P4.7, R14.1
/West Yellow: P4.6, R13.1
CS: U1.4 (#10), U2.13 (CS)
GND: C1.1, C2.1, C3.2, C4.2, C5.2, CON1.2, IC1.5, IC1.8, J1.3, J1.6, J1.7, J2.3, J2.6, J2.7, P2.2 (PM), P5.2 (PM), SW1.2, SW2.2, U1.23 (GND), U1.24 (GND), U2.7 (GND), U3.2 (GND), U3.8 (Rs), U4.1 (A0), U4.2 (A1), U4.3 (A2), U4.8 (Gnd)
INT: U1.5 (#9), U2.4 (INT)
MISO: U1.2 (#12), U2.12 (SO)
MOSI: U1.3 (#11), U2.11 (SI)
unnamed: IC1.6, IC1.7, R5.2, U1.6 (#8)
unnamed: IC1.1, IC1.3, R4.2
unnamed: CON1.1, D2.1 (A), P2.1
unnamed: D4.2 (K), R11.1, U1.10 (#4)
unnamed: D5.2 (K), R12.1, U1.7 (#7)
unnamed: D5.1 (A), R10.2
unnamed: D4.1 (A), R9.2
unnamed: R12.2, SW2.1
unnamed: R11.2, SW1.1
unnamed: D1.1 (A), D2.2 (K), JP1.2, P5.1
unnamed: J1.8, J2.8, JP1.1
unnamed: J1.5, J2.5
unnamed: J1.4, J2.4
unnamed: D3.2, IC1.2, IC1.4, P3.2 (PM)
unnamed: D3.3, P3.1, R4.1
unnamed: D3.1 (+), D3.4 (-)
unnamed: C4.1, P1.3, P1.4
unnamed: P1.2, R3.2
unnamed: P1.1, R2.2
unnamed: R14.2, U4.10 (Out5)
unnamed: R13.2, U4.9 (Out4)
unnamed: R8.2, U4.7 (Out3)
unnamed: R7.2, U4.6 (Out2)
unnamed: R6.2, U4.5 (Out1)
unnamed: R1.2, U4.4 (Out0)
unnamed: R15.1, U4.13 (Reset)
unnamed: J1.2, J2.2, R3.1, U3.6 (CANL)
unnamed: J1.1, J2.1, R2.1, U3.7 (CANH)
unnamed: C1.2, U2.6 (OSC1), X1.2
unnamed: C2.2, U2.5 (OSC2), X1.1
unnamed: U2.1 (TXCAN), U3.1 (TXD)
unnamed: U2.2 (RXCAN), U3.4 (RXD)
SCL: U1.15 (A5), U4.14 (SCL)
SCLK: U1.1 (#13), U2.10 (SCK)
SDA: U1.16 (A4), U4.15 (SDA)
Vin: D1.2 (K), U1.22 (Vin)

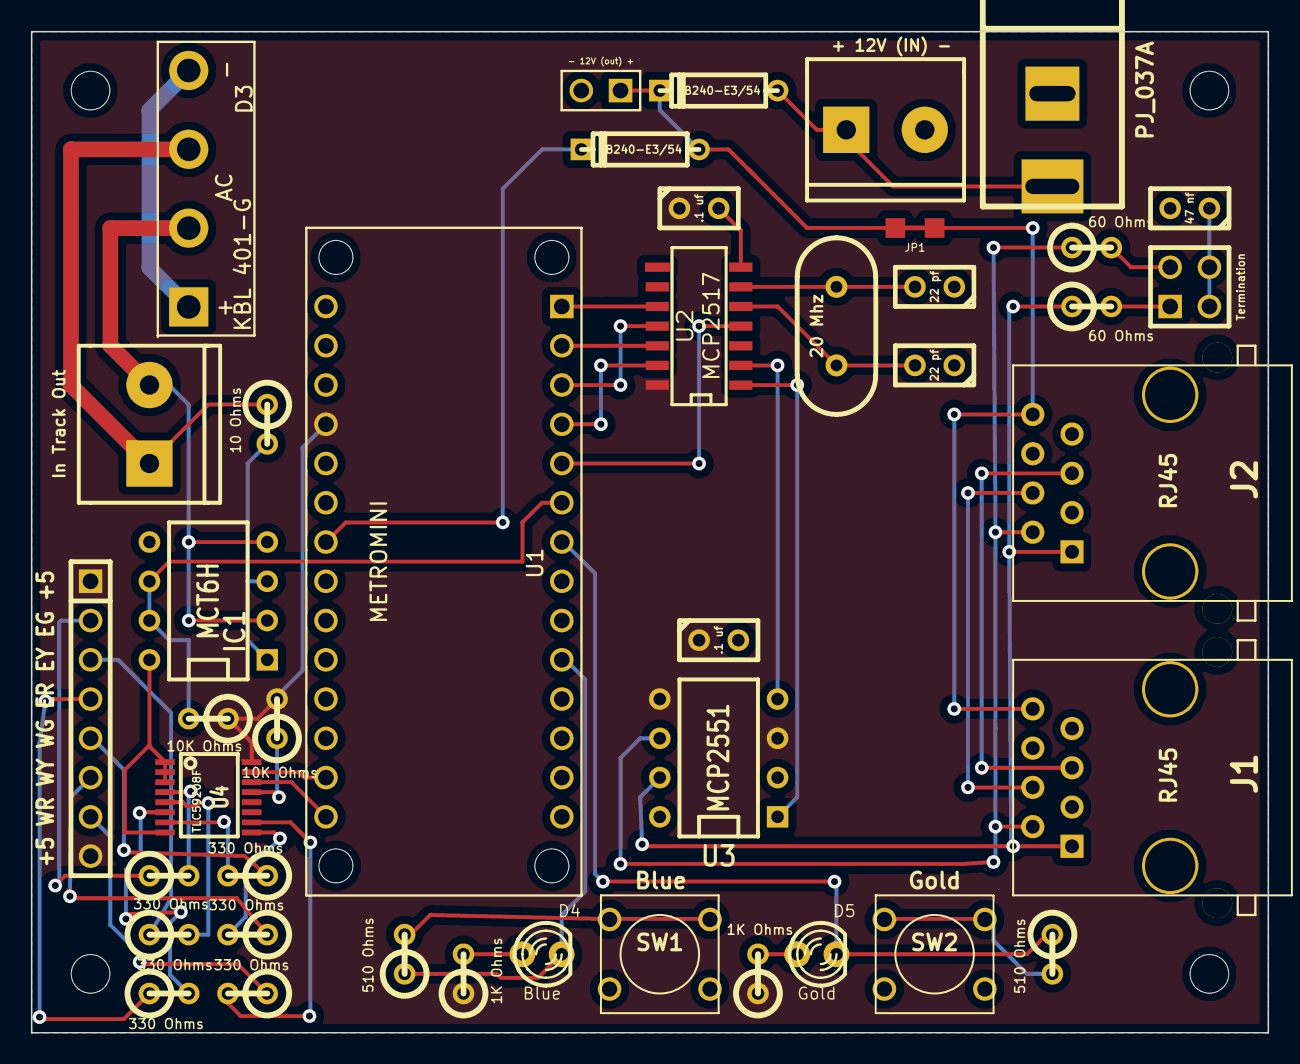
[picture p147: board MetroMiniABS2-bidir.kicad_pcb from above]

Board: 2 copper layers, 80.0 x 64.8 mm, 46 parts (0 on the bottom side), 48 nets.

Other parts of the board:
MH: MountingHole_2-5mm_RevA_Date21Jun2010
MH#2, MH#3, MH#4: MountingHole_2-5mm_RevA_Date21Jun2010
