RobertPHeller/RPi-RRCircuits/QuadSignalDriverCA/QuadSignalDriverCA.kicad_pcb

## KiCad design QuadSignalDriverCA/QuadSignalDriverCA.kicad_pcb (2018-05-23)

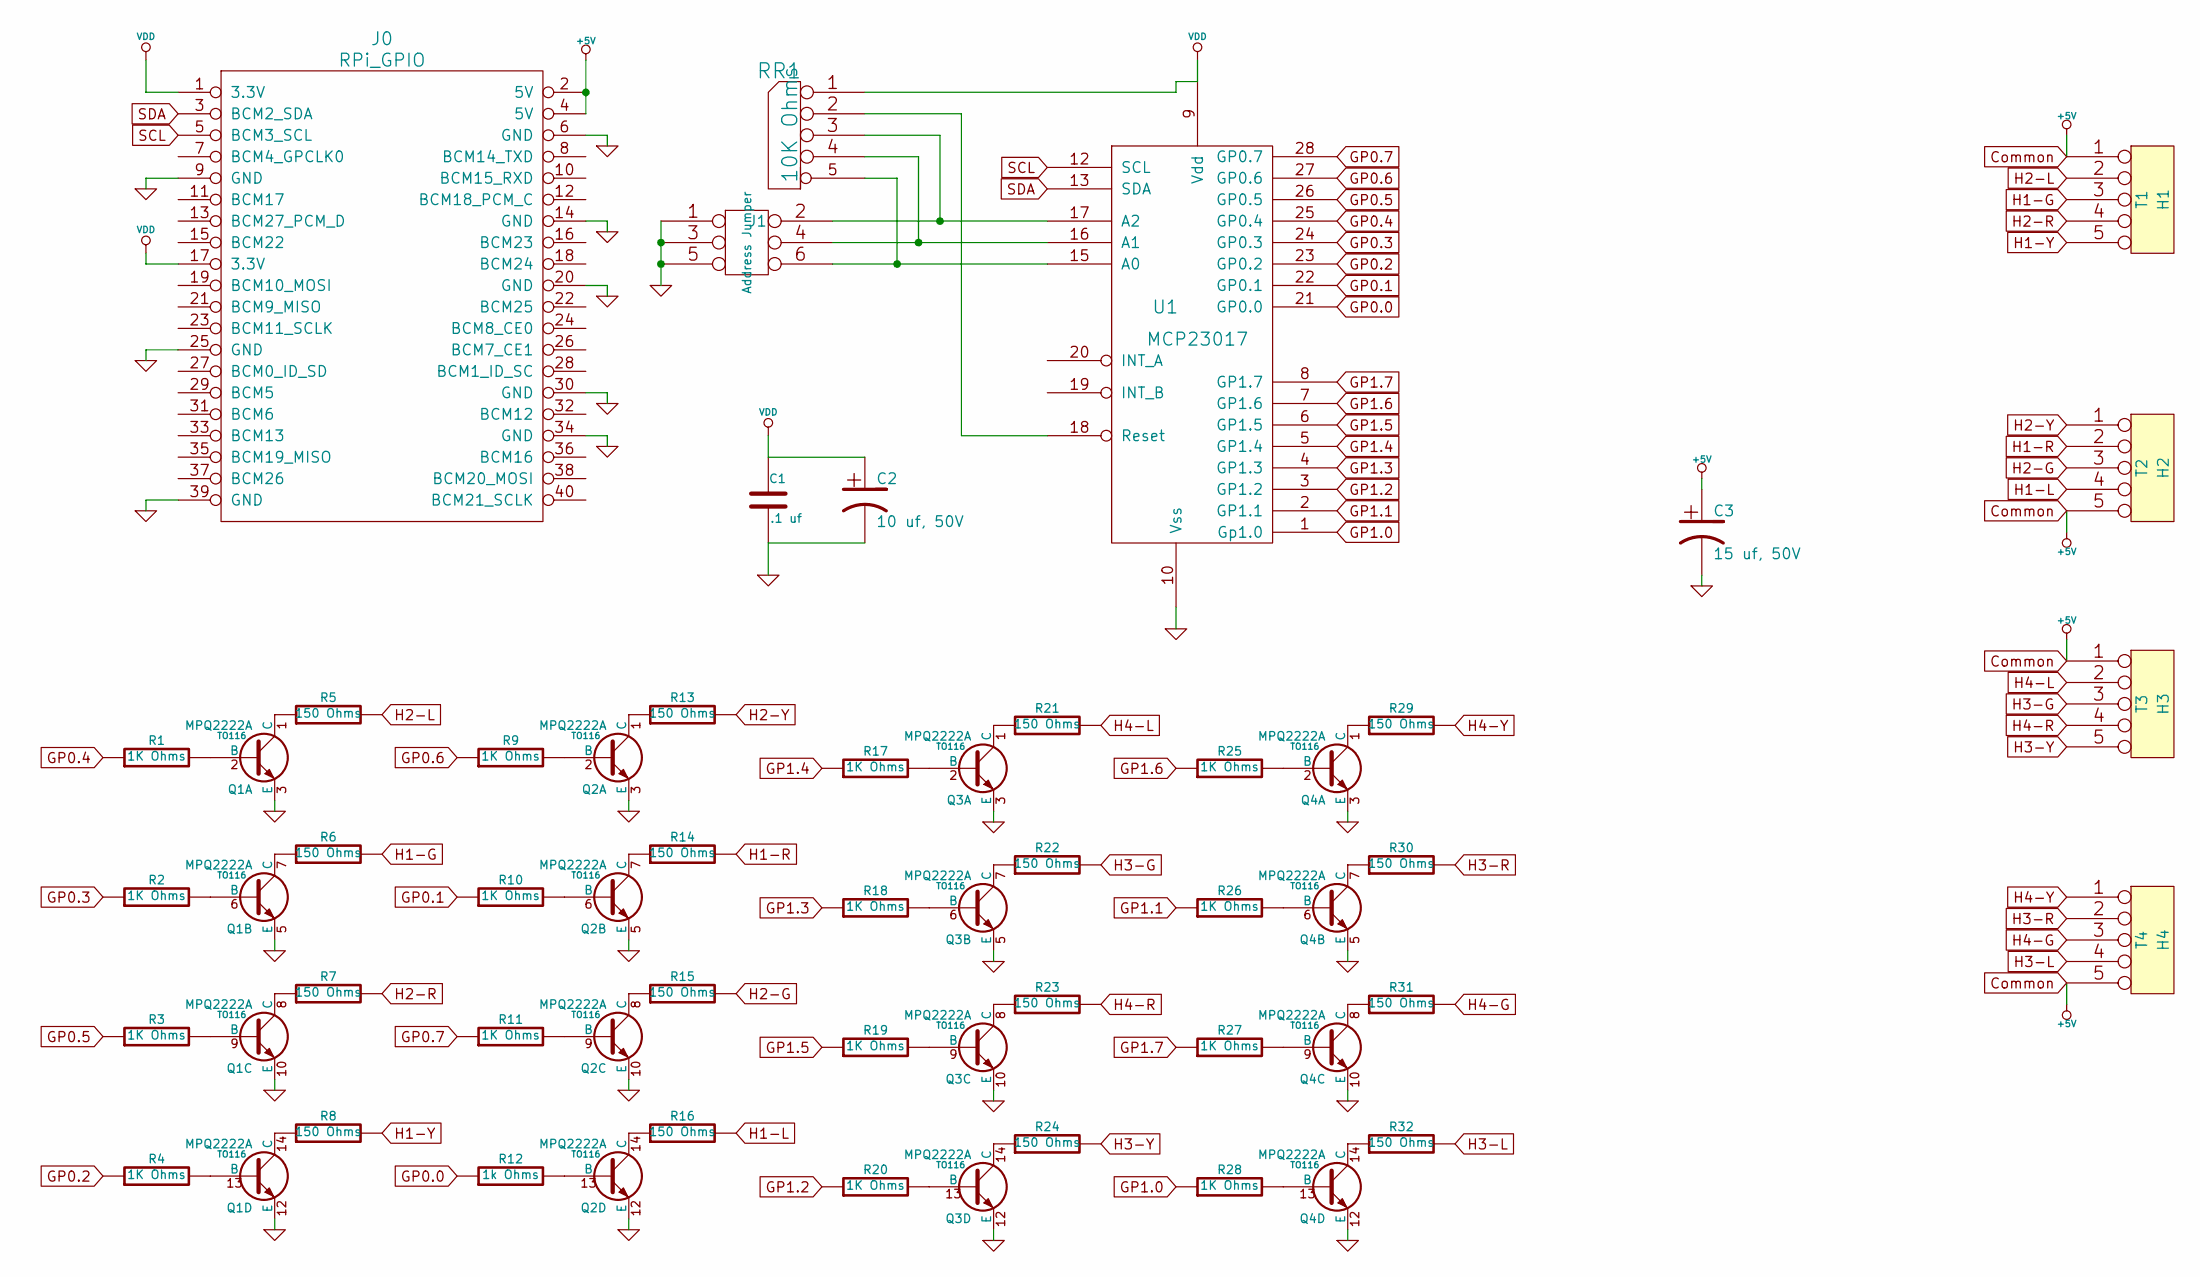
[picture p148: schematic QuadSignalDriverCA.sch]

Parts:
C1: .1 uf
C2: 10 uf, 50V
C3: 15 uf, 50V
J0: RPi_GPIO; Pin_Header_Straight_2x20
J1: Address Jumper
Q1, Q2, Q3, Q4: MPQ2222A; TO116
R1, R2, R3, R4, R9, R10, R11, R17, R18, R19, R20, R25, R26, R27, R28: 1K Ohms
R5, R6, R7, R8, R13, R14, R15, R16, R21, R22, R23, R24, R29, R30, R31, R32: 150 Ohms
R12: 1k Ohms
RR1: 10K Ohms
T1: H1
T2: H2
T3: H3
T4: H4
U1: MCP23017

Connections:
Common: C3.1, J0.2 (5V), J0.4 (5V), T1.1, T2.5, T3.1, T4.5
GND: C1.2, C2.2, C3.2, J0.6 (GND), J0.9 (GND), J0.14 (GND), J0.20 (GND), J0.25 (GND), J0.30 (GND), J0.34 (GND), J0.39 (GND), J1.1, J1.3, J1.5, Q1.3 (E), Q1.5 (E), Q1.10 (E), Q1.12 (E), Q2.3 (E), Q2.5 (E), Q2.10 (E), Q2.12 (E), Q3.3 (E), Q3.5 (E), Q3.10 (E), Q3.12 (E), Q4.3 (E), Q4.5 (E), Q4.10 (E), Q4.12 (E), U1.10 (Vss)
GP0.0: R12.1, U1.21 (GP0.0)
GP0.1: R10.1, U1.22 (GP0.1)
GP0.2: R4.1, U1.23 (GP0.2)
GP0.3: R2.1, U1.24 (GP0.3)
GP0.4: R1.1, U1.25 (GP0.4)
GP0.5: R3.1, U1.26 (GP0.5)
GP0.6: R9.1, U1.27 (GP0.6)
GP0.7: R11.1, U1.28 (GP0.7)
GP1.0: R28.1, U1.1 (Gp1.0)
GP1.1: R26.1, U1.2 (GP1.1)
GP1.2: R20.1, U1.3 (GP1.2)
GP1.3: R18.1, U1.4 (GP1.3)
GP1.4: R17.1, U1.5 (GP1.4)
GP1.5: R19.1, U1.6 (GP1.5)
GP1.6: R25.1, U1.7 (GP1.6)
GP1.7: R27.1, U1.8 (GP1.7)
H1-G: R6.2, T1.3
H1-L: R16.2, T2.4
H1-R: R14.2, T2.2
H1-Y: R8.2, T1.5
H2-G: R15.2, T2.3
H2-L: R5.2, T1.2
H2-R: R7.2, T1.4
H2-Y: R13.2, T2.1
H3-G: R22.2, T3.3
H3-L: R32.2, T4.4
H3-R: R30.2, T4.2
H3-Y: R24.2, T3.5
H4-G: R31.2, T4.3
H4-L: R21.2, T3.2
H4-R: R23.2, T3.4
H4-Y: R29.2, T4.1
unnamed: Q4.14 (C), R32.1
unnamed: Q4.13 (B), R28.2
unnamed: J1.6, RR1.5, U1.15 (A0)
unnamed: J1.4, RR1.4, U1.16 (A1)
unnamed: J1.2, RR1.3, U1.17 (A2)
unnamed: RR1.2, U1.18 (Reset)
unnamed: Q1.6 (B), R2.2
unnamed: Q1.7 (C), R6.1
unnamed: Q1.1 (C), R5.1
unnamed: Q1.2 (B), R1.2
unnamed: Q2.2 (B), R9.2
unnamed: Q2.1 (C), R13.1
unnamed: Q1.14 (C), R8.1
unnamed: Q1.13 (B), R4.2
unnamed: Q1.8 (C), R7.1
unnamed: Q1.9 (B), R3.2
unnamed: Q4.2 (B), R25.2
unnamed: Q4.1 (C), R29.1
unnamed: Q3.14 (C), R24.1
unnamed: Q3.13 (B), R20.2
unnamed: Q3.8 (C), R23.1
unnamed: Q3.9 (B), R19.2
unnamed: Q4.8 (C), R31.1
unnamed: Q4.9 (B), R27.2
unnamed: Q4.7 (C), R30.1
unnamed: Q4.6 (B), R26.2
unnamed: Q2.8 (C), R15.1
unnamed: Q2.9 (B), R11.2
unnamed: Q2.7 (C), R14.1
unnamed: Q2.6 (B), R10.2
unnamed: Q3.7 (C), R22.1
unnamed: Q3.6 (B), R18.2
unnamed: Q3.1 (C), R21.1
unnamed: Q3.2 (B), R17.2
unnamed: Q2.14 (C), R16.1
unnamed: Q2.13 (B), R12.2
SCL: J0.5 (BCM3_SCL), U1.12 (SCL)
SDA: J0.3 (BCM2_SDA), U1.13 (SDA)
VDD: C1.1, C2.1, J0.1 (3.3V), J0.17 (3.3V), RR1.1 (COM), U1.9 (Vdd)

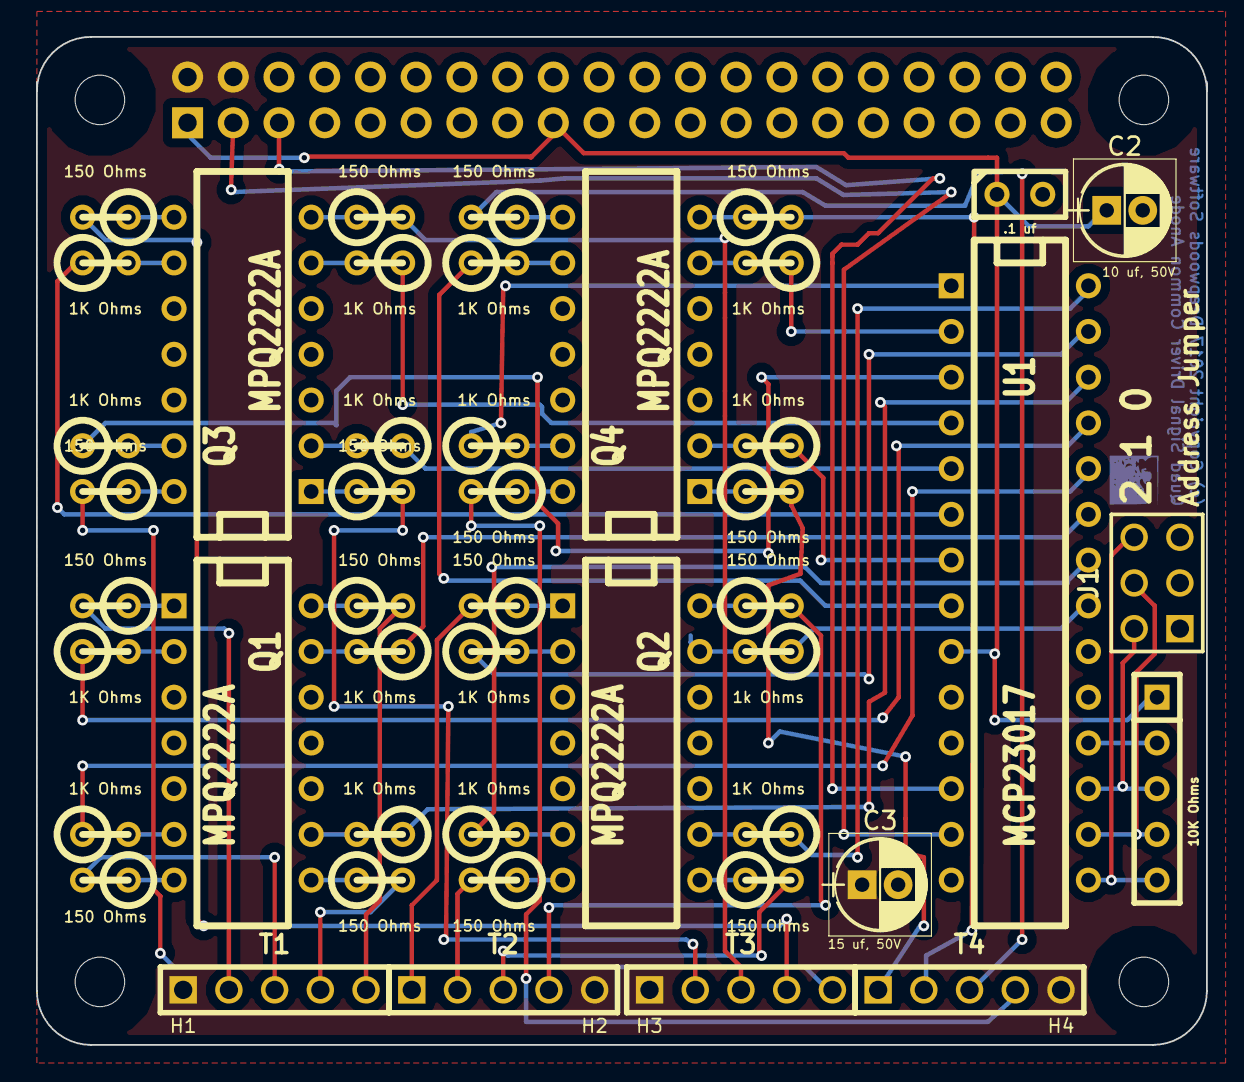
[picture p149: board QuadSignalDriverCA.kicad_pcb from above]

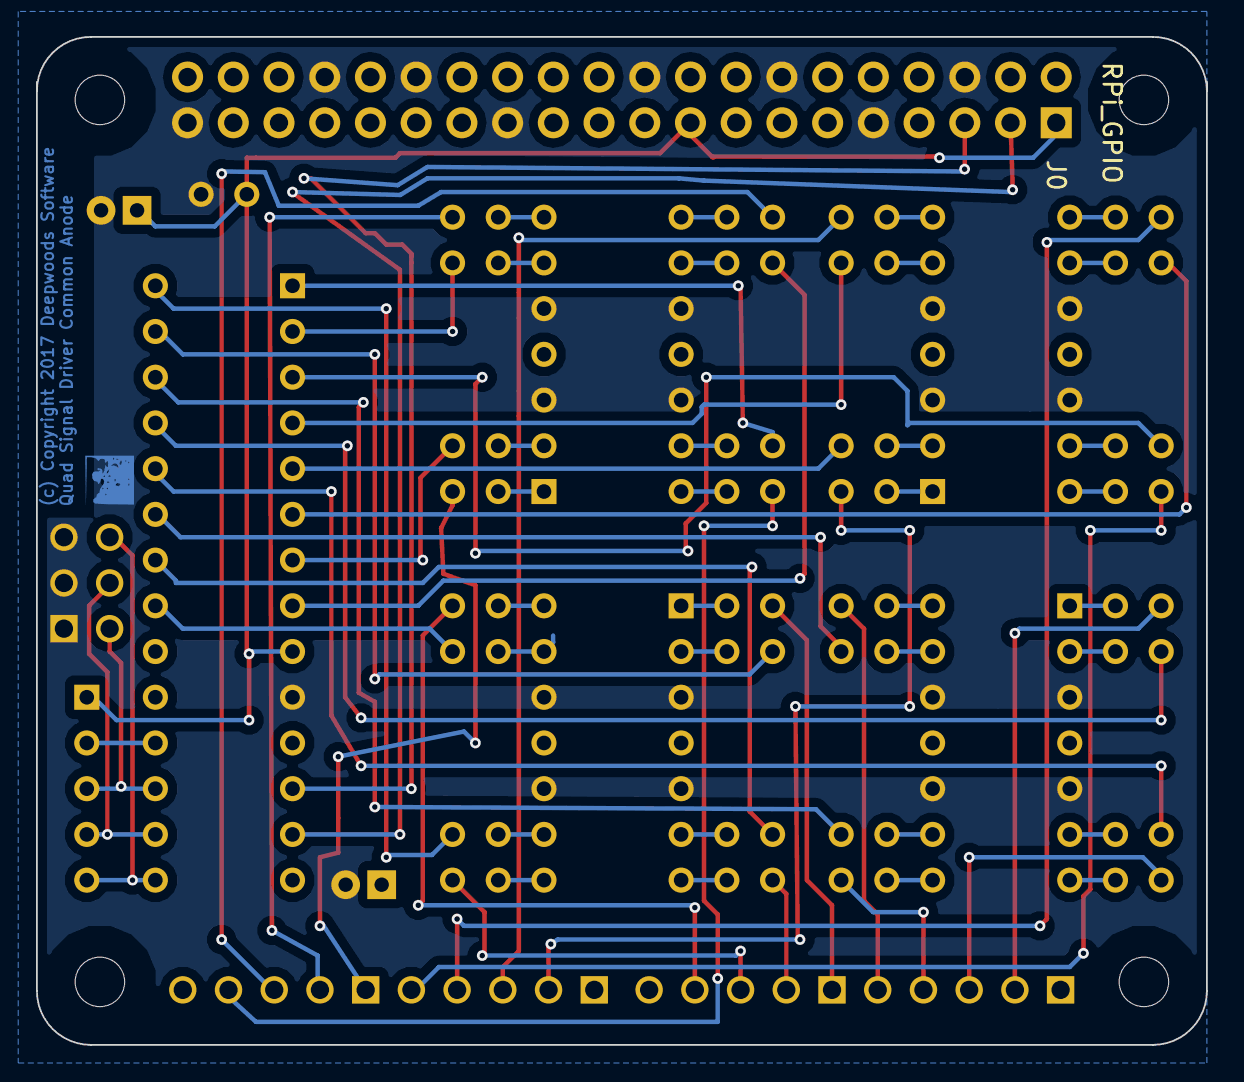
[picture p150: board QuadSignalDriverCA.kicad_pcb from below]

Board: 2 copper layers, 65.0 x 56.0 mm, 51 parts (5 on the bottom side), 73 nets.

Other parts of the board:
H1, H2, H3, H4: RPi_Hat_Mounting_Hole
