RobertPHeller/RPi-RRCircuits/CANHat3/CANHat3.kicad_pcb

## KiCad design CANHat3/CANHat3.kicad_pcb (2018-05-20)

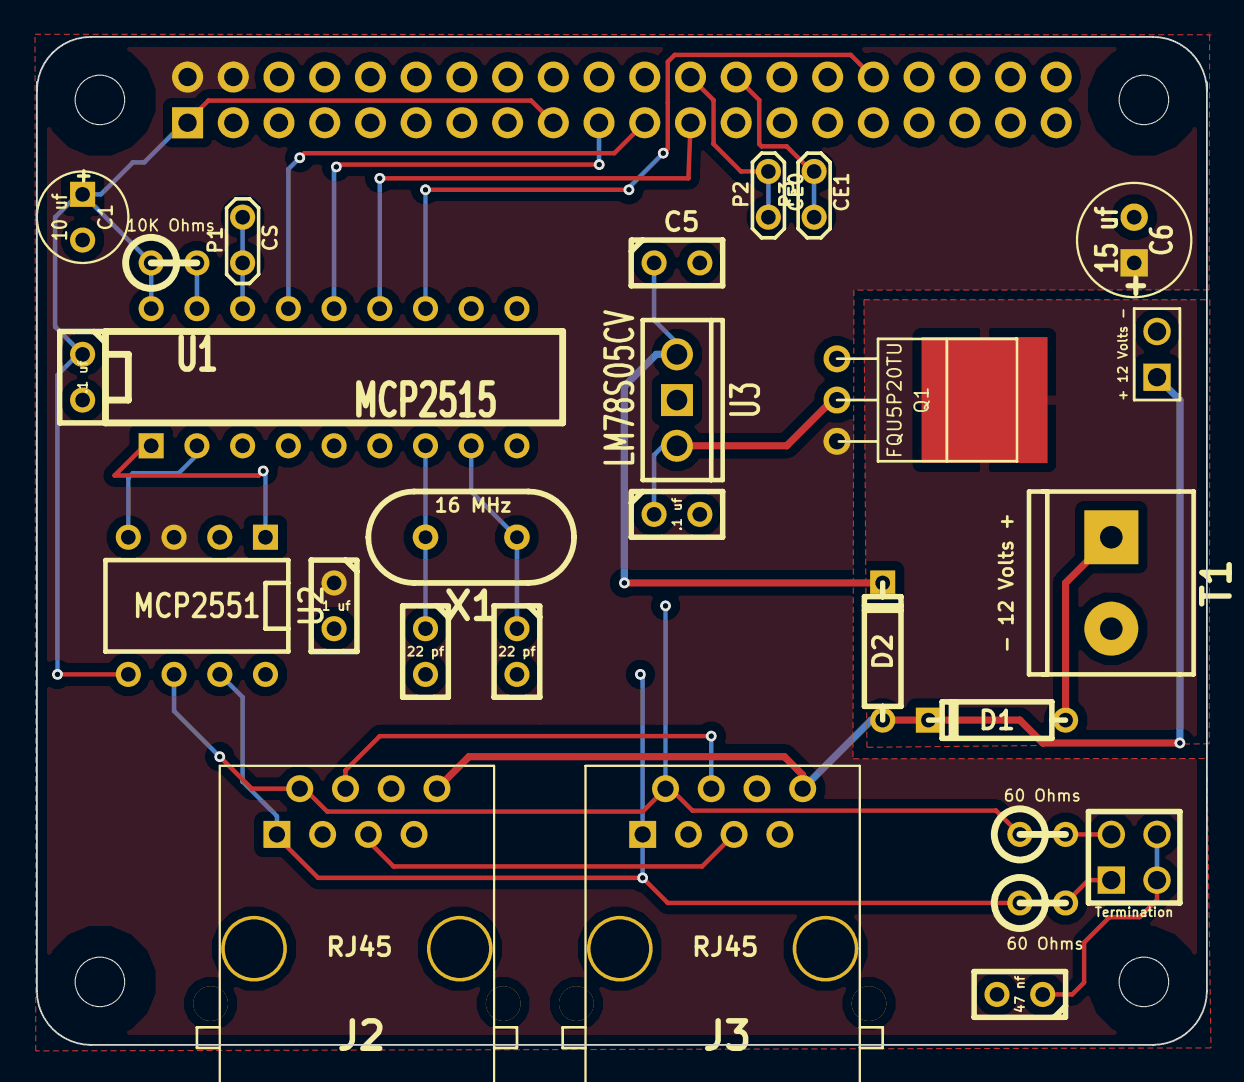
[picture p151: board CANHat3.kicad_pcb from above]

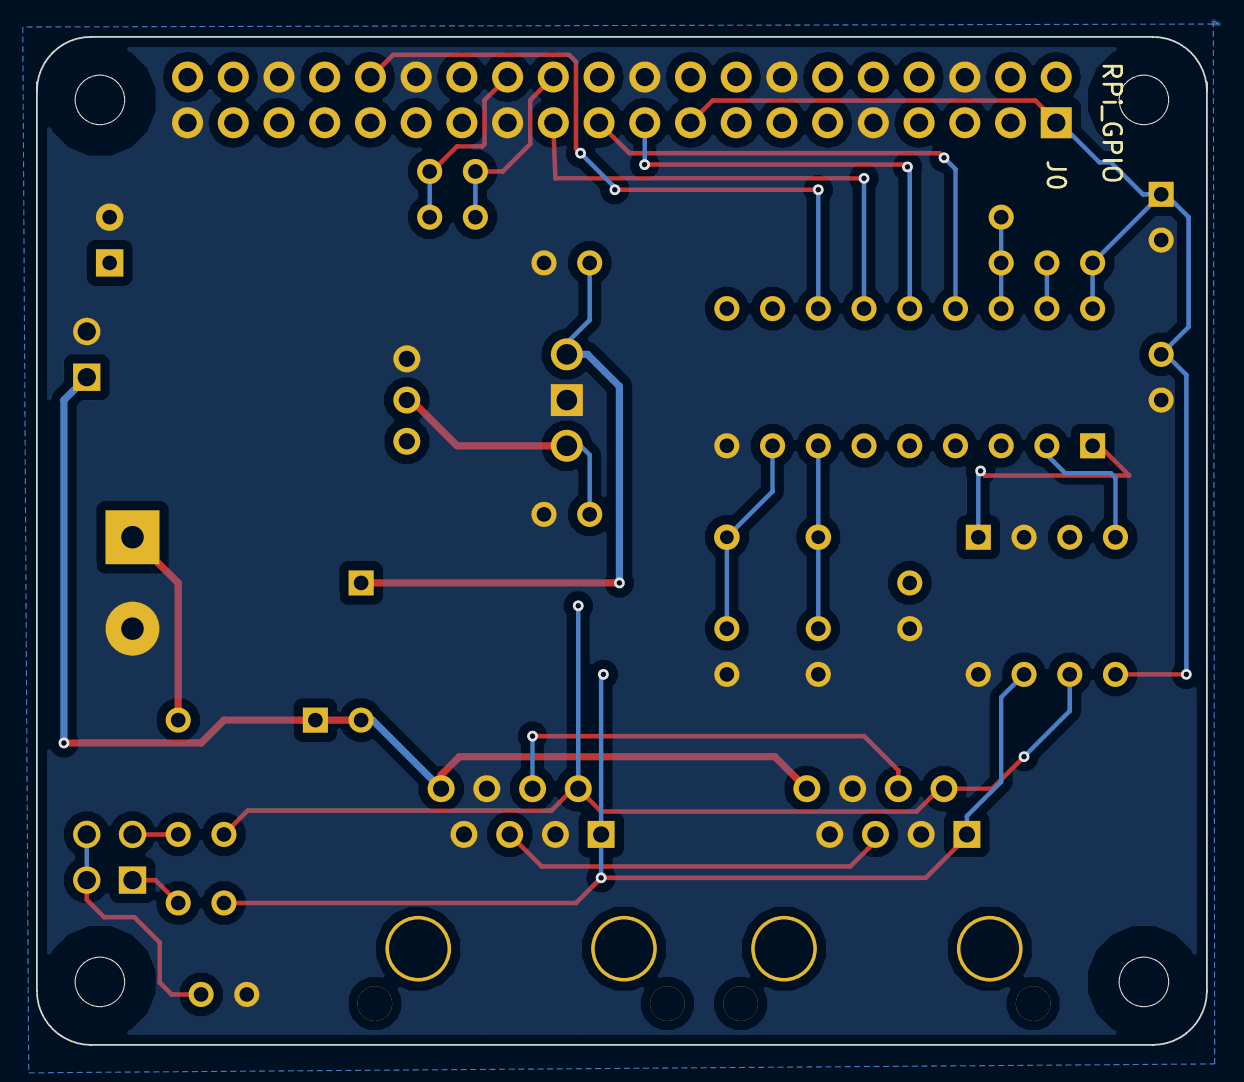
[picture p152: board CANHat3.kicad_pcb from below]

Board: 2 copper layers, 65.0 x 56.0 mm, 32 parts (5 on the bottom side), 26 nets.

Parts:
C1: 10 uf; C1V5
C2, C4: 22 pf; C1
C3, C7, C8: .1 uf; C1
C5: 0.33 uf; C1
C6: 15 uf; C1V7
C9: 47 nf; C1
D1, D2: SB240-E3/54; D3
H1, H2, H3, H4: RPi_Hat_Mounting_Hole
J0: RPi_GPIO; Pin_Header_Straight_2x20
J1: Termination; PIN_ARRAY_2X2
J2, J3: RJ45; RJ45_8N-S
P1: CS; TESTPOINT
P2: CE0; TESTPOINT
P3: CE1; TESTPOINT
P4: + 12 Volts -; ScrewTerm2.54-2
Q1: FQU5P20TU; TO-251-3
R1: 10K Ohms; R1
R2, R3: 60 Ohms; R1
T1: - 12 Volts +; mors_2p
U1: MCP2515; DIP-18__300
U2: MCP2551; DIP-8__300
U3: LM78S05CV; LM78XXV
X1: 16 MHz; HC-49V

Connections:
+3.3V: C1.1, C3.1, J0.1, J0.17, R1.1, U1.18, U2.5
+5V: C6.1, C8.1, J0.2, J0.4, Q1.S, U2.3
+12V: D1.2, D2.1, J2.8, J3.8, P4.1
CS: P1.1, U1.16
GND: C1.2, C2.2, C3.2, C4.2, C5.2, C6.2, C7.2, C8.2, C9.2, J0.6, J0.9, J0.14, J0.20, J0.25, J0.30, J0.36, J0.39, J2.3, J2.6, J2.7, J3.3, J3.6, J3.7, P4.2, Q1.G, T1.2, U1.9, U2.2, U2.8, U3.GND
INT: J0.32, U1.12
MISO: J0.21, U1.15
MOSI: J0.19, U1.14
unnamed: J1.1, R2.2
unnamed: J1.2, R3.2
unnamed: C9.1, J1.3, J1.4
unnamed: C5.1, D2.2, U3.VI
unnamed: D1.1, T1.1
unnamed: C7.1, Q1.D, U3.VO
unnamed: J0.26, P3.1
unnamed: J0.24, P2.1
unnamed: U1.1, U2.1
unnamed: R1.2, U1.17
unnamed: J2.4, J3.4
unnamed: J2.2, J3.2, R3.1, U2.6
unnamed: J2.5, J3.5
unnamed: U1.2, U2.4
unnamed: C4.1, U1.7, X1.2
unnamed: C2.1, U1.8, X1.1
unnamed: J2.1, J3.1, R2.1, U2.7
SCLK: J0.23, U1.13
