RobertPHeller/RPi-RRCircuits/YardBoss/BlankDaughterBoard/BlankDaughterBoard.sch

## KiCad design YardBoss/BlankDaughterBoard/BlankDaughterBoard.sch (2018-05-17)

Schematic: BlankDaughterBoard.sch

Parts:
J1: I2CIN
J2: I2COUT
