RobertPHeller/RPi-RRCircuits/YardBoss/ButtonDaughterBoard/ButtonDaughterBoard.sch

## KiCad design YardBoss/ButtonDaughterBoard/ButtonDaughterBoard.sch (2018-05-18)

Schematic: ButtonDaughterBoard.sch

Parts:
C1: CP1
C2, C3, C4, C5: .1 uf
C6, C7, C8, C9, C10, C11, C12, C13, C14, C15, C16, C17, C18, C19, C20, C21: 10 nf
J1: I2CIN
J2: I2COUT
P1: 2 1 0
P2: GND 00 01 02 03
P3: GND 17 16 15 14
P4: 13 12 11 10 GND
P5: 04 05 06 07 GND
R1, R2, R3, R4, R5, R6, R7, R8, R9, R10, R11, R12, R13, R14, R15, R16: 10K Ohms
RR1: 10K Ohms
U1: MCP23017
U2, U3, U4: 74HC14
