RobertPHeller/RPi-RRCircuits/YardBoss/LEDDaughterBoard/LEDDaughterBoard.sch

## KiCad design YardBoss/LEDDaughterBoard/LEDDaughterBoard.sch (2018-05-18)

Schematic: LEDDaughterBoard.sch

Parts:
C1: .1 uf
C2: 10 uf
C3: 15 uf
J1: I2CIN
J2: I2COUT
P1: 2 1 0
P2: L04 L05 L06 L07 C
P3: C L14 L15 L16 L17
P4: L00 L01 L02 L03 C
P5: C L13 L12 L11 L10
Q1, Q2, Q3, Q4: MPQ2222A; TO116
R1, R2, R3, R4, R9, R10, R11, R12, R17, R18, R19, R20, R25, R26, R27, R28: 1K Ohms
R5, R6, R7, R8, R13, R14, R15, R16, R21, R22, R23, R24, R29, R30, R31, R32: 150 Ohms
RR1: 10K Ohms
U1: MCP23017
