RobertPHeller/RPi-RRCircuits/LPC176x_SignalOnlyOpenMRN/targets/freertos.armv7m.nxp-lpcexpresso-lpc1769/startup.c

/** \copyright
 * Copyright (c) 2015, Stuart W Baker
 * All rights reserved.
 *
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
 * \file startup.c
 * This file sets up the runtime environment for NXP LPC175x and LPC176x MCUs.
 *
 * @author Stuart W. Baker
 * @date 16 April 2015
 */

#include <stdint.h>

#include "FreeRTOSConfig.h"

/* prototypes */
extern unsigned long *__stack;
extern void reset_handler(void);
static void nmi_handler(void);
static void hard_fault_handler(void);
static void mpu_fault_handler(void);
static void bus_fault_handler(void);
static void usage_fault_handler(void);

extern void SVC_Handler(void);
extern void debug_interrupt_handler(void);

extern void PendSV_Handler(void);
extern void SysTick_Handler(void);

extern void __libc_init_array(void);

extern int main(int argc, char *argv[]);

extern void watchdog_interrupt_handler(void);
extern void timer0_interrupt_handler(void);
extern void timer1_interrupt_handler(void);
extern void timer2_interrupt_handler(void);
extern void timer3_interrupt_handler(void);
extern void uart0_interrupt_handler(void);
extern void uart1_interrupt_handler(void);
extern void uart2_interrupt_handler(void);
extern void uart3_interrupt_handler(void);
extern void pwm1_interrupt_handler(void);
extern void i2c0_interrupt_handler(void);
extern void i2c1_interrupt_handler(void);
extern void i2c2_interrupt_handler(void);
extern void spi_interrupt_handler(void);
extern void ssp0_interrupt_handler(void);
extern void ssp1_interrupt_handler(void);
extern void pll0_interrupt_handler(void);
extern void rtc_interrupt_handler(void);
extern void external0_interrupt_handler(void);
extern void external1_interrupt_handler(void);
extern void external2_interrupt_handler(void);
extern void external3_interrupt_handler(void);
extern void adc_interrupt_handler(void);
extern void bod_interrupt_handler(void);
extern void usb_interrupt_handler(void);
extern void can_interrupt_handler(void);
extern void gpdma_interrupt_handler(void);
extern void i2s_interrupt_handler(void);
extern void ethernet_interrupt_handler(void);
extern void repetitive_interrupt_handler(void);
extern void mcpwm_interrupt_handler(void);
extern void qei_interrupt_handler(void);
extern void pll1_interrupt_handler(void);
extern void usb_activity_interrupt_handler(void);
extern void can_activity_interrupt_handler(void);
extern void ignore_fn(void);

extern const unsigned long cm3_cpu_clock_hz;
/** CPU clock speed. */
const unsigned long cm3_cpu_clock_hz = 96000000;

/** Exception table */
__attribute__ ((section(".interrupt_vector")))
void (* const __interrupt_vector[])(void) =
{
    (void (*)(void))(&__stack),      /**<   0 initial stack pointer */
    reset_handler,                   /**<   1 reset vector */
    nmi_handler,                     /**<   2 non-maskable interrupt */
    hard_fault_handler,              /**<   3 hard fault */
    mpu_fault_handler,               /**<   4 memory managment */
    bus_fault_handler,               /**<   5 bus Fault */
    usage_fault_handler,             /**<   6 usage fault */
    0,                               /**<   7 reserved */
    0,                               /**<   8 reserved */
    0,                               /**<   9 reserved */
    0,                               /**<  10 reserved */
    SVC_Handler,                     /**<  11 SV call */
    debug_interrupt_handler,         /**<  12 debug monitor */
    0,                               /**<  13 reserved */
    PendSV_Handler,                  /**<  14 pend SV */
    SysTick_Handler,                 /**<  15 system tick */
    watchdog_interrupt_handler,      /**<  16 watchdog timer*/
    timer0_interrupt_handler,        /**<  17 timer 0 */
    timer1_interrupt_handler,        /**<  18 timer 1 */
    timer2_interrupt_handler,        /**<  19 timer 2 */
    timer3_interrupt_handler,        /**<  20 timer 3 */
    uart0_interrupt_handler,         /**<  21 UART0 */
    uart1_interrupt_handler,         /**<  22 UART1 */
    uart2_interrupt_handler,         /**<  23 UART2 */
    uart3_interrupt_handler,         /**<  24 UART3 */
    pwm1_interrupt_handler,          /**<  25 PWM generator */
    i2c0_interrupt_handler,          /**<  26 I2C0 */
    i2c1_interrupt_handler,          /**<  27 I2C1 */
    i2c2_interrupt_handler,          /**<  28 I2C2 */
    spi_interrupt_handler,           /**<  29 SPI */
    ssp0_interrupt_handler,          /**<  30 SSP0 */
    ssp1_interrupt_handler,          /**<  31 SSP1 */
    pll0_interrupt_handler,          /**<  32 PLL0 (main PLL) */
    rtc_interrupt_handler,           /**<  33 real time clock */
    external0_interrupt_handler,     /**<  34 external interrupt 0 */
    external1_interrupt_handler,     /**<  35 external interrupt 1 */
    external2_interrupt_handler,     /**<  36 external interrupt 2 */
    external3_interrupt_handler,     /**<  37 external interrupt 3 */
    adc_interrupt_handler,           /**<  38 ADC */
    bod_interrupt_handler,           /**<  39 brown out detect */
    usb_interrupt_handler,           /**<  40 USB */
    can_interrupt_handler,           /**<  41 CAN */
    gpdma_interrupt_handler,         /**<  42 DMA channels 1 and 2 */
    i2s_interrupt_handler,           /**<  43 I2S */
    ethernet_interrupt_handler,      /**<  44 Ethernet */
    repetitive_interrupt_handler,    /**<  45 repetitive interrupt timer */
    mcpwm_interrupt_handler,         /**<  46 motion control PWM */
    qei_interrupt_handler,           /**<  47 quadrature encoder interface */
    pll1_interrupt_handler,          /**<  48 PLL1 (USB PLL) */
    usb_activity_interrupt_handler,  /**<  49 USB activity */
    can_activity_interrupt_handler,  /**<  50 CAN activity */
    ignore_fn                        /**< forces the linker to add this fn */
};

extern unsigned long __data_section_table;
extern unsigned long __data_section_table_end;
extern unsigned long __bss_section_table;
extern unsigned long __bss_section_table_end;

extern unsigned long _etext;
extern unsigned long _data;
extern unsigned long _edata;
extern unsigned long _bss;
extern unsigned long _ebss;

/** This hardware initialization code will be called before C++ global objects
 * are initialized. */
extern void hw_preinit(void);

/** Sets the hardware outputs to a safe state. Called when the program crashes
 * handler. */
/*void hw_set_to_safe(void) __attribute__ ((weak));
void hw_set_to_safe(void)
{
}*/
extern void hw_set_to_safe(void);


/** Startup the C/C++ runtime environment.
 */
void reset_handler(void)
{
    unsigned long *section_table_addr = &__data_section_table;

    /* copy ram load sections from flash to ram */
    while (section_table_addr < &__data_section_table_end)
    {
        unsigned long *src = (unsigned long *)*section_table_addr++;
        unsigned long *dst = (unsigned long *)*section_table_addr++;
        unsigned long  len = (unsigned long)  *section_table_addr++;

        for ( ; len; len -= 4)
        {
            *dst++ = *src++;
        }
    }

    /* zero initialize bss segment(s) */
    while (section_table_addr < &__bss_section_table_end)
    {
        unsigned long *zero = (unsigned long *)*section_table_addr++;
        unsigned long  len  = (unsigned long)  *section_table_addr++;
        
        for ( ; len; len -= 4)
        {
            *zero++ = 0;
        }
    }

    hw_preinit();

    /* call static constructors */
    __libc_init_array();

    /* execute main */
    char *argv[] = {0};
    main(0, argv);

    for ( ; /* forever */ ;)
    {
        /* if we ever return from main, loop forever */
    }
}

extern void resetblink(unsigned long pattern);
//extern void diewith(unsigned pattern);


    /* These are volatile to try and prevent the compiler/linker optimising them
    away as the variables never actually get used.  If the debugger won't show the
    values of the variables, make them global my moving their declaration outside
    of this function. */
/** Fault handling information */
typedef struct fault_information
{
    volatile unsigned long stacked_r0 ;
    volatile unsigned long stacked_r1 ;
    volatile unsigned long stacked_r2 ;
    volatile unsigned long stacked_r3 ;
    volatile unsigned long stacked_r12 ;
    volatile unsigned long stacked_lr ;
    volatile unsigned long stacked_pc ;
    volatile unsigned long stacked_psr ;
    volatile unsigned long _CFSR ;
    volatile unsigned long _HFSR ;
    volatile unsigned long _DFSR ;
    volatile unsigned long _AFSR ;
    volatile unsigned long _BFAR ;
    volatile unsigned long _MMAR ;
} FaultInformation;

/** Global instance so that it can be added to the watch expressions */
volatile FaultInformation faultInfo;

/** Decode the stack state prior to an exception occuring.  This code is
 * inspired by FreeRTOS.
 * @param address address of the stack
 */
__attribute__((optimize("-O0"))) void hard_fault_handler_c( unsigned long *hardfault_args )
{
    /* force a reference in the local variables for debug */
    volatile FaultInformation *fault_info = &faultInfo;

    fault_info->stacked_r0 = ((unsigned long)hardfault_args[0]) ;
    fault_info->stacked_r1 = ((unsigned long)hardfault_args[1]) ;
    fault_info->stacked_r2 = ((unsigned long)hardfault_args[2]) ;
    fault_info->stacked_r3 = ((unsigned long)hardfault_args[3]) ;
    fault_info->stacked_r12 = ((unsigned long)hardfault_args[4]) ;
    fault_info->stacked_lr = ((unsigned long)hardfault_args[5]) ;
    fault_info->stacked_pc = ((unsigned long)hardfault_args[6]) ;
    fault_info->stacked_psr = ((unsigned long)hardfault_args[7]) ;

    // Configurable Fault Status Register
    // Consists of MMSR, BFSR and UFSR
    fault_info->_CFSR = (*((volatile unsigned long *)(0xE000ED28))) ;   
                                                                                    
    // Hard Fault Status Register
    fault_info->_HFSR = (*((volatile unsigned long *)(0xE000ED2C))) ;

    // Debug Fault Status Register
    fault_info->_DFSR = (*((volatile unsigned long *)(0xE000ED30))) ;

    // Auxiliary Fault Status Register
    fault_info->_AFSR = (*((volatile unsigned long *)(0xE000ED3C))) ;

    // Read the Fault Address Registers. These may not contain valid values.
    // Check BFARVALID/MMARVALID to see if they are valid values
    // MemManage Fault Address Register
    fault_info->_MMAR = (*((volatile unsigned long *)(0xE000ED34))) ;
    // Bus Fault Address Register
    fault_info->_BFAR = (*((volatile unsigned long *)(0xE000ED38))) ;

    //__asm("BKPT #0\n") ; // Break into the debugger

    /* When the following line is hit, the variables contain the register values. */
    if (fault_info->stacked_r0  || fault_info->stacked_r1  ||
        fault_info->stacked_r2  || fault_info->stacked_r3  ||
        fault_info->stacked_r12 || fault_info->stacked_lr  ||
        fault_info->stacked_pc  || fault_info->stacked_psr ||
        fault_info->_CFSR       || fault_info->_HFSR       ||
        fault_info->_DFSR       || fault_info->_AFSR       ||
        fault_info->_MMAR       || fault_info->_BFAR)
    {
        resetblink(BLINK_DIE_HARDFAULT);
        for( ;; );
    }
}

/** The fault handler implementation.  This code is inspired by FreeRTOS.
 */
__attribute__((__naked__)) static void hard_fault_handler(void)
{
    __asm volatile
    (
        " tst   lr, #4               \n"
        " ite   eq                   \n"
        " mrseq r0, msp              \n"
        " mrsne r0, psp              \n"
        " b     hard_fault_handler_c \n"
        " bx    lr                   \n"
    );
}

static void nmi_handler(void)
{
    for ( ; /* forever */ ; )
    {
    }
}

static void mpu_fault_handler(void)
{
    for ( ; /* forever */ ; )
    {
    }
}

static void bus_fault_handler(void)
{
    for ( ; /* forever */ ; )
    {
    }
}

static void usage_fault_handler(void)
{
    for ( ; /* forever */ ; )
    {
    }
}

/** This is the default handler for exceptions not defined by the application.
 */
void default_interrupt_handler(void) __attribute__ ((weak));
void default_interrupt_handler(void)
{
    while(1);
    diewith(BLINK_DIE_UNEXPIRQ);
}

void debug_interrupt_handler(void) __attribute__ ((weak, alias ("default_interrupt_handler")));
void watchdog_interrupt_handler(void) __attribute__ ((weak, alias ("default_interrupt_handler")));
void timer0_interrupt_handler(void) __attribute__ ((weak, alias ("default_interrupt_handler")));
void timer1_interrupt_handler(void) __attribute__ ((weak, alias ("default_interrupt_handler")));
void timer2_interrupt_handler(void) __attribute__ ((weak, alias ("default_interrupt_handler")));
void timer3_interrupt_handler(void) __attribute__ ((weak, alias ("default_interrupt_handler")));
void uart0_interrupt_handler(void) __attribute__ ((weak, alias ("default_interrupt_handler")));
void uart1_interrupt_handler(void) __attribute__ ((weak, alias ("default_interrupt_handler")));
void uart2_interrupt_handler(void) __attribute__ ((weak, alias ("default_interrupt_handler")));
void uart3_interrupt_handler(void) __attribute__ ((weak, alias ("default_interrupt_handler")));
void pwm1_interrupt_handler(void) __attribute__ ((weak, alias ("default_interrupt_handler")));
void i2c0_interrupt_handler(void) __attribute__ ((weak, alias ("default_interrupt_handler")));
void i2c1_interrupt_handler(void) __attribute__ ((weak, alias ("default_interrupt_handler")));
void i2c2_interrupt_handler(void) __attribute__ ((weak, alias ("default_interrupt_handler")));
void spi_interrupt_handler(void) __attribute__ ((weak, alias ("default_interrupt_handler")));
void ssp0_interrupt_handler(void) __attribute__ ((weak, alias ("default_interrupt_handler")));
void ssp1_interrupt_handler(void) __attribute__ ((weak, alias ("default_interrupt_handler")));
void pll0_interrupt_handler(void) __attribute__ ((weak, alias ("default_interrupt_handler")));
void rtc_interrupt_handler(void) __attribute__ ((weak, alias ("default_interrupt_handler")));
void external0_interrupt_handler(void) __attribute__ ((weak, alias ("default_interrupt_handler")));
void external1_interrupt_handler(void) __attribute__ ((weak, alias ("default_interrupt_handler")));
void external2_interrupt_handler(void) __attribute__ ((weak, alias ("default_interrupt_handler")));
void external3_interrupt_handler(void) __attribute__ ((weak, alias ("default_interrupt_handler")));
void adc_interrupt_handler(void) __attribute__ ((weak, alias ("default_interrupt_handler")));
void bod_interrupt_handler(void) __attribute__ ((weak, alias ("default_interrupt_handler")));
void usb_interrupt_handler(void) __attribute__ ((weak, alias ("default_interrupt_handler")));
void can_interrupt_handler(void) __attribute__ ((weak, alias ("default_interrupt_handler")));
void gpdma_interrupt_handler(void) __attribute__ ((weak, alias ("default_interrupt_handler")));
void i2s_interrupt_handler(void) __attribute__ ((weak, alias ("default_interrupt_handler")));
void ethernet_interrupt_handler(void) __attribute__ ((weak, alias ("default_interrupt_handler")));
void repetitive_interrupt_handler(void) __attribute__ ((weak, alias ("default_interrupt_handler")));
void mcpwm_interrupt_handler(void) __attribute__ ((weak, alias ("default_interrupt_handler")));
void qei_interrupt_handler(void) __attribute__ ((weak, alias ("default_interrupt_handler")));
void pll1_interrupt_handler(void) __attribute__ ((weak, alias ("default_interrupt_handler")));
void usb_activity_interrupt_handler(void) __attribute__ ((weak, alias ("default_interrupt_handler")));
void can_activity_interrupt_handler(void) __attribute__ ((weak, alias ("default_interrupt_handler")));
